guiraudjb/Arducible_Fanny_Petanque_World_Tour/videos/poster-chassis-as-du-tir.jpg

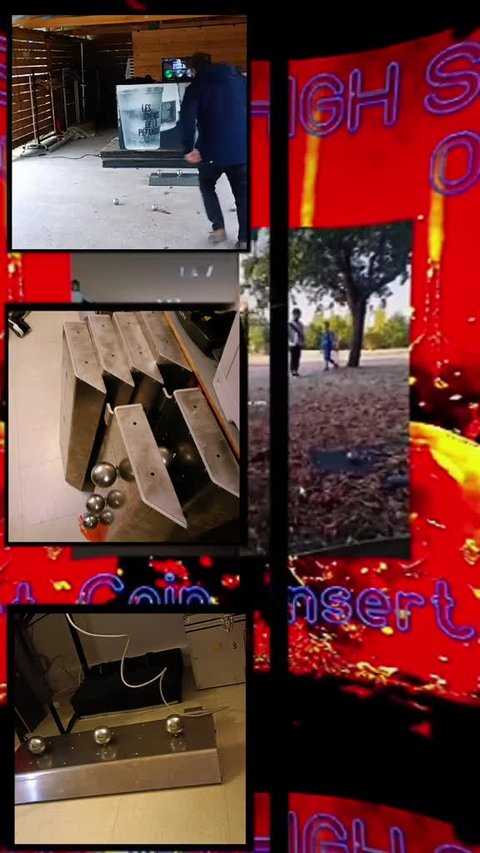
videos/poster-chassis-as-du-tir.jpg
