guiraudjb/Arducible_Fanny_Petanque_World_Tour/videos/poster-assemblage-articulation.jpg

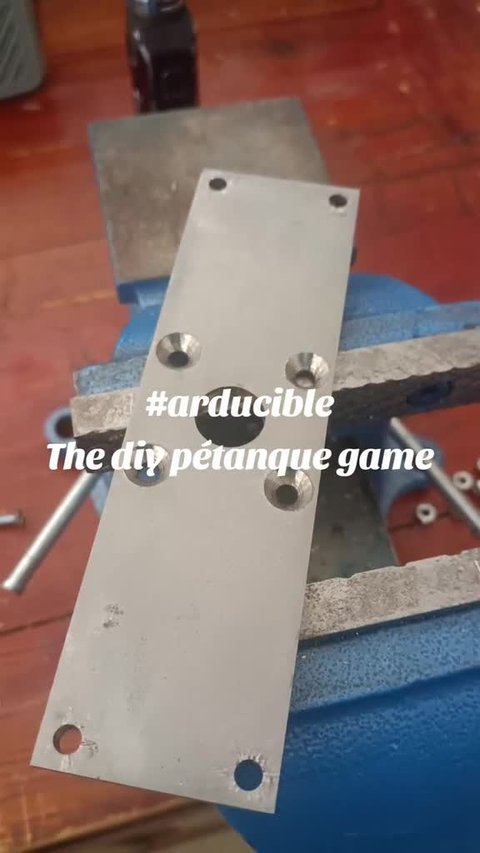
videos/poster-assemblage-articulation.jpg
