guiraudjb/Arducible_Fanny_Petanque_World_Tour/ressources/utils/RECHERCHE_ATHLETES_PETANQUE.md

# Recherche : athlètes, titres et classements de pétanque par pays

Registre des recherches web menées pour documenter, pour chacun des 112 pays du tour (`Scripts/dialogues.py`), les athlètes de pétanque notables, les titres nationaux/internationaux et le niveau compétitif du pays — en complément de `RECHERCHE_PETANQUE_PAYS.md` (dates de fondation des fédérations) et en vue d'enrichir les questions de `Scripts/quiz_questions.py`.

Principe : chaque fait doit être vérifiable et sourcé. Quand aucune information fiable n'a été trouvée après recherche web, c'est noté explicitement (`AUCUNE INFORMATION TROUVÉE`) plutôt que d'inventer un fait.

**112 pays traités par recherche web.**

## Europe

**Allemagne** (tier 0) — Pas de champion individuel historique majeur trouvé, mais nation en forte progression : a organisé le premier championnat d'Europe triplette féminin à Rastatt (2003) ; a décroché son tout premier titre de championne d'Europe triplette masculine en 2025 à Santa Susanna (Espagne), battant la France 13-7 en finale ; nombreuses médailles CEP (bronzes/argents EuroCup, ors en Espoirs triplette femmes 2009/2011/2017/2025) — sources : cep-petanque.com/medals.html ; sportmag.fr/petanque-enorme-desillusion-la-france-privee-de-la-couronne-par-lallemagne

**Andorre** (tier 1) — Federació Andorrana de Petanca (présidée par Patrick Senzier), organise championnats nationaux et ateliers jeunesse. Aucun athlète ni résultat international trouvé — sources : andorrapetanca.com ; coa.ad/federacio/federacio-andorrana-petanca

**Angleterre** (tier 2) — Petanque England ; fédération forte reconnue par la CEP ; bronze en FedCup 2023, argent Doubles Femmes 2022, bronze Doubles Hommes 2022, argent Junior Triples Filles 2022, or Précision Espoirs Femmes 2017 ; a longtemps dominé le "Home Nations Championship" jusqu'à une série de 24 ans rompue par Jersey en 2025 — sources : cep-petanque.com/medals.html ; channeleye.media/team-jersey-triumphs-in-historic-victory-at-petanque-home-nations-championships

**Autriche** (tier 4) — Fédération autrichienne (boule.at) ; bronze en triplette femmes au championnat d'Europe 2016 et bronze en tir de précision femmes 2024 ; jeune joueur Maris Newerkla (PSV Freistadt) noté 5e aux championnats d'Europe juniors — sources : cep-petanque.com/medals.html ; boule.at/ranglisten

**Belgique** (tier 5) — Claudy Weibel : 2 titres de champion du monde (triplette 2000, tête-à-tête 2015 à Nice), champion d'Europe de tir de précision 2009, 19 médailles mondiales seniors ; William Van der Biest, 2 fois champion du monde junior ; la Belgique a aussi remporté l'or en EuroCup en 2016 et 2018 — sources : fr.wikipedia.org/wiki/Charles_Weibel ; sportmag.fr/petanque-la-legende-claudy-weibel-dit-stop-avec-la-belgique ; cep-petanque.com/medals.html

**Bulgarie** (tier 6) — Fédération bulgare de pétanque (petanque-bulgaria.com) ; a organisé le championnat d'Europe hommes 2015 et 2019 à Albena. Aucun athlète bulgare médaillé trouvé — sources : petanque-bulgaria.com ; cep-petanque.com/medals.html

**Danemark** (tier 7) — Fédération existant depuis plus de 50 ans ; Lasse Dithmar a réalisé le meilleur score de tir de précision jamais atteint par un Danois (36) en grand championnat ; médailles CEP officielles : Or en FedCup 2024 ET 2025, argent EuroCup 1998, plusieurs bronzes (triplette femmes 2012/2014, junior mixte 2000/2004, tir 2006/2013) — sources : sportmag.fr/petanque-le-danemark-grandit-a-linternational ; cep-petanque.com/medals.html

**Écosse** (tier 8) — Scottish Pétanque Association fondée en 1985 ; dispute le "Celtic Challenge" contre le Pays de Galles et l'Irlande (13 victoires en 2026, derrière le Pays de Galles à 14). Aucune médaille CEP/FIPJP trouvée à ce jour — sources : scottishpetanque.org ; welshpetanque.org.uk/?page_id=77

**Espagne** (tier 9) — Sara Díaz Reyes, championne d'Europe espagnole citée comme référence ; l'Espagne a battu la Suisse 13-7 en finale de doublette et l'Italie 13-9 en doublette messieurs lors de récents championnats d'Europe ; médailles CEP très nombreuses (or triplette féminine 1971, multiples ors en tir de précision) — sources : boule-petanque.fr/vibrer-petanque/direct-live-des-championnats-deurope-de-petanque-en-espagne-cette-semaine ; cep-petanque.com/medals.html

**Estonie** (tier 10) — En demi-finale du championnat d'Europe vétérans 2023, l'Estonie s'est inclinée 33-23 face à l'Italie ; médailles CEP officielles en FedCup : argent 2023, bronze 2022 ; bronzes en tir de précision 2011 et 2013 — sources : blogpetanque.com/guerchois/RESULTATS-CHAMPIONNAT-D-EUROPE_a987 ; cep-petanque.com/medals.html

**Finlande** (tier 11) — Suomen Pétanque-Liitto ; meilleurs résultats historiques : plusieurs 5e places en Euro, ~9e en Mondial ; argent FedCup 2024, bronzes FedCup 2018/2019/2021, or en Espoirs triplette hommes 2019 ; joueurs représentant la Finlande au Mondial de Dijon (déc. 2024) : Mikko Soikkeli, Petri Seppä, Antti Lehtonen, Mikael Daniloff-Bredenholm — sources : petanquefinland.com ; cep-petanque.com/medals.html

**France** (tier 12) — Philippe Quintais, "le Roi Quintais"/"Zidane de la pétanque", 14 fois champion du monde (8x triplette, 4x tir de précision, 2x en tant que coach), 2 titres de champion d'Europe ; Dylan Rocher, actuel meilleur joueur mondial (9 fois champion du monde, 7 fois champion d'Europe) ; la France domine tous les tableaux avec 27+ titres mondiaux et plus de 80 podiums — sources : en.wikipedia.org/wiki/Philippe_Quintais ; famille-rocher.com/qui-sommesnous-dylan-rocher ; fr.wikipedia.org/wiki/Championnats_du_monde_de_pétanque

**Guernesey** (tier 13) — Guernsey Club de Pétanque ; au tournoi international "Guernsey Open" 2025, Andrew Bellamy-Burt vainqueur en simple, victoires en doublette et triplette avec des joueurs jersiais/guernesiais mêlés (tournoi ouvert, pas de médaille FIPJP/CEP) — source : guernseypetanque.co.uk/guernsey-open

**Hongrie** (tier 14) — Ágnes Kocsis-Simon, présidente de la Fédération hongroise de pétanque, joueuse et entraîneuse : 11 titres nationaux, 11e place par équipe au championnat du monde en ayant battu la future championne (Tunisie), a mené l'équipe féminine jeunes de Hongrie au bronze au championnat d'Europe U- 2019 ; argent en tir de précision juniors filles au championnat d'Europe 2022 — sources : petanque.hu/kocsissimonagnes-interju2020 ; sportmag.fr/petanque-la-hongrie-se-fait-sa-place-dans-le-gratin-europeen ; cep-petanque.com/medals.html

**Irlande** (tier 15) — Irish Pétanque Association fondée en 1990 ; a remporté le "Celtic Challenge" quatre années consécutives, bronze en Coupe Fédération Europe ; équipe Ireland A1 (Colin Delaney, Sariff Antooaroo, Stephane Voinot, Kevin Meniel) invaincue en 2023 — sources : irishpetanque.org ; educnaute-infos.com/article-la-petanque-en-irlande-119320671

**Italie** (tier 16) — Diego Rizzi, surnommé "l'Alieno" (l'extraterrestre) : 46 fois champion d'Italie, 6 fois champion d'Europe, 5 fois champion du monde, 2 fois champion de France ; l'Italie championne du monde triplette 2024 (Rizzi/Cocciolo) battant Madagascar 13-11, premier titre italien en 45 ans dans cette épreuve ; or mondial en doublette 2022, argent en tête-à-tête 2022 — sources : fr.wikipedia.org/wiki/Diego_Rizzi ; sportmag.fr/petanque-litalie-sur-le-toit-du-monde

**Jersey** (tier 17) — L'équipe de Jersey a mis fin en 2025 à une série de 24 années de victoires consécutives de l'Angleterre au "Petanque Home Nations Championship" ; 4 joueurs de Jersey ont participé au championnat d'Europe 2026 à Lorca (Espagne) ; Cassie Stewart-Le Gallais a remporté les Island Singles Championships 2025 (catégorie femmes) — sources : channeleye.media/team-jersey-triumphs-in-historic-victory-at-petanque-home-nations-championships ; jerseysportscouncil.com/jersey-petanque-players-in-confederation-of-european-petanque-championships

**Lettonie** (tier 18) — Latvijas petanka sporta federācija (fédération active, championnats nationaux doublette hommes/femmes). Aucun résultat international individuel ou d'équipe médaillé trouvé — source : petanque.lv

**Lituanie** (tier 19) — Lietuvos petankės asociacija ; champions nationaux : Irma Bagdanavičienė (simple femmes), Nerijus Kukcinavičius (simple hommes), Doringa Burneikienė & Almantas Burneika (mixte) ; a participé au championnat d'Europe 2024 à 's-Hertogenbosch (Pays-Bas) où la Lituanie a décroché le bronze en doublette femmes — sources : lietuvospetanke.lt/petankes-rezultatai ; cep-petanque.com/medals.html

**Luxembourg** (tier 20) — Fédération Luxembourgeoise de Boules et de Pétanque (65 ans d'existence) ; joueurs notables : Luc Cattazzo, Claudio Contardi, Sven Thill, Adrien Daunois ; plusieurs médailles CEP (bronzes EuroCup 2015/2019/2024, bronze doublette femmes 2024, argent junior mixte 2014) — sources : flbp.lu ; boulistenaute.com/les-actualites-de-la-petanque-et-du-monde-bouliste ; cep-petanque.com/medals.html

**Monaco** (tier 21) — Myriam Chambeiron et Laura Vierjon, championnes d'Europe de doublette féminine 2022 (à 's-Hertogenbosch, Pays-Bas), battant en finale la France, l'Allemagne, le Danemark, la Lituanie et l'Angleterre ; puissance récurrente du tir de précision avec de très nombreuses médailles CEP (or EuroCup 2011, ors en Espoirs, Vétérans, junior mixte 2018) — sources : monaco-tribune.com/2022/07/petanque-monaco-decroche-le-titre-de-champion-deurope-chez-les-feminines ; cep-petanque.com/medals.html

**Norvège** (tier 22) — Qualifiée pour la première fois au championnat du monde en 2013 ; meilleur résultat mondial junior : 9e place en 1995 ; or en FedCup 2022, bronzes FedCup 2023/2018 ; bronze en tir de précision femmes 2014 — sources : cd29petanque.fr/europe/petanque-en-norvege ; cep-petanque.com/medals.html

**Pays-Bas** (tier 23) — Kees Koogje et Edward Vinke, champions nationaux néerlandais, Vinke ayant représenté les Pays-Bas à plusieurs championnats d'Europe ; l'équipe néerlandaise a battu en poule les champions du monde en titre Dylan Rocher/Christophe Sarrio lors d'un tournoi à Rome ; nombreuses médailles CEP (or en tir de précision femmes 2007, ors en Vétérans 2016/2017, bronze en simple femmes 2022/2024) — sources : pen.nl/artikel/speler-petanque-vereniging-nieuwegein-nederland-kampioen-doubletten ; cep-petanque.com/medals.html

**Pays de Galles** (tier 24) — Welsh Pétanque Association fondée en 2004 ; pays le plus titré du "Celtic Challenge" avec 14 victoires (devant l'Écosse à 13 et l'Irlande à 8) ; champions nationaux récents : J-Y Robic, L Field, I Bailey — sources : welshpetanque.org.uk ; en.wikipedia.org/wiki/Welsh_Pétanque_Association

**Pologne** (tier 25) — Fédération polonaise de pétanque créée en 2002 ; Jędrzej Śliż, bronze en tir de précision au championnat d'Europe juniors 2003 (Brno) ; Paweł Pieprzyk, or en tir de précision juniors 2012 (Gand, Belgique) ; Katarzyna Błasiak, plusieurs médailles internationales ; or en FedCup 2021 — sources : lepetitjournal.com/varsovie/karolina-fabis-petanque-polonaise-passion-gagne-terrain-364712 ; cep-petanque.com/medals.html

**Portugal** (tier 26) — Federação Portuguesa de Petanca créée en 1992, membre FIPJP ; bronze en tir de précision hommes au championnat d'Europe 2019, argent 2011 ; bronze en Espoirs triplette hommes 2024. Aucun athlète nommé individuellement trouvé — sources : fppetanca.pt/fpp ; fipjp.org/images/pdf/nations/portugal.pdf ; cep-petanque.com/medals.html

**Roumanie** (tier 27) — Fédération roumaine de pétanque fondée en 2006 par Titus Marin ; Association Petanque Romania (APR) créée à Bucarest avec le soutien de la diaspora ; sport encore en développement, sans résultat international médaillé trouvé — sources : adevarul.ro/stil-de-viata/petanque-jocul-cu-bila-pe-gustul-lui-victor-1299315 ; romanialibera.ro/special/un-sport-nou-a-patruns-in-romania-petanque-66045

**Russie** (tier 28) — Fédération russe de pétanque (organise un championnat ouvert à Moscou) ; bronze en Vétérans au championnat d'Europe 2016 à Monaco — source : cep-petanque.com/medals.html

**Saint-Marin** (tier 29) — La Fédération sammarinaise de boules organise un tournoi international annuel de pétanque (24e édition mentionnée), avec inauguration de terrains couverts. AUCUNE INFORMATION TROUVÉE sur un athlète sammarinais médaillé au niveau international — sources : sanmarinortv.sm/sport/sport-sammarinese-c16/bocce-marro-e-musso-vincono-il-240-trofeo-internazionale-di-petanque-di-san-marino ; libertas.sm

**Serbie** (tier 30) — AUCUNE INFORMATION TROUVÉE de source fiable sur une fédération, un athlète ou un résultat international serbe en pétanque

**Slovaquie** (tier 31) — Slovak Petanque Federation ; participe au circuit "Petanque Tour Central Europe" (Trophée L. Sedivy) ; bronze en tir de précision hommes au championnat d'Europe 2015 à Albena. Aucun athlète nommé trouvé — source : cep-petanque.com/medals.html

**Slovénie** (tier 32) — La Slovénie a perdu 48-35 face à l'Italie en phase de championnat d'Europe, et 5-13 face à la France en 8e de finale du championnat du monde ; médailles CEP officielles : bronze FedCup 2025, argent FedCup 2022, bronze triplette hommes 2019, bronzes en tir de précision 2018/2023. Aucun athlète nommé trouvé — sources : blogpetanque.com/guerchois/RESULTATS-CHAMPIONNAT-D-EUROPE_a987 ; cep-petanque.com/medals.html

**Suède** (tier 33) — Ivar Liljegren, vice-champion d'Europe de tête-à-tête 2024 (à Martigny, Suisse), ayant battu Henri Lacroix en poule puis en demi-finale ; une joueuse suédoise a été sacrée championne d'Europe de tête-à-tête féminin 2026 à Lorca, battant Aurélie Bories 13-9 en finale (nom non confirmé) ; or à l'EuroCup 1998, or en triplette femmes 2007 — sources : sportmag.fr/petanque-un-redoutable-tireur-suedois-debarque-en-france ; sportmag.fr/petanque-bonetto-champion-deurope-desillusion-pour-bories-et-le-mixte ; cep-petanque.com/medals.html

**Suisse** (tier 34) — Maïky Molinas (Genève), champion du monde de tête-à-tête 2019, battant Henri Lacroix 13-12 ; Sylviane Métairon, championne du monde féminine l'année suivante ; la Suisse a remporté le championnat d'Europe junior triplette en 2022 ; considérée comme une grande nation de pétanque malgré seulement ~2 500 licenciés (contre 300 000 en France) ; or en EuroCup 1999, or en Vétérans 2025 — sources : letemps.ch/sport/petanque-maiki-molinas-las-carreau ; rts.ch/sport/autres-sports/14181090-loin-des-cliches-la-suisse-fait-partie-des-meilleures-nations-au-monde-en-petanque ; cep-petanque.com/medals.html

**Tchéquie** (tier 35) — Česká asociace pétanque klubů (~52 clubs, ~1000 licenciés en 2010) ; plus grand succès tchèque : médaille d'argent de l'équipe féminine au championnat d'Europe 2007 (Ankara/Turquie) ; argent en FedCup 2021 ; bronze en tir de précision juniors filles 2022 — source : cep-petanque.com/medals.html

**Ukraine** (tier 37) — Fédération ukrainienne de pétanque, enregistrée en 2007 puis reconfirmée en 2015 ; champions nationaux récents : Andriy Kameniev (Kharkiv) et Hanna Bezrodna (Kharkiv) ; a participé au tournoi préliminaire du championnat du monde 2024 à Dijon. Aucun résultat médaillé au niveau international (CEP/FIPJP) trouvé — sources : petanque.org.ua ; fr.wikipedia.org/wiki/Championnats_du_monde_de_pétanque_2024

Note méthodologique : les données les plus fiables proviennent de la page officielle des médailles de la Confédération Européenne de Pétanque (cep-petanque.com/medals.html), consultée directement, ce qui a permis de confirmer précisément année/catégorie/rang pour de nombreux petits pays (Danemark, Norvège, Pologne, Estonie, Lituanie, Tchéquie, Slovénie, Slovaquie, Hongrie, Autriche, Portugal, Russie, etc.). Pour Serbie, Roumanie, Andorre, Saint-Marin et Bulgarie, aucune médaille officielle ni athlète notable n'a pu être confirmé malgré plusieurs recherches ciblées.

## Asie

**Arménie** (tier 3) — AUCUNE INFORMATION TROUVÉE sur un athlète notable ou un résultat international. Un club de pétanque existe à Erevan (présenté comme "le premier club de pétanque en Arménie"), mais aucune fédération, aucun palmarès ni aucun résultat de compétition n'a pu être trouvé — source : https://www.instagram.com/petanqueclub_armenia/?hl=fr ; https://www.facebook.com/PetanqueArmenia/

**Turquie** (tier 36) — Aucun athlète notable identifié, mais le pays a un rôle d'hôte international réel : la fédération turque (Turkish Federation of Bocce, Bowling and Dart, affiliée FIPJP) a organisé les Championnats du Monde féminins en 2008, puis le 45ème Championnat du Monde de pétanque en triplette masculine à Izmir en 2015 (limité à 48 équipes qualifiées par continents), avec en parallèle le Championnat du Monde de tir de précision — source : https://petanque-en-comminges.over-blog.com/pages/45eme_Championnat_du_Monde_Triplettes_a_Izmir_Turquie-3811890.html

**Afghanistan** (tier 65) — AUCUNE INFORMATION TROUVÉE. Aucune fédération, aucun club, aucun athlète de pétanque afghan n'a pu être trouvé malgré plusieurs recherches.

**Bangladesh** (tier 66) — AUCUNE INFORMATION TROUVÉE. Aucune fédération ni club de pétanque n'a pu être identifié au Bangladesh.

**Brunei** (tier 67) — A participé au 6ème Championnat d'Asie de pétanque 2025 (Kuala Lumpur) en triplette homme/femme et tir, sans obtenir de médaille. Aucune médaille de pétanque relevée aux SEA Games 2025 (le premier "gold" historique de Brunei à ces Jeux était en wushu, pas en pétanque) — source : http://www.asianboulessport.org/News/FullOfficialResult_ASC2025.pdf ; https://www.seagames2025.org/news/details/Brunei-Secures-First-Gold-Med:-736

**Cambodge** (tier 68) — Sok Chanmean, champion du monde de tir de précision en 2016 (Madagascar), 2e place aux Championnats du Monde 2004 (France), 39 médailles cumulées sur 29 compétitions internationales depuis 2001 (12 titres). Au Championnat d'Asie 2025 (Kuala Lumpur) : OR en triplette féminine (Un Sreya, Ouk Sreymom, Heang Vichny, Pov Thyda), ARGENT en triplette masculine (Thong Chhoeun, Sychan Dara, Heng Than, Puth Yon Chandra), OR en tir juniors (Nun Ravin). Puissance montante confirmée de la pétanque en Asie du Sud-Est — source : https://www.cambodgemag.com/post/le-cambodgien-aux-39-m%C3%A9dailles-sok-chanmean-a-de-grandes-ambitions-pour-les-championnats-du-monde ; PDF résultats officiels ASC2025 (asianboulessport.org)

**Chine** (tier 69) — Au Championnat d'Asie 2025, la Chine (équipe Zhou Bao, Chuan Huai, Dao Shan, Cheng Ze) a remporté le BRONZE en triplette masculine (Nation Cup). Par ailleurs Wang Chenyi (Chine) a atteint la demi-finale de la discipline "Lyonnaise féminine" (boules lyonnaises, discipline distincte de la pétanque) aux World Games 2025 à Chengdu — à noter que ce dernier résultat concerne une discipline sœur et non la pétanque elle-même — source : PDF résultats officiels ASC2025 ; https://cnosf.franceolympique.com/jeux-mondiaux-2025-j11-du-bronze-pour-finir

**Corée du Sud** (tier 70) — Présence confirmée mais modeste (club "Hongchungang", moins de 25 joueurs). A participé au Championnat d'Asie 2025 sans obtenir de médaille (classée en fin de tableau en triplette hommes/femmes et junior) — source : PDF résultats officiels ASC2025 (asianboulessport.org)

**Inde** (tier 71) — La Petanque India Association (PIA) est l'organe national reconnu ; la pétanque serait arrivée en Inde en 2005. L'Inde a participé au Championnat d'Asie 2025 à Kuala Lumpur mais classée dernière (16e) en triplette masculine, sans médaille — source : https://www.instagram.com/indiapetanque/ ; PDF résultats officiels ASC2025

**Indonésie** (tier 72) — Anni Saputri, championne d'Asie 2025 en tir de précision féminin (Kuala Lumpur). Andri Irawan, médaille d'or en simple messieurs aux SEA Games 2025 (Thaïlande), battant le Laotien Southammavong Bountamy 13-7 en finale. Bronze en triplette masculine à l'Asian Cup 2025 (M Muhlis Harliza, Bagas Syarief Hidayat, Dhoni Wahyu Krisbiantoro, Topan Satria) — source : PDF résultats officiels ASC2025 ; https://en.wikipedia.org/wiki/P%C3%A9tanque_at_the_2025_SEA_Games

**Iran** (tier 73) — La Boules and Petanque Association of Iran (BPAI) est reconnue depuis 2009 comme organe national unique pour la pétanque, organisant des championnats nationaux (ex. 13e édition en février 2023 à Sari) pour sélectionner les équipes envoyées aux championnats d'Asie et du monde. Aucun résultat de médaille ni athlète notable identifié précisément — source : https://fipjp.org/index.php/en/?view=article&id=526:iranian-national-petanque-championships-2023&catid=45

**Japon** (tier 74) — Ayumi Goma, joueuse japonaise classée 1ère de la sélection nationale trois fois consécutives, ayant représenté le Japon au Championnat d'Asie 2023 à Kuala Lumpur (5e ex æquo en triplette femmes) et aux Asian Beach Games 2016 (simple femmes). Au Championnat d'Asie 2025 : BRONZE en tir juniors (Koiwa Toshihiro), BRONZE en triplette féminine et junior (Nation Cup), avec les joueuses Goma Ayumi, Sakakibara Chikage, Ishikawa Norie, Katata Keiko — source : PDF résultats officiels ASC2025 ; recherche web sur Ayumi Goma

**Kazakhstan** (tier 75) — AUCUNE INFORMATION TROUVÉE. Aucune fédération ni club de pétanque identifiable.

**Kirghizistan** (tier 76) — Une "Kyrgyz Petanque Federation" est référencée sur la base de données petanque-world.com, mais celle-ci indique explicitement l'absence de clubs, de joueurs et de compétitions actifs dans le pays. AUCUNE INFORMATION TROUVÉE sur un athlète ou un résultat — source : https://www.petanque-world.com/country/federation/kyrgyzstan-kg/

**Laos** (tier 77) — Thepphakan Bovilak (Bovilak Thepphakan), première médaille d'or de l'histoire du Laos aux SEA Games, remportée en simple femmes le 10 décembre 2025 à Bangkok (33e SEA Games). Southammavong Bountamy (Bountamy Southamavong), médaille d'argent en simple hommes aux mêmes Jeux, battu 13-7 en finale par l'Indonésien Andri Irawan. Confirme le Laos comme puissance montante de la pétanque en Asie du Sud-Est — source : https://kpl.gov.la/EN/detail.aspx?id=96008 ; https://en.wikipedia.org/wiki/P%C3%A9tanque_at_the_2025_SEA_Games

**Malaisie** (tier 78) — Pays hôte du 6e Championnat d'Asie 2025 (Kuala Lumpur), très performant : BRONZE tir hommes (Muhamad Nuzul Azwan Ahmad Temizi), ARGENT tir femmes (Nur Iman Aina binti Ahmad Sabti), ARGENT tir juniors (Muhammad Harith Muhaimin bin Hafaizul), BRONZE triplette masculine (Asian Cup), BRONZE triplette féminine (Asian Cup, équipe A), ARGENT triplette junior (Asian Cup) et OR triplette junior (Nation Cup, équipe B) — source : PDF résultats officiels ASC2025 (asianboulessport.org)

**Mongolie** (tier 79) — AUCUNE INFORMATION TROUVÉE. Aucune fédération, club ou athlète de pétanque mongol identifié.

**Myanmar** (tier 80) — Médaille d'argent en tir de précision féminin aux SEA Games 2025 (derrière la Thaïlande), dans le cadre d'un total de 11 médailles remportées par le Myanmar à ces Jeux (toutes disciplines confondues). Nom de l'athlète non trouvé précisément — source : recherche web SEA Games 2025 Myanmar petanque (gnlm.com.mm, moi.gov.mm)

**Népal** (tier 81) — AUCUNE INFORMATION TROUVÉE. Aucune fédération ni club de pétanque népalais identifié.

**Pakistan** (tier 82) — AUCUNE INFORMATION TROUVÉE. Aucune fédération ni club de pétanque pakistanais identifié.

**Philippines** (tier 83) — Aux SEA Games 2025 (Thaïlande) : double BRONZE — Cesiel Domenios & Ma. Corazon Soberre (double dames) et Jhasfer Camingal & Harry Micutuan (double hommes). Aux SEA Games 2023 (Cambodge) : BRONZE en double dames (April Alarcon & Maria Corazon Soberre), seule médaille philippine cette année-là — source : https://www.facebook.com/gmasportsph/posts/2025-sea-games-double-bronze-in-petanque-doubles-jhasfer-camingal-and-harry-micu/1474175984716670/ ; https://www.malaymail.com/news/sports/2023/05/11/sea-games-national-petanque-squad-adds-a-silver-and-bronze-to-medal-tally/68775

**Singapour** (tier 84) — BRONZE Nation Cup en triplette féminine au Championnat d'Asie 2025 (Tan Lay Tin, Tay Gek Heok, Leong Seng Lee). Programme national modeste mais structuré (Sports Boules Singapore), participation historique dès les SEA Games 2005 aux Philippines — source : PDF résultats officiels ASC2025 ; https://www.sportsboules.org.sg/team-sports

**Taïwan** (tier 85) — Wu, Kun-Yu, médaille d'ARGENT en tir de précision hommes au Championnat d'Asie 2025. ARGENT en triplette féminine (Nation Cup, équipe Chen Ping-Ru, Wang Yi-Hsuan, Zheng Yong-Xin, Yang Yen-Lin). BRONZE en triplette junior (Asian Cup, équipe Tsai Chih-Hsuan, Li Yi-Huei, Chen Min-Che, Chen Rou-Xuan) — source : PDF résultats officiels ASC2025 (asianboulessport.org)

**Thaïlande** (tier 86) — Nation dominante mondiale : Championne du Monde 2023 (Bénin) avec 3 titres — triplette masculine (1ère fois de son histoire : Ratchata Khamdee, Sarawut Sriboonpeng, Supan Thongphoo, Thanawan Toosewha), simple messieurs (Ratchata Khamdee), double dames (Sunitra Phuangyoo & Nantawan Fuangsanit) ; la Thaïlande a fini 1ère nation devant la France en 2023. Au Championnat d'Asie 2025 (Kuala Lumpur) : OR tir hommes (Khamdee Ratchata), OR triplette masculine Asian Cup, OR triplette junior, OR triplette féminine (Nation Cup). Aux SEA Games 2025 : nation la plus titrée en pétanque avec 5 médailles d'or — source : https://www.france24.com/fr/info-en-continu/20231121-princesse-arm%C3%A9e-comment-la-tha%C3%AFlande-est-devenue-championne-du-monde-de-p%C3%A9tanque ; https://ma-thailande.fr/la-thailande-championne-du-monde-de-petanque ; PDF résultats officiels ASC2025

**Turkménistan** (tier 87) — AUCUNE INFORMATION TROUVÉE. Aucune fédération, club ou athlète de pétanque turkmène identifié.

**Vietnam** (tier 88) — Premier titre mondial de l'histoire de la pétanque vietnamienne : championne du monde de triplette féminine 2023 à Bangkok (13-12 face à la Thaïlande), équipe composée de Trinh Thi Kim Thanh, Tran Thi Diem Trang, Thach Thi Anh Lan et Kim Thi Thu Thao. Titre défendu en 2025 à Sin-le-Noble (France), victoire 13-1 en finale face à la Thaïlande. Aux SEA Games 2025 : 3 médailles d'or — double hommes (Ngô Ron & Lý Ngọc Tài), double dames (Nguyễn Thị Thùy Kiều & Nguyễn Thị Thi), tir hommes (Nguyễn Văn Dũng). Au Championnat d'Asie 2025 : ARGENT triplette masculine Nation Cup, ARGENT triplette féminine Asian Cup — source : https://en.sggp.org.vn/vietnamese-petanque-team-secures-first-world-championship-title-post106604.html ; https://en.vietnamplus.vn/vietnamese-petanque-team-successfully-defends-world-championship-post330330.vnp ; https://en.wikipedia.org/wiki/P%C3%A9tanque_at_the_2025_SEA_Games ; PDF résultats officiels ASC2025

Note méthodologique : les résultats du Championnat d'Asie 2025 (Kuala Lumpur, 5-10 novembre 2025) proviennent du document officiel téléchargé depuis asianboulessport.org (FullOfficialResult_ASC2025.pdf), qui donne le détail nominatif des médaillés par pays et catégorie (tir de précision, triplette hommes/femmes/juniors, Asian Cup et Nation Cup). Pour 9 pays (Arménie, Afghanistan, Bangladesh, Kazakhstan, Kirghizistan, Mongolie, Népal, Pakistan, Turkménistan), aucune source fiable n'a pu établir d'athlète ou de résultat international précis malgré plusieurs recherches ciblées — ces cas sont marqués AUCUNE INFORMATION TROUVÉE conformément à la consigne de ne jamais inventer de contenu factuel.

## Afrique

**Algérie** (tier 38) — Seul titre mondial de son histoire : championne du monde de pétanque en triplette en 1964 à Genève (Suisse), première nation non-française à remporter ce titre après trois éditions de domination française. Plus récemment : Farid Hamoudi, bronze au tir de précision aux championnats d'Afrique 2009 et 2013 ; Hmida Zerrouk, argent au tir de précision 2019 ; bronze en triplette hommes aux championnats d'Afrique 2021. Équipe 2024 (Dijon) : Hammoudi Farid, Zebaier Boualem, Bachene Rabah, Boutarfa Samir (coach Kerdjou Abdelmalek) — sources : sportmag.fr, fr.wikipedia.org/wiki/Championnats_d'Afrique_de_pétanque, petanque-dijon2024.fr

**Bénin** (tier 39) — Championne du monde en doublette mixte en 2023 (50e Mondial, Cotonou), première médaille d'or mondiale du pays. Marcel (Terrazini) Bio, considéré comme l'un des meilleurs tireurs au monde et capitaine de l'équipe nationale : champion d'Afrique de tir de précision en 2019 et 3e en triplette au championnat d'Afrique 2019. Médailles en triplette hommes aux championnats d'Afrique : argent 2007, bronze 2013, bronze 2015, bronze 2019 — sources : france24.com, fr.wikipedia.org/wiki/Championnats_d'Afrique_de_pétanque, benin-sports.com

**Burkina Faso** (tier 40) — Premier vainqueur historique du championnat d'Afrique de pétanque en triplette hommes (2007, à Cotonou), équipe : Raphaël Kiéma, Marius Ouoba, Salif Ouédraogo, Touré Mamadou Ouédraogo. Bronze au tir de précision au Mondial 2008 (Dakar). Argent en triplette hommes au championnat d'Afrique 2021. Bronze par équipe (« Étalons Boulistes ») au Mondial 2023 (Bénin), Coupe CEDEAO en or 2023. Équipe féminine : or à la Coupe des nations femmes 2024, Florence Kanzié bronze au tir de précision femmes 2024 — sources : fr.wikipedia.org/wiki/Championnats_d'Afrique_de_pétanque, burkina-faso.news-pravda.com, infosculturedufaso.net

**Cameroun** (tier 41) — Médailles aux championnats d'Afrique de pétanque : bronze en triplette hommes 2011, argent en triplette hommes 2015, argent au tir de précision 2024 (Charles Mbenoun) — source : fr.wikipedia.org/wiki/Championnats_d'Afrique_de_pétanque

**Comores** (tier 42) — Résultat historique : première finale de l'histoire du pays au championnat d'Afrique (tête-à-tête 2025, Nouakchott), argent pour Zaidou Maoulida Mhamadi (les Comores avaient éliminé Madagascar 13-11). 5e place mondiale en triplette au Mondial de Cotonou 2023 (Bénin), 2e nation africaine derrière le Burkina Faso — sources : fr.wikipedia.org/wiki/Championnats_d'Afrique_de_pétanque, alwatwan.net, comoresinfos.net

**Congo** (tier 43) — Or au tir de précision au championnat d'Afrique 2015 (Galy Chabrol Binguila). Or à la Coupe des nations hommes au championnat d'Afrique 2024 (Marrakech). Argent en triplette hommes au championnat d'Afrique 2025 (Nouakchott), équipe : Binguila Charbrol, Batambika Verdorold, Babassana Christ, Ndembi Bertrand, battue en finale par la Tunisie 13-8 — sources : fr.wikipedia.org/wiki/Championnats_d'Afrique_de_pétanque, adiac-congo.com

**Côte d'Ivoire** (tier 44) — Championne du monde de la Coupe des Nations au Mondial 2023 (Cotonou, Bénin), en battant le Bénin 13-3 en finale, avec la triplette Saman, Maiga, Gnahoré. Or en tête-à-tête au championnat d'Afrique 2025 (Salif Kourouma). Trois médailles au championnat d'Afrique 2026 (Abidjan) : or en individuel, argent en doublette et argent en triplette — sources : news.abidjan.net, linfodrome.com, fr.wikipedia.org/wiki/Championnats_d'Afrique_de_pétanque, ami-sportif.com

**Djibouti** (tier 45) — Said Kadir, médaille d'argent au tir de précision au championnat d'Afrique de pétanque 2009 — source : fr.wikipedia.org/wiki/Championnats_d'Afrique_de_pétanque

**Égypte** (tier 46) — AUCUNE INFORMATION TROUVÉE (l'Égypte n'apparaît pas sur la liste des fédérations africaines affiliées à la FIPJP, et aucun résultat sportif fiable n'a été trouvé) — source vérifiée : fipjp.org/index.php/fr/federations/confederation-afrique

**Gabon** (tier 47) — Fédération affiliée à la FIPJP/CASB, mais AUCUNE INFORMATION TROUVÉE sur un athlète notable ou un résultat international précis malgré recherche — source : fipjp.org/index.php/fr/federations/confederation-afrique

**Guinée** (tier 48) — Aucun résultat international trouvé. Au niveau national : la triplette Baba Conté, Djiba Camara et Alseny Sylla Bongo a remporté l'or au championnat national de boules et pétanque 2024 (Conakry, stade Russal, Tombo) — source : guineenews.org / mjs.gov.gn

**Libye** (tier 49) — Fédération libyenne de pétanque existante (élections de comité en 2017), membre fondateur de la Confédération Africaine de Sport Pétanque en 2019. AUCUNE INFORMATION TROUVÉE sur un athlète notable ou un résultat international précis — sources : fiboules.org, fipjp.org/index.php/fr/federations/confederation-afrique

**Madagascar** (tier 50) — L'une des plus grandes puissances mondiales de la pétanque hors France. Titres mondiaux en triplette hommes : 1999 (Christian Andriantseheno, Kalias Oukabay, Jean-Jacky Randrianandrasana) et 2016 (2e titre triplette). Championnats d'Afrique triplette hommes : or 2009, 2011, 2017. Doublette mixte : championne du monde 2025 à Rome (Lova et Fana, 13-10 face à la France). Tir de précision : Jean-François « Zigle » Rakotondrainibe champion du monde de tir de précision (2024) ; Sylvain Rakotoarivelo également champion du monde du tir ; or au tir de précision au championnat d'Afrique 2017 (Zoël Tony Elhenj). Faneva Ramanandraitsiory, champion du monde junior de tir de précision. Championnat du monde jeunes 2025 : or en doublette mixte (Tafitasoa Mitia et Andriatsivolo Jean Nathanaël) et titre déjà remporté en 2017 à Kaihua (Chine) — sources : la1ere.franceinfo.fr, moov.mg, lexpress.mg, depeche-taratra.mg, linfo.re, fr.wikipedia.org/wiki/Christian_Andriantseheno, madagascar-tourisme.com, fr.wikipedia.org/wiki/Championnats_d'Afrique_de_pétanque

**Mali** (tier 51) — Sangaré Nouhoum, bronze au tir de précision au championnat d'Afrique 2009. Le Mali a participé au Mondial (élimination 13-3 face à l'Italie en 16e de finale) — sources : fr.wikipedia.org/wiki/Championnats_d'Afrique_de_pétanque, sportmag.fr

**Maurice** (tier 52) — Parvez Khodabaccus, tireur mauricien, demi-finaliste au tir de précision au Championnat du monde 2024 à Dijon, après avoir éliminé l'Italien Diego Rizzi (favori du titre) et terminé 2e des qualifications avec 49 points. L'Île Maurice a également remporté le bronze au tir de précision au championnat d'Afrique 2019 — sources : sportmag.fr, fr.wikipedia.org/wiki/Championnats_d'Afrique_de_pétanque

**Mauritanie** (tier 53) — Pays hôte du 10e championnat d'Afrique de pétanque (novembre 2025, Nouakchott). L'équipe nationale a obtenu la 5e place mondiale par équipe de trois (triplette) lors du Mondial 2023 (Bénin), qualification directe pour le Mondial suivant. Sélection 2025 (coach Tarek Akili) : Mohamed Lemine Bakha, Bah Def, Mohamed Barikalla, Amadou Traoré, Valy Abdallahi, Yaya Ndiaye, Aliou Guisset, Mohamed Ould Taher — sources : cridem.org, fjbrim.com, fipjp.org, wiwsport.com

**Maroc** (tier 54) — Trois titres de champion du monde en triplette hommes : 1984 (Rotterdam, Pays-Bas), 1987 (Boumerdès, Algérie) et 1990 (Monaco). Vice-champion du monde en triplette hommes en 2018 à Desbiens (Québec), battu 13-7 par la France en finale, avec Mohamed Ajouad, Abdessamad El Mankari et Hodayfa Bouchgour. Abdessamad El Mankari, champion du monde de tir de précision individuel en 2008 à Dakar, et quadruple champion d'Afrique de tir de précision (2009, 2011, 2013). Or en triplette hommes aux championnats d'Afrique 2013 et 2021. Argent en triplette femmes 2019 et 2024, argent au tir de précision femmes 2024 (Soukaina Gourar) — sources : hespress.com, sport.le360.ma, bladi.net, aujourdhui.ma, fr.wikipedia.org/wiki/Championnats_d'Afrique_de_pétanque

**Niger** (tier 55) — Mohamed Harouna, champion d'Afrique de tir de précision en 2021. Argent à la Coupe des nations hommes au championnat d'Afrique 2024. Le Niger s'est retiré du Mondial 2023 (Cotonou) — sources : fr.wikipedia.org/wiki/Championnats_d'Afrique_de_pétanque, levenementniger.com

**Ouganda** (tier 56) — Fédération affiliée à la FIPJP/CASB, mais AUCUNE INFORMATION TROUVÉE sur un athlète notable ou un résultat international précis malgré recherche — source : fipjp.org/index.php/fr/federations/confederation-afrique

**République Centrafricaine** (tier 57) — AUCUNE INFORMATION TROUVÉE (n'apparaît pas sur la liste des fédérations africaines affiliées à la FIPJP, aucun résultat sportif fiable trouvé) — source vérifiée : fipjp.org/index.php/fr/federations/confederation-afrique

**République Démocratique du Congo** (tier 58) — AUCUNE INFORMATION TROUVÉE (n'apparaît pas sur la liste des fédérations africaines affiliées à la FIPJP, à ne pas confondre avec la République du Congo/Congo-Brazzaville, active en pétanque) — source vérifiée : fipjp.org/index.php/fr/federations/confederation-afrique

**Sénégal** (tier 59) — Or en triplette hommes au championnat d'Afrique 2024 (Marrakech). François Fara Ndiaye, vice-champion du monde de tir de précision individuel en 2008 à Dakar (finale perdue face au Marocain Abdessamad El Mankari), argent au tir de précision au championnat d'Afrique 2011. Bronze en triplette hommes au championnat d'Afrique 2009 — sources : aujourdhui.ma, fr.wikipedia.org/wiki/Championnats_d'Afrique_de_pétanque

**Seychelles** (tier 60) — AUCUNE INFORMATION TROUVÉE malgré recherche sérieuse

**Tchad** (tier 61) — Hounaye Raymon, argent au tir de précision au championnat d'Afrique 2013. Le Tchad avait signé des accords pour organiser le championnat d'Afrique 2015 et avait candidaté pour l'organisation du Mondial 2016, finalement attribué à Madagascar — sources : fr.wikipedia.org/wiki/Championnats_d'Afrique_de_pétanque, tchadinfos.com

**Togo** (tier 62) — Bronze au tir de précision par équipe au Mondial 2023 (Cotonou, Bénin). Argent en triplette hommes au championnat d'Afrique 2019. Argent à la Coupe des nations femmes au championnat d'Afrique 2024 — sources : lenouveaureporter.com, fr.wikipedia.org/wiki/Championnats_d'Afrique_de_pétanque

**Tunisie** (tier 63) — Trois titres de champion du monde en triplette hommes : 1983 (Mohamed Ferjani, Hédi Jabeur, Matallah Ben Hamida), 1986 (Jendoubi Allala, Raouf Lakili, Tarik Lakili, 15-9 contre le Maroc en finale) et 1997 (Montpellier ; Abderraouf Lakili, Tarak Lakili, Khaled Lakhal). Mouna Béji : championne du monde en triplette femmes 2011, championne du monde en individuel femmes 2023, championne du monde en doublette femmes 2025 (à Fréjus, avec Asma Belli, contre la France). Or en triplette hommes aux championnats d'Afrique 2015 et 2019 ; or en triplette femmes 2019 et 2024 ; or au tir de précision hommes 2024 (Khaled Boughriba) — sources : mosaiquefm.net, leconomistemaghrebin.com, fr.wikipedia.org/wiki/Fédération_tunisienne_de_boules_et_pétanque, fr.wikipedia.org/wiki/Championnats_d'Afrique_de_pétanque

**Zambie** (tier 64) — Fédération affiliée à la FIPJP/CASB, mais AUCUNE INFORMATION TROUVÉE sur un athlète notable ou un résultat international précis malgré recherche — source : fipjp.org/index.php/fr/federations/confederation-afrique

Note : la page Wikipédia « Championnats d'Afrique de pétanque » (fr.wikipedia.org/wiki/Championnats_d'Afrique_de_pétanque) est la source la plus riche et fiable trouvée, avec un tableau complet des médailles par édition (2007-2025).

## Amérique

**Argentine** (tier 89) — Médaille de bronze de l'équipe nationale au Championnat Panaméricain à Iquique (Chili), qualification pour le Championnat du Monde de Khon Kaen (Thaïlande, novembre 2026, triplette masculine). Entraîneur José Giménez ; joueurs cités : Mario Sejas, Adrián Castillo, Juan Esponda — source : lagaceta.com.ar/nota/1135392/deportes/petanca-argentina-crece-apunta-al-mundial-como-se-prepara-seleccion.html

**Bolivie** (tier 90) — Fédération affiliée à la Confédération Panaméricaine de Pétanque (président cité : Yerko Castro) ; équipe présente au Championnat Panaméricain qualificatif d'Iquique (Chili) 2025. Aucun nom de joueur individuel ni médaille trouvé de façon fiable — sources : panampetanque.org/about-us

**Canada** (tier 91) — Selon le tableau des médailles de la FIPJP (bilan après Montauban 2013) : 3 médailles d'argent et 4 de bronze au Championnat du Monde, aucune médaille d'or — classé parmi les nations de "second rang" derrière les 10 grandes puissances mondiales. Pétanque organisée au Québec depuis 1956, qui a accueilli 4 fois le Championnat du Monde — sources : fipjp.org/index.php/fr/?view=article&id=70:tableau-des-medailles&catid=8 ; ici.radio-canada.ca/sports/2009947/petanque-championnats-monde-benin-canada

**Chili** (tier 92) — Aux Jeux Bolivariens d'Ayacucho 2024 (Pérou) : argent de l'équipe mixte de pétanque (battue en finale par le Venezuela) et argent en paire mixte pour Melisa Polito et Renato Donoso — sources : leanotas.com/chile-campeon-de-las-bochas-de-los-juegos-bolivarianos-del-bicentenario-ayacucho-2024/ ; eldeportero.cl/sabrina-y-melisa-polito-ganaron-medallas-de-bronce-en-el-mundial-de-bochas/

**Colombie** (tier 93) — Fédération colombienne affiliée à la Confédération Panaméricaine de Pétanque (président cité : Gustavo Henao). AUCUNE INFORMATION TROUVÉE sur un athlète ou un résultat international précis.

**Costa Rica** (tier 94) — Mentionné seulement dans une liste de pays membres de la Confédération Panaméricaine de Pétanque, sans aucune autre trace vérifiable. AUCUNE INFORMATION TROUVÉE fiable au-delà de cette mention.

**Cuba** (tier 95) — AUCUNE INFORMATION TROUVÉE. Aucune fédération, aucun joueur, aucun résultat de pétanque identifiable.

**Équateur** (tier 96) — AUCUNE INFORMATION TROUVÉE. Aucune fédération ni résultat de pétanque identifiable ; l'Équateur ne figure pas parmi les médaillés de pétanque aux Jeux Bolivariens d'Ayacucho 2024.

**États-Unis** (tier 97) — Rebekah "Bekah" Howe (Crow Creek Sioux) : argent en tir de précision individuel dames aux World Games de Birmingham, 12 juillet 2022 (première médaille internationale de l'histoire de la pétanque US), battue en finale par la Cambodgienne Ouk Sreymom. Stefan Nicolas : or (première médaille d'or internationale de l'histoire de la pétanque US) en 2022 ; lui et son père Jerome Nicolas (représentant des USA aux Mondiaux de France 2013) ont représenté ensemble les USA au Championnat du Monde au Bénin en septembre 2023. Équipe masculine triplette USA championne du Championnat Panaméricain qualificatif à Iquique (Chili), décembre 2024, qualifiée pour la Coupe du Monde de Kuala Lumpur (septembre 2025) — sources : ictnews.org/news/indigenous-woman-wins-silver-medal-at-world-games/ ; usapetanque.org/in-the-spotlight/usa-takes-silver-in-petanque-at-the-world-games ; gotowncrier.com/2023/07/father-son-duo-to-play-for-u-s-at-world-petanque-championships/

**Guatemala** (tier 98) — Mentionné seulement dans une liste de pays membres de la Confédération Panaméricaine de Pétanque. AUCUNE INFORMATION TROUVÉE fiable sur un athlète ou un résultat.

**Haïti** (tier 99) — Fédération Haïtienne de Pétanque/du Sport de Boules (FHSB) créée à Port-au-Prince, rejoint la FIPJP en mars 2009 sous l'impulsion de Jean-Édouard Nelson ; affiliée à la Confédération Panaméricaine (représentante citée : Nancy Aly, président Dieufils Pierre). AUCUN résultat ni athlète individuel de compétition trouvé — sources : petanqueamericaopen.blogspot.com/2009/03/haiti-joins-fipjp.html ; panampetanque.org/about-us

**Mexique** (tier 100) — Federación Mexicana de Petanca fondée en 2011 ; première participation au Championnat du Monde triplette masculine à Marseille en 2012, puis Canada 2018, Espagne 2021, Bénin 2023, Dijon 2024, Rome/France 2025 ; équipe féminine triplette au Championnat du Monde féminin ; première participation d'une équipe jeunes en 2025 ; présente au Championnat Panaméricain qualificatif pour le Mondial triplette 2026. Aucun nom de joueur individuel ni médaille trouvé — sources : fedmexpetanca.org/home/historia ; panampetanque.org/mexico.html

**Paraguay** (tier 101) — Fédération affiliée à la Confédération Panaméricaine (président cité : Alcides Acosta) ; équipe présente au Championnat Panaméricain de Limache (Chili) 2023 (8 pays) et au Championnat Panaméricain qualificatif d'Iquique 2025 (triplette masculine). Aucun nom de joueur ni médaille trouvé.

**Pérou** (tier 102) — Aux Jeux Bolivariens d'Ayacucho 2024 : Rosalba Rojas, or en pétanque individuelle dames ; Erik Bardelli, finaliste (battu par le Vénézuélien José Manuel Marcano 13-2) en pétanque individuelle messieurs ; Bardelli/Rojas, bronze en paire mixte ; équipe péruvienne, bronze par équipe mixte — sources : rpp.pe/multideportes/mas-deportes/peru-en-juegos-bolivarianos-del-bicentenario-que-deportistas-ganaron-medallas-en-ayacucho-2024-noticia-1603310

**République Dominicaine** (tier 103) — Coordinateur cité au sein de la Confédération Panaméricaine de Pétanque : Juan Moreno. Équipe présente au Championnat Panaméricain de Limache (Chili) 2023 (8 pays participants). Aucun nom de joueur ni médaille trouvé.

**Uruguay** (tier 104) — Fédération affiliée à la Confédération Panaméricaine (président cité : Fredy Isaias). Participation évoquée mais non confirmée au Championnat Panaméricain d'Iquique 2025. Aucun nom de joueur ni médaille trouvé.

**Venezuela** (tier 105) — Aux Jeux Bolivariens d'Ayacucho 2024 : or de l'équipe mixte de pétanque (victoires 13-6 et 12-4 contre le Chili, 13-2 contre le Pérou) ; José Manuel Marcano, or en pétanque individuelle messieurs (victoires contre Erik Bardelli et Renato Donoso) ; María de Jesús Pérez, argent en pétanque individuelle dames — sources : mindeporte.gob.ve/venezuela-se-bano-de-oro-en-la-modalidad-petanca-de-la-bochas/

Note méthodologique : pour la Colombie, le Costa Rica, Cuba, l'Équateur et le Guatemala, aucune recherche web (français/anglais/espagnol) n'a permis de trouver un athlète nommé ou un résultat international vérifiable — marqué AUCUNE INFORMATION TROUVÉE. Pour la Bolivie, le Paraguay, la République Dominicaine et l'Uruguay, seule l'existence de la fédération et la participation aux championnats panaméricains ont pu être confirmées, sans athlète ni médaille nommément identifiés.

## Océanie

**Australie** (tier 106) — Pas de champion du monde ni de champion d'Océanie individuel identifié avec certitude. Résultats internationaux documentés : à l'Oceania Championship 2022 (Tahiti) l'Australie n'a remporté aucune médaille ; à l'Oceania Championship 2023 (Nouvelle-Calédonie, Boulari) elle a remporté 4 médailles ; à l'Oceania Championship 2025 (Wallis-et-Futuna) elle a obtenu 2 médailles de bronze et s'est qualifiée pour le Championnat du monde de pétanque triplette hommes 2026 (Malaisie). Joueuse notable : Delys Brady, médaille de bronze en pointage femmes à l'Oceania Championship 2025 — sources : petanqueaustralia.org.au/the-pfa/championships ; la1ere.franceinfo.fr/wallisfutuna/resultats-des-oceania-2025-la-petanque-a-brille-pendant-quatre-jours-a-wallis-1634945.html

**Nouvelle-Calédonie** (tier 107) — Toma Wai, joueur des « Cagous », sacré champion aux Océanias 2023 en triplette (avec Florian Mahossem et Aloi Pauvale) ; il a disputé trois éditions des Océanias et en est reparti à chaque fois avec l'or en triplette (en 2025 il jouait toutefois sous les couleurs de l'équipe polynésienne « Tuhaa Pae »). Sophie Takosi (club Boules du Mont-Dore) a remporté l'or en triplette (avec Adèle Ngadae et Sicera Owane) en battant de fortes équipes tahitiennes, et l'argent en pointage lors de sa première participation aux Océanias. À l'Oceania Championship 2025 (Wallis), les hommes calédoniens ont remporté l'or au tir de précision — sources : la1ere.franceinfo.fr/nouvellecaledonie/province-sud/mont-dore/petanque-les-oceanias-dans-le-viseur-des-boulistes-caledoniens-1608414.html ; la1ere.franceinfo.fr/nouvellecaledonie/province-sud/mont-dore/oceania-de-petanque-2023-23-cagous-reunis-pour-cette-edition-1434668.html

**Nouvelle-Zélande** (tier 108) — Pas de titre mondial identifié pour un joueur néo-zélandais. Participe au Championnat du monde Open depuis 1995 et au Championnat du monde féminin depuis 2006, avec des joueurs récurrents comme Christian Fouquet (7 sélections mondiales, 1995-2012) et Georgio Vakauta (sélections 2001-2003, 2012). Meilleur résultat continental : Oceania Championship 2005 (Rotorua) remporté avec six médailles d'or. Plus récemment : Claire Wilson, or en pointage femmes à l'Oceania Championship 2017 ; Naomi Paulo, or en pointage femmes à l'Oceania Championship 2023 ; Tom Paulo, argent en pointage hommes à l'Oceania Championship 2023 — sources : petanque.org.nz/archive/results/world-championship.htm ; petanque.nz/representation/oceania.html

**Tahiti** (tier 109) — Jean Manéa, finaliste (médaille d'argent) du Championnat du monde de tir de précision 2010 à Izmir (Turquie), battu en finale 34-12 par le Français Bruno Le Boursicaud — seule performance individuelle mondiale clairement documentée pour un joueur polynésien. Au tableau des médailles FIPJP (état 2013), la Polynésie française totalise 1 argent et 2 bronzes aux championnats du monde. Au niveau continental, nation dominante : à l'Oceania Championship 2025 (Wallis-et-Futuna), la délégation polynésienne a réalisé tous les podiums et terminé 1ère du classement général. Tahiti a accueilli les Océanias en 2000, 2008 et 2022 (Papara) — sources : Wikipédia « Championnats du monde de pétanque » / FIPJP palmarès tir de précision ; la1ere.franceinfo.fr/wallisfutuna/resultats-des-oceania-2025-la-petanque-a-brille-pendant-quatre-jours-a-wallis-1634945.html ; fipjp.org/index.php/fr/?view=article&id=70:tableau-des-medailles&catid=8

**Vanuatu** (tier 110) — AUCUNE INFORMATION TROUVÉE concernant un(e) athlète nommé(e) ou un titre précis. Faits vérifiés sans nom de joueur : le Vanuatu dispose d'une Fédération de Pétanque (présidée par Jerry Moli, Port-Vila), membre de la confédération océanienne de pétanque ; il a accueilli l'Oceania Championship 2016 à Port-Vila ; des sources non confirmées indiquent une participation au Championnat du monde en 2014 autour de la 18e place mondiale (source primaire inaccessible) — sources : fipjp.org/images/pdf/nations/vanuatu.pdf ; dailypost.vu (accès bloqué, non confirmé)

**Wallis-et-Futuna** (tier 111) — Tofata Tautapu, joueuse wallisienne réputée invaincue aux championnats d'Océanie de pétanque pendant huit ans. Elle a remporté 3 médailles d'or à l'Oceania Championship 2017 (Nouvelle-Zélande) : tir de précision, tête-à-tête femmes, et doublette femmes (avec Atonia Lutovika) ; la délégation de Wallis-et-Futuna est repartie de cette édition avec 3 ors et 1 bronze au total. À l'Oceania Championship 2025 (organisé à Wallis même), les femmes de Futuna ont remporté l'or en triplette, et le territoire a terminé 2e du classement général derrière la Polynésie française — sources : la1ere.franceinfo.fr/wallisfutuna/trois-medailles-bronze-boulistes-wallis-futuna-reviendront-heureux-oceania-petanque-nouvelle-zelande-527039.html ; la1ere.franceinfo.fr/wallisfutuna/resultats-des-oceania-2025-la-petanque-a-brille-pendant-quatre-jours-a-wallis-1634945.html
