guiraudjb/Arducible_Fanny_Petanque_World_Tour/ressources/utils/RECHERCHE_PETANQUE_PAYS.md

# Recherche pétanque par pays — sources

Registre des recherches web menées pour documenter un fait réel et sourcé
sur la pétanque dans chacun des 112 pays du tour (`Scripts/dialogues.py`),
utilisées pour générer les questions de `Scripts/quiz_questions.py` (voir
`ressources/utils/build_quiz_questions.py` et
`ressources/utils/quiz_petanque_researched_facts.py`).

Principe : chaque fait doit être vérifiable et sourcé. Quand aucune
information fiable n'a été trouvée après recherche, c'est noté
explicitement (`AUCUNE INFORMATION TROUVÉE`) plutôt que d'inventer un
fait — ces pays gardent le système de repli "reconnaître la réplique de
Fanny" (`Scripts/dialogues.py`) dans le quizz.

**100 pays documentés / 12 sans information fiable trouvée.**

Sources principales : fiches officielles "nations" de la FIPJP
(fipjp.org/images/pdf/nations/&lt;pays&gt;.pdf), sites de fédérations
nationales, Wikipédia (FR/EN), articles de presse spécialisée
(boulistenaute.com, lepetitjournal.com, etc.).

## Europe

**Allemagne** — La fédération allemande de pétanque (Deutscher
Pétanque-Verband, DPV) a été fondée le 1er décembre 1984 à Groß-Gerau ;
~26 876 licenciés actifs (2025), plus grande association du DBBPV.
Sources : https://de.wikipedia.org/wiki/Deutscher_Boccia-,_Boule-_und_P%C3%A9tanque-Verband ; https://deutscher-petanque-verband.de/

**Andorre** — Fédération Andorrane de Pétanque membre de la FIPJP depuis
1987. Source : https://fipjp.org/images/pdf/nations/andorra.pdf

**Angleterre** — Premier club britannique apparu en Essex au milieu des
années 1960 ; British Pétanque Association fondée en 1974, scindée en
2004 en fédérations nationales ; Pétanque England membre FIPJP depuis
2008. Sources : https://southerncountiespetanque.org/about/ ; https://fipjp.org/images/pdf/nations/england.pdf

**Arménie** — Fédération créée en 2004, membre FIPJP depuis 2005.
Source : https://fipjp.org/images/pdf/nations/armenia.pdf

**Autriche** — Fédération autrichienne (ÖPV) membre FIPJP depuis 1995.
Sources : https://fipjp.org/images/pdf/nations/austria.pdf ; https://www.boule.at/

**Belgique** — En 1957 à Spa, six pays (Belgique, France, Maroc, Monaco,
Suisse, Tunisie) posent les bases de la FIPJP, officiellement fondée le
8 mars 1958 à Marseille (rejointe par l'Espagne). Source :
https://www.fipjp.org/index.php/fr/fipjp/historique

**Bulgarie** — Fédération (présidée par Ludmil Smukov, Sofia) membre
FIPJP seulement depuis 2021 — l'une des affiliations les plus récentes
d'Europe. Source : https://fipjp.org/images/pdf/nations/bulgaria.pdf

**Danemark** — Dansk Petanque Forbund créée et affiliée FIPJP en 1986.
Sources : https://fipjp.org/images/pdf/nations/denmark.pdf ; https://petanque.dk/

**Écosse** — Scottish Pétanque Association fondée en 1985, affiliée CEP
et FIPJP. Source : https://www.scottishpetanque.org/

**Espagne** — Federación Española de Petanca créée en 1954 ; pays
fondateur de la FIPJP en 1958 ; pétanque arrivée dans les années 1950 via
des touristes français. Source : https://fipjp.org/images/pdf/nations/spain.pdf

**Estonie** — Fédération (EPKL) créée le 31 janvier 1993, membre FIPJP la
même année. Sources : https://fipjp.org/images/pdf/nations/estonia.pdf ; https://www.spordiregister.ee/en/organisatsioon/3255/eesti_petanquei_klubide_liit

**Finlande** — Suomen Pétanque-Liitto créée en 1982, membre FIPJP en 1983.
Source : https://fipjp.org/images/pdf/nations/finland.pdf

**France** — FFPJP fondée le 31 juillet 1945 à Marseille avec 10 000
membres fondateurs ; FIPJP fondée le 8 mars 1958. Sources :
https://www.home.ffpjp.org/pratiquer/la-pratique/l-histoire-de-la-petanque ; https://fipjp.org/images/pdf/nations/france.pdf

**Guernesey** — Membre FIPJP depuis 2018 ; premier club de l'île fondé en
1984. Sources : https://fipjp.org/images/pdf/nations/guernsey.pdf ; https://guernseypetanque.co.uk/about-us-2/

**Hongrie** — Magyar Pétanque Szövetség créée en 1989, membre FIPJP en
1991. Source : https://fipjp.org/images/pdf/nations/hongrie.pdf

**Irlande** — Irish Pétanque Association fondée en 1990, membre FIPJP en
1994. Sources : https://www.irishpetanque.org/about ; https://fipjp.org/images/pdf/nations/ireland.pdf

**Italie** — Premier titre mondial (triplette messieurs) en 1975 à
Québec ; 2e titre le 8 décembre 2024 au Zénith de Dijon face à Madagascar,
45 ans après son précédent sacre (1979, Southampton). Sources :
https://www.federbocce.it/la-federazione/storia.html ; https://www.boulistenaute.com/les-actualites-de-la-petanque-et-du-monde-bouliste/i/84827726/petanque-l-italie-sacree-45-ans-apres-un-titre-mondial-arrache-face-madag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

**Jersey** — Jersey Petanque Club fondé en 1986 (Gerald Durrell 1er
président d'honneur) ; fédération membre FIPJP depuis 2017. Sources :
https://jerseypetanque.org/about/ ; https://fipjp.org/images/pdf/nations/jersey.pdf

**Lettonie** — Fédération créée en 2009, admise la même année à la FIPJP
(après admission CEP en novembre 2008). Sources :
https://fipjp.org/images/pdf/nations/latvia.pdf ; https://petanque.lv/par-petanku/vesture/

**Lituanie** — Première fédération (LPF) créée en 2006, dissoute en 2010,
remplacée la même année par une nouvelle organisation. Source :
https://www.lse.lt/petanke/

**Luxembourg** — FLBP fondée en 1959 (Gérard Schneider), qui a ensuite
œuvré à l'installation du siège de la CEP à Belvaux-Metzerlach. Sources :
https://www.facebook.com/sportpetanque/posts/... ; https://sports.public.lu/fr/actualites/articles/2017/04/confederation-europeenne-petanque.html

**Monaco** — Membre fondateur de la FIPJP, créée le 8 mars 1958 à
Marseille. Source : https://www.boulistenaute.com/les-actualites-de-la-petanque-et-du-monde-bouliste/i/82704687/monaco-face-au-monde

**Norvège** — Fédération fondée en 1984 par trois clubs (Oslo Petanque
Club, Christiania Boule Club, Follo Petanca Club) ; fusionnée en 2007 dans
la fédération multisports norvégienne. Sources :
https://cd29petanque.fr/europe/petanque-en-norvege/ ; http://www.fipjp.org/images/pdf/nations/norvege.pdf

**Pays-Bas** — NJBB fondée le 1er septembre 1972, membre FIPJP en 1978 ;
~16 000-19 000 licenciés, ~200 clubs (50 ans en 2022). Sources :
https://njbb.nl/op-1-september-bestaat-de-njbb-50-jaar/ ; https://fipjp.org/images/pdf/nations/pays-bas.pdf

**Pays de Galles** — Welsh Pétanque Association fondée en 2004
(Pontyclun), affiliée CEP/FIPJP, organise la Welsh Cup for Clubs. Source :
https://en.wikipedia.org/wiki/Welsh_P%C3%A9tanque_Association

**Pologne** — Fédération créée le 10 novembre 2002 par six clubs
(Wrocław, Jedlina-Zdrój, Wałbrzych, Żywiec), FIPJP en 2003. Source :
https://pl.wikipedia.org/wiki/Polska_Federacja_P%C3%A9tanque

**Portugal** — FPP fondée le 26 mars 1992, FIPJP la même année. Sources :
https://www.fipjp.org/images/pdf/nations/portugal.pdf ; https://fppetanca.pt/fpp/

**Roumanie** — Pétanque introduite en 2006 par Titus Marin, fondateur de
la fédération roumaine ; invitée observatrice à la Coupe du Monde de
Grenoble 2006, championnat du monde en Thaïlande 2007. Source :
https://romanialibera.ro/special/un-sport-nou-a-patruns-in-romania-petanque-66045/ (source de presse, à recouper)

**Russie** — Fédération actuelle créée le 26 mars 2018 ; suspendue de la
FIPJP/CMSB en 2022 (guerre en Ukraine). Sources : https://boulsport.ru/vfb/1.htm ; http://www.fiboules.org/news/ukraine-:-les-federations-russe-et-du-belarus-suspendues/402/

**Saint-Marin** — Trofeo Internazionale di Petanque annuel (24e édition
en 2026 — année de création du tournoi non confirmée explicitement).
Source : https://www.sanmarinortv.sm/sport/... (incertain, non retenu
dans le quizz)

**Serbie** — Boćarski savez Srbije (Nebojša Čolić) ; premier championnat
national serbe en 2025. Sources : https://www.pink.rs/sport/679622/... ; https://bocarski-savez-srbije.rs/petank/

**Slovaquie** — SFP fondée en 1994, 19 clubs actifs aujourd'hui. Source :
https://sk.wikipedia.org/wiki/Slovensk%C3%A1_feder%C3%A1cia_p%C3%A9tanque

**Slovénie** — ZDPS fondée en 1999, FIPJP en 2000 (première année du
championnat national) ; licenciés passés de 25 à 320 en six ans. Sources :
https://fipjp.org/images/pdf/nations/slovenie.pdf ; https://zdps.si/kaj-je-petanka/

**Suède** — Svenska Bouleförbundet créée en 1977, FIPJP en 1980,
championnat national depuis 1978. Sources :
https://www.fipjp.org/images/pdf/nations/suede.pdf ; https://en.wikipedia.org/wiki/Swedish_p%C3%A9tanque_championships

**Suisse** — Fédération créée en 1953 (une des plus anciennes hors
France), FIPJP dès 1958 ; renommée "Swiss Pétanque" en 2019. Sources :
https://www.fipjp.org/images/pdf/nations/suisse.pdf ; https://swiss-petanque.ch/fr/federation/a-propos-de-swiss-petanque

**Tchéquie** — ČAPEK fondée en 1994 à Třebíč (statuts 1995, Pavel Lukeš
1er président), FIPJP en 1995, CEP en 1999. Source :
https://cs.wikipedia.org/wiki/%C4%8Cesk%C3%A1_asociace_p%C3%A9tanque_klub%C5%AF

**Turquie** — Pétanque intégrée à la fédération turque de Bocce, Bowling
et Fléchettes le 27 mai 2006 (proposition de Mutlu Türkmen). Source :
https://tr.wikipedia.org/wiki/T%C3%BCrkiye_Bocce_Bowling_Dart_Federasyonu

**Ukraine** — Fédération (UFP) cofondée en 2004 par Dmytro Bugaï ;
certificat officiel 2011 ; pétanque reconnue discipline sportive par
arrêté du 5 août 2013. Source : http://ufp.com.ua/novyny/66-... (accès
direct impossible, certificat SSL expiré)

## Afrique

**Algérie** — FASB créée en 1962, affiliée FIPJP la même année (une des
toutes premières fédérations africaines). Sources :
https://www.fipjp.org/images/pdf/nations/algerie.pdf ; https://www.fasb.dz/

**Bénin** — Fédération créée en 2004 ; a accueilli les 50e championnats du
monde à Cotonou (septembre 2023), Bénin champion du monde en doublette
mixte. Sources : https://www.fipjp.org/images/pdf/nations/benin.pdf ; https://mondial-petanque-benin.fipjp.com/

**Burkina Faso** — Fédération (Nazindintalba Jean A. Isidore Kientega)
créée et affiliée FIPJP en 1998. Source :
https://www.fipjp.org/images/pdf/nations/burkina.pdf

**Cameroun** — FECAPEDA (Yaoundé) membre FIPJP depuis 2002. Source :
https://www.fipjp.org/images/pdf/nations/cameroun.pdf

**Comores** — Fédération (Moroni) membre FIPJP depuis 1998. Source :
https://www.fipjp.org/images/pdf/nations/comores.pdf

**Congo (Brazzaville)** — FECOBoules membre FIPJP depuis 1999. Source :
https://www.fipjp.org/images/pdf/nations/congo.pdf

**Côte d'Ivoire** — FISP (Kone Adama, Abidjan) affiliée FIPJP seulement en
juin 2020 — l'une des adhésions les plus récentes d'Afrique. Source :
https://www.fipjp.org/images/pdf/nations/ivorycoast.pdf

**Djibouti** — Fédération (Stade Gouled) membre FIPJP depuis 1983, six
ans après l'indépendance. Source :
https://www.fipjp.org/images/pdf/nations/djibouti.pdf

**Égypte** — Fédération créée et affiliée FIPJP en 2010 (président Patrice
Everaert). Source : https://www.fipjp.org/images/pdf/nations/egypte.pdf

**Gabon** — FEGAP (Guillaume Mbadinga, Libreville) créée et affiliée
FIPJP en 2006. Source : https://www.fipjp.org/images/pdf/nations/gabon.pdf

**Guinée** — Fédération Guinéenne de Boules et Pétanque (Moussa Kaba,
Conakry) — année de création/adhésion non précisée. Source :
https://www.fipjp.org/images/pdf/nations/guinee.pdf (non retenu dans le
quizz, fait trop mince)

**Libye** — Libyan Bowls Federation (Mahmud Atwil, Tripoli) créée en 2009.
Source : https://www.fipjp.org/images/pdf/nations/libye.pdf

**Madagascar** — Champion du monde triplette masculine en décembre 2016 à
Antananarivo, battant le Bénin 13-5 en finale (2e titre après 1999 à La
Réunion). Sources : https://www.lexpressmada.com/05/12/2016/... ; https://www.fipjp.org/index.php/fr/championnats-du-monde/mondial-triplette-masculin/58-47e-championnats-du-monde-2016-a-madagascar

**Mali** — Fédération affiliée FIPJP en 1994 (Abibou Alabou Coulibaly,
Bamako). Source : https://www.fipjp.org/images/pdf/nations/mali.pdf

**Maurice** — Mauritius Boules Federation (Stade George V, Forest Side)
membre FIPJP depuis 1989. Source :
https://www.fipjp.org/images/pdf/nations/maurice.pdf

**Mauritanie** — FJBRIM membre FIPJP depuis 1989 ; bronze au championnat
du monde 2010 à Izmir (éliminée en demi-finale par Madagascar) ; accueille
le 10e Championnat d'Afrique à Nouakchott (nov. 2025). Sources :
https://www.fipjp.org/images/pdf/nations/mauritanie.pdf ; https://ami.mr/fr/archives/260532

**Maroc** — Champion du monde triplette messieurs en 1987 à Boumerdès
(Algérie) ; vice-champion du monde 2018 (Desbiens, Québec, finale perdue
13-7 face à la France). Sources :
https://fr.wikipedia.org/wiki/Championnats_du_monde_de_p%C3%A9tanque ; https://fr.hespress.com/15339-le-maroc-vice-champion-du-monde-de-petanque.html

**Niger** — FENIBOULES (Ly Amadou Tabsirou) membre FIPJP depuis 2011 ; 58
clubs dans 8 régions (19 à Niamey). Sources :
https://www.fipjp.org/images/pdf/nations/niger.pdf ; https://www.lesahel.org/sport-petanque-sadass-petanque-club-symbole-de-la-popularite-de-la-petanque-au-niger/

**Ouganda** — Fédération ("Sporting is the Answer Federation Uganda",
John Ssentamu) créée et affiliée FIPJP en 2013. Source :
https://www.fipjp.org/images/pdf/nations/ouganda.pdf

**République Centrafricaine** — AUCUNE INFORMATION TROUVÉE (n'apparaît
dans aucune liste de fédérations affiliées).

**République Démocratique du Congo** — AUCUNE INFORMATION TROUVÉE (à ne
pas confondre avec le Congo-Brazzaville, qui a sa propre fédération ;
seules mentions anecdotiques non vérifiables de terrains privés à
Kinshasa/Lubumbashi).

**Sénégal** — Fédération créée et affiliée FIPJP en 1982 ; bronze au
championnat du monde 2018 (équipe N'Diaye/Seck/Samoua/Dakhla Ilah).
Sources : https://www.fipjp.org/images/pdf/nations/senegal.pdf ; https://www.senenews.com/actualites/championnat-du-monde-de-petanque-2018-le-senegal-perd-contre-la-france_247618.html

**Seychelles** — Seychelles Pétanque Association (Danny Bonte, Victoria)
fondée et affiliée FIPJP en 1996. Source :
https://www.fipjp.org/images/pdf/nations/seychelles.pdf

**Tchad** — Fédération (Bachar Ibrahim, N'Djaména) créée en 2011, FIPJP
en 2012. Source : https://www.fipjp.org/images/pdf/nations/tchad.pdf

**Togo** — FTSB (Edem Bonou) créée et affiliée FIPJP en 2019 ; bronze en
tir de précision au championnat du monde 2023 à Cotonou. Sources :
https://www.fipjp.org/images/pdf/nations/togo.pdf ; https://www.republicoftogo.com/toutes-les-rubriques/sport/le-togo-decroche-le-bronze

**Tunisie** — Fédération créée et affiliée FIPJP en 1958 ; championne du
monde triplette à 3 reprises (1983, 1986, 1997 à Montpellier — Lakili,
Lakili, Lakhal). Sources : https://www.fipjp.org/images/pdf/nations/tunisie.pdf ; http://ftbp.org.tn/ftbp/palmares-de-la-federation/

**Zambie** — AUCUNE INFORMATION TROUVÉE (pas de fiche FIPJP ni fédération
identifiable malgré plusieurs recherches).

## Asie

**Afghanistan** — Fédération affiliée à la Confédération Asiatique de
Boules (ABSC/CASB, 26 membres) mais aucune date/détail trouvé. Source :
https://fipjp.org/index.php/fr/federations/confederation-asie (non
retenu dans le quizz, fait trop mince)

**Bangladesh** — Fédération créée en 2017 (Habiba Rahman Khan MP, Dacca).
Source : https://www.petanque-world.com/country/federation/bangladesh-bd/
(source communautaire, non officielle)

**Brunei** — Fédération créée en 2007 (Haji Mohammad bin Panglima, Bandar
Seri Begawan). Source : https://www.petanque-world.com/country/federation/brunei-bn/
(source communautaire)

**Cambodge** — Fédération fondée en 1992 ; 5e titre mondial consécutif par
équipe au Championnat du monde 2021 (Espagne) ; Ouk Sreymom championne du
monde de tir de précision 2021 (37-29 vs Thaïlande). Sources :
https://www.information.gov.kh/articles/60003 ; https://lepetitjournal.com/cambodge/petanque-cambodgienne-or-324906

**Chine** — Introduite à partir de 1985 par le promoteur français Bernard
Champey (universités de Pékin et Xi'an) ; pratiquée dans ~20 provinces en
2013. Source : https://www.educnaute-infos.com/article-la-petanque-en-chine-115299515.html
(source unique blog associatif)

**Corée du Sud** — Korean Petanque Federation créée en 2013 (Chai
Young-mi, Séoul). Source : https://www.petanque-world.com/country/federation/south-korea-kr/
(source communautaire)

**Inde** — Pétanque implantée depuis +100 ans à Pondichéry (comptoir
français) ; Petanque India Association incorporée le 27 août 2019,
affiliée ABSC/FIPJP. Sources :
https://www.petanque-world.com/country/federation/india-in/ ; https://www.thecompanycheck.com/company/petanque-india-association/U85300DL2019NPL354293
(date recoupée par un registre officiel indien)

**Indonésie** — FOPI créée le 11 mars 2011 (Caca Isa Saleh) ; a organisé
le championnat d'Asie juniors 2013 à Bali (22 nations). Source :
https://www.petanque.or.id/web/site/sejarah

**Iran** — Boules & Petanque Association of I.R. of Iran fondée en 2009
(Jasem Manouchehri, Hamedan) ; 13e championnat national en février 2023 à
Sari. Sources : https://www.petanque-world.com/country/federation/iran-ir/ ; https://o-sport.ir/Page121/Jasem-Manouchehri.html

**Japon** — Japan Petanque Boules Federation créée le 15 mars 2014,
association d'intérêt public. Source :
https://www.wikidata.org/wiki/Q11506905

**Kazakhstan** — Fédération affiliée ABSC/CASB/FIPJP mais aucun détail
trouvé. Source : https://fipjp.org/index.php/fr/federations/confederation-asie
(non retenu, trop mince)

**Kirghizistan** — Fédération fondée en 2022 (Medet Mukanov, Bichkek).
Source : https://www.petanque-world.com/country/federation/kyrgyzstan-kg/
(source communautaire)

**Laos** — Fédération créée en 1997, FIPJP en 1998. Source :
https://fipjp.org/images/pdf/nations/laos.pdf

**Malaisie** — Malaysia Boule Sports Federation créée en 1996, FIPJP en
2001. Source : https://fipjp.org/images/pdf/nations/malaisie.pdf

**Mongolie** — Fédération créée en 2012, FIPJP la même année. Source :
https://fipjp.org/images/pdf/nations/mongolie.pdf

**Myanmar** — Fédération créée et affiliée FIPJP en 2013 (Wunna Theikdi
Football Stadium, Nay Pyi Taw). Source :
https://fipjp.org/images/pdf/nations/myanmar.pdf

**Népal** — Petanque Federation Nepal (Dr Devkant Joshi, Katmandou) créée
et affiliée FIPJP en 2012. Source :
https://fipjp.org/images/pdf/nations/nepal.pdf

**Pakistan** — Fédération (Karachi) créée en 2002, FIPJP en 2006. Source :
https://fipjp.org/images/pdf/nations/pakistan.pdf

**Philippines** — "Pétanque de Las Islas Filipinas Inc." créée et
affiliée FIPJP en 2005. Source :
https://fipjp.org/images/pdf/nations/philippines.pdf

**Singapour** — Fédération créée en 1989, FIPJP en 1990 — une des plus
anciennes affiliations d'Asie. Source :
https://fipjp.org/images/pdf/nations/singapore.pdf

**Taïwan** — Fédération de Chinese Taipei créée en 2005, FIPJP en 2006
(T.Y. Miao). Source : https://fipjp.org/images/pdf/nations/chinese-taipei.pdf

**Thaïlande** — Introduite en 1975 par un Thaïlandais formé en France,
popularisée par la princesse mère Srinagarindra ; 2023 : 1er titre mondial
en triplette messieurs (Ratchata Khamdee), battant la France. Sources :
https://www.taipeitimes.com/News/sport/archives/2023/11/22/2003809533 ; https://en.wikipedia.org/wiki/P%C3%A9tanque_World_Championships

**Turkménistan** — Fédération (Arshavskiy Zinoviy, Achgabat) créée en
2019. Source : https://fipjp.org/images/pdf/nations/turkmenistan.pdf

**Vietnam** — Fédération (Tran Van Mui, Hanoï) créée en 2003, FIPJP en
2004. Source : https://fipjp.org/images/pdf/nations/vietnam.pdf

## Amérique

**Argentine** — Fédération créée et affiliée FIPJP en 2002 (Raúl Enrique
Quirós, Tucumán). Source : https://www.fipjp.org/images/pdf/nations/argentina.pdf

**Bolivie** — Fédération (Yerko Castro Fernandez, La Paz) affiliée FIPJP
seulement en 2025. Source : https://www.fipjp.org/images/pdf/nations/bolivia.pdf

**Canada** — Fédération créée en 1955 (Fédération Canadienne Bouliste),
FIPJP en 1959 ; Québec a accueilli en 1975 le 1er championnat du monde
FIPJP hors de France. Sources : https://www.fipjp.org/images/pdf/nations/canada.pdf ; https://petanquecentral.com/petanque-canada/

**Chili** — Federación Chilena de Bochas créée et affiliée FIPJP en 2013.
Source : https://www.fipjp.org/images/pdf/nations/chili.pdf

**Colombie** — Fédération (Gustavo Alonso Henao Chica, Cali) affiliée
FIPJP seulement en 2025. Source :
https://www.fipjp.org/images/pdf/nations/columbia.pdf

**Costa Rica** — AUCUNE INFORMATION TROUVÉE.

**Cuba** — Cuba Pétanque créée et affiliée FIPJP en 2013 (rattachée à
l'INDER, La Havane). Source : https://www.fipjp.org/images/pdf/nations/cuba.pdf

**Équateur** — AUCUNE INFORMATION TROUVÉE.

**États-Unis** — Mistral Club (plus ancien club US) fondé en 1958 à
Worcester (Massachusetts) par des immigrants français d'origine
arménienne de Marseille ; FPUSA fondée en 1973 (Alfred Levitt). Sources :
https://petanque.wordpress.com/le-mistral-club-de-petanque/ ; https://petanque.wordpress.com/2014/08/21/the-birth-of-the-fpusa/

**Guatemala** — AUCUNE INFORMATION TROUVÉE.

**Haïti** — Fédération Haïtienne de Sport Boules (Pierre Dieufils,
Port-au-Prince) créée en 2010, FIPJP en 2012. Source :
https://www.fipjp.org/images/pdf/nations/haiti.pdf

**Mexique** — Federación Mexicana de Petanca créée en 2011 pour
participer au championnat du monde 2012 (Marseille) ; 24 clubs, 4 régions.
Sources : https://www.fedmexpetanca.org/home/historia ; https://www.fipjp.org/images/pdf/nations/mexique.pdf

**Paraguay** — Federación Paraguaya de Bochas dispose du Centro Nacional
de Bochas, seul stade du continent réunissant raffa volo, petanca et
zerbín. Source : https://rcc.com.py/deporte/paraguay-es-el-primer-pais-en-contar-un-estadio-de-bochas-con-tres-modalidades/
(non retenu dans le quizz — fait de type "nom", pas de pool de
distracteurs sûr)

**Pérou** — Federación Peruana de Pétanque (Pedro Carreño Mendiola, Stade
National de Lima) affiliée FIPJP en 2021. Source :
https://www.fipjp.org/images/pdf/nations/perou.pdf

**République Dominicaine** — FEDOBOCHAS (Santiago) affiliée FIPJP depuis
2003. Source : https://www.fipjp.org/images/pdf/nations/dominicana.pdf

**Uruguay** — Federación Uruguaya de Bochas (bochas/boccia/petanca/zerbín)
fondée le 28 mai 1930. Sources :
https://www.mapeosociedadcivil.uy/organizaciones/federacion-uruguaya-de-bochas/ ; http://www.cou.org.uy/cou/es/articulos/692-federacion-uruguaya-de-bochas.html

**Venezuela** — Federación Venezolana de Bolas Criollas y Bochas (Lesbia
Marcano) créée en 2022, agréée FIPJP en 2023. Source :
https://www.fipjp.org/images/flags-nations/venezuela.pdf

## Océanie

**Australie** — Petanque Australia membre FIPJP depuis 1990. Sources :
https://www.fipjp.org/images/pdf/nations/australia.pdf ; https://www.petanqueaustralia.org.au/about/organisation-of-the-sport

**Nouvelle-Calédonie** — Fédération créée et affiliée FIPJP en 2013 (une
ligue territoriale existait depuis 1988 à Bourail) ; a accueilli la Coupe
du Monde des Confédérations à Païta en octobre 2015. Sources :
https://www.fipjp.org/images/pdf/nations/new-caledonia.pdf ; https://la1ere.franceinfo.fr/nouvellecaledonie/2014/01/14/petanque-la-caledonie-dans-la-cour-des-grands-100151.html

**Nouvelle-Zélande** — Petanque New Zealand fondée en 1993 lors d'une
réunion à l'Atomic Café d'Auckland (Chris Priestley, 1er président).
Source : https://www.petanquenz.com/petanquenz/about-us/index.html

**Tahiti (Polynésie française)** — Fédération Polynésienne de Pétanque
membre FIPJP depuis 2004 ; +2000 licenciés (13 clubs à Tahiti, 38 dans
les autres îles). Source : https://www.fipjp.org/images/pdf/nations/tahiti.pdf

**Vanuatu** — Fédération (Port-Vila, Jerry Moli) membre de la
Confédération Océanienne ; année d'affiliation FIPJP non précisée. Source :
https://fipjp.org/images/pdf/nations/vanuatu.pdf (non retenu, fait trop
mince)

**Wallis-et-Futuna** — Océania 2025 de pétanque à Wallis (16-19 octobre
2025) : Futuna, représentée seule pour la première fois, championne en
triplette dames (3 médailles au total) ; Wallis 2e au général derrière la
Polynésie française. Source :
https://la1ere.franceinfo.fr/wallisfutuna/resultats-des-oceania-2025-la-petanque-a-brille-pendant-quatre-jours-a-wallis-1634945.html

## Pays sans information fiable trouvée (12)

Saint-Marin (année du tournoi incertaine), Guinée (fait trop mince),
République Centrafricaine, République Démocratique du Congo, Zambie,
Afghanistan, Kazakhstan, Costa Rica, Équateur, Guatemala, Paraguay (fait
retenu ici en documentation mais pas dans le quizz), Vanuatu (année
manquante). Ces pays gardent le système de repli "reconnaître la réplique
de Fanny" dans `Scripts/quiz_questions.py`.
