guiraudjb/Arducible_Fanny_Petanque_World_Tour/ressources/Corrosion Et Compatibilité Des Métaux.pdf

# Traité d'Ingénierie sur la Dégradation des Matériaux Métalliques : Mécanismes Thermodynamiques, Compatibilité Galvanique et Cadre Normatif

## 1. Instabilité Thermodynamique et Enjeux Économiques de la Corrosion

La quasi-totalité des métaux employés dans l'ingénierie contemporaine, à l'exception notable des métaux nobles tels que l'or ou le platine, n'existe pas à l'état pur dans la nature. Ils se présentent sous la forme de minerais, c'est-à-dire d'oxydes, de sulfures ou de carbonates

1
L'élaboration métallurgique requiert un apport énergétique massif pour extraire le métal pur de sa gangue minérale, plaçant ainsi les métaux industriels dans un état thermodynamiquement métastable. Soumis aux agressions de leur environnement (oxygène, humidité, polluants), ces matériaux tendent inéluctablement à retourner vers leur état d'équilibre originel, beaucoup plus stable sur le plan énergétique, en formant de nouveaux composés chimiques

1
. Ce processus
de retour à l'état naturel définit le phénomène de corrosion.
L'impact économique de cette dégradation structurelle est d'une ampleur considérable. Les coûts directs globaux inhérents à la corrosion, incluant l'application de systèmes de protection, les opérations de maintenance préventive et le remplacement prématuré des infrastructures, sont évalués à environ 3,5 % du produit intérieur brut (PIB) des nations industrialisées

1
. Au-delà
de ces considérations financières, la corrosion soulève des enjeux critiques en matière de sécurité publique et industrielle. La défaillance inopinée d'éléments porteurs dans le génie civil, la rupture de canalisations sous pression dans l'industrie pétrochimique ou la perte d'intégrité de composants aéronautiques démontrent la nécessité d'une maîtrise absolue de ces phénomènes dès la genèse d'un projet

2
L'étude de la corrosion s'articule autour de mécanismes complexes et multifactoriels. Parmi ces processus, la corrosion galvanique, également qualifiée de corrosion bimétallique ou d'électro-corrosion, occupe une position singulière

1
. Elle résulte d'une erreur d'ingénierie évitable : l'association inappropriée de matériaux dissemblables au sein d'un même électrolyte. La compréhension fine de la thermodynamique électrochimique, de la conductivité des milieux et des rapports de surfaces est impérative pour prévenir ces dégradations et concevoir des assemblages pérennes.

## 2. Fondements Thermodynamiques et Électrochimiques

La corrosion en milieu aqueux ou atmosphérique humide obéit rigoureusement aux lois de l'électrochimie. Pour qu'une pile de corrosion s'établisse et s'auto-entretienne, le système doit impérativement réunir trois éléments constitutifs : une région anodique, une région cathodique et un milieu conducteur ionique, appelé électrolyte, reliant ces deux pôles tout en assurant un contact électrique direct au sein du substrat métallique

8

### 2.1. Cinétique des Réactions aux Électrodes

Le processus de détérioration matérielle s'opère exclusivement à l'anode. C'est en ce point que

se produit l'oxydation : les atomes du réseau cristallin métallique ( | ) se dissocient en ions
positifs ( | ) qui passent en solution dans l'électrolyte, abandonnant leurs électrons de
valence ( | ) dans la matrice métallique

8
. L'exemple paradigmatique est celui de l'acier ou de la fonte, où le fer subit la réaction d'oxydation suivante

10
:

Les électrons ainsi libérés transitent par conduction électronique à travers le métal jusqu'à la cathode. La cathode ne subit aucune dégradation géométrique ; elle constitue le siège de réactions de réduction permettant de consommer les électrons excédentaires. Dans la majorité des environnements naturels (eau douce, eau de mer, atmosphère), c'est l'oxygène dissous qui joue le rôle d'accepteur primaire d'électrons, conduisant à la génération d'ions hydroxyde selon la demi-équation

10
:

L'équilibre dynamique du système de corrosion est atteint lorsque la vitesse de dissolution anodique générant les électrons équivaut exactement à la vitesse de consommation de ces

mêmes électrons par la réaction cathodique

11
. Ultérieurement, les ions ferreux ( | ) et les
ions hydroxyde ( | ) réagissent au sein de l'électrolyte pour précipiter sous forme
d'hydroxydes de fer insolubles, communément appelés rouille

11
Afin de visualiser ces flux ioniques en laboratoire, il est courant d'immerger un échantillon d'acier (par exemple un clou) dans un gel d'agar-agar additionné d'une solution de chlorure de sodium (NaCl à 3 %) et d'indicateurs colorés

11
. L'ajout de ferricyanure de potassium révèle la

formation des ions aux zones anodiques par l'apparition d'une intense coloration bleue. Conjointement, la présence de phénolphtaléine met en évidence la production d'ions

hydroxyde | aux zones cathodiques par une coloration rose franche. Cette séparation
spatiale des couleurs démontre que la consommation d'oxygène et la dissolution du métal se produisent en des sites distincts

11

### 2.2. L'Équation de Nernst et les Potentiels Standards

La propension intrinsèque d'un métal à s'oxyder est quantifiée par son potentiel d'électrode

standard ( ), défini par rapport à l'électrode standard à hydrogène (ESH)

10
. La
thermodynamique permet de lier la faisabilité d'une réaction de corrosion à la variation de
l'enthalpie libre de Gibbs ( | ). Une réaction est jugée spontanée et inéluctable si | est
négatif, conformément à la relation
| 10 :
Où | désigne le nombre d'électrons transférés, | la constante de Faraday, et | la force
électromotrice de la cellule
| 10 .
Le potentiel réel d'une électrode plongée dans un environnement spécifique ne correspond pas exactement à son potentiel standard. Il est régi par l'équation de Nernst, qui intègre les paramètres de température et les concentrations des espèces en solution
| | 10 :

L'analyse des potentiels standards permet d'établir une hiérarchie absolue de la réactivité des éléments purs. Plus un potentiel est négatif, plus le métal est actif et prompt à se corroder. À l'inverse, un potentiel positif caractérise un métal noble et résistant

10
Électrode | Réaction de réduction associée | Potentiel Standard E∘ (V)
Lithium | | - 3,045 10
Calcium | | - 2,840 10
Sodium | | - 2,714 10
Magnésium | | - 2,340 1
Aluminium | | - 1,670 1

Zinc | - 0,760 1
Fer | - 0,440 1
Plomb | - 0,125 1
Hydrogène (ESH) | 0,000 (Référence) 1
Cuivre | + 0,340 1
Argent | + 0,800 1
Platine | + 1,200 1
Or | + 1,420 1

## 3. Taxonomie des Morphologies de Dégradation

Bien que les principes électrochimiques soient universels, l'expression physique de la corrosion dépend étroitement de la métallurgie locale et de l'architecture de la pièce

1
La corrosion généralisée, ou uniforme, se caractérise par une perte de masse homogène sur l'ensemble de la surface exposée. Elle est prédictible et gérable par l'ingénierie, qui peut intégrer des surépaisseurs sacrificielles lors du dimensionnement

12
. À l'opposé, la corrosion par piqûres (pitting) constitue un mode de défaillance extrêmement pernicieux. Elle se concentre sur des surfaces microscopiques, perçant le métal en profondeur tout en laissant les zones adjacentes intactes

12
. Ce phénomène frappe particulièrement les matériaux passivables, tels que les aciers inoxydables et l'aluminium, lorsque le film d'oxyde protecteur est localement détruit par des ions agressifs, en premier lieu les chlorures présents dans l'eau de mer

12
. La
capacité d'un acier inoxydable à résister à la piqûration est évaluée par l'indice PREN (Pitting Resistance Equivalent Number), dont la valeur s'accroît significativement par l'alliage avec le chrome, le molybdène et l'azote

15
La corrosion caverneuse dérive d'un mécanisme d'aération différentielle. Elle s'amorce dans les interstices, sous les joints, les têtes de vis ou les dépôts de salissures, où le renouvellement de l'électrolyte est fortement entravé

1
. Le confinement provoque un appauvrissement rapide en oxygène dissous dans la caverne. La zone confinée, désoxygénée, devient alors anodique par rapport à la vaste surface extérieure fortement aérée, enclenchant un processus de dissolution autocatalytique

1
L'intégrité microstructurale est également un facteur déterminant, comme l'illustre la corrosion intergranulaire. Cette pathologie se propage insidieusement le long des joints de grains cristallins, souvent consécutivement à une précipitation de carbures lors d'un cycle thermique inadéquat (tel que le soudage des aciers inoxydables non stabilisés). Le métal perd sa cohésion mécanique et devient hautement fragile sans manifester de perte de masse globale décelable à l'œil nu

1
. Ce phénomène peut être aggravé par des contraintes mécaniques résiduelles ou appliquées, menant à la corrosion sous contrainte, caractérisée par une fissuration brutale et catastrophique

14
Enfin, la dégradation peut être d'origine biologique, désignée sous le terme de corrosion bactérienne ou biochimique. Les bactéries sulfato-réductrices, proliférant dans des environnements anaérobies ou sous des dépôts stagnants, métabolisent les sulfates et génèrent du sulfure d'hydrogène hautement corrosif, accélérant la destruction des aciers

12

## 4. Dynamique de la Corrosion Galvanique (Bimétallique)

La corrosion galvanique se distingue des autres morphologies par sa genèse : elle est intégralement induite par l'assemblage de matériaux distincts au sein d'un système. Dès lors que deux métaux dotés de potentiels électrochimiques différents entrent en contact physique direct et baignent dans un électrolyte commun, une macro-pile court-circuitée se forme

5
Le métal caractérisé par le potentiel le plus bas, qualifié de moins noble ou de plus actif, est forcé d'assumer le rôle d'anode. Il cède ses électrons et subit une dissolution accélérée

5
Corollairement, le métal affichant le potentiel le plus élevé se polarise en cathode. Ayant un excès d'électrons fournis par l'anode, ses propres réactions de dissolution sont stoppées. Le métal noble se trouve ainsi immunisé contre la corrosion tant que le métal sacrificiel se consume

1

### 4.1. Série Galvanique et Seuils de Tolérance (Différence de Potentiel)

Si les potentiels standards théoriques offrent une base de compréhension, l'ingénierie appliquée s'appuie sur la "série galvanique". Il s'agit d'un classement des métaux et alliages réels, mesuré expérimentalement dans des environnements spécifiques, le plus souvent dans l'eau de mer ou une solution de chlorure de sodium à 2 % ou 3 %

9
La force motrice de l'attaque bimétallique est proportionnelle à l'écart de potentiel, ou

différence de potentiel ( ou ddp), mesuré en millivolts (mV), entre les deux éléments couplés

6
. Plus la ddp est vaste, plus le courant de corrosion est intense, et plus l'anode se détériore promptement

18
Les pratiques industrielles et normatives, notamment basées sur la norme française NF E 25-032 relative aux fixations, établissent des seuils de tolérance critiques
| 21 . Un couplage est
considéré comme sûr si la différence de potentiel n'excède pas 200 à 250 mV
| 21 . Entre 200 et
300 mV, le risque devient modéré et nécessite une analyse contextuelle
| 8 . Cependant, le
franchissement du cap des 300 mV (et particulièrement au-delà de 500 mV) signale un danger imminent : le métal anodique subira une attaque corrosive inacceptable, imposant la modification des matériaux ou la conception d'isolations strictes
| 8 .

### 4.2. Le Rapport des Surfaces : Règle d'Or de la Conception Architecturale

Bien que la ddp définisse la probabilité thermodynamique de la corrosion, la cinétique de destruction — c'est-à-dire la vitesse à laquelle l'épaisseur du matériau disparaît — est presque exclusivement gouvernée par le rapport des surfaces exposées entre l'anode et la cathode

18
Les lois de l'électrocinétique imposent que le courant global d'oxydation produit à l'anode soit strictement égal au courant global de réduction consommé par la cathode. Cependant, la

criticité de l'attaque dépend de la densité de courant ( ), définie comme l'intensité totale divisée par la surface active de l'électrode

10
Si la surface de la cathode est immense et que la surface de l'anode est infime, l'anode microscopique doit générer un volume colossal d'électrons pour satisfaire l'appétit de la vaste cathode. La densité de courant anodique devient faramineuse, conduisant à une perforation fulgurante de la petite pièce. Ce scénario du couplage "grande cathode / petite anode" est l'erreur de conception la plus catastrophique en ingénierie

21
. Un exemple classique est l'utilisation de rivets en aluminium (anode) pour assembler de vastes tôles en acier ou en cuivre (cathode).
À l'inverse, une configuration "grande anode / petite cathode" dilue la faible demande en électrons de la minuscule cathode sur une gigantesque surface anodique. La perte de masse de l'anode est alors si infime qu'elle demeure imperceptible et sans conséquence sur la durée de vie de l'infrastructure

21
. C'est ce principe qui justifie l'utilisation ubiquitaire de vis en acier inoxydable (petite cathode) pour fixer d'immenses structures en aluminium (grande anode)

15

### 4.3. Polarité Environnementale et Conductivité de l'Électrolyte

La propagation du courant galvanique est intimement liée à la nature de l'électrolyte. Un environnement intérieur sec, occasionnellement soumis à une condensation d'eau pure, présente une très faible conductivité électrique. La corrosion se limitera alors au joint immédiat entre les deux métaux

8
. À l'inverse, en milieu marin, l'eau chargée en ions chlorures agit comme un électrolyte hautement performant. Le courant galvanique peut alors circuler sur de vastes distances, propageant l'attaque anodique bien au-delà de la zone de contact physique

1
. De
plus, les sels chlorurés ont la capacité de briser les films de passivation, exacerbant drastiquement les cinétiques de réaction

1

## 5. Cartographie des Compatibilités Métalliques

La réussite d'un assemblage repose sur l'étude rigoureuse des couples galvaniques. Le tableau suivant synthétise les écarts de potentiel mesurés en millivolts (mV) entre différents métaux de construction usuels plongés dans une solution saline, permettant d'identifier immédiatement les risques d'association

8
Métal | Inox | Cuivr | Laiton | Aciers | Étain | Alumi | Acier | Zinc

/ Alliag e (Anod e poten tielle en colon ne, Catho de en ligne) | 304L/ 316L (mV) | e (mV) | / Bronz e (mV) | / Fonte (mV) | (mV) | nium (mV) | Galva nisé (mV) | (mV)
Acier Inoxy dable 304L | 0 | - | - | - | - | - | - | -
Cuivr e | 320 9 | 0 | - | - | - | - | - | -
Laiton / Bronz e | ~70-1 00 9 | 40-70 9 | 0 | - | - | - | - | -
Aciers (au carbo ne) | 750 / 9 390 | 9 530 | ~460-9 490 | 0 | - | - | - | -
Étain | 550 / 9 140 | 9 280 | ~210-9 240 | 9 250 | 0 | - | - | -
Alumi nium | 840 / 9 440 | 9 580 | ~510-9 540 | 9 50 | 300 9 | 0 | - | -
Acier Galva | 9 ~760 | 900 9 | ~830-9 860 | 9 370 | 620 9 | 320 9 | 0 | -

nisé

Zinc | 1150 / 9 780 | 9 920 | ~850-9 880 | 9 390 | 640 9 | 340 9 | 20 9 | 0

### 5.1. Associations Formellement Interdites et Mises en Garde

Certains couplages génèrent des processus de destruction si véloces et systémiques qu'ils sont formellement proscrits par les standards d'ingénierie.
L'Incompatibilité Critique : Cuivre et Zinc (ou Acier Galvanisé)
Le couplage entre le cuivre (ou ses alliages comme le laiton ou le bronze) et l'acier galvanisé ou le zinc pur est l'un des plus redoutés

12
. La noblesse du cuivre impose une différence de potentiel dépassant 900 mV face au zinc

9
. En contact direct, la dissolution du zinc est spectaculaire, transformant l'acier galvanisé en rouille rouge dès que la couche protectrice est annihilée

7
Cependant, le danger ne réside pas uniquement dans le contact physique. Le phénomène de corrosion par lessivage et cémentation est tout aussi destructeur. Si le cuivre est placé en amont du zinc (par exemple, des éléments de couverture en cuivre situés au-dessus de chéneaux en zinc, ou une tuyauterie en cuivre alimentant un ballon en acier galvanisé), l'eau ou
la condensation dissout des traces infimes d'ions cuivriques ( | )
| 12
. Entraînés par le flux,
ces ions atteignent la surface du zinc en aval. Une réaction d'oxydoréduction violente s'opère : les ions cuivre se réduisent et précipitent sous forme de dépôts de cuivre métallique sur la matrice zinguée, forçant la dissolution équivalente du zinc. Ces milliers de précipités cuivrés forment autant de micro-cathodes disséminées sur le zinc, générant de microscopiques piles galvaniques locales qui perforent le matériau de façon anarchique et inexorable

7
Le Couplage Aluminium et Cuivre
L'association directe entre le cuivre et l'aluminium engendre une force électromotrice approchant les 600 mV, propulsant l'aluminium vers une oxydation désastreuse

9
. Même lorsque
l'aluminium bénéficie d'une protection par anodisation épaisse ou par un revêtement thermolaqué, la moindre rayure ou discontinuité du film expose une minuscule surface d'aluminium nu à l'agression d'une vaste surface de cuivre cathodique. La densité de courant y devient colossale, perforant l'enveloppe à vitesse grand V

28
. De manière analogue au couple Cuivre/Zinc, tout ruissellement d'eau issue du cuivre vers des menuiseries en aluminium est à proscrire

33
La Problématique du Titane
Le titane est plébiscité pour sa résistance hors norme en environnement agressif. Toutefois, son extraordinaire noblesse le hisse à un potentiel voisin de celui de l'or ou du platine

21
. Le
coupler directement avec des aciers au carbone, de l'aluminium ou du zinc sans dispositifs d'isolation sévères induit une corrosion rapide et inexorable du partenaire le moins noble, la ddp pouvant franchir la barre des 900 mV

21

### 5.2. Associations Tolérées et Recommandées (Ingénierie Optimisée)

La réalisation d'infrastructures hybrides est possible en maîtrisant finement les écarts de potentiels et les ratios géométriques

9
La Synergie Acier Inoxydable et Aluminium (Le Paradoxe de la Surface) L'écart de potentiel mesuré entre un acier inoxydable austénitique (304L/316L) et l'aluminium varie de 440 à 840 mV

9
. Sur le papier, ce couplage semble risqué pour l'aluminium. Pourtant, il s'agit de l'association la plus exploitée dans le bâtiment (fixations de bardage) et l'industrie aérospatiale

26
. Ce succès s'explique exclusivement par la règle des rapports de surface. En employant des éléments de fixation en acier inoxydable (vis, rivets, écrous sertis), on associe une cathode de surface négligeable à une anode (panneaux, profilés en aluminium) dont la surface est exponentiellement supérieure

15
. La corrosion de l'aluminium a bien lieu, mais elle est répartie sur une si vaste étendue que la perte d'épaisseur annuelle devient infinitésimale et n'affecte pas l'intégrité de l'ouvrage

26
. La prudence reste néanmoins de mise en milieu marin extrême (CX), où l'usage de mastics d'étanchéité ou de canons isolants demeure recommandé pour éviter les piqûres sous tête

26
La Compatibilité Zinc et Aluminium
Le zinc (ou l'acier galvanisé) et l'aluminium démontrent une remarquable affinité galvanique. Leurs potentiels de dissolution sont si voisins que la ddp n'excède généralement pas 50 à 100 mV

9
. Le contact direct entre des bardages en aluminium et des ossatures en acier galvanisé, ou l'utilisation de visserie zinguée sur des structures en alliages légers, est une pratique sûre et validée en atmosphère rurale ou industrielle

33
. En milieu très salin (immersion), une corrosion additionnelle modérée du zinc peut survenir, mais elle demeure technologiquement gérable

29
Acier Inoxydable et Alliages Cuivreux
La juxtaposition d'acier inoxydable (particulièrement les nuances au molybdène type 316) avec le cuivre, le laiton ou le bronze est excellente. Les écarts de potentiels relevés n'excèdent guère 70 à 150 mV

9
. Cette faible réactivité explique leur utilisation conjointe massive dans les réseaux de distribution d'eau potable, la robinetterie industrielle et l'accastillage naval, sans observer de dégradations mutuelles préjudiciables

7

## 6. Cadre Normatif et Prescriptions d'Ingénierie (Normes ISO et DTU)

La prévention de la corrosion bimétallique n'est pas qu'une recommandation technique ; elle est dictée par des cadres normatifs mondiaux et nationaux qui engagent la responsabilité des bureaux d'études et des maîtres d'ouvrage.

### 6.1. Classification de la Corrosivité et Protection des Structures (ISO 12944, ISO 1461, ISO 14713)

La norme NF EN ISO 12944 constitue la clé de voûte de la protection des structures en acier par systèmes de peinture, tandis que les normes ISO 1461 et ISO 14713 encadrent la galvanisation à

chaud

2
. L'approche initiale exige la définition stricte de l'environnement, catégorisé de C1 à CX selon la perte d'épaisseur annuelle attendue

2
Catégorie de Corrosivité | Type d'Environnement (Exemples) | Agressivité et Impacts sur le Design
C1 | Bureaux, espaces intérieurs 2 chauffés . | Très faible. Tolérance sur certains couples limites.
C2 | Atmosphères rurales, hangars non chauffés avec condensation 2 . | Faible. L'acier non protégé montre des signes d'oxydation de surface.
C3 | Milieux urbains, industriels modérés, zones côtières à salinité modérée 2 . | Moyenne. Les fixations nécessitent des revêtements adaptés (zingage lourd, flocage) 44 .
C4 | Zones industrielles agressives, chantiers navals, front de mer 2 . | Élevée. Isolation électrique des couples hétérogènes obligatoire. Rétentions d'eau proscrites 44 .
C5 / CX | Zones tropicales humides, offshore direct, ponts maritimes soumis aux 2 embruns . | Extrême. Matériaux nobles (Inox 316L, Titane) ou protection cathodique 39 requise .

Les milieux immergés sont classés de Im1 (eaux douces) à Im4 (eaux salines avec protection cathodique)

2
. Pour les structures galvanisées, la norme NF A 35-503 définit la qualité des aciers en trois catégories (A, B, C) selon leur teneur en silicium et en phosphore

37
. Le respect de ces
teneurs contrôle "l'effet Sandelin", qui dicte la réactivité entre l'acier et le zinc en fusion. Des aciers de catégorie C, surchargés en silicium/phosphore, provoquent une croissance incontrôlée des alliages Fer-Zinc, générant des revêtements de plus de 200 µm d'épaisseur, d'aspect mat et parfois fragiles, influençant la durée de vie du composant face aux agressions galvaniques

37
De plus, la norme NF EN 1090-2 (régissant l'exécution des charpentes métalliques) impose que les éléments de fixation (boulons, rondelles) partagent une durabilité au moins équivalente à celle de la structure qu'ils lient

46
. Un boulon de classe 8.8 ou 10.9 (selon EN 14399) galvanisé ne doit pas être substitué par une alternative de moindre noblesse sous peine de rupture catastrophique de l'assemblage

50

### 6.2. L'Enveloppe du Bâtiment : Les Règles strictes des DTU 40.x

La toiture et le bardage constituent le théâtre privilégié des corrosions par lessivage atmosphérique. Les Documents Techniques Unifiés (DTU) imposent une discipline draconienne.
- DTU 40.41 (Zinc) & DTU 40.45 (Cuivre) : Ces documents entérinent juridiquement l'interdiction de positionner des équipements en cuivre (chéneaux, ornements, collerettes) en surplomb d'installations en zinc ou en acier galvanisé

30
. Cette ségrégation
vise à annihiler la corrosion par cémentation des ions cuivriques. De surcroît, le zinc doit être rigoureusement isolé des mortiers ou plâtres frais, dont l'alcalinité extrême ronge le métal

53
- DTU 40.44 (Acier Inoxydable) : Bien que l'acier inoxydable soit prestigieux, sa spécification obéit à des règles strictes. En atmosphère marine ou industrielle agressive, la nuance austénitique de base 304L (1.4307) doit être impérativement supplantée par une nuance fortement alliée au molybdène, telle que le 316L (1.4404 ou 1.4571), sous peine de voir des coulures de rouille disgracieuses et des piqûres perforantes ruiner la couverture

56
- Aération et géométrie : Les DTU 40.41 et 40.45 exigent des toitures dites "froides", intégrant une lame d'air ventilée de 4 à 6 cm sous le voligeage, afin de dissiper la condensation nocturne. L'absence d'une telle ventilation engendre une corrosion fulgurante en sous-face des métaux (formation intempestive de rouille blanche sur le zinc)

31

### 6.3. Hydraulique et Distribution : Le Dogme du DTU 60.1

Les installations de plomberie et d'eau chaude sanitaire (ECS) concentrent une triple contrainte : températures élevées, oxygénation constante, et circulation de fluides conducteurs. Le NF DTU 60.1 (et DTU 60.5) codifie la hiérarchie des matériaux pour endiguer la destruction galvanique des réseaux

32
- La Règle de l'Amont et de l'Aval : Il est strictement prohibé d'installer la moindre portion de canalisation ou de raccord en cuivre en amont d'un réseau en acier galvanisé

12
. La
justification repose à nouveau sur le transport des ions | destructeurs pour le zinc.
- L'Impasse des Boucles Sanitaires : Dans le cadre des boucles d'eau chaude sanitaire (réseau de recirculation assurant l'eau chaude instantanée), l'association cuivre et acier galvanisé est totalement proscrite. Dans un tel circuit fermé, la notion de flux directionnel disparaît, et la contamination par les ions cuivriques affecte irréversiblement l'ensemble des organes galvanisés

7
- Température et Traitements : Le DTU alerte sur l'instabilité de l'acier galvanisé au-delà de 60 °C, température à laquelle le potentiel du zinc s'inverse par rapport à celui du fer dans les eaux riches en bicarbonates, détruisant son rôle sacrificiel et propulsant la perforation des tubes

12
. Pour contrer ces effets et atténuer la corrosion généralisée, des traitements d'eau sont autorisés, notamment l'injection de silicates et de polyphosphates alcalins

12
. Toutefois, les silicates, excellents inhibiteurs pour l'acier galvanisé, n'offrent aucune protection aux canalisations en cuivre

12
. Des adoucisseurs d'eau (résines échangeuses de cations) peuvent abaisser la conductivité et réduire la sévérité du courant galvanique, bien qu'ils ne suppriment pas la pile électrochimique initiale

7
. En
présence de métaux dissemblables (par exemple la connexion d'une pompe immergée en acier inoxydable avec des canalisations galvanisées), l'usage de raccords diélectriques isolants (ou l'intercalation de sections en PVC/PEHD) est une nécessité absolue

7

## 7. Arsenal Technologique et Stratégies d'Assemblage Préventives

La lutte contre la dégradation des matériaux hétérogènes réclame l'intégration de contre-mesures dès l'avant-projet, s'appuyant sur cinq leviers d'ingénierie fondamentaux

1

### 7.1. Compatibilité et Optimisation Géométrique

La première itération d'un design doit rechercher l'homogénéité matérielle, ou se restreindre à des métaux dont l'écart de potentiel n'excède pas 200 mV

20
. Si l'hétérogénéité est dictée par des contraintes mécaniques ou budgétaires (par exemple l'utilisation massive d'aluminium pour l'allègement des structures de transport couplé à des châssis en acier

59
), l'ingénieur doit
impérativement éviter de concevoir de petites pièces anodiques

24
. Les éléments cruciaux de fixation (boulonnerie, inserts) doivent toujours être prescrits dans le métal le plus cathodique du système (ex. A2, A4, ou 316L) pour sanctuariser leur résistance

22
. L'épaisseur des tôles
intervient également dans l'ancrage : l'utilisation d'inserts taraudés aveugles (type POP Nut™) nécessite l'emploi de métaux galvaniquement compatibles, et dont la géométrie (tête affleurante ou noyée) empêche la création de crevasses favorisant la rétention de saumure

5

### 7.2. Rupture de la Continuité Électrique (Isolation Diélectrique)

La pile galvanique s'effondre dès lors que la migration électronique est entravée. L'interposition physique de polymères techniques (Nylon, Téflon®, Élastomères, résines acétales) entre les deux métaux accomplit cet objectif

5
- Connectique et Visserie : L'usage de canons isolants, de manchons épaulés et de rondelles diélectriques permet d'isoler le fût de la vis ainsi que sa tête par rapport à la pièce traversée

5
- Barrettes Bimétalliques : Dans les environnements électriques et de mise à la terre, où la conductivité électrique doit paradoxalement être maintenue tout en liant du cuivre à de l'aluminium (ou à de l'acier zingué), on recourt à des raccords de transition bimétalliques. Ces cosses, plaques ou rondelles spécifiques intègrent une transition métallurgique stable, évitant le couplage électrochimique explosif de l'interface directe

9

### 7.3. Confinement et Protection par Revêtements (ISO 12944)

L'oblitération de l'électrolyte empêche la réaction cathodique. L'application de systèmes de peintures multicouches à haute teneur en solides ou riches en pigments anticorrosion (époxy durci au polyamide, laques polyuréthanes) permet d'isoler l'ensemble de l'architecture, certifiée

selon les durabilités de l'ISO 12944 (de Faible à Très Haute durabilité | ans)
| 2

Une erreur magistrale consiste à ne revêtir que l'anode : le moindre défaut du film protecteur (égratignure, porosité) concentrera un foudroyant courant de dissolution anodique sur la minuscule zone à nu, la cathode restante demeurant immense

5
. La règle de l'art stipule que si un seul élément doit être peint par économie, ce doit impérativement être la cathode

5
. L'usage
de revêtements avancés, comme le chromage fin et dense (Armoloy TDC), offre une barrière infranchissable aux électrolytes tout en apportant une tenue mécanique supérieure aux arbres de transmission ou composants aérospatiaux

21
. Dans la fixation, l'usage de couches d'alliages de zinc (Zinc-Nickel) ou de zinc lamellaire supplante le cadmiage (hautement toxique et banni par les normes RoHS) pour assurer une protection sacrificielle robuste aux aciers sans agresser l'aluminium²⁸

### 7.4. Assemblage Avancé et Traitement Thermique

Lorsque les pièces doivent être fusionnées, les techniques de jonction sophistiquées pallient les limites de la métallurgie classique. Le soudage par faisceau d'électrons (EBW), le soudage par diffusion (HIP) ou le brasage sous vide permettent d'unir des métaux fondamentalement dissemblables sans introduire de métaux d'apport intermédiaires créant de nouveaux gradients galvaniques

60
. Ces opérations sous atmosphère contrôlée (vide ou hydrogène) purgent les oxydes de surface et garantissent une intégrité moléculaire exempte d'interstices, réduisant les sites d'amorçage de la corrosion caverneuse et galvanique dans les turbines, les échangeurs de chaleur et l'aéronautique

60

### 7.5. Protection Cathodique Appliquée

Pour la sauvegarde d'infrastructures colossales impossibles à isoler (pipelines, plateformes pétrolières, ponts côtiers, navires), l'ingénierie orchestre volontairement la pile galvanique en faveur de l'ouvrage

3
- Anodes Sacrificielles : L'acier est connecté à des blocs de métaux hyper-actifs (alliages de zinc, de magnésium ou d'aluminium) disséminés sur la coque ou dans le sol. Ces blocs s'oxydent continuellement en saturant l'acier d'électrons, lui imposant le rôle de cathode immunisée

1
- Courant Imposé : Une source externe de courant continu, couplée à des anodes inertes (titane revêtu, graphite), injecte un flux électronique massif sur l'infrastructure, abaissant son potentiel bien en deçà du seuil d'oxydation

2

## 8. Conclusion

L'altération des composants métalliques par corrosion bimétallique ne relève d'aucune fatalité ; elle constitue l'aboutissement prévisible d'une incompatibilité électrochimique et d'erreurs d'intégration architecturale. La préservation de l'intégrité des structures exige une appropriation totale des règles thermodynamiques et cinétiques qui gouvernent ces transferts ioniques.
Les interdits formels dictés par l'expérience et codifiés par les normes — à l'image du contact destructeur entre le cuivre et l'acier galvanisé, ou de l'association de l'aluminium aux alliages cuivreux en milieu humide — constituent le socle de toute démarche de conception sécuritaire.

L'optimisation des configurations tolérées, comme le couplage de l'aluminium et de l'acier inoxydable, démontre avec acuité la supériorité de la règle des rapports de surface (grande anode face à une petite cathode) face à la seule lecture théorique des écarts de potentiel. Finalement, dans un paysage industriel régi par les directives ISO 12944, l'exécution EN 1090 et les DTU nationaux, l'anticipation de la corrosion doit se muer en un véritable exercice de simulation prédictive dès l'avant-projet. De l'évaluation de la corrosivité du milieu, au choix de revêtements barrières, jusqu'à la prescription de fixations diélectriques, l'ingénierie des matériaux s'affirme comme le seul rempart crédible pour garantir la longévité des infrastructures de demain et enrayer le coût dévastateur des avaries de corrosion.

Sources des citations

1. Lutte contre la corrosion - Maurin Fixation, https://fixation.emile-maurin.fr/custom/docs/modele/fix_chap7_fi/chapitre-7-lutte-contre-corrosion-pdf-673-ko-fix_chap-lmod7.pdf (https://fixation.emile-maurin.fr/custom/docs/modele/fix_chap7_fi/chapitre-7-lutte-contre-corrosion-pdf-673-ko-fix_chap-lmod7.pdf)
2. CORROSIVITÉ & DURABILITÉ - Filière Peinture Anticorrosion, https://www.filiere-peinture-anticorrosion.fr/wp-content/uploads/2023/07/FicheN03_2024_Corrosivite_et_durabilite.pdf.pdf (https://www.filiere-peinture-anticorrosion.fr/wp-content/uploads/2023/07/FicheN03_2024_Corrosivite_et_durabilite.pdf.pdf)
3. Expertise en corrosion et protection anticorrosion - Cetim, https://www.cetim.fr/content/view/flyer/90808/Expertise-in-corrosion-and-corrosi on-protection.pdf (https://www.cetim.fr/content/view/flyer/90808/Expertise-in-corrosion-and-corrosion-protection.pdf)
4. Expertise en corrosion et protection anticorrosion - Cetim, https://www.cetim.fr/prestations/conseil-et-expertises/expertise-en-corrosion-et-protection-anticorrosion/ (https://www.cetim.fr/prestations/conseil-et-expertises/expertise-en-corrosion-et-protection-anticorrosion/)
5. Corrosion électrolytique Compatibilité galvanique de métaux divers - Visselect, http://www.visselect.com/adncms/images/stories/notices_techniques/ecrous__sertir_notices_techniques.pdf (http://www.visselect.com/adncms/images/stories/notices_techniques/ecrous__sertir_notices_techniques.pdf)
6. Quelles sont les causes de la corrosion galvanique et comment puis-je l'éviter -Accu,
https://accu-components.com/fr/p/334-quelles-sont-les-causes-de-la-corrosion -galvanique-comment-puis-je-lempecher (https://accu-components.com/fr/p/334-quelles-sont-les-causes-de-la-corrosion-galvanique-comment-puis-je-lempecher)
7. Corrosion galvanique : causes, risques et solutions - La Bonne Pompe, https://www.labonnepompe.com/fr/blog/corrosion-galvanique-causes-risques-et -solutions-n70 (https://www.labonnepompe.com/fr/blog/corrosion-galvanique-causes-risques-et-solutions-n70)
8. NOTE TECHNIQUE - Couple galvanique - Maltep, https://www.maltep.com/img/cms/Corrosion%20galvanique/P04-NT-210119-02.p df (https://www.maltep.com/img/cms/Corrosion%20galvanique/P04-NT-210119-02.pdf)
9. Mise à la terre et protection : La corrosion galvanique - Maltep, https://www.maltep.com/fr/content/26-mise-a-la-terre-et-protection-la-corrosio n-galvanique (https://www.maltep.com/fr/content/26-mise-a-la-terre-et-protection-la-corrosion-galvanique)
10. COURS DE CORROSION,
https://www.univ-biskra.dz/enseignant/bensaada/corrosion.pdf
11. Comprendre la corrosion galvanique - à www.publications.gc.ca, https://publications.gc.ca/collections/collection_2020/pch/CH57-4-22-2019-fra.p df (https://publications.gc.ca/collections/collection_2020/pch/CH57-4-22-2019-fra.pdf)

12. Corrosion | ANTAGUA, https://www.antagua.fr/corrosion-paris.html
13. Corrosion des circuits d'eau sanitaire en acier - Agence Qualité Construction, https://qualiteconstruction.com/ressource/fiches-pathologie-batiment/corrosion-circuits-eau-sanitaire-acier/ (https://qualiteconstruction.com/ressource/fiches-pathologie-batiment/corrosion-circuits-eau-sanitaire-acier/)
14. Protéger les biens métalliques contre la corrosion - SelecDEPOL, https://selecdepol.fr/mesures-constructives/proteger-les-biens-metalliques-cont re-la-corrosion (https://selecdepol.fr/mesures-constructives/proteger-les-biens-metalliques-contre-la-corrosion)
15. Module 5 : Résistance à la corrosion des aciers inoxydables - Worldstainless, https://worldstainless.org/wp-content/uploads/2025/02/Module_05_Resistance_a_la_corrosion_des_aciers_inoxydables.pdf (https://worldstainless.org/wp-content/uploads/2025/02/Module_05_Resistance_a_la_corrosion_des_aciers_inoxydables.pdf)
16. Types de corrosion et catégories de corrosivité - Bernardo Ecenarro, https://www.bernardoecenarro.com/fr/besa-lab/types-de-corrosion-et-categories-de-corrosivite/ (https://www.bernardoecenarro.com/fr/besa-lab/types-de-corrosion-et-categories-de-corrosivite/)
17. Prévention de la corrosion des matériaux métalliques - Formations - Cetim, https://www.cetim.fr/formation/formation/materiaux-et-surfaces/Materiaux-metalliques/Corrosion/prevention-de-la-corrosion-des-materiaux-metalliques-m07 (https://www.cetim.fr/formation/formation/materiaux-et-surfaces/Materiaux-metalliques/Corrosion/prevention-de-la-corrosion-des-materiaux-metalliques-m07)
18. Lutte contre la corrosion - Maurin Fixation, https://fixation.emile-maurin.fr/custom/images/rtf/chapitre-7-lutte-contre-corrosion-fix_chap-lmod7.pdf (https://fixation.emile-maurin.fr/custom/images/rtf/chapitre-7-lutte-contre-corrosion-fix_chap-lmod7.pdf)
19. tableau corrosion électrochimique (galvanique) - Velo Vert - forum velotaf, https://forum.velotaf.com/topic/34928-tableau-corrosion-electrochimique-galvanique/ (https://forum.velotaf.com/topic/34928-tableau-corrosion-electrochimique-galvanique/)
20. Comprendre la corrosion galvanique - Galvatech 2000, https://galvatech2000.com/comprendre-la-corrosion-galvanique/
21. Comprendre la corrosion galvanique : concepts, causes et prévention, https://armoloy.com/fr/Comprendre-les-causes-de-la-corrosion-galvanique%C2%A0%3A-pr%C3%A9vention-et-solutions/ (https://armoloy.com/fr/Comprendre-les-causes-de-la-corrosion-galvanique%C2%A0%3A-pr%C3%A9vention-et-solutions/)
22. 7.1 Corrosion galvanique - Maurin Fixation, https://fixation.emile-maurin.fr/custom/images/rtf/corrosion-galvanique-infra-ldoc 12.pdf (https://fixation.emile-maurin.fr/custom/images/rtf/corrosion-galvanique-infra-ldoc12.pdf)
23. Couple galvanique - GTA-Visserie et Fixations spéciales, https://www.visserie-boulonnerie-speciale.com/accueil/documentation/couple-galvanique/ (https://www.visserie-boulonnerie-speciale.com/accueil/documentation/couple-galvanique/)
24. https://armoloy.com/fr/Comprendre-les-causes-de-la-corrosion-galvanique%C2%A0%3A-pr%C3%A9vention-et-solutions/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,anode%20sera%20beaucoup%20plus%20imp ortante. (https://armoloy.com/fr/Comprendre-les-causes-de-la-corrosion-galvanique%C2%A0%3A-pr%C3%A9vention-et-solutions/)
25. Comprendre la corrosion galvanique : concepts, causes et prévention, https://armoloy.com/fr/modes-de-d%C3%A9faillance-des-m%C3%A9taux/corrosion-galvanique/ (https://armoloy.com/fr/modes-de-d%C3%A9faillance-des-m%C3%A9taux/corrosion-galvanique/)
26. La corrosion galvanique – Partie 2 - Métalétech, https://metaletech.com/2026/05/18/la-corrosion-galvanique-partie-2/
27. L'acier inoxydable réagit-il avec l'aluminium ? - SinoExtrud, https://sinoextrud.com/fr/lacier-inoxydable-reagit-il-avec-laluminium/
28. La résistance à la corrosion de l'aluminium - JPC France, https://www.jpcfrance.fr/bases-pratiques/matieres-premieres/la-resistance-a-la-corrosion/ (https://www.jpcfrance.fr/bases-pratiques/matieres-premieres/la-resistance-a-la-corrosion/)
29. Le contact du zinc avec d'autre métaux - Galvazinc, https://www.galvazinc.com/contact-zinc-autre-metaux
30. Oxydation des accessoires de toiture - Energie Plus Le Site, https://energieplus-lesite.be/theories/enveloppe9/comportement-des-materiaux4/oxydation-des-accessoires-de-toiture/ (https://energieplus-lesite.be/theories/enveloppe9/comportement-des-materiaux4/oxydation-des-accessoires-de-toiture/)
31. DTU 40.45 – Couvertures par éléments métalliques en cuivre - Batirama.com, https://www.batirama.com/article/26619-dtu-40.45-couvertures-par-elements-m etalliques-en-cuivre.html (https://www.batirama.com/article/26619-dtu-40.45-couvertures-par-elements-metalliques-en-cuivre.html)
32. Plomberie - sanitaire, https://www.btp42.fr/upload/DocumentsTech/_29_09_2021_08_36_47_36-calepin -plomberiesanitaire---essentiel-nf-dtu-60.1.pdf (https://www.btp42.fr/upload/DocumentsTech/_29_09_2021_08_36_47_36-calepin-plomberiesanitaire---essentiel-nf-dtu-60.1.pdf)
33. fiche-technique-39-comportement-aluminium-contact-autres-metaux-dans-bat iment-74.pdf,
https://www.fenetrealu.com/uploads/documents/fiche-technique-39-comportem ent-aluminium-contact-autres-metaux-dans-batiment-74.pdf (https://www.fenetrealu.com/uploads/documents/fiche-technique-39-comportement-aluminium-contact-autres-metaux-dans-batiment-74.pdf)
34. Association cuivre et acier galvanisé - smabtp, https://www.smabtp.fr/sma/assurance/infos-assurance/pathologie-et-prevention-batiment-et-tp/association-cuivre-et-acier-galvanise (https://www.smabtp.fr/sma/assurance/infos-assurance/pathologie-et-prevention-batiment-et-tp/association-cuivre-et-acier-galvanise)
35. Compatibilité inox - alu - Usinages, https://www.usinages.com/threads/compatibilite-inox-alu.33089/
36. Manuel ABSOLUMENT ZINC - Galvazinc, https://www.galvazinc.com/images/articles/PDFs/Manuel-Absolument-Zinc-V1.pd f (https://www.galvazinc.com/images/articles/PDFs/Manuel-Absolument-Zinc-V1.pdf)
37. France-Galva-Memento.pdf, https://www.francegalva.fr/wp-content/uploads/2015/04/France-Galva-Memento. pdf (https://www.francegalva.fr/wp-content/uploads/2015/04/France-Galva-Memento.pdf)
38. NF EN ISO 12944-8 - Normes - Afnor EDITIONS, https://www.boutique.afnor.org/fr-fr/norme/nf-en-iso-129448/peintures-et-vernis-anticorrosion-des-structures-en-acier-par-systemes-de-p/fa043018/12710 (https://www.boutique.afnor.org/fr-fr/norme/nf-en-iso-129448/peintures-et-vernis-anticorrosion-des-structures-en-acier-par-systemes-de-p/fa043018/12710)
39. NORME INTERNATIONALE ISO 12944-1 - IMANOR, https://www.imanor.gov.ma/wp-content/uploads/2022/05/ISO-12944-1_2017-ed.2 -id.64833-Publication-PDF-fr-1.pdf (https://www.imanor.gov.ma/wp-content/uploads/2022/05/ISO-12944-1_2017-ed.2-id.64833-Publication-PDF-fr-1.pdf)
40. Norme NF EN ISO 14713-1 - Afnor EDITIONS, https://www.boutique.afnor.org/fr-fr/norme/nf-en-iso-147131/revetements-de-zinc-lignes-directrices-et-recommandations-pour-la-protectio/fa188817/59461 (https://www.boutique.afnor.org/fr-fr/norme/nf-en-iso-147131/revetements-de-zinc-lignes-directrices-et-recommandations-pour-la-protectio/fa188817/59461)
41. Normes de galvanisation à chaud - Galvaswiss AG, https://www.galvaswiss.ch/fr/construction/normes-de-galvanisation-a-chaud/
42. FICHE QUALITE GROUPE INFO R1 REVETEMENT DE ZINC – EPAISSEUR OBTENUE -France Galva,
https://www.francegalva.fr/wp-content/uploads/2018/03/epaisseur-de-zinc-sur-a cier.pdf (https://www.francegalva.fr/wp-content/uploads/2018/03/epaisseur-de-zinc-sur-acier.pdf)
43. tout sur la galvanisation à chaud | zinq,
https://www.zinq.fr/wp-content/uploads/pdf/tout-sur-la-galvanisation-a-chaud.p df (https://www.zinq.fr/wp-content/uploads/pdf/tout-sur-la-galvanisation-a-chaud.pdf)
44. Choisir une protection anticorrosion selon ISO 12944 - xtrem coatings, https://www.xtremcoatings.com/post/comment-choisir-une-protection-anticorro sion-selon-la-classe-iso-12944 (https://www.xtremcoatings.com/post/comment-choisir-une-protection-anticorrosion-selon-la-classe-iso-12944)
45. Corrosion des métaux – Catégories de corrosivité - Métalétech, https://metaletech.com/2022/08/22/corrosion-des-metaux-categories-de-corrosivite/ (https://metaletech.com/2022/08/22/corrosion-des-metaux-categories-de-corrosivite/)
46. NORME INTERNATIONALE ISO 12944-3 - iTeh Standards, https://cdn.standards.iteh.ai/samples/64835/66b08aa1327142c0a8df95421f4db430/ISO-12944-3-2017.pdf (https://cdn.standards.iteh.ai/samples/64835/66b08aa1327142c0a8df95421f4db430/ISO-12944-3-2017.pdf)
47. Norme EN 1090-1: assemblage de structures en acier et aluminium - TRA-C industrie,
https://www.tra-c.com/fr/norme-de-soudage/norme-en-1090-1-assemblage-structures-acier-aluminium/ (https://www.tra-c.com/fr/norme-de-soudage/norme-en-1090-1-assemblage-structures-acier-aluminium/)
48. Exécution des structures métalliques Selon la norme NF EN 10902 Véronique BICILLI - PILES,
https://piles.cerema.fr/IMG/pdf/EN_1090-2_01-07-2010_cle783afc.pdf
49. Exécution des structures métalliques La nouvelle norme européenne EN 1090, https://www.otua.org/files/v3/pont-ouvrage-art/pdf/execution-structures.pdf
50. NF DTU 32.1 - Charpentes et ossatures en acier - Progineer, https://progineer.fr/workspace/regulation/dtu-32-1/
51. Corrosion | Simpson Strong-Tie, https://www.simpson.fr/fr-FR/articles/corrosion
52. Normes et codes de pratique - Galvanisation à chaud - ZinkInfo Benelux, https://www.zinkinfobenelux.com/fr/normes-et-codes-de-pratique/
53. DTU 40.4 : Guide Essentiel pour la Pose des Couvertures Zinc - Mortier Matériaux, https://mortiermateriaux.fr/dtu-40-4-couvertures-zinc/
54. NF DTU 40.41 - Couvertures par éléments métalliques en feuilles - Progineer, https://progineer.fr/workspace/regulation/dtu-40-41/
55. DTU 40.41 – Couvertures en feuilles et longues feuilles en zinc - Batirama.com, https://www.batirama.com/article/26342-dtu-40.41-couvertures-en-feuilles-et-lo ngues-feuilles-en-zinc.html (https://www.batirama.com/article/26342-dtu-40.41-couvertures-en-feuilles-et-longues-feuilles-en-zinc.html)
56. NF DTU 40.44 - Couverture en acier inoxydable - Progineer, https://progineer.fr/workspace/regulation/dtu-40-44/
57. Corrosion de feuilles de zinc en couverture - smabtp, https://www.smabtp.fr/sma/assurance/infos-assurance/pathologie-et-prevention-batiment-et-tp/corrosion-de-feuilles-de-zinc-en-couverture (https://www.smabtp.fr/sma/assurance/infos-assurance/pathologie-et-prevention-batiment-et-tp/corrosion-de-feuilles-de-zinc-en-couverture)
58. NF DTU 60.1 - Plomberie sanitaire pour bâtiments, https://www.batirama.com/article/11570-nf-dtu-60.1-plomberie-sanitaire-pour-b atiments.html (https://www.batirama.com/article/11570-nf-dtu-60.1-plomberie-sanitaire-pour-batiments.html)
59. Guide de solutions pratiques permettant de contrer la corrosion galvanique entre l'aluminium et l'acier dans le domaine du, https://aluminium.ca/wp-content/uploads/2022/11/guide-des-solutions-pratiques-corrosion-galvanique.pdf (https://aluminium.ca/wp-content/uploads/2022/11/guide-des-solutions-pratiques-corrosion-galvanique.pdf)
60. Techniques d'assemblage des métaux - Services - Bodycote, https://www.bodycote.com/fr/ce-que-nous-faisons/assemblage-de-metaux/
