guiraudjb/Arducible_Fanny_Petanque_World_Tour/ressources/utils/amérique du sud/Bochas au Venezuela et Colombie.pdf

# Analyse Anthropologique, Technique et Sociologique des Pratiques des Boules Créoles (Bolas Criollas) et des Bochas au Venezuela et en Colombie

## Introduction à la Culture des Jeux de Sphères en Amérique du Sud

L'utilisation d'objets sphériques comme instruments de jeu, de compétition et de rituel social constitue une constante anthropologique dont les origines remontent à l'aube de la civilisation humaine. Des découvertes archéologiques suggèrent que des pratiques rudimentaires de lancer de pierres arrondies existaient dès 5200 avant notre ère en Égypte ancienne, avant de s'étendre à la Grèce antique, où la balistique ludique est devenue une véritable discipline, puis à l'Empire romain, qui a introduit le concept fondamental d'une cible vers laquelle les projectiles devaient converger

1
. Au fil des siècles, ces pratiques ont traversé l'Europe médiévale, suscitant des passions si intenses qu'elles furent parfois perçues comme une menace pour l'ordre militaire ; des monarques tels que le roi Henri III d'Angleterre ou les rois Charles IV et Charles V de France ont formellement interdit ces jeux, craignant qu'ils ne détournent leurs archers et soldats de l'entraînement martial

1
En Amérique du Sud, et plus spécifiquement dans le continuum géographique et culturel formé par le Venezuela et la Colombie, cet héritage eurasiatique s'est heurté aux réalités topographiques, matérielles et sociales du Nouveau Monde. Il en a résulté une hybridation fascinante. Les "bioulze créoles" (orthographe phonétique et francisée historique pour désigner les boules créoles, ou bolas criollas en espagnol) représentent aujourd'hui bien plus qu'un simple passe-temps dominical. Elles constituent le sport traditionnel par excellence du Venezuela, unifiant les vastes plaines des Llanos jusqu'aux côtes caraïbes

4
Parallèlement, la migration européenne et la codification sportive ont introduit et préservé les bochas d'origine italienne, une discipline d'une rigueur géométrique absolue

7
. La porosité de la
frontière colombo-vénézuélienne, particulièrement autour de la ville de Cúcuta dans le département de Norte de Santander, a favorisé l'assimilation des boules créoles en territoire colombien

11
. Cette assimilation s'accompagne de l'émergence de disciplines endémiques comme le bolo criollo dans la région de Santander

14
, et s'étend jusqu'à l'excellence paralympique avec la boccia, où la Colombie domine actuellement la scène internationale

3
Ce rapport propose une autopsie exhaustive de ces écosystèmes ludiques. En disséquant leur généalogie historique, la transition matérielle de leurs équipements, l'architecture de leurs terrains, la biomécanique de leurs lancers et leurs profondes implications sociologiques et économiques, il s'agit de démontrer comment un acte cinétique simple—lancer une sphère vers une cible—révèle l'histoire coloniale, l'adaptation technologique et l'identité intrinsèque des sociétés vénézuélienne et colombienne.

## Archéologie et Histoire Évolutive des Boules Créoles

### L'Importation Coloniale et le Syncrétisme Ludique

L'introduction des jeux de boules sur le continent sud-américain est un sous-produit direct de la conquête et de la colonisation espagnoles. Les archives historiques et les traditions orales convergent pour attribuer l'arrivée de ces pratiques à un moine espagnol, qui, entre les années 1498 et 1510, aurait importé ce passe-temps au Venezuela

6
. L'objectif initial était d'offrir aux esclaves, aux indigènes asservis et aux travailleurs des haciendas une forme de divertissement canalisé durant leurs rares périodes de repos, agissant ainsi comme une soupape de sécurité sociale au sein du système oppressif des plantations

9
Dans ces premiers temps, les matériaux européens faisaient défaut. Les populations locales ont donc fait preuve d'une adaptation technologique immédiate en taillant des sphères dans les bois endémiques les plus denses et les plus durs disponibles, tels que le vera et le guayacán (gaïac)

1
. Ces bois tropicaux, réputés pour leur gravité spécifique élevée et leur résistance à la friction, permettaient d'imiter la balistique des boules européennes cloutées. La nécessité de différencier les équipes lors des affrontements a conduit à une signalétique rudimentaire mais efficace : les joueurs sculptaient ou peignaient une croix sur les boules en bois d'une équipe, tandis que les sphères de l'équipe adverse demeuraient vierges

1
L'ancrage du jeu dans les élites créoles est souvent attribué à la figure historique de Pedro Palacios y Sojo, universellement connu sous le nom de Padre Sojo, qui n'était autre que le grand-oncle du Libertador Simón Bolívar. Au XVIIIe siècle, le Padre Sojo aurait formalisé et popularisé ce jeu de boules pour divertir ses invités, sa famille et la bourgeoisie aristocratique sur ses vastes haciendas situées dans les zones de Chacao et de La Floresta, aujourd'hui intégrées à la métropole de Caracas

1
. Cette double adoption—par le prolétariat agricole et par l'aristocratie terrienne—a forgé la nature profondément interclasse et rassembleuse des bolas criollas, un phénomène rare dans les sociétés coloniales hautement stratifiées.

### L'Institutionnalisation et la Structuration Fédérale

Si le jeu est resté une pratique informelle et rurale pendant des siècles, sa popularité a connu une croissance exponentielle dans les années 1930, au point de nécessiter une standardisation

6
. La transition d'un folklore récréatif à un sport moderne s'est cristallisée en 1946, lorsque les boules créoles ont été officiellement incluses dans les Premiers Jeux Sportifs Nationaux du Venezuela

4
Toutefois, la fondation de l'orthodoxie sportive date précisément de 1956. Sous l'impulsion de Lorenzo Rivas, un chirurgien-dentiste passionné, et de Carlos Pérez Castillo, un maître d'équipage, la Fédération Vénézuélienne de Bolas Criollas a vu le jour

1
. Cette même année, lors
d'un congrès technique historique dans l'État de Lara, les délégations de diverses régions (Miranda, Lara, Aragua, Portuguesa, Guárico, Carabobo, Yaracuy, et le District Fédéral) se sont réunies

9
. Ce conclave avait pour but d'analyser, de débattre et d'unifier les myriades de règles locales et coutumières afin de promulguer le tout premier Règlement Officiel des Bolas Criollas

9
Dès lors, le sport a acquis une infrastructure compétitive pérenne, avec des championnats nationaux organisés annuellement, généralement entre août et septembre

4
. Le développement
du sport a été tel qu'en décembre 1997, l'entité dirigeante a formellement modifié son nom pour devenir la "Fédération Vénézuélienne de Bolas Criollas et Bochas" (Federación Venezolana de Bolas Criollas y Bochas), intégrant ainsi la variante italienne pour permettre aux athlètes nationaux de concourir dans les compétitions panaméricaines et mondiales sous l'égide de la Confédération Panaméricaine de Bochas

9

## Évolution Matérielle : La Révolution des Résines Synthétiques

L'un des aspects les plus fascinants de l'histoire des bolas criollas et des bochas est l'évolution des matériaux constitutifs de l'équipement, qui reflète l'histoire industrielle mondiale. Pendant longtemps, l'ivoire (marfil) a été considéré comme le matériau suprême pour la fabrication de sphères de précision, notamment pour les boules de billard, en raison de sa densité et de son élasticité

9
. Cependant, l'ivoire présentait des défauts majeurs pour un sport pratiqué en extérieur sur de la terre battue : il absorbait l'humidité, se tachait irrémédiablement, son coût était prohibitif, et son utilisation soulevait des problèmes écologiques majeurs conduisant à des restrictions de trafic international

9
La solution technologique est venue de la chimie des polymères thermodurcissables. L'adoption des résines phénoliques (telles que la bakélite) a révolutionné la fabrication des boules créoles

9
. La résine phénolique offre des avantages structurels inégalés : une résistance extrême aux chocs violents et à la friction abrasive du sable, une imperméabilité totale, et surtout, un rapport poids-volume isotrope qui garantit un centre de gravité parfait pour chaque sphère

9
. Le processus de fabrication implique le préchauffage de la résine, suivi de son injection dans des moules calibrés pour obtenir un poids exact d'environ 1,2 kg pour un diamètre d'environ 15 centimètres

9
L'arsenal officiel d'une partie de bolas criollas se compose de neuf éléments cruciaux :
- Huit boules massives : Généralement réparties en quatre boules rouges et quatre boules vertes, permettant une distinction visuelle immédiate des deux équipes sur la poussière du terrain

11
. Ces boules doivent être maintenues rigoureusement sèches ; le règlement interdit formellement toute modification chimique ou physique (comme l'ajout de résines adhésives) visant à altérer la friction de la sphère

24
- Le Mingo : Contrairement au cochonnet en bois de la pétanque française, le mingo vénézuélien est une petite bille usinée en acier massif ou en fer, d'un diamètre strictement inférieur à 5 centimètres

13
. Sa composition métallique est vitale : elle lui confère une inertie suffisante pour ne pas être projeté hors des limites du terrain à la moindre collision avec une boule d'un kilogramme lancée à pleine vitesse. L'équipement est traditionnellement transporté dans des sacs en toile imperméable ou des cestas (paniers) spécifiques, qui protègent la résine des variations thermiques et facilitent le transport lors des tournois

11

## Anatomie et Mécanique des "Bolas Criollas" (Boules Créoles)

L'architecture du jeu de bolas criollas repose sur une combinaison de topographie rurale et de règles géométriques. Le sport se pratique sur un terrain appelé cancha, qui est le théâtre d'une bataille stratégique intense.

### Topographie et Limites de la Cancha

La cancha des boules créoles est un vaste rectangle plat, exigeant des joueurs une capacité à évaluer les distances sur de longues étendues.
- Proportions et Dimensions : La fédération recommande une proportion de 2:3. Les dimensions idéales et maximales sont fixées à 20 mètres de largeur sur 30 mètres de longueur, bien que des terrains de 15x25 mètres soient couramment acceptés pour les catégories inférieures ou les espaces restreints

5
. La taille impressionnante du terrain exige une force athlétique considérable, particulièrement lors des tirs de dégagement d'un bout à l'autre de la zone.
- La Surface : La surface de jeu est délibérément naturelle, composée de terre battue, d'argile rouge ou de sable

4
. Cette texture organique implique des micro-dénivelés, des variations d'humidité et des aspérités (cailloux, racines occasionnelles) que les joueurs doivent savoir "lire" pour anticiper les déviations de la boule

24
- Les Barrières et le Cordel : Le périmètre du terrain est protégé par une vaille (valla de protección) d'au moins 50 centimètres de haut, généralement construite à partir de troncs de bois rustiques ou de plaques de béton plaquées de bois

4
. L'élément
juridictionnel le plus critique est le cordel : un fil ou une cordelette tendue à une distance maximale de 20 centimètres à l'intérieur de la barrière physique. Ce cordel délimite la zone de jeu valide. Toute boule, ou le mingo, qui franchit ce fil est déclarée hors jeu ou nulle

4

### Cinématique et Taxonomie des Lancers

Lors des compétitions officielles, le lancer s'effectue souvent depuis un calzador (ou calce), un dispositif métallique en forme de "U" ancré dans le sol. Le joueur doit y insérer son pied pivot pour garantir qu'aucune distance illicite n'est gagnée lors de l'élan

5
. La biomécanique du lancer créole diffère de celle du bowling : la paume de la main est orientée vers le bas. Le joueur balance son bras dans un arc fluide, le corps s'abaissant sur une jambe fortement fléchie tandis que l'autre jambe s'étend en arrière pour maintenir l'équilibre

13
. Une course d'élan est autorisée à condition que la ligne de faute imaginaire du calzador ne soit pas transgressée au moment de la libération de la sphère

13
L'arsenal tactique d'un joueur se divise en deux doctrines principales :
1. L'Arrime (Le Pointage) : Le geste de précision par excellence. L'arrimador lance la boule pour qu'elle décrive une parabole douce, atterrisse et roule vers le mingo. L'objectif est de s'approcher au plus près de la cible, voire de s'y coller. Un bon arrime est l'épine dorsale de la stratégie, car il oblige l'équipe adverse à consommer ses tirs puissants pour nettoyer la zone

5
. Les joueurs experts savent utiliser les courbes naturelles du terrain (curved paths) pour contourner les blocs défensifs

25
2. Le Boche (Le Tir) : L'acte de destruction tactique. Il est exécuté par le bochador, un joueur doté d'une force et d'une précision exceptionnelles, visant à expulser la boule de l'adversaire ou à déplacer le mingo

5
- Boche de aire : La boule est projetée haut dans les airs pour s'abattre directement, tel un projectile balistique, sur la boule cible, évitant ainsi les aléas du sol

5
- Boche rastrero (ou de marrana) : La boule est lancée violemment à l'horizontale, rasant le sol. Elle accumule une vitesse fulgurante et détruit les formations adverses par transfert d'énergie cinétique

5
- Le Clavao : L'apogée de l'habileté technique. C'est un boche appliqué avec un puissant effet rétroactif (backspin). À l'impact, l'énergie est transférée à la boule adverse qui est éjectée, tandis que la boule du tireur reste immobilisée, comme "clouée" au sol à l'emplacement exact de sa cible

13

### Architecture Temporelle et Statistique d'une Partie

Une partie s'articule autour de manches successives appelées tiros ou sets. Le match débute par le lancer du mingo par l'équipe ayant remporté le tirage au sort. Pour que le tir soit valide, le mingo doit atterrir dans la moitié opposée du terrain

5
. Les équipes lancent ensuite à tour de rôle ; l'équipe dont la boule est la plus éloignée du mingo doit impérativement rejouer jusqu'à ce qu'elle reprenne l'avantage ou qu'elle épuise son quota de boules

4
L'un des moments les plus dramatiques d'une manche se produit lorsque le mingo est percuté avec force. Si le mingo est déplacé à l'intérieur du terrain, la géométrie du jeu est redéfinie, transformant instantanément des boules perdantes en boules gagnantes

4
. Cependant, si la
violence de l'impact expulse le mingo au-delà du cordel délimitant la zone valide, une règle implacable s'applique : la manche entière est déclarée nulle (juego nulo). Toutes les boules sont ramassées, aucun point n'est accordé, et la manche doit être rejouée depuis son point d'origine

4
. Cette règle engendre une stratégie de dernier recours ("sauver les meubles") où une équipe en difficulté tente délibérément de sortir le mingo pour annuler la manche.
À la fin d'une manche, le juge calcule les points. Un cercle imaginaire est tracé avec le mingo en son centre, le rayon étant déterminé par la distance de la boule adverse la plus proche. Toutes les boules de l'équipe gagnante situées dans ce cercle valent un point. Une équipe peut ainsi marquer de 0 à 8 points par manche

4
. Dans les parties informelles, les mesures se font de manière empirique à l'aide de brindilles, de pas bout à bout, ou de ficelles, générant des débats animés qui font partie intégrante du folklore

13
. Un match se termine généralement lorsqu'une équipe atteint un seuil de points (souvent 20 points) ou après une limite de temps stricte (par exemple, 3 heures pour les adultes, mi-temps incluse)

13
L'évaluation des compétences individuelles a atteint un niveau de sophistication mathématique dans les ligues organisées, utilisant une métrique d'average similaire au baseball. La formule est définie par :

Un score d'average dépassant 800 (soit 80% d'efficacité tactique) indique un niveau de maîtrise élite, témoignant d'une constance remarquable face aux variables environnementales

11

## L'Orthodoxie des "Bochas" : L'Héritage Italien Codifié

S'il est fréquent, dans le langage profane latino-américain, de confondre les boules créoles avec les bochas (le terme générique issu de la langue italienne pour "boules"), les instances sportives font une distinction catégorique. Les bochas constituent un sport international, rattaché à la Fédération Internationale de Boules et très populaire dans le cône Sud (Argentine, Chili, Uruguay), mais dont les règles s'appliquent également au Venezuela pour les compétitions panaméricaines

7

### L'Espace Géométrique et les Barrières Actives

Contrairement à la rusticité tolérée de la cancha créole, le terrain de bochas est un sanctuaire de géométrie stricte, construit sur une surface synthétique ou une terre battue lissée au millimètre près, interdisant la moindre déclivité

7
Les dimensions sont immuables : 24 mètres de long sur exactement 4 mètres de large

7
L'architecture tridimensionnelle du terrain est tout aussi réglementée :
- Les Bandes Latérales : Fabriquées en planches de bois d'une épaisseur de 5 cm, elles mesurent entre 25 et 30 cm de hauteur

10
. Contrairement aux bolas criollas où les bordures ne servent que de limites passives, les bandes des bochas sont des éléments actifs de la tactique. Les joueurs utilisent ces murs pour effectuer des rebonds savants (caramboles) afin de contourner les boules ennemies

7
- Les Cabeceras (Murs de fond) : Elles s'élèvent à 1,5 mètre pour contenir les puissants tirs en l'air

10
- Le Plafond : La réglementation exige une hauteur minimale de 5,50 mètres au centre de la piste

10
. Cette exigence s'explique par la nature des tirs (bochazos) qui requièrent des trajectoires paraboliques extrêmement hautes pour atterrir verticalement sur la cible sans rouler

7

### La Cartographie Linéaire et l'Équipement

Le sol du terrain de bochas est strié de lignes transversales (A, B, C, D, E, F) qui compartimentent l'espace et régissent les droits de mouvement

10
:
- La Ligne F coupe le terrain en son centre exact

10
- La Zone de jeu libre et la Zone de rata sont définies par la ligne B (à 2 mètres du fond pour les hommes) et la ligne C (à 4 mètres pour les femmes), témoignant d'une adaptation spatiale basée sur le genre, inexistante dans les boules créoles

10
- La Ligne D (à 6,50 mètres) marque l'ultime frontière au-delà de laquelle un joueur ne peut s'avancer lors d'un tir puissant (bochazo)

10
L'équipement diffère également. Les sphères de bochas sont plus petites mais extrêmement denses, fabriquées en matériau synthétique ou en métal. Les standards internationaux fixent leur diamètre à 107 millimètres pour un poids exact de 920 grammes

7
. La cible, appelée bochín (et non mingo), est une sphère synthétique d'environ 40 mm de diamètre pesant entre 90 et 115 grammes, beaucoup plus légère que son homologue vénézuélien, ce qui la rend extrêmement volatile aux impacts

7

### Tableau Comparatif Synoptique des Disciplines

Afin de clarifier les distinctions techniques souvent ignorées par le grand public, le tableau ci-dessous synthétise les paramètres fondamentaux des trois disciplines majeures de la famille des sphères :
Paramètre Technique | Bolas Criollas (Boules Créoles) | Bochas (Standard International) | Pétanque Française
Origine et Bastion | Venezuela, influencé par l'Espagne | Italie (Bocce), Cône Sud | France, Europe, Mondial
Dimensions du Terrain | ~ 20 x 30 m (Ratio 2:3) | Strictement 24 x 4 m | Dimensions variables (min 15 x 4 m)
Surface Requise | Terre, sable, argile (irrégulière) | Lisse, sans aucun dénivelé | Gravier, sable, terre (irrégulière)
Bordures | Fil de limite (cordel) passif | Planches en bois actives (rebonds) | Délimitation au sol
Diamètre des Boules | ~ 150 mm | 107 mm | 70 à 80 mm
Poids des Boules | ~ 1 200 g | 920 g | 650 à 800 g
Matière des Boules | Résine phénolique, bakélite | Synthétique ou Métal | Acier creux
Cible | Mingo (Acier/Fer, < 50 mm, lourd) | Bochín (Synthétique, 40 | Cochonnet (Bois, ~30 mm)

| | mm, ~100 g)
Cinématique de Lancer | Arc descendant, roulement rapide | Paraboles hautes, tirs directs | Paraboles moyennes à hautes, tirs au fer
Règle Spécifique | Manche annulée si le mingo sort | Utilisation des murs autorisée | Lancer pieds joints dans un cercle

[Analyse comparative basée sur les sources 5, 12, 25, 55, 101, 113, 116]

## Le Continuum Colombien : Syncrétisme, Endémisme et Inclusion

Si le Venezuela est la patrie indivisible des boules créoles, la Colombie présente un panorama anthropologique beaucoup plus complexe, où les influences frontalières se mêlent à des traditions régionales fortes et à un leadership avant-gardiste dans le sport adapté.

### L'Osmose Frontalière à Cúcuta

La topographie politique de l'Amérique du Sud a créé une zone de confluence culturelle unique à la frontière colombo-vénézuélienne. La ville colombienne de Cúcuta, chef-lieu du département de Norte de Santander, est physiquement et économiquement intriquée avec l'État vénézuélien de Táchira. Dans ce creuset, les frontières nationales s'effacent devant les coutumes. Les bolas criollas ont traversé le pont international Simón Bolívar pour s'enraciner profondément dans la société de Cúcuta

11
À Cúcuta, le sport n'est pas seulement toléré ; il est institutionnalisé. Des universités de premier plan, telles que l'Université Libre de Cúcuta, organisent des tournois officiels de boules créoles sur leurs campus

12
. Les politiques publiques municipales intègrent également cette pratique dans leurs programmes de gériatrie et de cohésion sociale : la mairie de Cúcuta finance l'équipement de parcs avec des terrains de boules créoles, utilisés comme thérapie ludo-motrice pour les personnes âgées, aux côtés du tejo et du parqués

32

### L'Endémisme du Bolo Criollo en Santander

Si l'on s'enfonce plus au sud dans la région andine de Santander (autour de Bucaramanga et Sabana de Torres), l'influence des bolas criollas disparaît au profit d'un sport endémique d'une tout autre nature : le Bolo Criollo

15
. Déclaré officiellement "expression culturelle et sportive" et patrimoine régional par l'ordonnance départementale de 2010

15
, le bolo criollo se situe à la croisée des chemins entre le bowling américain, la pétanque et le jeu de quilles traditionnel. La mécanique du jeu diffère radicalement des sports de précision vers cible mobile. Il se joue sur une piste allongée (environ 24 mètres) à l'extrémité de laquelle se dressent trois quilles en bois massif (palos ou pines), mesurant chacune 60 centimètres de haut pour 8 centimètres de

diamètre

14
. Le joueur lance une lourde sphère en aluminium, en fer ou en bois (selon la force et l'âge du participant) dans le but d'abattre un maximum de quilles

33
Le lexique utilisé par les pratiquants du bolo criollo est le reflet de sa tradition rurale :
- Le Postor : Le joueur qui ouvre la manche, chargé d'établir un score de référence

14
- Le Matador : Le joueur de clôture (le "tueur"), qui possède la pression de réaliser le lancer décisif pour remporter la manche

14
- Le Garitero : L'arbitre et assistant positionné au fond de la piste, chargé de ramasser les boules lourdes, de redresser les quilles et de valider l'impact

14
. La règle d'impact est
stricte : si la boule frappe le mur du garitero et revient par ricochet abattre une quille de l'arrière vers l'avant, le point est invalidé

14
- La Cabra : Terme vernaculaire désignant le trophée, la mise financière ou la récompense remportée par les vainqueurs

14

### L'Élite Paralympique : L'Hégémonie Colombienne en Boccia

Le troisième volet de la culture des sphères en Colombie s'inscrit dans la modernité absolue du sport paralympique de haut niveau : la Boccia. Dérivée étymologiquement des bochas italiennes, la boccia a été développée dans les années 1970 en Scandinavie spécifiquement pour les personnes atteintes de paralysie cérébrale, avant de faire son entrée aux Jeux Paralympiques de 1984

2
Aujourd'hui, la Colombie, par l'intermédiaire de la Federación Colombiana de Boccia (Fecolboccia), est devenue une puissance mondiale dans cette discipline de précision absolue

17
. Se pratiquant en salle sur une surface synthétique de 12,5 x 6 mètres, le sport utilise des balles en cuir souple qui ne rebondissent pas, exigeant des calculs d'inertie complexes

3
L'aspect le plus fascinant de la boccia réside dans son système de classification médicale, qui garantit que l'issue du match repose exclusivement sur la brillance tactique et mentale plutôt que sur la capacité physique brute :
Classification | Profil Pathologique et Capacités Motrices | Assistance Autorisée | Mode de Lancer
BC1 | Paralysie cérébrale affectant sévèrement les membres. | Assistant autorisé hors zone. | Main ou Pied
BC2 | Paralysie cérébrale modérée, bonne dextérité manuelle. | Aucune assistance. | Main

BC3 | Dysfonction locomotrice extrême des quatre membres. Aucune capacité de préhension ou de relâchement soutenu. | Assistant obligatoire (doit tourner le dos au jeu) et rampe de lancement (canaleta). | Pointeur (tête/bouche)
BC4 | Handicaps physiques sévères non cérébraux (ex: dystrophie musculaire), faible contrôle du tronc. | Aucune assistance si lancé à la main. Assistant permis si lancé au pied. | Main ou Pied

[Classification paralympique basée sur les sources 28, 43, 54, 88, 114, 115]
La Colombie a cimenté son statut d'élite lors des Jeux Paralympiques de Paris 2024. Sous la tutelle de l'entraîneur national Camilo Ortega, la fratrie colombienne composée de Leidy Chica et Edilson Chica a marqué l'histoire du sport national en remportant la médaille d'or dans l'épreuve des paires mixtes BC4

18
. Ce triomphe souligne comment une nation, baignée dans la tradition des jeux de précision ruraux, a su transmuter cette affinité culturelle en excellence paralympique internationale.

## Implications Sociologiques, Économiques et Identitaires

### L'Ethos du Llanero et le Nivellement Social

Au Venezuela, les bolas criollas ne sont pas seulement un sport ; elles sont le reflet de l'âme des Llanos, ces immenses plaines inondables du bassin de l'Orénoque. Le jeu agit comme un puissant mécanisme de nivellement social. Sur la cancha couverte de poussière, les barrières de classe, de richesse ou de profession disparaissent face aux lois inaltérables de la gravité et de la cinétique

4
L'ethos du joueur de boules exige stoïcisme et concentration. Dans une société parfois marquée par la turbulence, le règlement de la fédération réprime sévèrement les tactiques dilatoires et l'intimidation verbale, forçant les participants à intérioriser la pression et à faire preuve de sang-froid dans les situations critiques

25
. Les parties, qui peuvent s'étirer sur plusieurs heures, sont le ciment des relations communautaires. Bien que le règlement officiel bannisse la consommation d'alcool pour préserver l'intégrité athlétique

25
, la pratique
vernaculaire lors des fêtes de village ou des dimanches après-midi est indissociable de la musique, des grillades et du partage de bières, transformant le sport en rituel festif

6

### Économie Touristique et Gentrification du Sport

D'un point de vue économique, la présence d'une cancha de boules créoles est devenue un marqueur d'hospitalité et de loisir dans le secteur immobilier et touristique. L'analyse des offres d'hébergement (comme Airbnb) révèle que les posadas et les maisons de vacances dans des zones côtières prisées comme Choroní et Chuao, ou dans l'État de Barinas, mettent explicitement en avant leurs terrains privés de bolas criollas comme un équipement de luxe, au même titre qu'une piscine ou qu'un accès Wi-Fi

39
. Cela indique une certaine "gentrification" du sport, qui, né dans la poussière des haciendas et des barrios, est aujourd'hui commercialisé comme une expérience culturelle authentique et un argument de vente pour le tourisme intérieur vénézuélien

39
De même, le commerce des équipements représente un marché de niche florissant. Sur les plateformes de commerce électronique latino-américaines comme MercadoLibre, un ensemble professionnel de boules créoles en résine bicolore se négocie entre 175 000 et près de 770 000 pesos colombiens (environ 40 à 180 USD) selon la qualité, témoignant de la demande continue de part et d'autre de la frontière

42

### Émancipation de Genre et Inclusion

L'évolution la plus remarquable de ces dernières décennies concerne la dynamique de genre. Historiquement perçus comme des bastions de la masculinité rurale, les bolas criollas, les bochas et le bolo criollo ont subi une mutation inclusive majeure

25
. Les fédérations nationales organisent aujourd'hui des championnats du monde et des ligues nationales exclusivement féminines avec un succès retentissant

17
Plus encore, l'introduction de tournois mixtes (parejas mixtas) modifie la sociologie du jeu. Cette intégration force à repenser les dynamiques d'équipe, où la force brute de certains tirs cède la place à la précision stratégique du pointage, valorisant ainsi une complémentarité athlétique qui reflète les avancées en matière d'équité de genre dans la société sud-américaine contemporaine

25

### Le Débat Identitaire : Parallèle avec l'Arepa

Enfin, l'étude des boules créoles offre un miroir aux tensions et aux affinités macro-culturelles entre le Venezuela et la Colombie. Les forums sociologiques et les discussions populaires soulignent souvent les différences fondamentales entre les deux nations : le Venezuela étant davantage tourné vers la culture caribéenne, tandis que la Colombie présente une mosaïque de cultures régionales andines, pacifiques et côtières extrêmement distinctes les unes des autres

50
Pourtant, tout comme la paternité de l'arepa (la galette de maïs) fait l'objet de débats passionnés et unit paradoxalement les deux peuples

51
, les bolas criollas servent de pont culturel incontestable. Que ce soit à travers l'osmose à Cúcuta, l'adoption des bochas dans les ligues sportives professionnelles, ou la réinvention du concept sphérique dans le bolo criollo et la boccia, ces sociétés démontrent que les pratiques ludiques transcendent les tracés diplomatiques.

## Conclusion

Le phénomène des jeux de boules au Venezuela et en Colombie constitue un objet d'étude anthropologique d'une densité insoupçonnée. Ce qui apparaît de prime abord comme un simple affrontement cinétique entre des sphères de résine ou de métal est en réalité l'aboutissement de siècles de métissages coloniaux, d'évolutions en science des matériaux et d'adaptations topographiques.
Le Venezuela a érigé les bolas criollas au rang de monument national, codifiant un folklore paysan en une discipline sportive rigoureuse où le calcul d'average se mêle à l'effervescence des Llanos

4
. La Colombie, fidèle à sa nature régionaliste et à son ambition sportive, a fragmenté cet héritage : elle a absorbé les boules créoles à sa frontière

12
, a sanctifié son bolo criollo dans les montagnes de Santander

15
, et a sublimé le concept originel pour se hisser sur la plus haute marche du podium paralympique mondial en boccia

17
À l'heure de la mondialisation et de l'hyper-digitalisation des loisirs, la persistance obstinée de ces disciplines démontre que le besoin de communion humaine, de maîtrise physique de l'environnement naturel et de tactique face à l'incertitude demeure une composante vitale des sociétés sud-américaines. Les sphères continueront de rouler, de se heurter et de déplacer le mingo, redessinant sans fin, à chaque lancer, la géométrie sociale d'une région unie par sa diversité.

Sources des citations

1. Juegos tradicionales de Venezuela: Las Bolas Criollas - Otilca Radio, https://radio.otilca.org/la-bolas-criollas-un-juego-milenario/
2. Boccia - Atletas Paralímpicos, Fotos & Eventos - Paralympic.org., https://www.paralympic.org/es/boccia
3. ¿Qué es el Boccia? - Señal Colombia, https://www.senalcolombia.tv/deportes/que-es-boccia
4. Bolas criollas - Wikipedia, la enciclopedia libre, https://es.wikipedia.org/wiki/Bolas_criollas
5. BOLAS CRIOLLAS - JUEGO VENEZOLANO - Hive.blog, https://hive.blog/hive-148441/@suralla/bolas-criollas-juego-venezolano
6. Más de 500 años de Bolas Criollas - Fama 98.1 FM, https://fama.fm/mas-de-500-anos-de-bolas-criollas/
7. Diferencias entre bochas, petanca y boccia: reglas, superficies y tipos de bola, https://petanca.cnsportstourism.com/bochas-vs-petanca-boccia/
8. Bochas: Juego, reglas, pista y deportes boccia, petanca - Competize, https://www.competize.com/blog/bochas-boccia-petanca-juego-deporte/
9. Historia de las Bolas Criollas en Venezuela | PDF - Scribd,
https://es.scribd.com/document/405026400/Historia-de-Las-Bolas-Criollas-en-V enezuela (https://es.scribd.com/document/405026400/Historia-de-Las-Bolas-Criollas-en-Venezuela)
10. Bochas - Wikipedia, la enciclopedia libre, https://es.wikipedia.org/wiki/Bochas
11. bolas criollas venezolanas | Guías, Proyectos, Investigaciones de Ciencias de la
Actividad Física y del Deporte | Docsity,

https://www.docsity.com/es/docs/bolas-criollas-venezolanas/7398849/
12. INICIÓ TORNEO DE BOLAS CRIOLLAS EN LA UNIVERSIDAD LIBRE CÚCUTA, http://unilibrecucuta.edu.co/portal/saladeprensa/1889-inici%C3%B3-torneo-de-b olas-criollas-en-la-universidad-libre-c%C3%BAcuta.html (http://unilibrecucuta.edu.co/portal/saladeprensa/1889-inici%C3%B3-torneo-de-bolas-criollas-en-la-universidad-libre-c%C3%BAcuta.html)
13. Bolas criollas - Wikipedia, https://en.wikipedia.org/wiki/Bolas_criollas
14. “Con el bolo criollo aprendí puntería”: Johan - Mi Señal, https://www.misenal.tv/noticias/para-chicos/en-sus-marcas/con-el-bolo-criollo-a prendi-punteria-johan (https://www.misenal.tv/noticias/para-chicos/en-sus-marcas/con-el-bolo-criollo-aprendi-punteria-johan)
15. Bolo criollo: el rescate de una expresión cultural y deportiva - Plataforma UPB, https://plataforma.bucaramanga.upb.edu.co/comunidad-viva/bolo-criollo-el-resc ate-de-una-expresion-cultural-y-deportiva (https://plataforma.bucaramanga.upb.edu.co/comunidad-viva/bolo-criollo-el-rescate-de-una-expresion-cultural-y-deportiva)
16. Así se juega el bolo criollo, patrimonio cultural de Santander - Radio Nacional de Colombia,
https://www.radionacional.co/cultura/asi-se-juega-el-bolo-criollo-patrimonio-cult ural-de-santander (https://www.radionacional.co/cultura/asi-se-juega-el-bolo-criollo-patrimonio-cultural-de-santander)
17. Categorias – Federación Colombiana de Boccia, https://fecolboccia.co/index.php/categorias/
18. Camilo Ortega, el entrenador que ha llevado al éxito el Boccia en Colombia, https://cpc.org.co/camilo-ortega-el-entrenador-que-ha-llevado-al-exito-el-boccia-en-colombia/ (https://cpc.org.co/camilo-ortega-el-entrenador-que-ha-llevado-al-exito-el-boccia-en-colombia/)
19. Triunfo dorado en Boccia: los hermanos Chica hacen historia en los Paralímpicos de París 2024 - Universidad del Valle / Cali, Colombia, https://www.univalle.edu.co/talento-vallecaucano/triunfo-dorado-boccia-herman os-chica-hacen-historia-paralimpicos-paris-2024 (https://www.univalle.edu.co/talento-vallecaucano/triunfo-dorado-boccia-hermanos-chica-hacen-historia-paralimpicos-paris-2024)
20. Historia y reglamento de bolas criollas | PDF | Juegos de habilidad física | Equipos
- Scribd, https://www.scribd.com/document/344187309/Bolas-Criollas
21. Hace más de 500 años se juega Bolas Criollas en Venezuela - El Ciudadano, https://www.elciudadano.com/latinoamerica/venezuela/hace-mas-de-500-anos-se-juega-bolas-criollas-en-venezuela/01/03/ (https://www.elciudadano.com/latinoamerica/venezuela/hace-mas-de-500-anos-se-juega-bolas-criollas-en-venezuela/01/03/)
22. America - CBI - Confederazione Boccistica Internazionale, https://cbi-prv.org/america
23. Nuevo directorio de la Federación Venezolana de Bolas Criollas y Bochas -Wix.com,
https://cpdebochas.wixsite.com/bochas/single-post/2017/08/22/nuevo-directorio-de-la-federaci%C3%B3n-venezolana-de-bolas-criollas-y-bochas (https://cpdebochas.wixsite.com/bochas/single-post/2017/08/22/nuevo-directorio-de-la-federaci%C3%B3n-venezolana-de-bolas-criollas-y-bochas)
24. Manual Didactico De Bolas Criollas - Calaméo, https://www.calameo.com/books/0024748445b182017b38a
25. Bolas criollas - Grokipedia, https://grokipedia.com/page/bolas_criollas
26. Bolas Criollas - EcuRed, https://www.ecured.cu/Bolas_Criollas
27. How to Play Bolas Criollas a Traditional Venezuelan Sport? - YouTube, https://www.youtube.com/watch?v=jA9jO3I2LsM
28. Bolas criollas: entérate en qué consiste este deporte - Venezolanos Ilustres, https://venezolanosilustres.com/secciones/salud-y-deportes/bolas-criollas-deporte-venezolano/ (https://venezolanosilustres.com/secciones/salud-y-deportes/bolas-criollas-deporte-venezolano/)
29. Bochas - WEBMASTER (CIO), https://primeradivision.com.ar/bochas/

30. ¿Cuál es la diferencia entre las bochas y la petanca? - Blog de Adrada, https://adrada.es/blog/cual-es-la-diferencia-entre-las-bochas-y-la-petanca/
31. Bocce: a sport that requires skill, precision and strategy - YouTube, https://www.youtube.com/watch?v=TQkjMo_o1G8
32. LA ALCALDÍA DE CÚCUTA REINICIA LAS ACTIVIDADES EN EL CLUB DEL ADULTO MAYOR,
https://cucuta.gov.co/la-alcaldia-de-cucuta-reinicia-las-actividades-en-el-sql/
33. Bolo criollo: el rescate de una expresión cultural y deportiva - YouTube, https://www.youtube.com/watch?v=OksMhO4dmmI
34. Bolo criollo: cuando el bolo americano se conoce con el tejo - Radionica, https://www.radionica.rocks/bolo-criollo-cuando-el-bolo-americano-se-conoce-con-el-tejo (https://www.radionica.rocks/bolo-criollo-cuando-el-bolo-americano-se-conoce-con-el-tejo)
35. From Santander to the world: Bolo Criollo - YouTube, https://www.youtube.com/watch?v=EFZYyS1FKnA
36. COMO JUGAR BOLO CRIOLLO - TEJO BOLIRANA EVENTOS EMPRESAS BOGOTA, https://www.mechaa.com/post/como-jugar-bolo-criollo
37. Clasificación - Federación Colombiana de Boccia, https://fecolboccia.co/index.php/clasificacion/
38. The Colombian Siblings Who Won Boccia Gold Together ❤️ - YouTube, https://www.youtube.com/shorts/qo8ob4cJZyc
39. Choroní, Venezuela : locations de vacances - Airbnb, https://www.airbnb.fr/choroni-venezuela/stays
40. Rancho de Chana avec piscine et boules créoles - Maisons à louer, https://www.airbnb.fr/rooms/1334160194353649533
41. État de Barinas : locations de vacances - Venezuela - Airbnb, https://www.airbnb.fr/barinas-venezuela/stays
42. Juego Bolas Criollas | MercadoLibre,
https://listado.mercadolibre.com.co/juego-bolas-criollas
43. Juego De Bolas Criollas Profesional De Resina 2 Colores - SOEMEX, https://www.soemex.com/juego-de-bolas-criollas-profesional-de-resina-2-color es (https://www.soemex.com/juego-de-bolas-criollas-profesional-de-resina-2-colores)
44. Juego De Bochas Para Deportes 8 Bolas Criollas 90mm - Mercado Libre, https://www.mercadolibre.com.co/juego-de-bochas-para-deportes-8-bolas-criollas-90mm/up/MCOU2428437064 (https://www.mercadolibre.com.co/juego-de-bochas-para-deportes-8-bolas-criollas-90mm/up/MCOU2428437064)
45. Juego De Bolas Criollas Nacional | MercadoLibre,
https://listado.mercadolibre.com.co/juego-de-bolas-criollas-nacional
46. Bolas Para Bolo Criollo | MercadoLibre,
https://listado.mercadolibre.com.co/bolas-para-bolo-criollo
47. Google Sports Data,
https://support.google.com/knowledgepanel/answer/9787176
48. Championnat du monde féminin & mixte 2025 en France, http://www.fiboules.org/news/championnat-du-monde-feminin-&-mixte-2025-en-france/524/ (http://www.fiboules.org/news/championnat-du-monde-feminin-&-mixte-2025-en-france/524/)
49. Federación Venezolana de Bolas Criollas y Bochas definió cronograma anual -Mindeporte, https://mindeporte.gob.ve/index.php/prensa/federacion-venezolana-de-bolas-cri ollas-y-bochas-definio-cronograma-anual (https://mindeporte.gob.ve/index.php/prensa/federacion-venezolana-de-bolas-criollas-y-bochas-definio-cronograma-anual)
50. ¿Cuáles son las diferencias culturales entre la gente de Colombia, Venezuela y Ecuador? : r/asklatinamerica - Reddit, https://www.reddit.com/r/asklatinamerica/comments/176iiic/whats_the_cultural_differences_between_the_people/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 (https://www.reddit.com/r/asklatinamerica/comments/176iiic/whats_the_cultural_differences_between_the_people/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)
51. ¿Cuáles son algunas de las diferencias culturales entre ecuatorianos,
colombianos y venezolanos? : r/asklatinamerica - Reddit, https://www.reddit.com/r/asklatinamerica/comments/1crgqi5/what_are_some_of_the_cultural_differences_between/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 (https://www.reddit.com/r/asklatinamerica/comments/1crgqi5/what_are_some_of_the_cultural_differences_between/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)
