guiraudjb/Arducible_Fanny_Petanque_World_Tour/ressources/utils/les jeux de boules/Jeux de boules internationaux.pdf

# Les Sports de Boules à Travers le Monde

: Une Analyse Anthropologique,

# Technique et Institutionnelle Exhaustive

L'acte de propulser un projectile sphérique ou discoïdal vers une cible, dans le but de s'en approcher ou d'en chasser un adversaire, constitue l'une des manifestations ludiques et sportives les plus anciennes et les plus universelles de l'humanité. De l'Égypte antique à l'Empire romain, où l'on jouait avec des pierres polies, jusqu'aux déclinaisons contemporaines ultra-codifiées, les jeux de boules ont traversé les siècles en s'adaptant continuellement aux géographies, aux climats et aux structures sociales des populations

1
. Sous l'apparence d'un
principe balistique fondamentalement simple, se déploie en réalité une mosaïque d'une complexité technique, sociologique et institutionnelle remarquable.
L'analyse globale de ces disciplines démontre que les sports de boules transcendent le simple divertissement. Ils incarnent un patrimoine culturel immatériel puissant, cristallisent des stratégies d'intégration sociale (notamment par le sport adapté), et génèrent une économie sportive allant du loisir précaire au professionnalisme télévisuel hautement lucratif. La présente recherche propose une exploration exhaustive de ces pratiques à l'échelle mondiale, de leurs fondements biomécaniques à leur gouvernance internationale, en passant par les particularismes régionaux qui en font la richesse.

## La Matrice Française : Démocratisation et Athlétisme

La France occupe une place centrale dans la genèse et la diffusion des sports de boules modernes, en grande partie grâce au rayonnement mondial de la pétanque. Toutefois, le paysage bouliste français est d'une grande diversité, structuré autour de scissions historiques entre des pratiques exigeant un athlétisme prononcé et des pratiques favorisant l'immobilité et l'inclusion.

### Le Jeu Provençal et la Révolution de la Pétanque

Historiquement, le sud de la France fut le berceau du « Jeu Provençal », également désigné sous l'appellation de « la longue » ou « les trois pas ». Cette discipline, d'une grande exigence physique, se pratique sur un terrain ouvert mesurant entre 24 mètres de longueur et 4 mètres de largeur

5
. Les règles biomécaniques y sont strictes : le joueur lance le but (le cochonnet) à une distance comprise entre 15 et 20 mètres pour les seniors (12 à 15 mètres pour les minimes)

5
. Pour le pointage, le joueur doit obligatoirement effectuer un pas en dehors du cercle de lancement (qui mesure entre 35 et 50 cm de diamètre) et rester en équilibre sur une jambe jusqu'à ce que la boule touche le sol

7
. Pour le tir, l'effort est encore plus intense : le joueur doit réaliser une course d'élan de trois pas (et lâcher sa boule avant le quatrième appui)

5
. Les boules
en métal (acier) utilisées doivent être creuses, sans aucun lest interne (sable, mercure ou plomb interdits), présenter un diamètre compris entre 70,5 et 80 mm et un poids oscillant entre

650 et 800 grammes

6
C'est précisément cette rigueur athlétique qui a provoqué une révolution paradigmatique au début du XXe siècle. En 1907, pour permettre aux anciens joueurs souffrant de rhumatismes de continuer à s'affronter sans la contrainte de la course d'élan, les règles furent
fondamentalement adaptées. La distance de lancer du but fut drastiquement réduite, fixée entre 6 et 10 mètres, et l'obligation de prendre de l'élan fut supprimée

1
. Les joueurs devaient
désormais lancer en gardant les deux pieds immobiles à l'intérieur du cercle, c'est-à-dire « pieds tanqués » en dialecte provençal, donnant ainsi naissance au mot « Pétanque »

1
La pétanque s'est alors imposée comme un phénomène planétaire (avec plus de 300 000 licenciés rien qu'en France), principalement grâce à cette accessibilité intergénérationnelle

9
. Elle
se joue sur des terrains plus restreints (officiellement 15 mètres sur 4 mètres, bien que des dimensions de 12 x 3 m soient tolérées), en un contre un (tête-à-tête avec 3 boules), en doublette (2 contre 2 avec 3 boules) ou en triplette, considérée comme la formation reine (3 contre 3 avec 2 boules par joueur)

9
. Les parties se disputent traditionnellement en 13 points, et infliger un score de 13 à 0 à l'adversaire perpétue la tradition humoristique d'« embrasser Fanny » (le perdant devant embrasser une représentation dénudée nommée Fanny)

6
. La précision
requise a même conduit à la création d'épreuves spécifiques de tir de précision, où les athlètes doivent frapper des boules cibles placées dans des cercles d'un mètre à des distances de 6, 7, 8 et 9 mètres, avec un barème complexe octroyant 1, 3 ou 5 points (pour un carreau parfait) pour un score maximum de 100 points

17

### La Boule Lyonnaise (Sport-Boules) : L'Athlétisme de Précision

À l'opposé de l'immobilisme de la pétanque, la Boule Lyonnaise, officiellement renommée Sport-Boules en 1981, cultive une approche éminemment athlétique et codifiée. Née à Lyon au XVIIIe siècle, cette discipline exige force, agilité et concentration sur un terrain délimité mesurant 27,50 mètres de long sur 2,5 à 4 mètres de large

12
L'ingénierie de l'équipement révèle des contraintes biomécaniques radicalement différentes : les boules lyonnaises sont nettement plus imposantes, avec un diamètre allant de 90 à 110 mm et un poids massif variant de 900 à 1 200 grammes

2
. Fabriquées à l'origine en pierre puis en bois, elles sont aujourd'hui fondues d'un seul bloc (souvent en cupro-aluminium chauffé à 1 100°C) et intègrent une masse interne mobile (ressorts ou éléments en caoutchouc) qui absorbe l'énergie cinétique pour limiter drastiquement le rebond lors des frappes

2
. Le but (le
bouchon ou « petit »), généralement en buis non ferré, mesure entre 35 et 37 mm²
Le terrain est divisé par un marquage complexe réalisé à l'aide d'une baguette appelée « cinquante ». On y trouve une aire centrale libre de 12,50 mètres et des zones d'extrémité de 7,50 mètres

2
. La particularité de la Boule Lyonnaise réside dans la validation du tir : le joueur doit annoncer sa cible, prendre une course d'élan jusqu'à une ligne spécifique (la « donnée »), et sa boule doit impérativement percuter le sol à moins de 50 centimètres de l'objet annoncé pour que la frappe soit réglementaire

15
. Cette discipline a poussé la logique physiologique à son paroxysme avec des épreuves comme le « tir progressif », un effort anaérobie extrême où le joueur effectue des courses ininterrompues d'un bout à l'autre du terrain pendant cinq minutes pour frapper un maximum de cibles disposées sur des tapis alvéolés

2
. Les parties traditionnelles se jouent souvent en 11 points (ou 13 points)

2

### Les Particularismes Régionaux : Architecture des Pistes et Asymétrie des Sphères

L'anthropologie du sport en France ne saurait être complète sans l'étude des variantes régionales endémiques. Celles-ci démontrent comment l'artisanat local, les conditions climatiques et la topographie ont modelé les règles balistiques. Nombre de ces disciplines sont aujourd'hui inscrites à l'Inventaire du Patrimoine Culturel Immatériel de la France

2
La Boule de Fort (Val de Loire et Anjou)
Pratiquée principalement dans le Maine-et-Loire (Anjou) au sein de clubs appelés « Sociétés », la Boule de Fort est une anomalie fascinante dans le monde de la physique des projectiles

1
Contrairement aux sphères parfaites de la pétanque, la boule de fort est asymétrique, ressemblant à une sphère écrasée (dite « méplate ») de 12,5 à 13 cm de diamètre et 10 cm d'épaisseur, pesant entre 1,2 et 1,5 kg

5
. Elle est cerclée de fer sur un tiers de sa largeur

11
. Cette
boule est volontairement déséquilibrée : un côté (le « fort ») est légèrement plus lourd ou plus bombé que l'autre (le « faible »)

11
. Autrefois tournées en bois de cormier ou de buis par des artisans, puis cloutées par des femmes appelées « ferreuses », ces boules sont aujourd'hui majoritairement en résine synthétique

11
L'asymétrie oblige la boule à rouler selon des trajectoires courbes. Pour exacerber ce mouvement sinusoïdal, l'architecture du terrain (le « jeu ») est unique au monde : il s'agit d'une piste incurvée en forme de gouttière, longue de 18 à 25 mètres (jusqu'à 30 mètres historiquement) et large de 5 à 8 mètres, dont les bords (les « pentes ») sont relevés de 30 à 40 centimètres

9
. Les joueurs, obligatoirement chaussés de pantoufles en feutre pour ne pas abîmer le revêtement en résine (qui a remplacé la terre battue mêlée à du sable), doivent maîtriser la gravité en faisant monter la boule sur les pentes avant qu'elle ne redescende lentement vers le maître (un cochonnet en plomb ou en bois pesant 300 grammes pour 80 à 90 mm de diamètre) en fin de course

5
Le temps de roulement d'une boule peut excéder une minute, conférant à ce sport une lenteur tactique proche du billard, où les parties (se jouant en 10 ou 12 points) peuvent durer jusqu'à trois heures

11
. Le vocabulaire y est extrêmement vernaculaire : un joueur « se campe » sur la pente, mesure avec une « bauge », et applaudit une boule qui « malonne » (titube) pour finir par faire « bibi gouline » (un biberon collé au maître)

11
. Gérée par la Fédération Française de Boule de Fort (qui compte des milliers d'adhérents), cette discipline est un pilier de la sociabilité angevine

12
La Bourle (Nord de la France et Flandres)
Le nord de la France et la Belgique voisine cultivent la pratique de la Bourle, une discipline qui pousse le concept d'asymétrie encore plus loin. La bourle n'est pas une boule, mais un imposant disque en bois dur (historiquement en gaïac, quebracho ou noyer, aujourd'hui parfois en résine canévasite)

9
. Son poids et ses dimensions varient drastiquement selon les villes : à Wattrelos, elle pèse entre 4 et 8 kg pour un diamètre de 30 à 40 cm, tandis qu'à Tourcoing, la bourle en noyer ne pèse que 2 kg pour 19,5 cm de diamètre, et descend même à 1,7 kg dans les

Flandres intérieures (Bailleul, Hazebrouck)

9
Tout comme la boule de fort, la bourle possède un côté « fort » et un côté « faible », nécessitant un lancer expert pour la faire serpenter sur une piste également cintrée (la « bourloire ») de 20 à 28 mètres de long sur environ 3 mètres de large

35
. Autrefois, la surface de ces pistes était un mélange complexe d'argile, de farine de seigle, de bouse et d'urine de vache ; elles sont aujourd'hui souvent synthétiques

36
. L'objectif n'est pas un cochonnet mobile, mais un disque de cuivre fixe de 3 cm de diamètre appelé « l'étaque », enchâssé à 50 cm des extrémités creusées (la « fosse » ou le « cul ») de la piste

35
. L'aspect tactique repose sur l'entrave : les premiers joueurs construisent des barrages défensifs, tandis que les « buqueurs » de l'équipe adverse tentent de frapper avec force pour libérer l'accès à l'étaque

37
. Le tissu
associatif est très dense, géré par des entités locales comme la Fédération des Sociétés de Bourles du Nord ou de Wattrelos, qui organisent d'innombrables tournois et championnats

40
Les Boules Bretonnes et Autres Curiosités
En Bretagne, la déclinaison des jeux illustre une hyper-fragmentation des règles locales. La Boule Bretonne se joue avec des sphères en résine synthétique (autrefois en bois tourné par les sabotiers) d'un diamètre de 92 à 110 mm et d'un poids de 600 g à 1 kg

9
. La taille du terrain en
terre battue ou sable varie de 15 à 18 mètres de long sur 3 à 4 mètres de large, strictement encadré par des bordures en bois (les planches)

9
Ce qui distingue cette discipline, outre la possibilité tactique d'utiliser les bandes latérales comme au billard pour faire ricocher la boule, c'est l'adaptation locale du centre de gravité

46
Dans le Finistère et le pays de Morlaix, la pratique exige des boules plombées (le centre de gravité est délibérément modifié par l'insertion d'un cylindre de plomb), permettant des trajectoires ultra-complexes pour contourner les obstacles

5
. À l'inverse, cette altération est rigoureusement interdite dans les Côtes d'Armor

12
. Le jeu se conclut généralement en 10 ou 12 points, le lancer aérien (sous main) y est souvent proscrit, obligeant la boule à rouler

24
D'autres curiosités complètent le panorama français, telles que la Boule de Sable (jouée dans les Mauges sur des fosses de sable de 13,5 x 2,5 m empêchant tout roulement), ou les humoristiques Boules Carrées de Cagnes-sur-Mer, qui s'appuient sur des cubes de bois aux trajectoires imprévisibles, disposant même d'un championnat du monde depuis les années 1980

1
. Récemment, des déclinaisons d'intérieur en plastique mou (pétanque indoor) ou des hybrides palet/pétanque comme le Gabaky ont vu le jour pour pallier les aléas météorologiques

5

## L'Hégémonie Anglo-Saxonne : Les Maîtres du « Bias » et du Gazon

Si les nations latines privilégient historiquement des terrains rugueux qui valorisent le lancer en cloche ou le tir de destruction en plein fer, la tradition anglo-saxonne a développé une relation quasi fusionnelle avec le gazon tondu ras. Le Lawn Bowls (ou Boulingrin) et ses sous-disciplines reposent sur une mécanique de précision roulante d'une élégance absolue.

### Lawn Bowls : La Science de la Courbe

Le Lawn Bowls, extrêmement populaire au Royaume-Uni, en Australie, au Canada, en Nouvelle-Zélande et dans l'ensemble des pays du Commonwealth, se joue avec des boules asymétriques pesant jusqu'à 1,59 kg

1
. Appelées « woods » en raison de leur fabrication historique en bois dur, elles sont aujourd'hui moulées en plastique dur ou résine époxy, mesurant environ 115 à 130 mm de diamètre

51
. L'innovation majeure de ces boules est qu'elles ne sont pas parfaitement sphériques : elles sont légèrement rabotées aux pôles et intègrent un biais (un côté est intentionnellement plus lourd que l'autre)

1
Ce biais force la boule à décrire une large courbe parabolique en perdant de la vitesse

1
. Le
joueur ne vise donc jamais la cible (appelée le « jack » ou « kitty ») en ligne droite, mais doit anticiper l'angle de courbure en fonction de la force de son lancer, du sens du biais, et de la rapidité du terrain

53
. Contrairement à la pétanque où la boule est projetée depuis le dos de la main, au Lawn Bowls, la boule est roulée avec un mouvement pendulaire fluide, la paume orientée vers le haut

51
. La technique est exclusivement axée sur le contrôle du roulement

16
. Les
parties se jouent souvent en simple (jusqu'à 21 points) ou en équipes (paires, triples, fours)

51

### Le Duel des Surfaces : Crown Green vs Flat Green

L'analyse de la pratique britannique révèle deux écoles fondamentalement distinctes, dictées par la topographie du terrain et le type de boule utilisé.
Le Flat Green Bowls est la version internationale standardisée, se jouant en plein air ou en intérieur (Indoor Bowls) sur des pistes (rinks) de gazon plat ou de moquette synthétique mesurant entre 36,6 et 40 mètres de long

52
. Les joueurs lancent depuis un tapis fixe et cherchent à approcher un jack blanc ou jaune, parfaitement rond et sans biais

52
. Les boules
utilisées ont un biais standardisé (souvent un biais numéro 3) conçu pour une trajectoire prévisible

58
. L'homogénéité du terrain fait de cette discipline un sport d'une précision chirurgicale, où une équipe utilise généralement quatre boules par joueur

54
À l'inverse, le Crown Green Bowls, majoritairement pratiqué dans le nord et les Midlands de l'Angleterre, introduit un chaos maîtrisé. Le terrain est un vaste carré de gazon irrégulier (souvent 40 à 45 yards carrés) qui présente une élévation au centre (la couronne ou « crown »), créant des pentes douces vers les bords avec de multiples ondulations

54
. Les implications
tactiques et matérielles sont profondes :
1. Le joueur qui remporte le point précédent place un petit tapis circulaire (le « footer ») n'importe où et peut envoyer le jack dans n'importe quelle direction sur la surface, à des distances variant de 19 à 75 yards

54
2. Le jack utilisé en Crown Green est asymétrique et possède lui aussi un biais (pesant environ 32 oz / 900 g) ; le joueur doit d'ailleurs montrer le côté biaisé du jack à son adversaire avant de le lancer pour révéler la trajectoire choisie

54
3. Les boules de Crown Green ont un biais beaucoup plus prononcé (biais numéro 2) pour pouvoir « grimper » la colline centrale et tenir la ligne dans les descentes

54
. Elles sont plus
légères (entre 2 lbs et 2 lbs 14 oz) et chaque joueur n'en possède que deux

54
. L'interaction
complexe entre le biais de la boule et l'inclinaison imprévisible du terrain oblige le joueur à lire le gazon comme un golfeur lirait un putting green

54

### Synthèse comparative des matériels et terrains

Pour illustrer ces variations d'ingénierie sportive, le tableau suivant synthétise les données techniques des disciplines phares :
Discipline | Dimension s moyennes du terrain | Poids de la boule | Diamètre | Asymétrie / Biais | Distance de cible
Pétanque | 15m x 4m (Plat, ouvert) | 650 - 800 g | 70,5 - 80 mm | Non (Sphère parfaite) | 6 - 10 m
Boule Lyonnaise | 27,5m x 4m (Plat, fermé) | 900 - 1200 g | 90 - 110 mm | Non (Remplissag e équilibré) | 12,5 - 20 m
Lawn Bowls (Flat) | ~36m -40m (Gazon plat) | Jusqu'à 1590 g | ~115 - 130 mm | Oui (Biais interne) | Variable, long
Boule de Fort | 18-25m x 6m (Incurvé) | 1200 - 1500 g | 125 - 130 mm | Oui (Le "Fort" et le "Faible") | Variable
Bourle (Wattrelos) | 20-28m x 3,5m (Incurvé) | 4000 -8000 g | 300 - 400 mm | Oui | Variable
Bochas (Sud-Am.) | 24m x 4m (Plat, fermé) | ~1150 g | ~115 mm | Non | Jusqu'à ~20 m

Sources croisées :

5

## L'Évolution Latine et Sud-Américaine : De la Bocce aux Bolas Criollas

Le troisième grand pôle culturel des sports de boules tire ses racines de l'Italie antique. L'Empire romain a largement contribué à la dissémination de jeux de lancer, d'abord avec des pierres, puis avec des objets sphériques en bois, qui ont évolué vers le « Bocce »

1

### Le Bocce et le Raffa en Italie

Le Bocce (pluriel de boccia) est souvent perçu comme le cousin italien de la pétanque, bien qu'il présente des divergences structurelles majeures

19
. Il se joue sur un terrain de 24 à 27,5 mètres de long pour environ 4 mètres de large, strictement délimité par des bordures en bois (les planches), souvent sur des surfaces d'argile, de gravier fin compacté ou de synthétique lisse

14
. Les boules utilisées sont massives : environ 107 à 115 mm de diamètre pour un poids d'environ 920 grammes, historiquement en bois dur, aujourd'hui en résine époxy colorée

14
La codification internationale, notamment le Raffa (géré par la Confédération Boccistica Internazionale), distingue trois types de lancers fondamentaux

5
:
- Le « Punto » : un lancer doux où le joueur fait rouler la boule pour approcher le but (le pallino de 40 à 60 mm).
- Le « Raffa » : un tir très technique nécessitant d'annoncer la pièce visée ; le joueur prend de l'élan et lance la boule avec force pour qu'elle roule sur le terrain et percute la cible.
- Le « Volo » : un tir de destruction aérien où la boule doit frapper directement la cible sans l'aide d'un long rebond au sol.
L'existence de bordures physiques permet d'utiliser les bandes pour des tirs par ricochet, ajoutant une dimension géométrique comparable au billard

14

### L'Exportation et l'Adaptation : Bochas et Bolas Criollas

L'émigration européenne massive (italienne et espagnole) vers l'Amérique du Sud au tournant des XIXe et XXe siècles a implanté ces pratiques sur le nouveau continent, où elles ont muté pour s'adapter aux réalités sociologiques et climatiques locales

63
En Argentine et en Uruguay, les « Bochas » reprennent de manière stricte l'héritage italien, devenant un pilier des clubs sociaux et des sociétés d'immigrants

63
. La discipline y est
fortement institutionnalisée : les fédérations sud-américaines imposent des terrains rigoureusement normés de 24 x 4 mètres (avec des bordures de 25 à 30 cm de haut et des plafonds d'au moins 5,50 mètres en intérieur)

61
. Les boules sud-américaines pèsent très exactement 1 150 grammes pour un diamètre de 115 mm⁶²
. La réglementation est d'une sévérité absolue, reflet d'une sportivisation très avancée : les tenues doivent être uniformes, les joueurs ont un maximum d'une minute pour jouer leur boule sous peine de sanction (anulation de boules), et les parties ont parfois des durées chronométrées (90 minutes en doublette, 120 minutes en triplette)

61
. Les annonces de tir (le « bochazo ») et les règles du « pique régulier » sur les planches ou de la « rata regular » illustrent un niveau de complexité tactique exceptionnel

62
. Le 12 octobre y est même célébré comme la Journée du Bochófilo

69
Plus au nord, au Venezuela, la pratique s'est hybridée pour devenir les Bolas Criollas, un sport d'une popularité immense, à mi-chemin entre sport de haute compétition et loisir festif

67
. Le
terrain est nettement plus large : de 22 x 11 mètres jusqu'à 25 x 15 mètres pour les catégories adultes (Libre et Master), souvent sur de la terre battue ou de l'argile rouge

67
. Le jeu oppose deux équipes, utilisant des boules en résine rouge et verte pesant environ 1,2 kg pour un diamètre de 9 à 11 cm⁷⁰
Contrairement au terrain fermé des Bochas, le jeu vénézuélien s'articule autour du « calce », une petite pièce métallique en forme de U ancrée dans le sol, d'où les joueurs doivent lancer tout en y maintenant un pied

72
. L'action balistique s'effectue avec la paume de la main orientée vers le bas. On y retrouve l'« arrime » (le pointage vers le « mingo », un cochonnet de 30 à 35 mm pesant 55 g), le « boche de aire » (tir direct en l'air) et le spectaculaire « boche rastrero » (un tir très puissant lancé à ras du sol pour détruire les barrages)

70
. Les parties se disputent jusqu'à 20 points, avec des limites de temps strictes (souvent 2h30) gérées par un chronomètre officiel, et des règles minutieuses concernant les remplacements et les temps morts supervisés par la Fédération Vénézuélienne de Bolas Criollas et Bochas

67

### Jogo da Malha : L'Alternative Portugaise

Bien que n'utilisant pas de boules sphériques, le Jogo da Malha (ou jeu du fito) au Portugal mérite d'être intégré à cette taxonomie balistique

81
. Remplaçant les boules par des disques en métal pesant environ 600 grammes (pour 10 cm de diamètre), les joueurs doivent abattre ou s'approcher au maximum d'un pilon cylindrique (le fito ou xito) placé à 15 ou 20 mètres de distance

81
. Un renversement direct du fito rapporte 4 ou 6 points, et la malha la plus proche ajoute des points jusqu'à ce qu'une équipe atteigne 30 points

82
. Ce sport partage l'ADN
biomécanique du lancer de précision tout en s'apparentant structurellement aux jeux de quilles.

## L'Hégémonie Asiatique et le Renouveau Indo-Océanique

Si les jeux de boules sont indissociables de l'Europe et de son ancienne sphère d'influence coloniale, l'Asie et l'Océan Indien représentent aujourd'hui un pôle de dynamisme incontournable, tant sur le plan de la création de nouvelles disciplines que de la suprématie acquise dans les compétitions mondiales historiques.

### Le Woodball : La Synthèse Asio-Pacifique

En 1990, Taïwan a vu naître le Woodball, un sport hybride innovant qui synthétise la mécanique des jeux de boules, du croquet et du golf

1
. Cette discipline se joue sur de vastes parcours de gazon ou de sable

85
. Un parcours complet de compétition internationale comprend 12 « fairways » (pistes) mesurant entre 3 et 10 mètres de large, pour une longueur totale devant excéder 700 mètres, intégrant des virages (doglegs) et des obstacles naturels

87
L'équipement est hautement spécifique : les joueurs frappent une boule en bois naturel parfaitement ronde (9,5 cm de diamètre, pesant entre 290 et 410 g) à l'aide d'un maillet (le mallet) en forme de T pesant 800 grammes et long d'environ 90 cm¹
. L'extrémité du maillet (la tête en forme de bouteille) est recouverte d'un capuchon en caoutchouc amortissant

84
. Le but
n'est pas d'approcher un cochonnet ni un trou, mais de faire franchir à la boule un portique fixe (le « gate ») de 15 cm de largeur

84
. Lors du passage de la sphère, une petite coupe en bois suspendue au centre du portique bascule de manière spectaculaire, validant le point

87

Géré par l'International Woodball Federation (IWbF), ce sport propose des compétitions basées soit sur le nombre total de coups (Stroke Competition), soit sur le nombre de fairways remportés (Fairway Competition)

85
. Le Woodball connaît une expansion fulgurante en Asie et s'exporte mondialement grâce à son caractère accessible, ses règles strictes encadrant les lancers (10 secondes maximum, interdiction de frapper en marchant ou avec le côté du maillet), et son exigence d'entretien foncier moindre comparée au golf

85

### Thaïlande et Madagascar : Les Nouvelles Superpuissances de la Pétanque

La véritable révolution géopolitique du monde bouliste réside cependant dans la suprématie écrasante acquise par la Thaïlande et Madagascar sur la pétanque, sport originellement et jalousement gardé par la France.
En Thaïlande, la pétanque a dépassé le stade du loisir pour devenir une véritable institution d'État. Ce développement exceptionnel trouve sa source dans les années 1950, suite au long séjour en France de la Reine Mère Srinagarindra, qui s'éprit de ce sport et décida de l'importer

90
. Fortement soutenue par la monarchie, la discipline a été intégrée de manière systématique dans les programmes de l'éducation nationale, ainsi que dans les formations de l'armée et de la police à partir des années 1960 et 1970

90
Pour soutenir cette expansion colossale de la demande publique et s'affranchir des coûteuses importations européennes, la famille thaïlandaise Chokephaibulkit (via l'entreprise FBT, déjà pionnière en Asie pour les équipements de football certifiés par la FIFA) a commencé à usiner localement des boules de pétanque de compétition dès la fin des années 1970

90
. C'est ainsi
qu'est née la marque La Franc, dont le nom vise à associer un gage de qualité balistique à l'authenticité de l'origine du jeu. Aujourd'hui homologuée par la FIPJP, La Franc équipe d'innombrables champions

90
. L'intégration institutionnelle, couplée à une rigueur d'entraînement quasi martiale, a propulsé la Thaïlande au sommet. Des joueurs thaïlandais comme Sarawut Sriboonpeng dominent régulièrement les championnats du monde (notamment en triplette et doublette mixte), venant défier et souvent vaincre les meilleures formations françaises lors de tournois internationaux majeurs

90
Un schéma de domination parallèle, bien que reposant sur une sociologie différente, s'observe à Madagascar. Ancien territoire sous influence française, la Grande Île a totalement assimilé la pétanque au point d'en faire son deuxième sport national, juste derrière le football

92
. Bien que
dépourvu de l'immense industrie manufacturière de la Thaïlande, Madagascar pallie ce manque par un vivier inépuisable de talents forgés dans les rues et sur des terrains très sélectifs, favorisant le développement d'un instinct du tir en cloche redoutable. Madagascar a remporté de multiples couronnes mondiales : sacrée championne du monde en 1999 à La Réunion, elle a réitéré l'exploit en 2016 à domicile en battant le Bénin

92
. La relève est également assurée, les juniors malgaches ayant brillamment remporté l'or en doublette mixte lors des mondiaux de 2025 en Espagne, s'imposant comme les rois incontestés de l'Océan Indien devant l'île Maurice ou Tahiti

94

## Le Sommet de l'Inclusivité : L'Hyper-Codification de la

## Boccia Paralympique

L'étude minutieuse des jeux de boules révèle que la quête de la précision géométrique est intrinsèquement liée à l'accessibilité physique. Si la création de la pétanque en 1907 fut la première étape historique vers l'inclusion des seniors, la Boccia en constitue aujourd'hui l'aboutissement technologique et sportif absolu

12
Inventée originellement pour les personnes atteintes de paralysie cérébrale (Infirmité Motrice Cérébrale), la Boccia a été intégrée comme sport officiel aux Jeux Paralympiques dès l'édition de New York en 1984, et s'adresse désormais aux athlètes souffrant de divers handicaps moteurs lourds

16
. Contrairement aux sports classiques qui misent sur la force d'impact de masses dures (acier, bronze, bois dur), la Boccia utilise des balles molles et malléables en cuir naturel ou synthétique

16
. Pour garantir l'équité mondiale, la Fédération Internationale de Boccia (BISFed / World Boccia) impose des normes d'une sévérité absolue : un jeu comprend 6 balles rouges, 6 bleues et un jack (le but) blanc, chacune pesant exactement 275 grammes (+/- 12 g) pour 270 mm de circonférence (+/- 8 mm)

16
L'ingénierie des tests d'homologation est fascinante : avant une compétition internationale, les arbitres font passer chaque balle dans un gabarit métallique rigide de 7 mm d'épaisseur (la balle doit traverser un trou de 278 mm mais ne pas passer dans un trou de 262 mm)

101
. Le
roulement est testé en laissant la balle glisser sous son propre poids sur une rampe en aluminium de 290 mm de long inclinée à 25 degrés ; à sa sortie, la balle doit impérativement parcourir au moins 175 mm en ligne droite parfaite sur une plaque de sortie pour prouver l'absence de biais interne

101
. Les matchs se disputent sur un terrain intérieur, plat et parfaitement lisse de 12,5 x 6 mètres, avec des zones de lancers délimitées par du ruban adhésif spécifique, en 4 manches (mènes) en individuel ou 6 manches en triplette

96
La grandeur de la Boccia réside dans son système de classification clinique et fonctionnelle, qui permet une compétition équitable

96
:
- BC1 : Athlètes atteints de paralysie cérébrale lançant à la main ou au pied. Ils sont autorisés à avoir un assistant sportif. Ce dernier est placé derrière le joueur, intervient uniquement sur demande pour stabiliser le fauteuil ou donner une balle, mais n'influence jamais le jeu

96
- BC2 : Athlètes disposant de capacités motrices légèrement supérieures aux BC1. Ils lancent seuls la balle, sans l'aide d'aucun assistant

96
- BC3 : La catégorie la plus emblématique de l'ingénierie du sport adapté. Ces athlètes présentent des handicaps sévères aux quatre membres et ne peuvent physiquement pas lancer la balle

96
. Ils utilisent donc une rampe (gouttière) réglable et souvent un pointeur fixé au casque ou manipulé par la bouche pour pousser la balle

96
. L'athlète est
accompagné d'un assistant sportif qui manipule la rampe selon les instructions mathématiques strictes du joueur. L'assistant doit obligatoirement rester dos au terrain tout au long du match et a l'interdiction absolue de regarder la cible, de parler ou de participer à la réflexion stratégique

96
. Cela garantit que la lecture géométrique et la victoire appartiennent à 100 % à l'intelligence de l'athlète

104

- BC4 : Athlètes atteints de déficiences graves d'origine non cérébrale (ex: myopathie, dystrophie, lésions de la moelle épinière). Ils possèdent une force résiduelle suffisante pour lancer seuls, sans assistance

96
Dans des pays comme la France, ce système paralympique est complété par des classes « National Éligible » (NE1 à NE4) qui permettent à toute personne présentant un handicap physique mineur ne rentrant pas dans les critères internationaux rigides de concourir dans des championnats officiels, faisant de la Boccia un modèle d'intégration par le sport

96

## Institutionnalisation, Économie et le Labyrinthe Olympique

La transition de ces pratiques, passant d'amusements folkloriques ou vernaculaires à de véritables disciplines sportives mondialisées, a engendré un écosystème institutionnel extrêmement dense. La gouvernance internationale est marquée par des enjeux de pouvoir, une disparité économique fulgurante entre les différentes variantes, et une obsession constante : l'intégration au programme des Jeux Olympiques.

### Le Dédale Fédéral et la Diplomatie de la Boule

Les sports de boules sont historiquement fragmentés, gérés par plusieurs fédérations internationales fondatrices jalouses de leurs prérogatives :
1. La FIPJP (Fédération Internationale de Pétanque et Jeu Provençal), fondée en 1958 à Marseille, régit les disciplines de lancer à pieds fixes ou faible élan

64
2. La FIB (Fédération Internationale de Boules), qui a autorité sur le Sport-Boules/Lyonnaise et ses épreuves athlétiques de tirs en course

15
3. La CBI (Confederazione Boccistica Internazionale), qui encadre le Punto-Raffa-Volo et les variations sud-américaines (Bochas)

64
Cependant, le Comité International Olympique (CIO) a rapidement imposé une règle : il refuse de négocier avec de multiples instances pour une famille de sports d'apparence similaire. C'est pourquoi, le 21 décembre 1985 à Monaco, ces entités se sont regroupées au sein de la CMSB (Confédération Mondiale des Sports de Boules), afin de présenter un front uni

15
. Cette stratégie
s'est avérée initialement payante, la CMSB obtenant la reconnaissance officielle du CIO en octobre 1986, et participant ainsi à divers Jeux Mondiaux (organisés par l'IWGA) et intégrant l'ARISF (Association of the IOC Recognized International Sports Federations)

89
Malgré la puissance du dossier commun « Boules Sport 2024 » visant à intégrer les Jeux de Paris avec une compétition fusionnée, l'objectif ultime de devenir un sport olympique titulaire n'a pas été atteint

109
. Face à ce revers et pour restructurer sa diplomatie, la CMSB a été dissoute en avril 2020. Elle a été immédiatement remplacée en mai 2021 par la FMBP (Fédération Mondiale de Boules et de Pétanque - ou World Pétanque Bowls Federation / WPBF), dont le siège a été établi à Prilly, en Suisse

64
. Sous la présidence de Claude Azéma, la FMBP est aujourd'hui l'unique organe formellement reconnu par le CIO pour représenter les 165 nations affiliées et leurs quelque 200 millions de pratiquants

64
Cette hyper-centralisation ne va pas sans frictions diplomatiques locales. À titre d'exemple, lorsque des fédérations nationales (comme la Fédération italienne de boules) ont tenté de promulguer des règles interdisant l'usage de certaines marques de boules de compétition sur leur territoire, la FMBP a dû intervenir par des lettres de réprimande officielles et des réunions d'urgence. Elle a fermement rappelé que seules les instances internationales détiennent le monopole de l'homologation balistique, soulignant la tension permanente entre la souveraineté nationale des fédérations et l'harmonisation mondiale exigée par le marché des équipementiers

111

### L'Économie du Sport : Les Asymétries de la Professionnalisation

Bien que le nombre d'amateurs à travers le monde soit colossal, l'économie du sport professionnel dans le monde des boules est marquée par une asymétrie géographique et structurelle frappante.
Dans la sphère francophone de la pétanque, l'économie des joueurs professionnels demeure précaire. Même sur des circuits télévisés d'élite comme les Masters de Pétanque (qui réunit en été les meilleures équipes mondiales sur 8 étapes dans des stades éphémères), les dotations financières ou prize money restent relativement modestes comparées à d'autres sports télévisés

117
. Seule une infime minorité de boulistes peut prétendre vivre exclusivement du jeu. Le « salaire » d'un joueur professionnel de pétanque n'est d'ailleurs pas un salaire fixe traditionnel, mais un assemblage financier complexe et volatile : il repose sur le partage des primes de victoires (les gains étant divisés entre les membres de la triplette ou doublette), les contrats d'équipementiers (marques de boules ou de vêtements qui versent des primes à la performance ou un fixe pour l'exposition du logo), et les défraiements divers offerts par les clubs d'élite

118
. Cette saisonnalité forte oblige nombre d'athlètes de haut niveau à conserver une activité salariée parallèle, à se reconvertir dans l'événementiel sportif, ou à exploiter des niches comme le coaching et le tourisme bouliste pour stabiliser leurs revenus, les frais incompressibles (licences, déplacements internationaux) venant fortement grever leurs budgets

91
Ce modèle d'économie de survie contraste radicalement avec le professionnalisme établi du circuit anglo-saxon du Lawn Bowls et de sa variante en salle, l'Indoor Bowls. La structuration y est beaucoup plus aboutie, calquée sur le modèle d'économie du spectacle sportif britannique (comme le snooker ou les fléchettes)

119
. Le World Bowls Tour (WBT), géré par la Professional Bowls Association depuis la fin des années 1990, organise des tournois majeurs télévisés en direct par les réseaux nationaux comme la BBC

119
. Le championnat du monde en salle (World Indoor Bowls Championships), qui se tient annuellement en janvier à Yarmouth au Potters Resorts, génère des audiences dépassant les 2,4 millions de téléspectateurs

119
. L'implication
massive de sponsors et d'opérateurs de tourisme permet d'offrir des bourses financières sans commune mesure avec la pétanque : le prize money total de l'événement frôle les 200 000 £ (Livres sterling), le vainqueur en simple (Open Singles) ou en simple féminin empochant directement un chèque de 50 000 £, tandis que les vainqueurs en paire se partagent 20 000 £

121
. Même les perdants des premiers tours (l'événement regroupant 32 joueurs, les 16 premiers du classement mondial entrant directement au second tour) touchent une compensation financière significative

121

Cette attractivité financière ne se limite pas à la Grande-Bretagne : les événements organisés sous l'égide de World Bowls et des fédérations nationales dans l'hémisphère sud déplacent des sommes colossales. Le championnat du monde sur herbe (World Bowls Championship), dont l'édition 2027 est programmée sur les prestigieux greens de Victoria Park à Leamington Spa en Angleterre, attend plus de 27 nations

119
. En Australie, la professionnalisation est totale : le tournoi annuel « Inland Petroleum City of Dubbo Fours » distribue 120 000 $ de prix pour un seul événement de quelques jours, tandis que le prestigieux « Australian Open » met en jeu un prize pool faramineux approchant les 350 000 $ australiens

125
. Ces chiffres illustrent la viabilité d'une industrie du sport de boules où les meilleurs joueurs du Commonwealth évoluent avec le statut de véritables professionnels du sport-spectacle.

## Conclusion

L'analyse de l'écosystème planétaire des sports de boules dévoile une dialectique fascinante entre l'attachement aux traditions vernaculaires et la rationalisation exigée par le sport moderne de haut niveau.
D'un côté, la conservation minutieuse des anomalies physiques des équipements – les asymétries et les pentes de la boule de fort en Anjou, le poids écrasant de la bourle nordique, ou l'ovale biaisé du lawn bowls britannique – garantit la sauvegarde des régionalismes et de l'identité de territoires spécifiques, offrant une alternative intellectuelle et lente à l'athlétisme moderne

28
De l'autre, l'expansion globale et standardisée de disciplines comme la pétanque, les bochas sud-américaines ou l'innovation du woodball asiatique, portées par l'émergence de nouvelles superpuissances (Thaïlande, Madagascar), témoigne d'un dynamisme géopolitique où l'hégémonie européenne n'est plus qu'un lointain souvenir

62
. Enfin, l'existence et
l'hyper-codification scientifique de la Boccia paralympique rappellent avec force que l'intelligence spatiale, géométrique et tactique demeure le dénominateur commun absolu de toutes ces disciplines

101
. Quelles que soient les tractations politiques de la FMBP auprès des instances olympiques, les jeux de boules s'affirment non pas comme de simples loisirs du passé, mais comme des sciences exactes de la précision, capables de transcender les frontières sociologiques, générationnelles, climatiques et physiques de l'humanité.

Sources des citations

1. TOP 15 des MEILLEURS JEUX de BOULES qui ont marqué L'HISTOIRE - la mariole, https://lamariole.com/blogs/petanque-du-21e-siecle/top-15-des-meilleurs-jeux-d e-boules-qui-ont-marque-lhistoire (https://lamariole.com/blogs/petanque-du-21e-siecle/top-15-des-meilleurs-jeux-de-boules-qui-ont-marque-lhistoire)
2. « LA BOULE LYONNAISE » - Ministère de la Culture, https://www.culture.gouv.fr/Media/Thematiques/Patrimoine-culturel-immateriel/Files/Fiches-inventaire-du-PCI/Le-jeu-de-la-boule-lyonnaise (https://www.culture.gouv.fr/Media/Thematiques/Patrimoine-culturel-immateriel/Files/Fiches-inventaire-du-PCI/Le-jeu-de-la-boule-lyonnaise)
3. Bochas y Bochazos - TestimoniosBA, https://www.testimoniosba.com/2022/01/28/bochas-y-bochazos/
4. Bochas, o el juego de la cautela - Pulpería Quilapán, https://pulperia.ar/bochas-o-el-juego-de-la-cautela/

5. Jeux de boules : le guide complet pour tout savoir sur le sujet - Lumios le jeu, https://www.lumios-le-jeu.fr/blogs/articles/jeux-de-boules
6. REGLEMENT OFFICIEL POUR LE SPORT DE JEU PROVENÇAL - Applicable sur l'ensemble des territoires des fédérations nationales, membres de la FIPJP, https://www.ffpjp.org/portail/images/2023/arbitrage/Reglement_Jeu_Proven%C3%A7al_2023.pdf (https://www.ffpjp.org/portail/images/2023/arbitrage/Reglement_Jeu_Proven%C3%A7al_2023.pdf)
7. Règlement du Jeu Provençal 2026 & Bases Point & Tir à la Longue - Pétanque, https://boule-petanque.fr/reglement-du-jeu-provencal
8. FÉDÉRATION FRANÇAISE DE PÉTANQUE ET JEU PROVENÇAL, https://www.ffpjp69.com/wp-content/uploads/2019/08/R%C3%A9glement-jeu-pr ovencal.pdf (https://www.ffpjp69.com/wp-content/uploads/2019/08/R%C3%A9glement-jeu-provencal.pdf)
9. Les différents jeux de boules à connaître - Blog Sport, Pétanque, Guides & Conseils, https://www.facileacomprendre.fr/divers-jeux-de-boules-a-connaitre/
10. https://www.boulipedia.com/jeu-provencal/regles#:~:text=Le%20cercle%20de%2 0lancement%20doit,un%20pas%20lors%20du%20lancer. (https://www.boulipedia.com/jeu-provencal/regles)
11. BDF49 La boule de fort - Wiki-Anjou, https://www.wiki-anjou.fr/index.php/BDF49_La_boule_de_fort
12. Les différents types de jeux de boules - La gazette de la pétanque, https://www.gazette-petanque.com/les-differents-types-jeux-de-boules/
13. Les règles de la pétanque avec Obut, https://www.obut.com/fr/content/92-les-regles-de-la-petanque
14. Jeu de Boules (Bocce) — Règles et Techniques - Bordeaux Games, https://bordeauxgames.com/regles/jeu-de-boules/
15. Règles du jeu – Pétanque, Boccia, Boule Lyonnaise & Jeu Provençal | pebou,
https://www.pebou.com/fr/rules/
16. Differences between bocce, pétanque and boccia: rules, surfaces and types of ball, https://petanca.cnsportstourism.com/en/boccia-vs-boccia-boccia/
17. reglement epreuve de tir de precision simplifie - Comité Départemental de Pétanque et Jeu Provençal, https://www.ffpjp-cd17.com/uploads/Educateurs/tirprecision.pdf
18. REGLEMENT EPREUVE DE TIR DE PRECISION SIMPLIFIE BENJAMINS - MINIMES -Pétanque et Jeu Provençal, https://www.petanque-regionsud-ffpjp.org/wp-content/uploads/2023/08/REGLEMENT-tir_simplifie_benjamins_minimes.pdf (https://www.petanque-regionsud-ffpjp.org/wp-content/uploads/2023/08/REGLEMENT-tir_simplifie_benjamins_minimes.pdf)
19. TOP 9 des différents Jeux de Boules (Bowling, Pétanque, Bocce, Boule L - la mariole,
https://lamariole.com/blogs/petanque-du-21e-siecle/top-des-differents-jeux-de-boules (https://lamariole.com/blogs/petanque-du-21e-siecle/top-des-differents-jeux-de-boules)
20. Boules Lyonnaises, https://bouleslyonnaises.lyonsportmetropole.org/
21. Sport-boules - Wikipédia, https://fr.wikipedia.org/wiki/Sport-boules
22. La Boule Lyonnaise : Le Jeu Traditionnel - la boule meaulnoise, https://la-boule-meaulnoise.blog4ever.com/la-boule-lyonnaise-le-jeu-traditionnel
23. Boule lyonnaise et pétanque, quelles différences ? - Petit Paumé, https://www.petitpaume.com/article/boule-lyonnaise-et-petanque-quelles-differ ences (https://www.petitpaume.com/article/boule-lyonnaise-et-petanque-quelles-differences)

24. Boules bretonnes – Silfiac, https://www.silfiac.fr/boules-bretonnes/
25. La boule de fort : une tradition ligérienne - destination-rivesduloirenanjou.fr, https://destination-rivesduloirenanjou.fr/destination-item/la-boule-de-fort-une-tradition-ligerienne/ (https://destination-rivesduloirenanjou.fr/destination-item/la-boule-de-fort-une-tradition-ligerienne/)
26. http://www.patrimoinevivantdelafrance.fr/index.php?mact=News,cntnt01,detail,0&cntnt01articleid=14&cntnt01returnid=24#:~:text=Elle%20mesure%20environ%2 012%2C5,la%20p%C3%A9tanque)%20p%C3%A8se%20300%20g. (http://www.patrimoinevivantdelafrance.fr/index.php?mact=News,cntnt01,detail,0&cntnt01articleid=14&cntnt01returnid=24)
27. d'où le nom du jeu - La Boule de fort en Anjou, http://bouledefort.free.fr/boule.htm
28. La boule de fort du Val de Loire - Fiche d'inventaire - Patrimoine Culturel Immatériel en France, https://www.pci-lab.fr/fiche-d-inventaire/fiche/120
29. Boule de fort - Wiki-Anjou, https://www.wiki-anjou.fr/index.php/Boule_de_fort
30. La boule de fort en Anjou - Patrimoine culturel immatériel, http://www.patrimoinevivantdelafrance.fr/index.php?mact=News,cntnt01,detail,0&cntnt01articleid=14&cntnt01returnid=24 (http://www.patrimoinevivantdelafrance.fr/index.php?mact=News,cntnt01,detail,0&cntnt01articleid=14&cntnt01returnid=24)
31. Boule de fort - Commune de Mazé-Milon, https://www.maze-milon.fr/boule-de-fort/
32. « BOULE DE FORT DE CHATEAUNEUF SUR SARTHE », https://www.culture.gouv.fr/Media/Thematiques/Patrimoine-culturel-immateriel/Files/Fiches-inventaire-du-PCI/La-boule-de-fort-de-Chateauneuf-sur-Sarthe (https://www.culture.gouv.fr/Media/Thematiques/Patrimoine-culturel-immateriel/Files/Fiches-inventaire-du-PCI/La-boule-de-fort-de-Chateauneuf-sur-Sarthe)
33. La boule de Fort - club Pétanque PETANQUE SAUJON VAUX - Clubeo, https://petanquesaujonvaux.clubeo.com/page/la-boule-de-fort.html
34. Jeu de boules de fort " La Bonne Tenue" - Savennières, https://www.savennieres.fr/associations/3270
35. Sports de boules - Bourle - sport.brussels, https://sport.brussels/disciplines/sports-de-boules/sports-de-boules-bourle/
36. Les estaminets et les jeux Les bourleux - Association HISTORIHEM, http://histori.hem.free.fr/estaminets_bourloire.html
37. la Bourle: jeu traditionnel - Les jeux picards, https://www.jeuxpicards.org/bourle.html
38. Bourle - Wikipédia, https://fr.wikipedia.org/wiki/Bourle
39. La bourle de Tourcoing - Fiche d'inventaire - Patrimoine Culturel Immatériel en France,
https://www.pci-lab.fr/en/fiche-d-inventaire/fiche/281-la-bourle-de-tourcoing
40. Association FEDERATION DES SOCIETES DE BOURLES DE TG à 59200
TOURCOING - SIREN 381 013 416 | L'Annuaire des Entreprises,
https://annuaire-entreprises.data.gouv.fr/entreprise/federation-des-societes-de-bourles-de-tg-381013416 (https://annuaire-entreprises.data.gouv.fr/entreprise/federation-des-societes-de-bourles-de-tg-381013416)
41. federation des societes de bourles du nord - L'Annuaire des Entreprises - Data gouv,
https://annuaire-entreprises.data.gouv.fr/entreprise/federation-des-societes-de-bourles-du-nord-832141832 (https://annuaire-entreprises.data.gouv.fr/entreprise/federation-des-societes-de-bourles-du-nord-832141832)
42. Fédération des Sociétés de Bourles du Nord, https://fedbourlenord.wordpress.com/
43. Federation Des Societes De Bourles De Wattrelos - CerfApp, https://www.cerfapp.fr/associations/hauts-de-france/nord/wattrelos/federation-d es-societes-de-bourles-de-wattrelos-w595029272 (https://www.cerfapp.fr/associations/hauts-de-france/nord/wattrelos/federation-des-societes-de-bourles-de-wattrelos-w595029272)
44. FEDERATION DES SOCIETES DE BOURLES DE WATTRELOS - Google Sites, https://sites.google.com/site/federationbourlewattrelos/
45. Boule bretonne du Morbihan - FALSAB, https://www.falsab.com/jeu/boule_bretonne_morbihan/
46. Principes et règles du jeu | boule-elvinoise,
https://www.boule-elvinoise.com/principes-et-regles-du-jeu
47. « Boule Bretonne des Côtes d'Armor », https://www.culture.gouv.fr/Media/Thematiques/Patrimoine-culturel-immateriel/Files/Fiches-inventaire-du-PCI/Boule-bretonne-des-Cotes-d-Armor (https://www.culture.gouv.fr/Media/Thematiques/Patrimoine-culturel-immateriel/Files/Fiches-inventaire-du-PCI/Boule-bretonne-des-Cotes-d-Armor)
48. Règlement FNSMR Boules Bretonnes, https://bretagne.sportrural.fr/wp-content/uploads/2023/03/Reglement-FNSMR-B oules-Bretonnes.pdf (https://bretagne.sportrural.fr/wp-content/uploads/2023/03/Reglement-FNSMR-Boules-Bretonnes.pdf)
49. « La Boule Bretonne à un plomb », https://www.culture.gouv.fr/Media/Thematiques/Patrimoine-culturel-immateriel/Files/Fiches-inventaire-du-PCI/Boule-bretonne-a-un-plomb (https://www.culture.gouv.fr/Media/Thematiques/Patrimoine-culturel-immateriel/Files/Fiches-inventaire-du-PCI/Boule-bretonne-a-un-plomb)
50. MAINE-ET-LOIRE — Boules (pétanque, boules) - Assoce, https://assoce.fr/departement/49/MAINE-ET-LOIRE/categorie/11035
51. Variations of Petanque - ActiveSG Circle, https://www.activesgcircle.gov.sg/learn/petanque/variations-of-petanque
52. What is lawn bowls, https://www.fflb.fr/en/what-is-lawn-bowls/
53. What's the difference between boules, pétanque, lawn bowls and bocce ball? -Packaworld,
https://www.packaworld.com/news-blog/whats-the-difference-between-boules-petanque-lawn-bowls-and-bocce-ball (https://www.packaworld.com/news-blog/whats-the-difference-between-boules-petanque-lawn-bowls-and-bocce-ball)
54. Crown Green Vs Flat Green - The Key Differences - Bowls.co.uk, https://www.bowls.co.uk/crown-green/crown-green-vs-flat-green
55. Bowls Selection | Crown Green Bowler,
https://www.crowngreenbowler.co.uk/bowls-selection
56. Discover Bowls - British Crown Green Bowling Association, https://www.bcgba.org.uk/bowler-information/discover-bowls/
57. The difference between Pétanque and Boules - Big Game Hunters, https://www.biggamehunters.co.uk/pages/petanque-vs-boules-what-is-the-diffe rence (https://www.biggamehunters.co.uk/pages/petanque-vs-boules-what-is-the-difference)
58. Flat Green vs Crown Green: The Key Differences - Bowls World, https://www.bowlsworld.co.uk/blogs/lawn-bowls/flat-green-vs-crown-green-the -key-differences (https://www.bowlsworld.co.uk/blogs/lawn-bowls/flat-green-vs-crown-green-the-key-differences)
59. Bowls | Lawn Bowling, Indoor Carpet Bowling & Outdoor Flat Green Bowling |
Britannica, https://www.britannica.com/sports/bowls
60. Frequently Asked Questions - Taylor Bowls, https://www.taylorbowls.com/faqs
61. reglamento de juego del deporte de bochas en canchas, estilo sudamericano, http://www.argentinabochas.com.ar/images/reglamentos/Reglamento%20Sudam ericano%20-%20Argentina.pdf (http://www.argentinabochas.com.ar/images/reglamentos/Reglamento%20Sudamericano%20-%20Argentina.pdf)
62. Reglamento Bochas Estilo Sudamericano, http://bochascba.com.ar/reglamento-estilo-sudamericano

63. Institucional - Federación Uruguaya de Bochas, https://bochasuruguay.com.uy/institucional/
64. Fédération mondiale de boules et de pétanque - Wikipédia, https://fr.wikipedia.org/wiki/F%C3%A9d%C3%A9ration_mondiale_de_boules_et_de_p%C3%A9tanque (https://fr.wikipedia.org/wiki/F%C3%A9d%C3%A9ration_mondiale_de_boules_et_de_p%C3%A9tanque)
65. Las Bochas en Uruguay: un deporte marcado por la tradición, identidad e inclusión social,
https://grupormultimedio.com/las-bochas-en-uruguay-un-deporte-marcado-por-la-tradicion-identidad-e-inclusion-social-id194026/ (https://grupormultimedio.com/las-bochas-en-uruguay-un-deporte-marcado-por-la-tradicion-identidad-e-inclusion-social-id194026/)
66. Reglamento del Juego de Bochas - Infosport Saladillo, https://www.infosportsaladillo.com.ar/deporte-nota/1008
67. Historia de las Bolas Criollas en Venezuela | PDF - Scribd,
https://es.scribd.com/document/405026400/Historia-de-Las-Bolas-Criollas-en-V enezuela (https://es.scribd.com/document/405026400/Historia-de-Las-Bolas-Criollas-en-Venezuela)
68. REGLAMENTO COMBINADO,
http://www.argentinabochas.com.ar/images/reglamentos/Reglamento%20combin ado.pdf (http://www.argentinabochas.com.ar/images/reglamentos/Reglamento%20combinado.pdf)
69. La historia de las bochas y el Día del Bochófilo - Puntal Villa María, https://www.puntalvillamaria.com.ar/domingo/la-historia-las-bochas-y-el-dia-del-bochofilo-n120363 (https://www.puntalvillamaria.com.ar/domingo/la-historia-las-bochas-y-el-dia-del-bochofilo-n120363)
70. BOLAS CRIOLLAS - JUEGO VENEZOLANO - Hive.blog, https://hive.blog/hive-148441/@suralla/bolas-criollas-juego-venezolano
71. Bolas criollas: entérate en qué consiste este deporte - Venezolanos Ilustres, https://venezolanosilustres.com/secciones/salud-y-deportes/bolas-criollas-deporte-venezolano/ (https://venezolanosilustres.com/secciones/salud-y-deportes/bolas-criollas-deporte-venezolano/)
72. Reglamento de Bolas Criollas 2025 | PDF | Deporte del atletismo - Scribd,
https://es.scribd.com/document/545168881/REGLAMENTO-OFICIAL-DE-JUEGO-DE-BOLAS-CRIOLLAS (https://es.scribd.com/document/545168881/REGLAMENTO-OFICIAL-DE-JUEGO-DE-BOLAS-CRIOLLAS)
73. Reglamento de Juego de Bolas Criollas | PDF | Árbitro | Deporte del atletismo -
Scribd,
https://es.scribd.com/document/405028449/Reglamento-de-Juego-de-Bolas-Cri ollas-2018-o-k (https://es.scribd.com/document/405028449/Reglamento-de-Juego-de-Bolas-Criollas-2018-o-k)
74. Reglamento de Bolas Criollas 2025 | PDF | Deporte del atletismo | Árbitro - Scribd,
https://es.scribd.com/document/625012092/REGLAMENTO-DE-JUEGO-BOLAS-C RIOLLAS (https://es.scribd.com/document/625012092/REGLAMENTO-DE-JUEGO-BOLAS-CRIOLLAS)
75. Bolas criollas - Wikipedia, https://en.wikipedia.org/wiki/Bolas_criollas
76. liga interclubes de bolas criollas - Libocrintc, https://www.libocrintc.com/libo.pdf
77. Set (8) Bolas Criollas. Bochas Petanca - Pesadas. Venezuela | MercadoLibre,
https://www.mercadolibre.cl/set-8-bolas-criollas-bochas-petanca--pesadas-venezuela/up/MLCU110118728 (https://www.mercadolibre.cl/set-8-bolas-criollas-bochas-petanca--pesadas-venezuela/up/MLCU110118728)
78. Bolas Criollas - EcuRed, https://www.ecured.cu/Bolas_Criollas
79. Propuesta metodológica para el dominio de la técnica en el lanzamiento de la Bola Criolla en el arrime del equipo municipal de Arroyo Naranjo - EFDeportes, https://www.efdeportes.com/efd177/la-tecnica-en-el-lanzamiento-de-la-bola-cri olla.htm (https://www.efdeportes.com/efd177/la-tecnica-en-el-lanzamiento-de-la-bola-criolla.htm)

80. Reglamento Oficial de Bolas Criollas 2023 | PDF | Documento de identidad |
Árbitro - Scribd,
https://es.scribd.com/document/729872943/REGLAMENTO-BOLAS-CRIOLLAS-A N-O-2017 (https://es.scribd.com/document/729872943/REGLAMENTO-BOLAS-CRIOLLAS-AN-O-2017)
81. Jogo da malha – Wikipédia, a enciclopédia livre, https://pt.wikipedia.org/wiki/Jogo_da_malha
82. Regras do Jogo da Malha - Freguesia de Degolados, https://www.degolados.pt/jregras-do-jogo-da-malha/
83. ENA - Jogo da Malha - CENA, https://gana.blogs.sapo.pt/40487.html
84. Woodball Rules / Equipment, http://uswoodball.com/rules-ch2.htm
85. About Woodball - Topend Sports, https://www.topendsports.com/sport/list/woodball.htm
86. Introduction to Woodball Sport | PDF | Golf Course | Entertainment - Scribd,
https://www.scribd.com/presentation/615090584/Woodball-Ppt-r-r
87. Chapter One: Beach Woodball Course, https://www.iwbf-woodball.org/imagess/1021051115_1331375C5p3.pdf
88. Rules of Woodball,
http://www.iwbf-woodball.org/imagess/1021050620_0828E8213p3.pdf
89. Confédération mondiale des sports de boules (CMSB) - Union of International Associations, https://uia.org/s/or/en/1100052062
90. LA FRANC Boules de Pétanque - légendaire histoire (1950) - petanque spot, https://petanque-spot.com/la-franc-boules-de-petanque-competition-histoire/
91. Pétanque : Madagascar et la Thaïlande défiés par les meilleures formations françaises à l'International Triplette d'Objat - Boulistenaute, https://www.boulistenaute.com/les-actualites-de-la-petanque-et-du-monde-bouliste/i/82029399/petanque-madagascar-et-la-thailande-defies-par-les-meilleur es-formations-francaises-a-l-international-triplette-d-objat (https://www.boulistenaute.com/les-actualites-de-la-petanque-et-du-monde-bouliste/i/82029399/petanque-madagascar-et-la-thailande-defies-par-les-meilleures-form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)
92. Pétanque: Madagascar remporte le championnat du monde, https://www.madamaxi.com/actualites-madagascar-petanque-madagascar-rem porte-le-championnat-du-monde-actualites-1436.html (https://www.madamaxi.com/actualites-madagascar-petanque-madagascar-remporte-le-championnat-du-monde-actualites-1436.html)
93. Pétanque : Madagascar créé la surprise en vue des Mondiaux ! - SPORTMAG, https://www.sportmag.fr/petanque-madagascar-cree-la-surprise-en-vue-des-mondiaux/ (https://www.sportmag.fr/petanque-madagascar-cree-la-surprise-en-vue-des-mondiaux/)
94. Championnats du Monde de pétanque I Madagascar champion 2024 de tir de précision -,
https://alwatwan.net/sports/championnats-du-monde-de-p%C3%A9tanque-i-ma dagascar-champion-2024-de-tir-de-pr%C3%A9cision.html (https://alwatwan.net/sports/championnats-du-monde-de-p%C3%A9tanque-i-madagascar-champion-2024-de-tir-de-pr%C3%A9cision.html)
95. Pétanque - Mondiaux Jeunes : Madagascar champion du monde en doublette mixte,
https://midi-madagasikara.mg/petanque-mondiaux-jeunes-madagascar-champion-du-monde-en-doublette-mixte/ (https://midi-madagasikara.mg/petanque-mondiaux-jeunes-madagascar-champion-du-monde-en-doublette-mixte/)
96. Boccia - Wikipédia, https://fr.wikipedia.org/wiki/Boccia
97. Boccia | Handisport.org, https://www.handisport.org/les-29-sports/boccia/
98. Boccia - Paralympics Australia, https://www.paralympic.org.au/sport/boccia/
99. Boccia New Standard - Handi Life Sport, https://handilifesport.com/product/boccia-new-standard/
100. Short boccia rules - Bashto Sports, https://www.bashtosports.com/index.php/en/about-boccia/short-boccia-rules
101. Sport Equipment - World Boccia, https://www.worldboccia.com/about-boccia/sport-equipment/
102. Competition Rules - Boccia News, https://boccianews.com/wp-content/uploads/2016/11/draft-working-copy_format ted.pdf (https://boccianews.com/wp-content/uploads/2016/11/draft-working-copy_formatted.pdf)
103. sports / boccia rules - ISF Inclusive Games 2019, https://isfinclusivegames2019.dge.mec.pt/boccia.htm
104. BOCCIA – CDH 80 - CD Handisport Somme, https://handisport-somme.org/sport/boccia/
105. https://generation2024.franceolympique.com/sites/default/files/2023-10/Paris2 024-Fiche%20Pedagogique%20Boccia.pdf (https://generation2024.franceolympique.com/sites/default/files/2023-10/Paris2024-Fiche%20Pedagogique%20Boccia.pdf)
106. CLASSIFICATION - Commission fédérale de la Boccia - Handisport.org, https://boccia.handisport.org/classification/
107. Boccia - Comité paralympique canadien, https://paralympique.ca/sport/boccia/
108. Boccia - Comité Départemental Handisport de Seine Saint-Denis, https://www.handisport93.fr/sport/boccia/
109. Historique - F.I.P.J.P, https://www.fipjp.org/index.php/fr/fipjp/historique
110. History - F.I.P.J.P, https://fipjp.org/index.php/en/f-i-p-j-p/history
111. Communiqué de la WPBF (FMBP), https://wpbf-fmbp.org/index.php/fr/?view=article&id=90:communique-de-la-wpbf-fmbp&catid=10 (https://wpbf-fmbp.org/index.php/fr/?view=article&id=90:communique-de-la-wpbf-fmbp&catid=10)
112. Confédération mondiale des sports de boules - Wikipédia, https://fr.wikipedia.org/wiki/Conf%C3%A9d%C3%A9ration_mondiale_des_sports_de_boules (https://fr.wikipedia.org/wiki/Conf%C3%A9d%C3%A9ration_mondiale_des_sports_de_boules)
113. Claude Azéma: “Pétanque is taken less seriously in France than abroad” -YouTube, https://www.youtube.com/watch?v=pdbfdRGoRP4
114. IWGA General Assembly in Madrid - WPBF, https://wpbf-fmbp.org/index.php/en/wpbf-en/about-the-wpbf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 (https://wpbf-fmbp.org/index.php/en/wpbf-en/about-the-wpbf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)
115. Qui sommes-nous ? - WPBF, https://wpbf-fmbp.org/index.php/fr/wpbf/a-propos-de-la-wpbf
116. WPBF - Federation Mondiale de Boules et de Petanque - Olympics.com, https://www.olympics.com/cio/federation-mondiale-de-boules-et-de-petanque
117. Présentation - Masters de Pétanque, https://www.mastersdepetanque.fr/presentation/
118. Ce que le salaire d'un bouliste professionnel ne dit pas : primes, contrats et revenus cachés - - Orientation Formation, https://www.orientation-formation.org/ce-que-le-salaire-dun-bouliste-professionnel-ne-dit-pas-primes-contrats-et-revenus-caches/ (https://www.orientation-formation.org/ce-que-le-salaire-dun-bouliste-professionnel-ne-dit-pas-primes-contrats-et-revenus-caches/)
119. World lawn and indoor bowls events - Wikipedia, https://en.wikipedia.org/wiki/World_lawn_and_indoor_bowls_events

120. World Bowls Tour | Supporting Professional Indoor Bowls,
https://theworldbowlstour.org/
121. World Indoor Bowls Championships - Grokipedia, https://grokipedia.com/page/World_Indoor_Bowls_Championships
122. World Indoor Bowls Championships prize money: How much does the winner get for BBC event? - The Mirror, https://www.mirror.co.uk/sport/other-sports/bowls-championship-bbc-prize-mo ney-36604303 (https://www.mirror.co.uk/sport/other-sports/bowls-championship-bbc-prize-money-36604303)
123. 2027 World Bowls Championship, https://www.bowlsengland.com/world-bowls-championships-2027/
124. 2027 World Bowls Championship, https://www.worldbowls.com/2027-world-bowls-championship/
125. Prize money - Australian Open - Bowls Australia, https://australianopen.bowls.com.au/prize-money/
126. Richest Fours event in the World - World Bowls Series, https://worldbowlsseries.com/richest-fours-event-in-the-world/
