guiraudjb/Arducible_Fanny_Petanque_World_Tour/assets/Images/BackgroundWorldTourHardcore/004_armenie.png

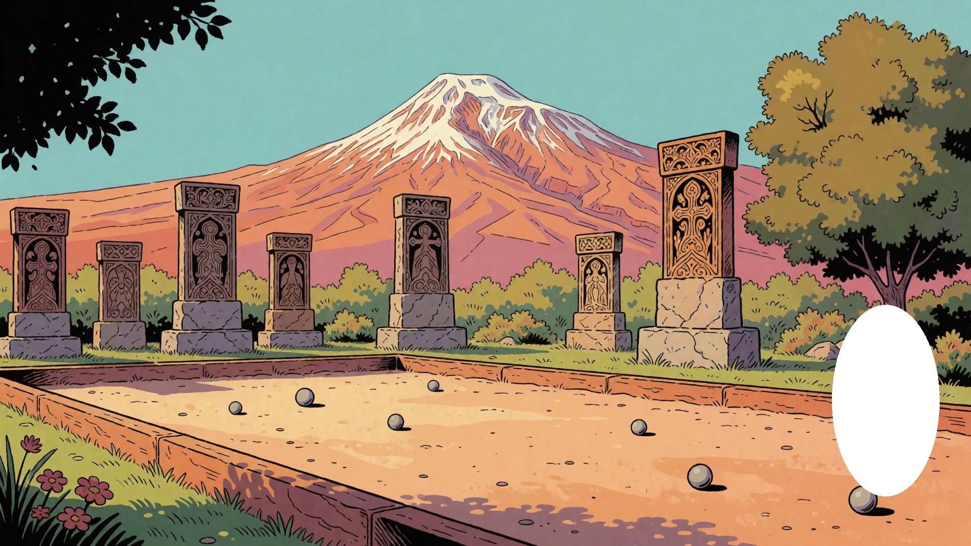
assets/Images/BackgroundWorldTourHardcore/004_armenie.png
