guiraudjb/Arducible_Fanny_Petanque_World_Tour/assets/Images/BackgroundWorldTourHardcore/008_danemark.png

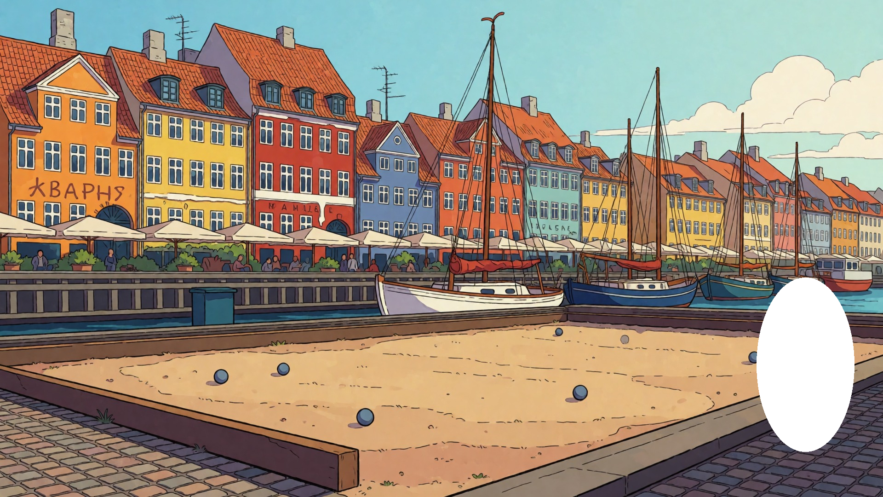
assets/Images/BackgroundWorldTourHardcore/008_danemark.png
