guiraudjb/Arducible_Fanny_Petanque_World_Tour/assets/Images/BackgroundWorldTourHardcore/013_france.png

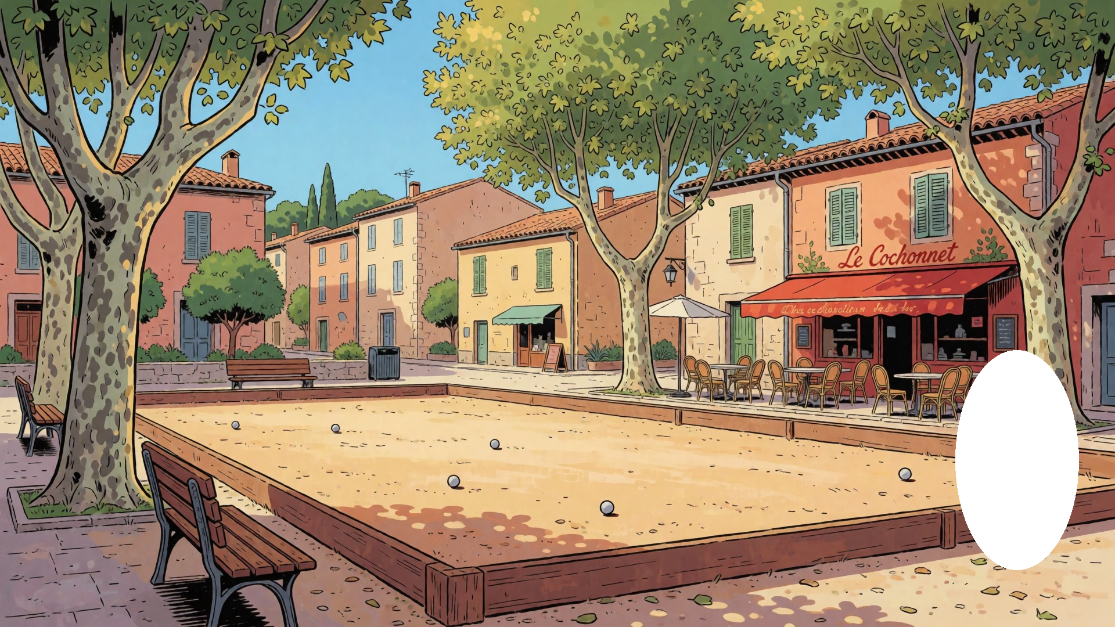
assets/Images/BackgroundWorldTourHardcore/013_france.png
