guiraudjb/Arducible_Fanny_Petanque_World_Tour/assets/Images/BackgroundWorldTourHardcore/015_hongrie.png

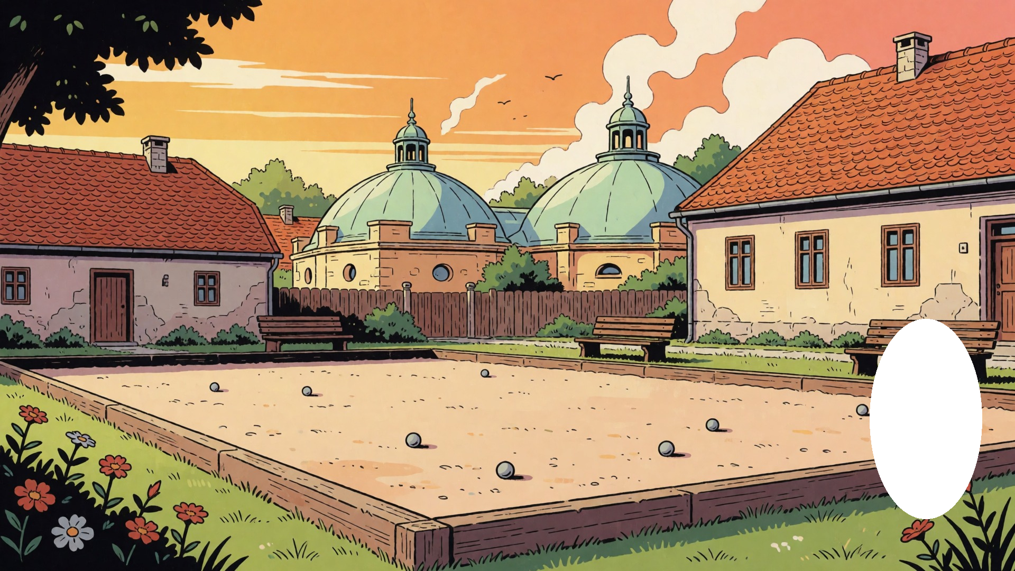
assets/Images/BackgroundWorldTourHardcore/015_hongrie.png
