guiraudjb/Arducible_Fanny_Petanque_World_Tour/assets/Images/BackgroundWorldTourHardcore/019_lettonie.png

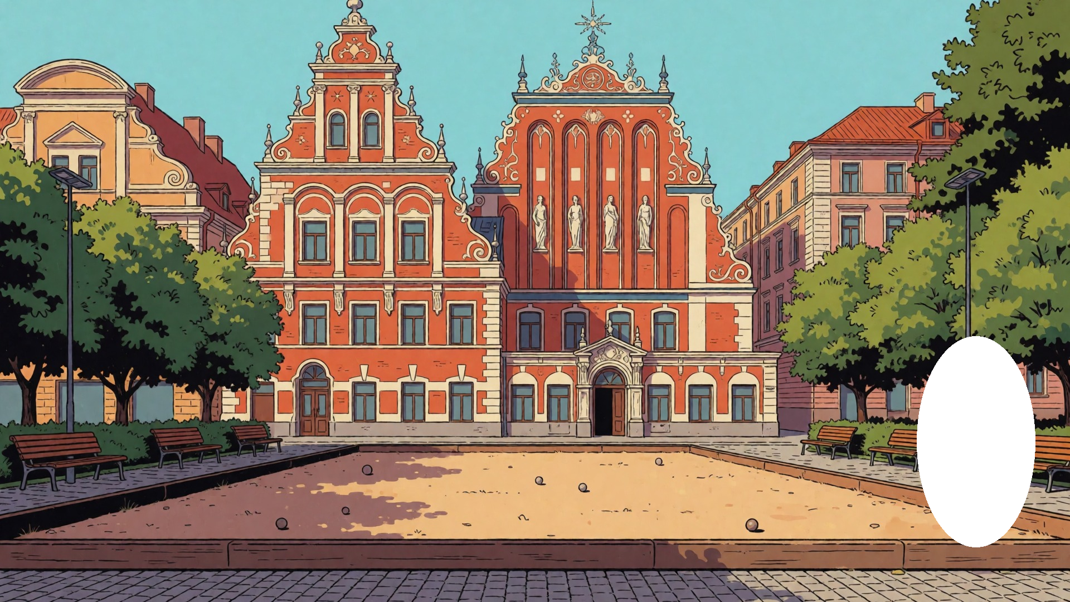
assets/Images/BackgroundWorldTourHardcore/019_lettonie.png
