guiraudjb/Arducible_Fanny_Petanque_World_Tour/assets/Images/BackgroundWorldTourHardcore/020_lituanie.png

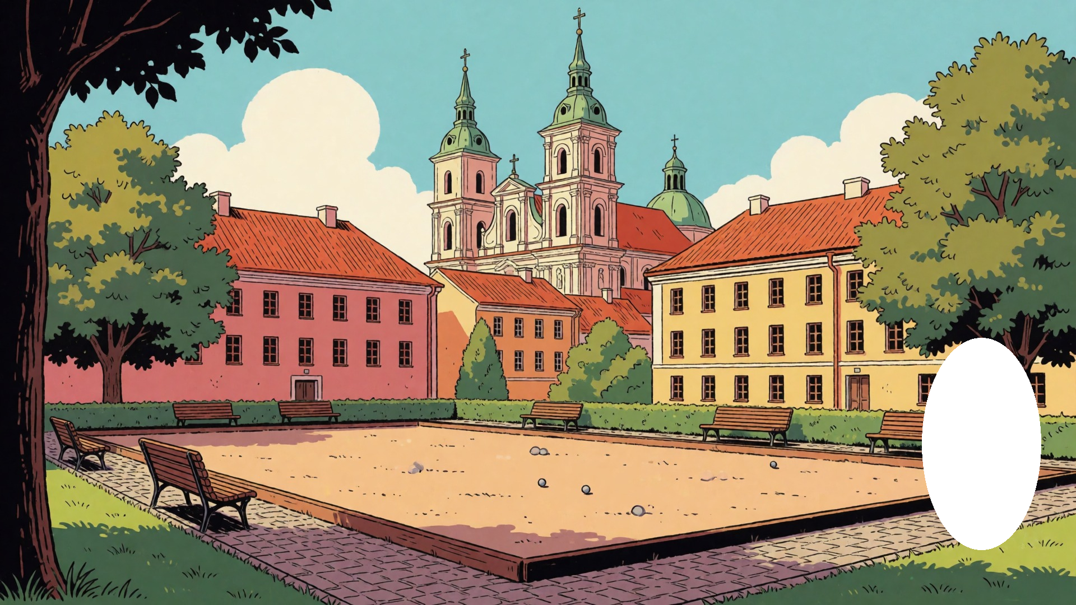
assets/Images/BackgroundWorldTourHardcore/020_lituanie.png
