guiraudjb/Arducible_Fanny_Petanque_World_Tour/assets/Images/BackgroundWorldTourHardcore/023_norvege.png

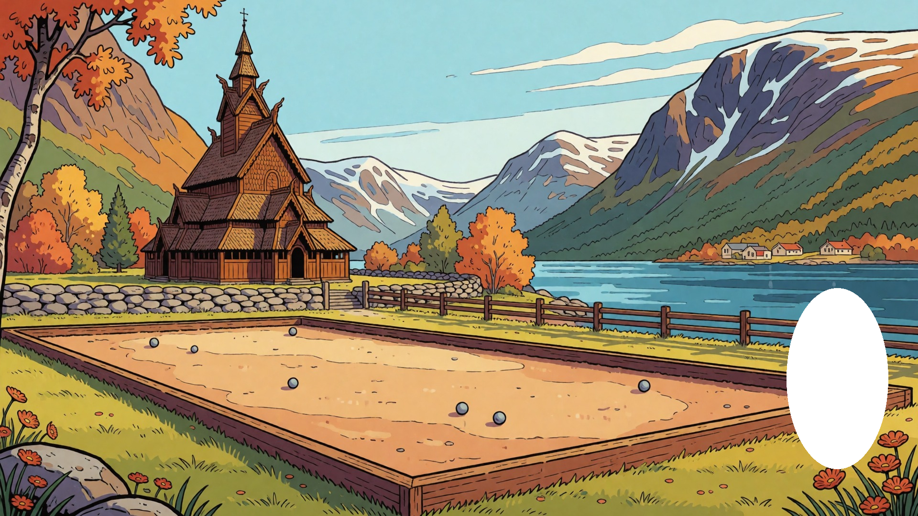
assets/Images/BackgroundWorldTourHardcore/023_norvege.png
