guiraudjb/Arducible_Fanny_Petanque_World_Tour/assets/Images/BackgroundWorldTourHardcore/024_pays_bas.png

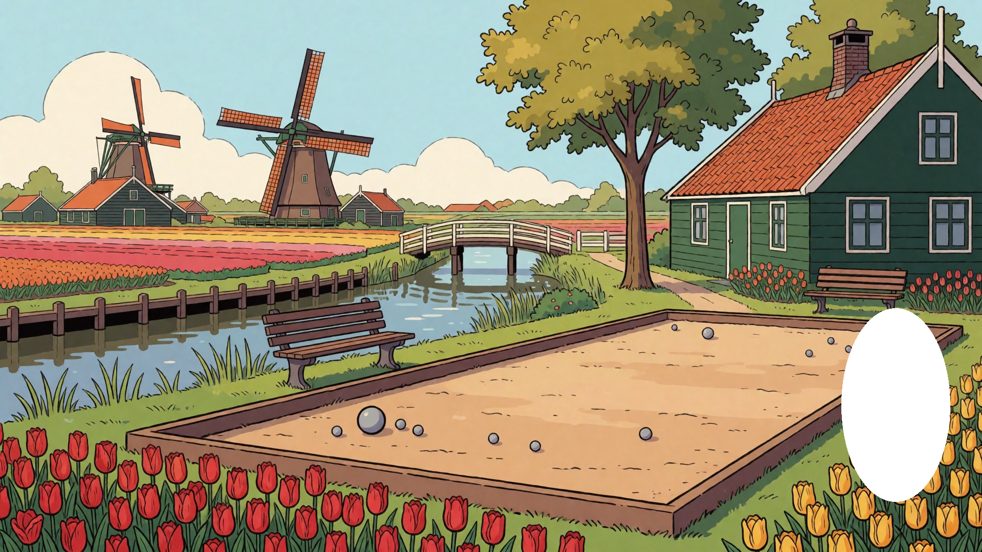
assets/Images/BackgroundWorldTourHardcore/024_pays_bas.png
