guiraudjb/Arducible_Fanny_Petanque_World_Tour/assets/Images/BackgroundWorldTourHardcore/026_pologne.png

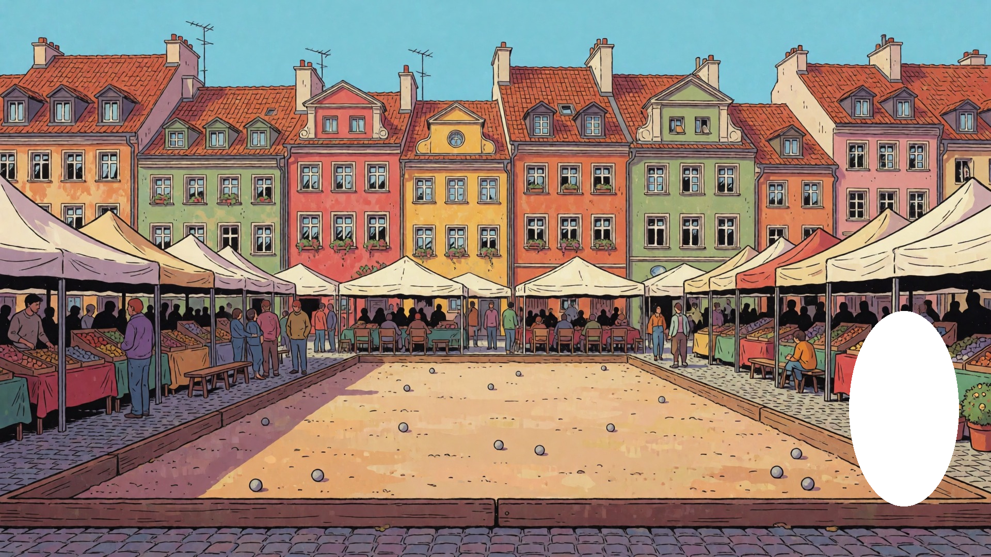
assets/Images/BackgroundWorldTourHardcore/026_pologne.png
