guiraudjb/Arducible_Fanny_Petanque_World_Tour/assets/Images/BackgroundWorldTourHardcore/031_serbie.png

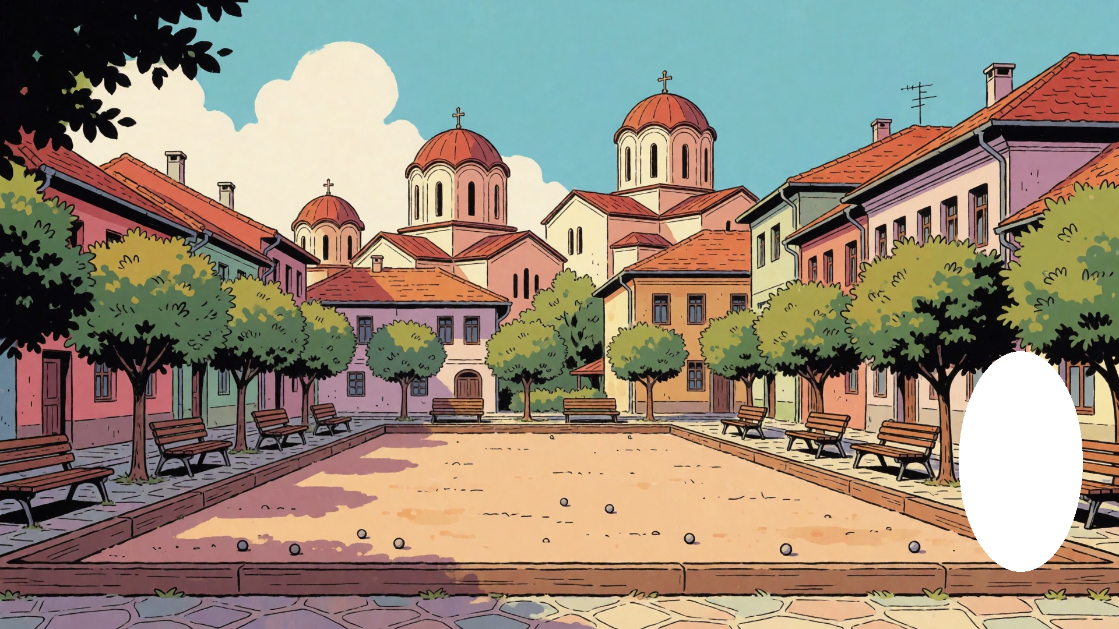
assets/Images/BackgroundWorldTourHardcore/031_serbie.png
