guiraudjb/Arducible_Fanny_Petanque_World_Tour/assets/Images/BackgroundWorldTourHardcore/047_egypte.png

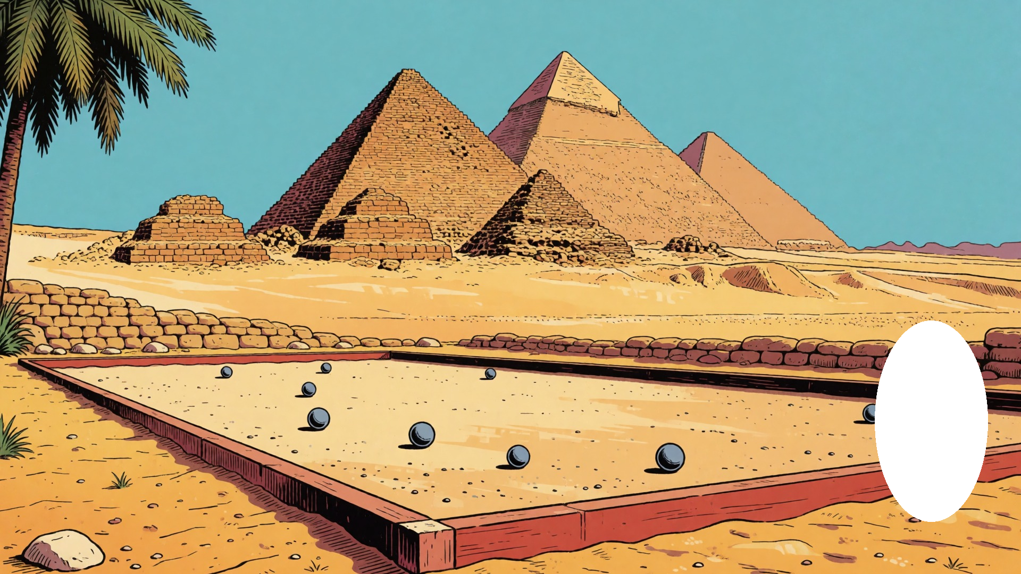
assets/Images/BackgroundWorldTourHardcore/047_egypte.png
