guiraudjb/Arducible_Fanny_Petanque_World_Tour/assets/Images/BackgroundWorldTourHardcore/058_republique_centrafricaine.png

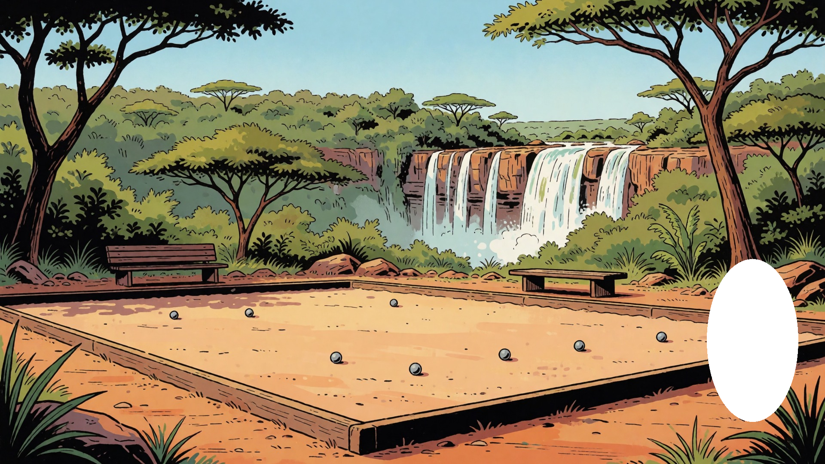
assets/Images/BackgroundWorldTourHardcore/058_republique_centrafricaine.png
