guiraudjb/Arducible_Fanny_Petanque_World_Tour/assets/Images/BackgroundWorldTourHardcore/059_republique_democratique_du_congo.png

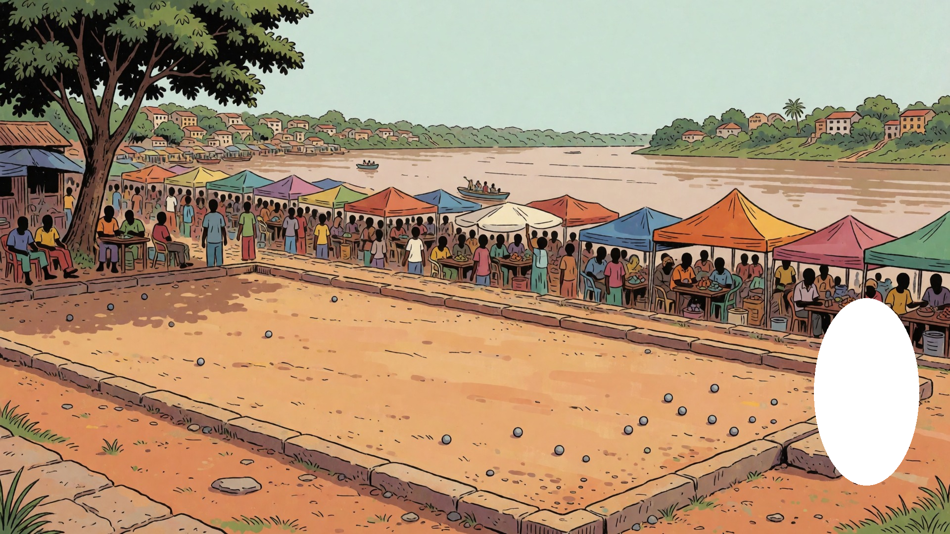
assets/Images/BackgroundWorldTourHardcore/059_republique_democratique_du_congo.png
