guiraudjb/Arducible_Fanny_Petanque_World_Tour/assets/Images/BackgroundWorldTourHardcore/066_afghanistan.png

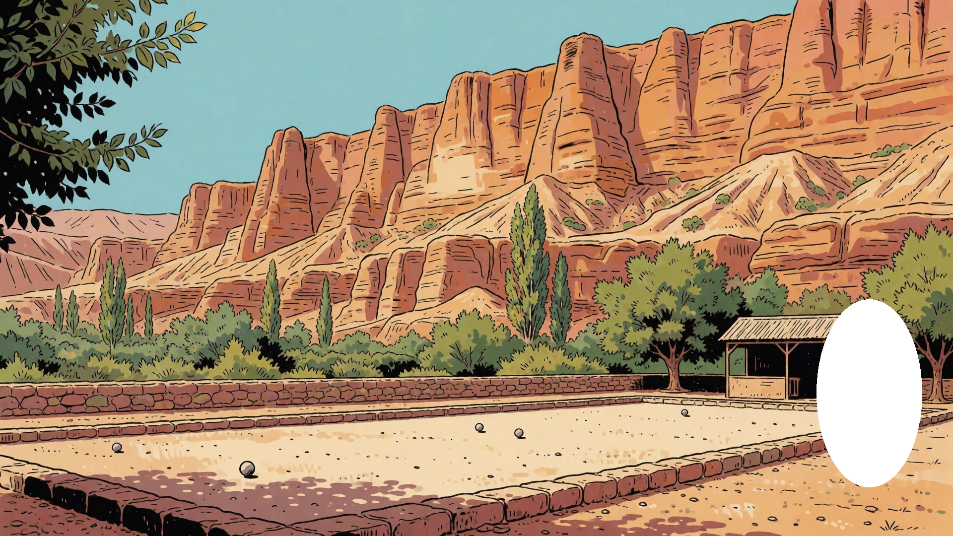
assets/Images/BackgroundWorldTourHardcore/066_afghanistan.png
