guiraudjb/Arducible_Fanny_Petanque_World_Tour/assets/Images/BackgroundWorldTourHardcore/077_kirghizistan.png

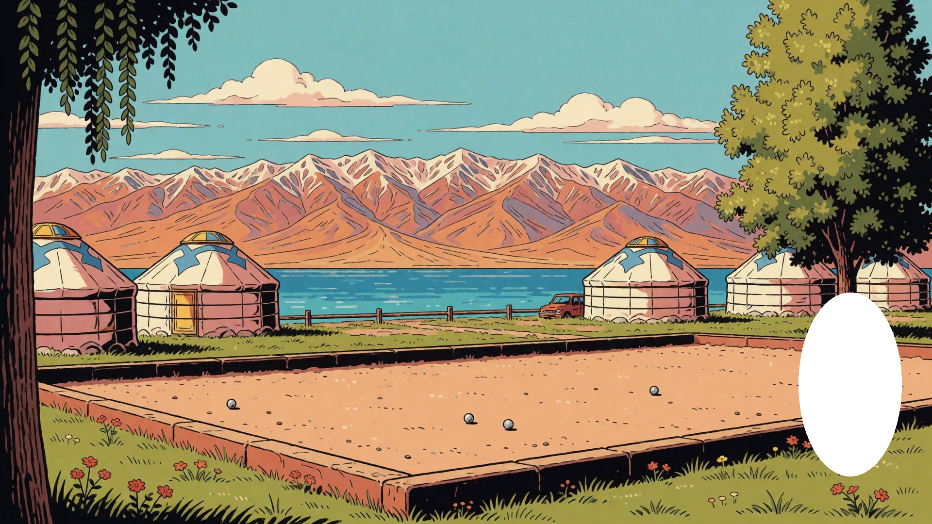
assets/Images/BackgroundWorldTourHardcore/077_kirghizistan.png
