guiraudjb/Arducible_Fanny_Petanque_World_Tour/assets/Images/BackgroundWorldTourHardcore/079_malaisie.png

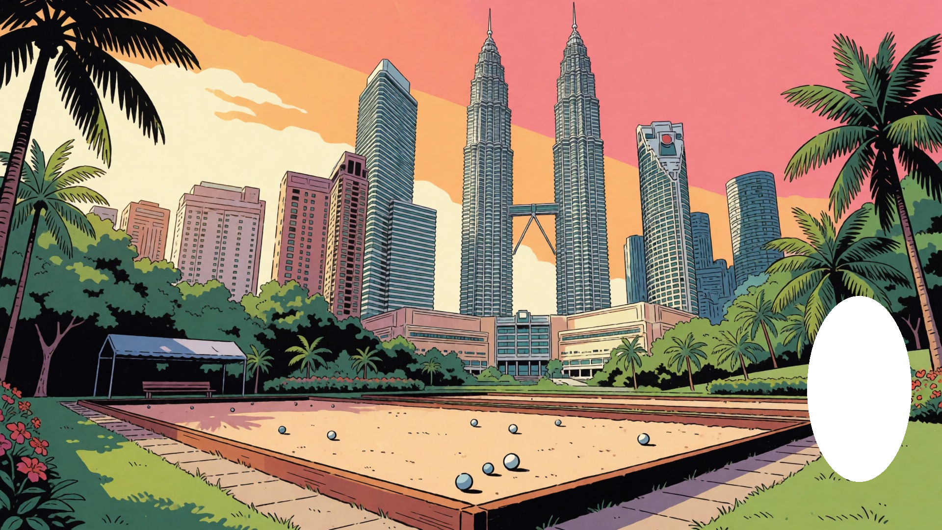
assets/Images/BackgroundWorldTourHardcore/079_malaisie.png
