guiraudjb/Arducible_Fanny_Petanque_World_Tour/assets/Images/BackgroundWorldTourHardcore/092_canada.png

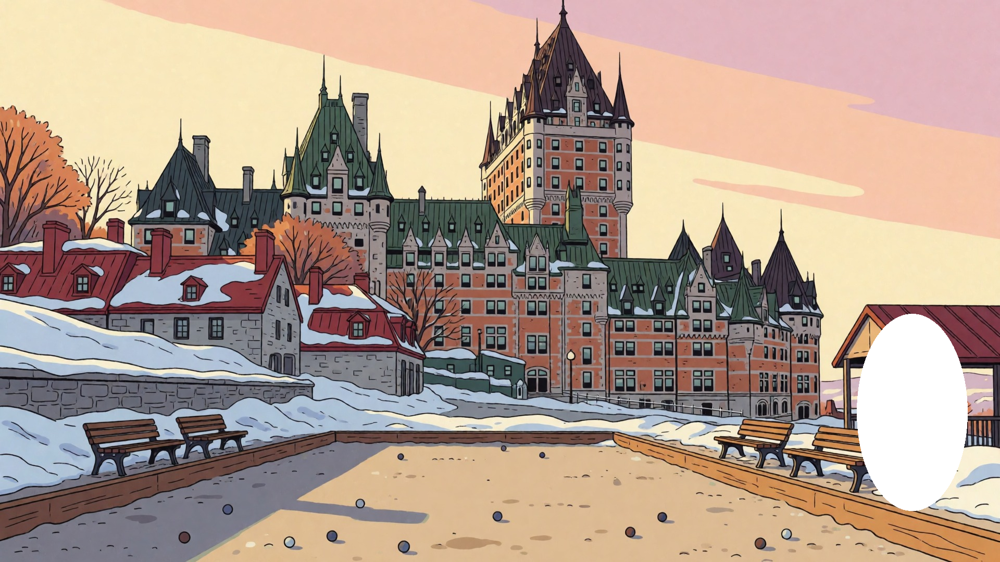
assets/Images/BackgroundWorldTourHardcore/092_canada.png
