guiraudjb/Arducible_Fanny_Petanque_World_Tour/assets/Images/BackgroundWorldTourHardcore/094_colombie.png

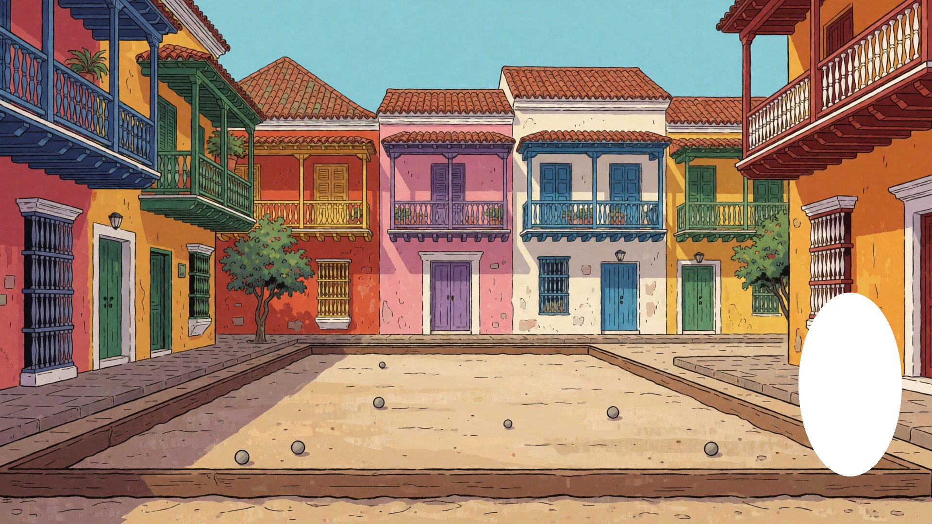
assets/Images/BackgroundWorldTourHardcore/094_colombie.png
