guiraudjb/Arducible_Fanny_Petanque_World_Tour/assets/Images/BackgroundWorldTourHardcore/097_equateur.png

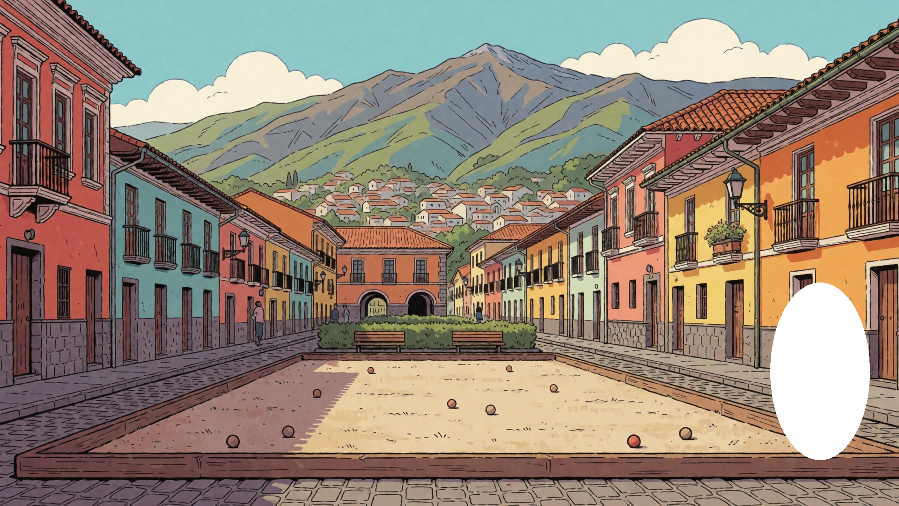
assets/Images/BackgroundWorldTourHardcore/097_equateur.png
