guiraudjb/Arducible_Fanny_Petanque_World_Tour/assets/Images/BackgroundWorldTourHardcore/100_haiti.png

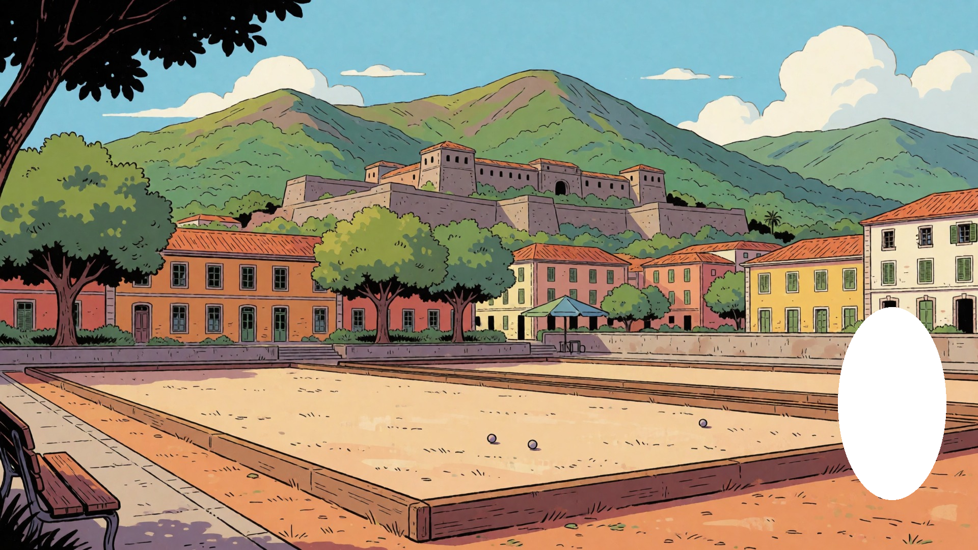
assets/Images/BackgroundWorldTourHardcore/100_haiti.png
