guiraudjb/Arducible_Fanny_Petanque_World_Tour/assets/Images/BackgroundWorldTourHardcore/101_mexique.png

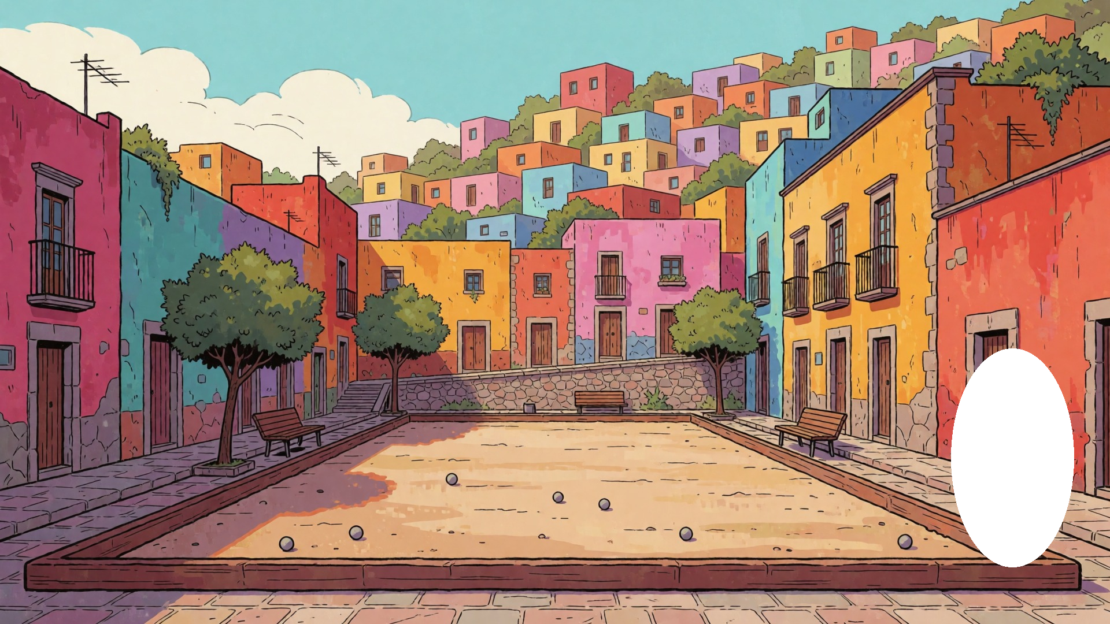
assets/Images/BackgroundWorldTourHardcore/101_mexique.png
