guiraudjb/Arducible_Fanny_Petanque_World_Tour/assets/Images/BackgroundWorldTourHardcore/104_republique_dominicaine.png

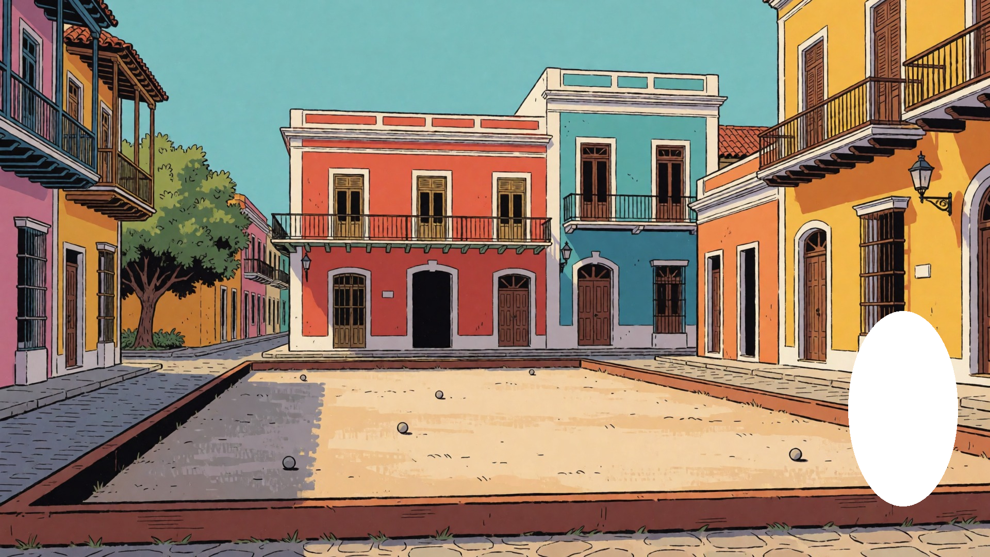
assets/Images/BackgroundWorldTourHardcore/104_republique_dominicaine.png
