guiraudjb/Arducible_Fanny_Petanque_World_Tour/assets/Images/CountryMapsWorldTour/004_armenie.png

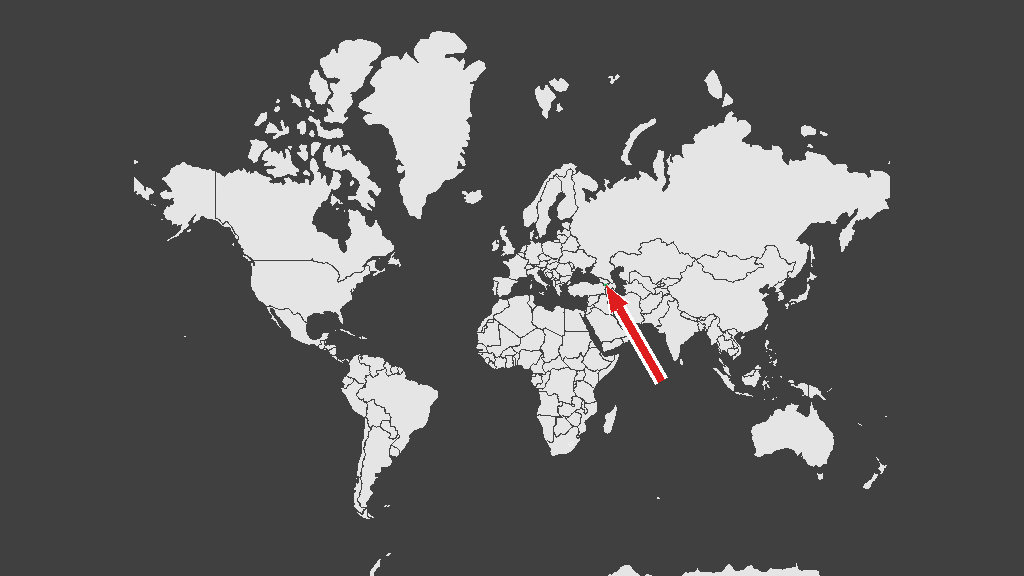
assets/Images/CountryMapsWorldTour/004_armenie.png
