guiraudjb/Arducible_Fanny_Petanque_World_Tour/assets/Images/FannyWorldTour/001_allemagne.png

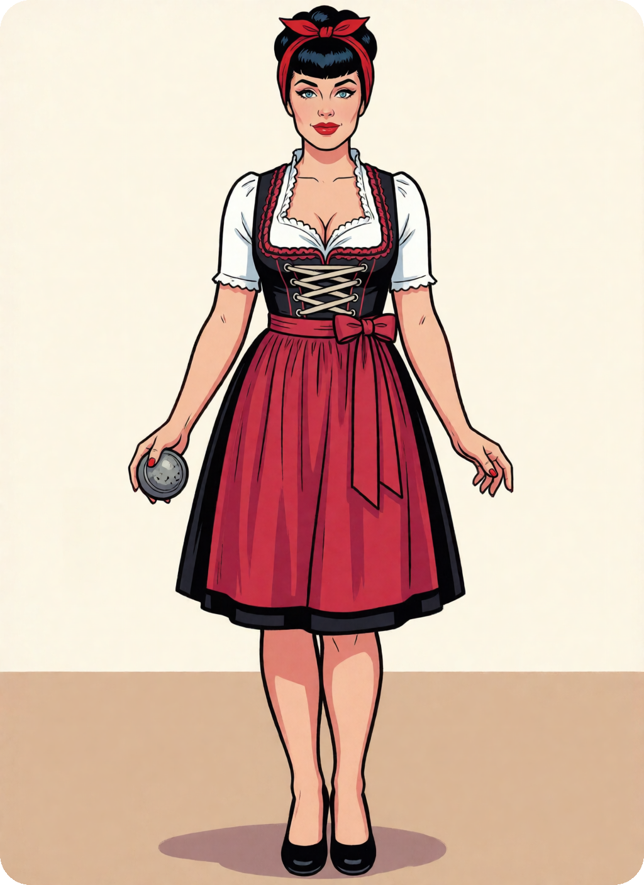
assets/Images/FannyWorldTour/001_allemagne.png
