guiraudjb/Arducible_Fanny_Petanque_World_Tour/assets/Images/FannyWorldTour/002_andorre.png

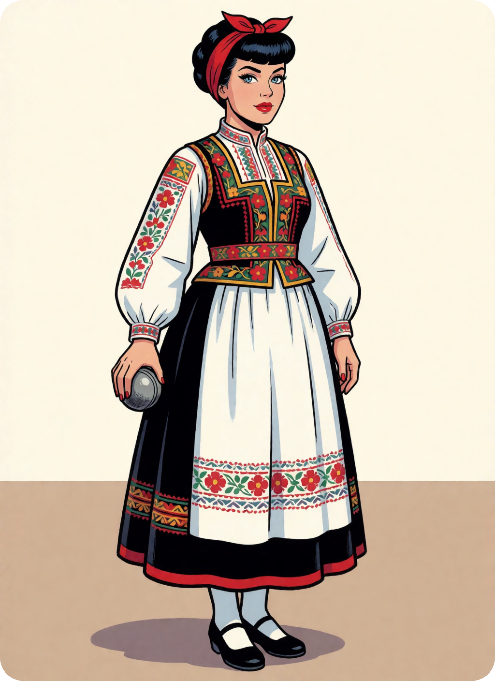
assets/Images/FannyWorldTour/002_andorre.png
