guiraudjb/Arducible_Fanny_Petanque_World_Tour/assets/Images/FannyWorldTour/003_angleterre.png

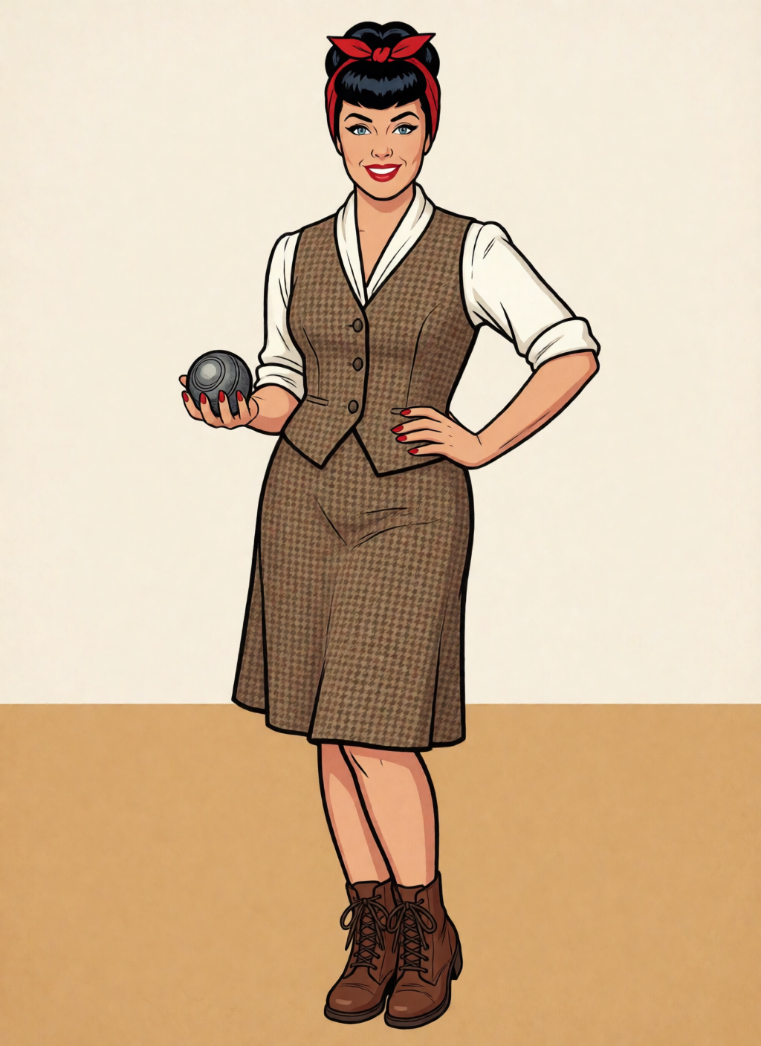
assets/Images/FannyWorldTour/003_angleterre.png
