guiraudjb/Arducible_Fanny_Petanque_World_Tour/assets/Images/FannyWorldTour/004_armenie.png

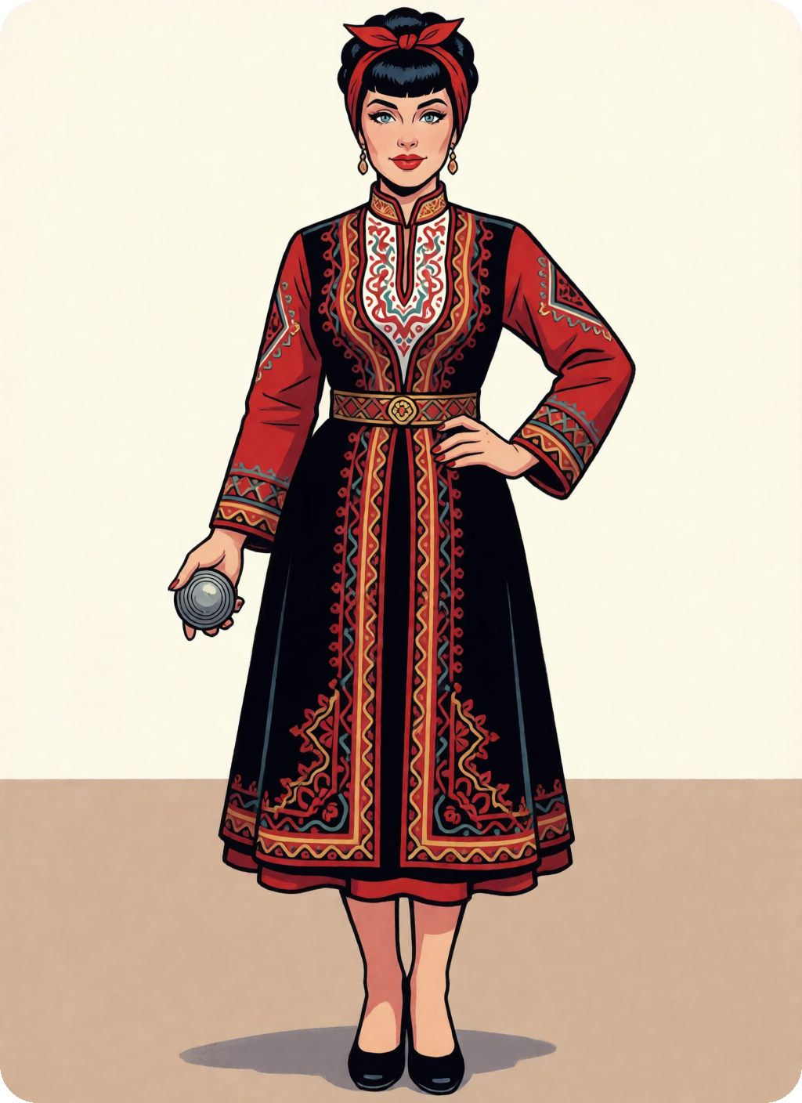
assets/Images/FannyWorldTour/004_armenie.png
