guiraudjb/Arducible_Fanny_Petanque_World_Tour/assets/Images/FannyWorldTour/008_danemark.png

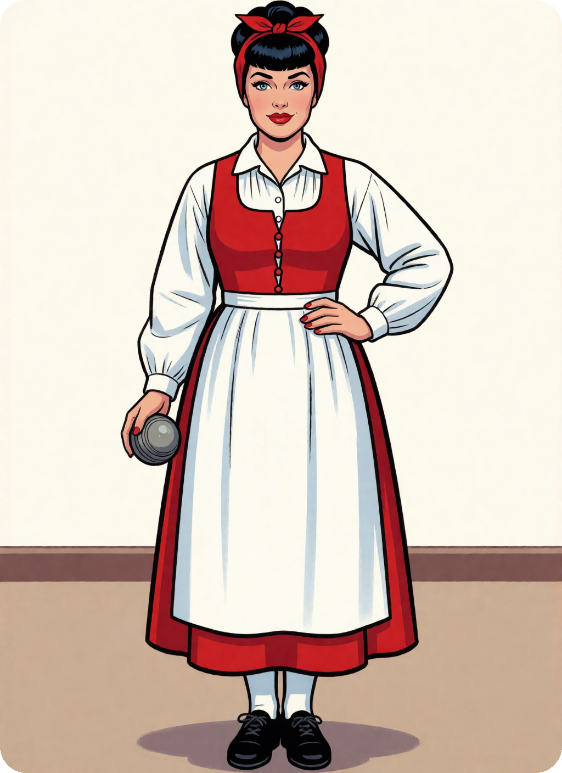
assets/Images/FannyWorldTour/008_danemark.png
