guiraudjb/Arducible_Fanny_Petanque_World_Tour/assets/Images/FannyWorldTour/018_jersey.png

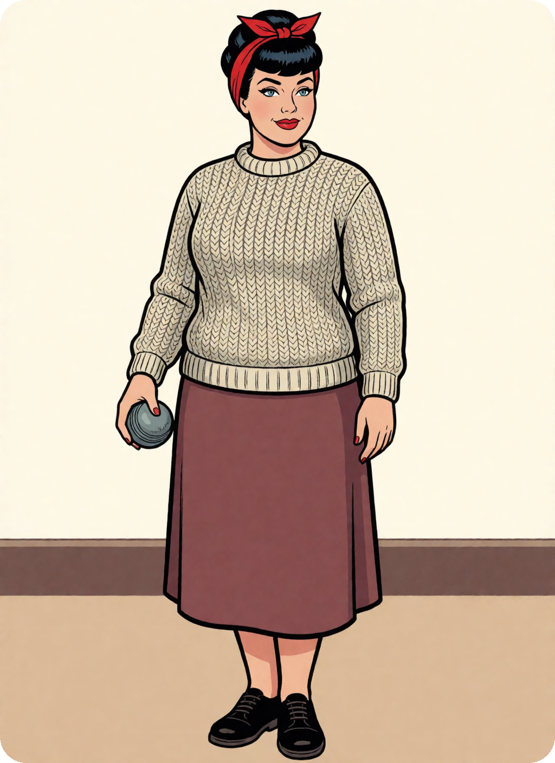
assets/Images/FannyWorldTour/018_jersey.png
