guiraudjb/Arducible_Fanny_Petanque_World_Tour/assets/Images/FannyWorldTour/020_lituanie.png

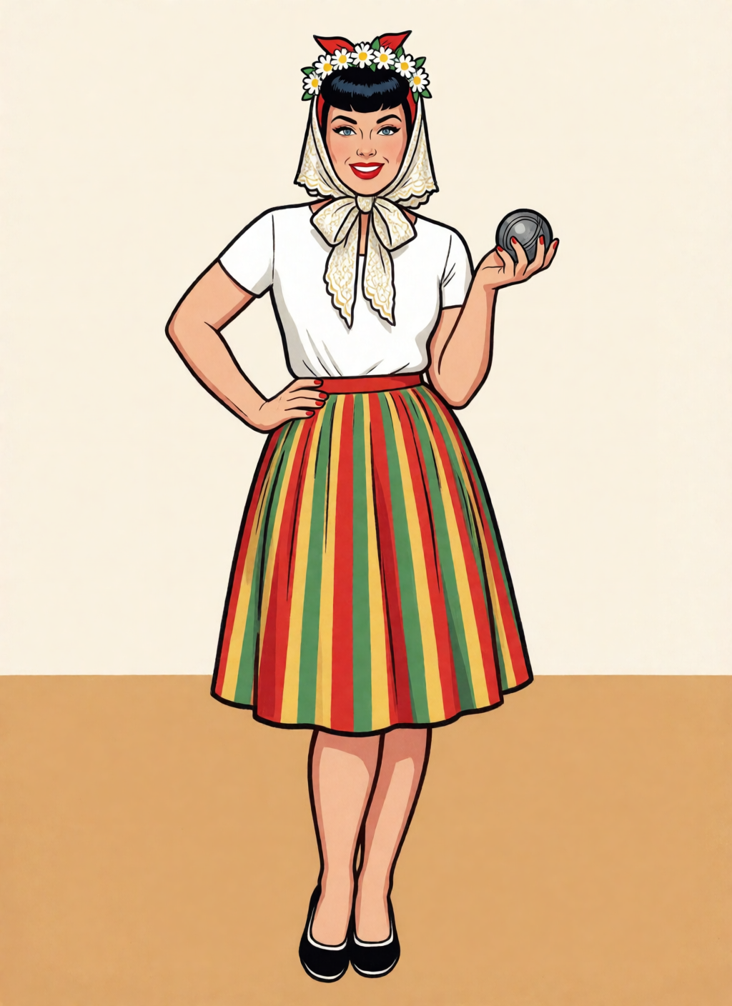
assets/Images/FannyWorldTour/020_lituanie.png
