guiraudjb/Arducible_Fanny_Petanque_World_Tour/assets/Images/FannyWorldTour/021_luxembourg.png

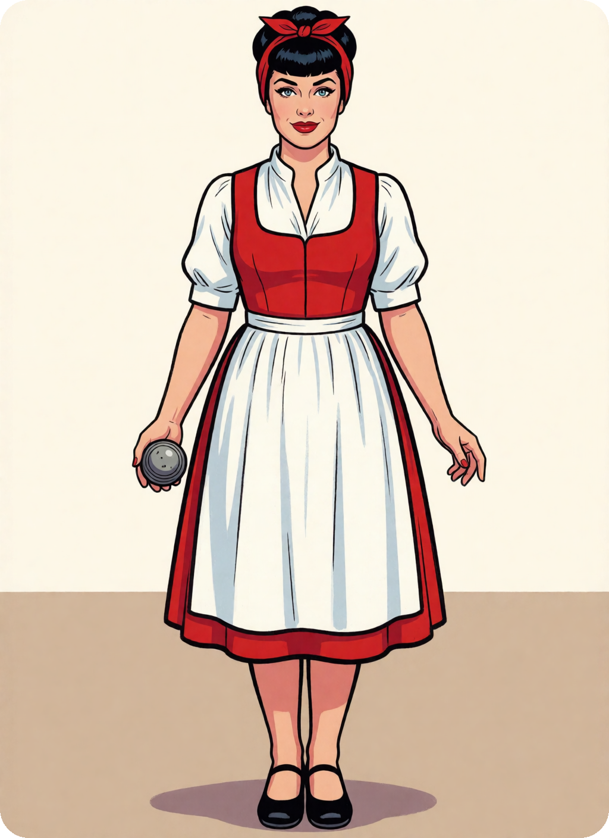
assets/Images/FannyWorldTour/021_luxembourg.png
