guiraudjb/Arducible_Fanny_Petanque_World_Tour/assets/Images/FannyWorldTour/028_roumanie.png

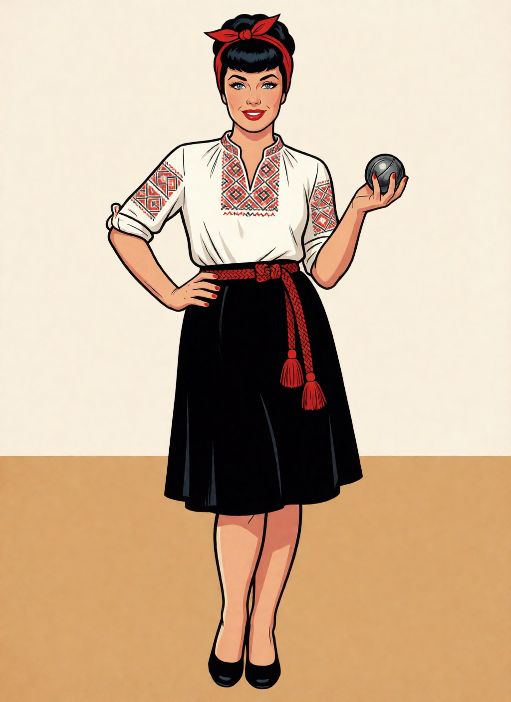
assets/Images/FannyWorldTour/028_roumanie.png
