guiraudjb/Arducible_Fanny_Petanque_World_Tour/assets/Images/FannyWorldTour/041_burkina_faso.png

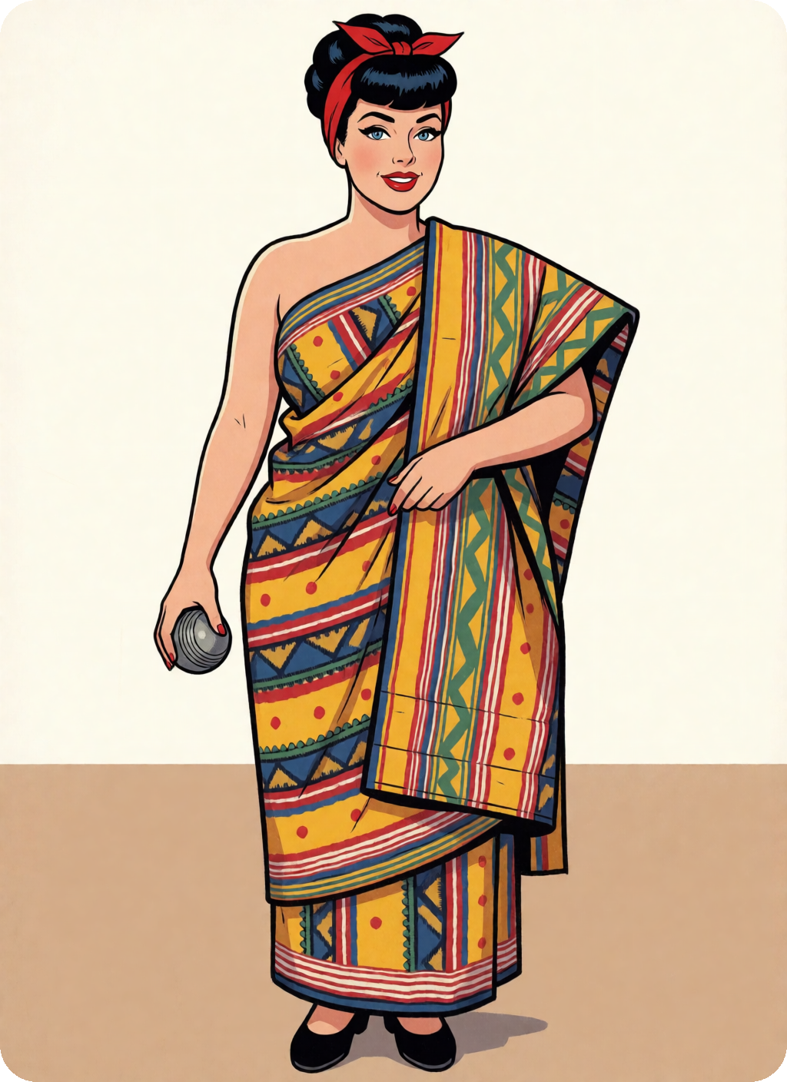
assets/Images/FannyWorldTour/041_burkina_faso.png
