guiraudjb/Arducible_Fanny_Petanque_World_Tour/assets/Images/FannyWorldTour/043_comores.png

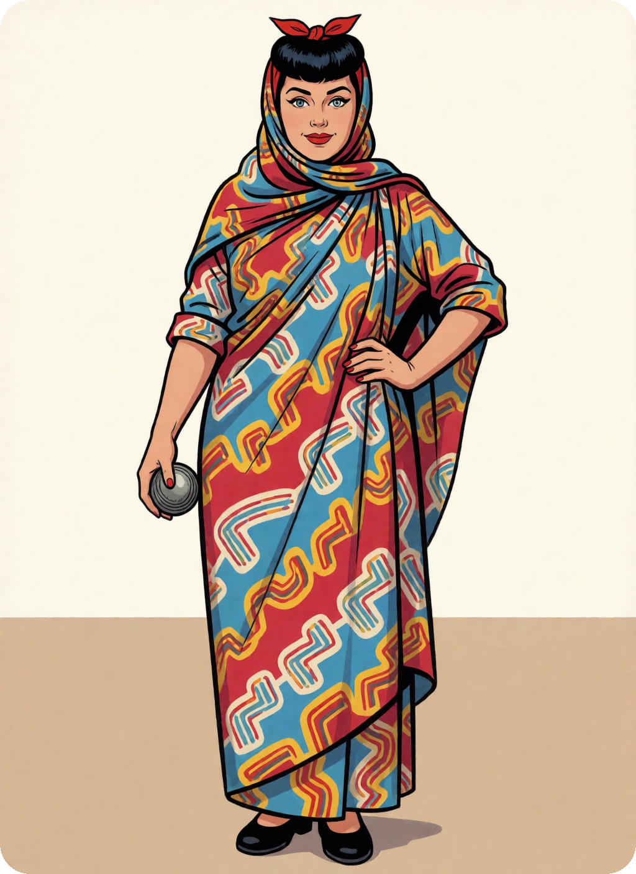
assets/Images/FannyWorldTour/043_comores.png
