guiraudjb/Arducible_Fanny_Petanque_World_Tour/assets/Images/FannyWorldTour/045_cote_d_ivoire.png

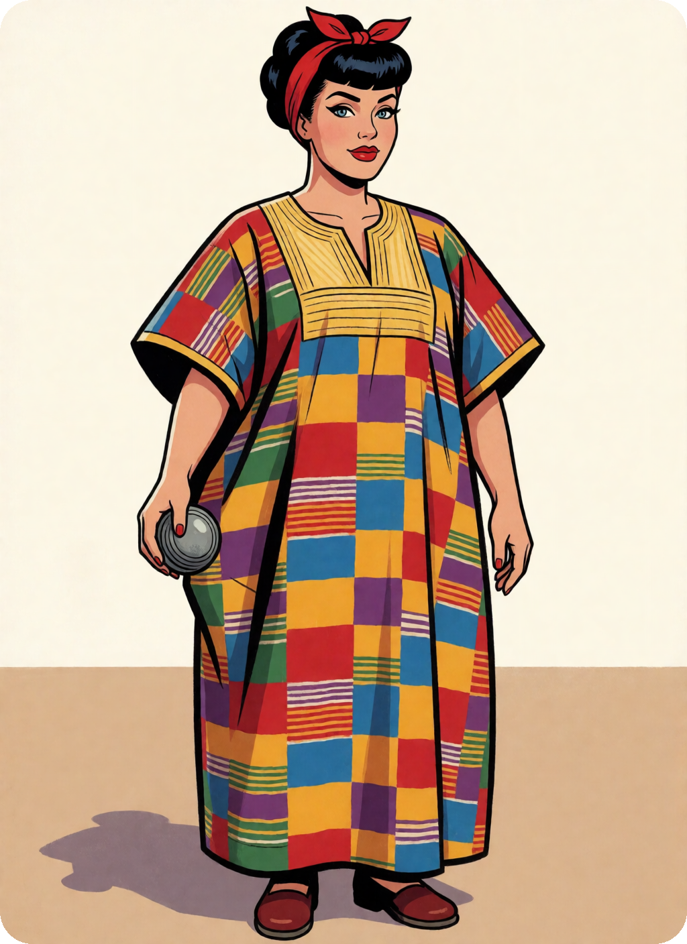
assets/Images/FannyWorldTour/045_cote_d_ivoire.png
