guiraudjb/Arducible_Fanny_Petanque_World_Tour/assets/Images/FannyWorldTour/046_djibouti.png

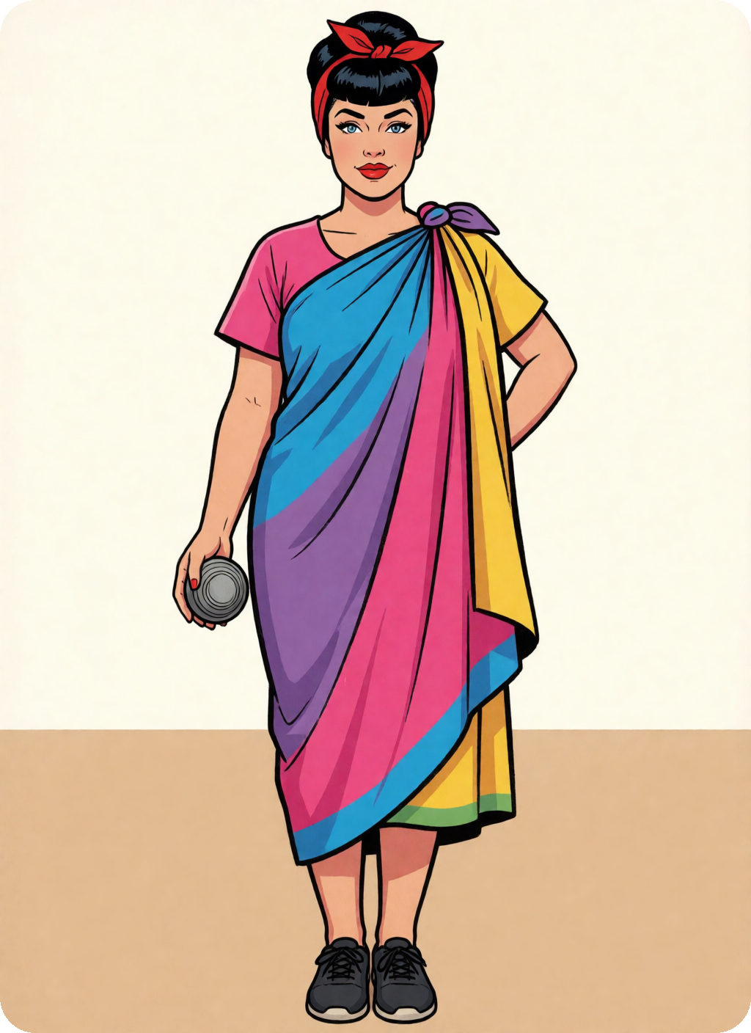
assets/Images/FannyWorldTour/046_djibouti.png
