guiraudjb/Arducible_Fanny_Petanque_World_Tour/assets/Images/FannyWorldTour/048_gabon.png

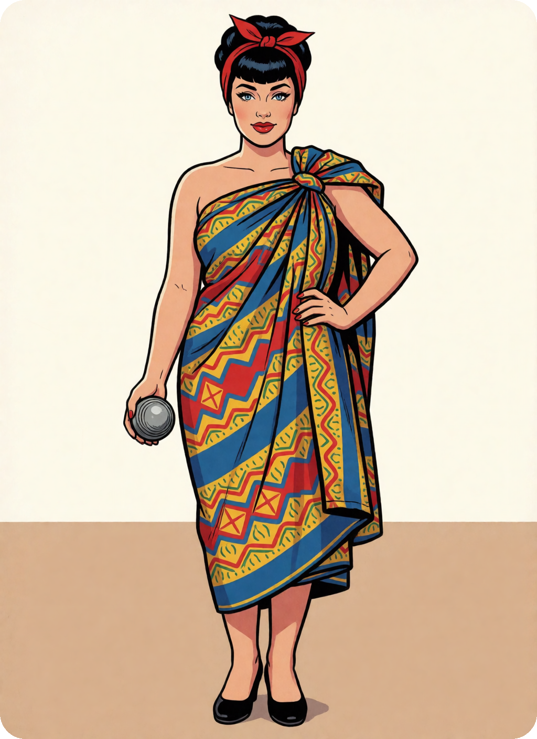
assets/Images/FannyWorldTour/048_gabon.png
