guiraudjb/Arducible_Fanny_Petanque_World_Tour/assets/Images/FannyWorldTour/055_maroc.png

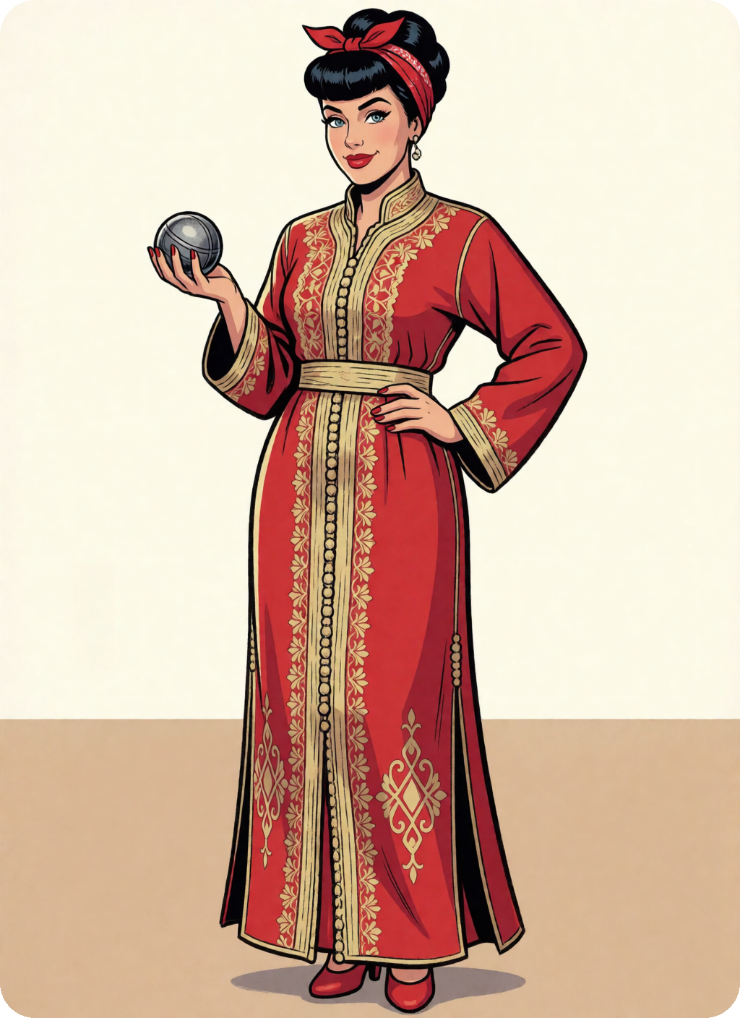
assets/Images/FannyWorldTour/055_maroc.png
