guiraudjb/Arducible_Fanny_Petanque_World_Tour/assets/Images/FannyWorldTour/056_niger.png

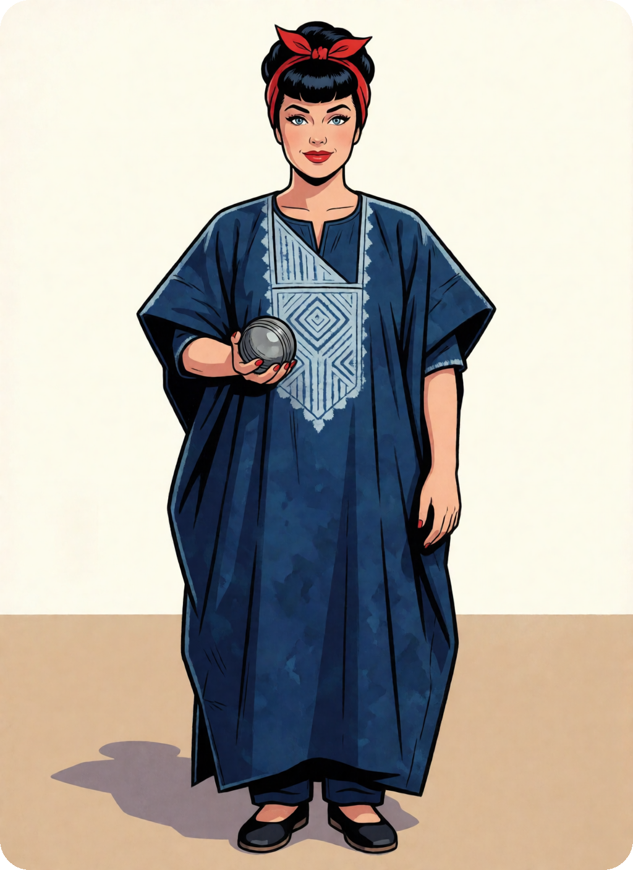
assets/Images/FannyWorldTour/056_niger.png
