guiraudjb/Arducible_Fanny_Petanque_World_Tour/assets/Images/FannyWorldTour/057_ouganda.png

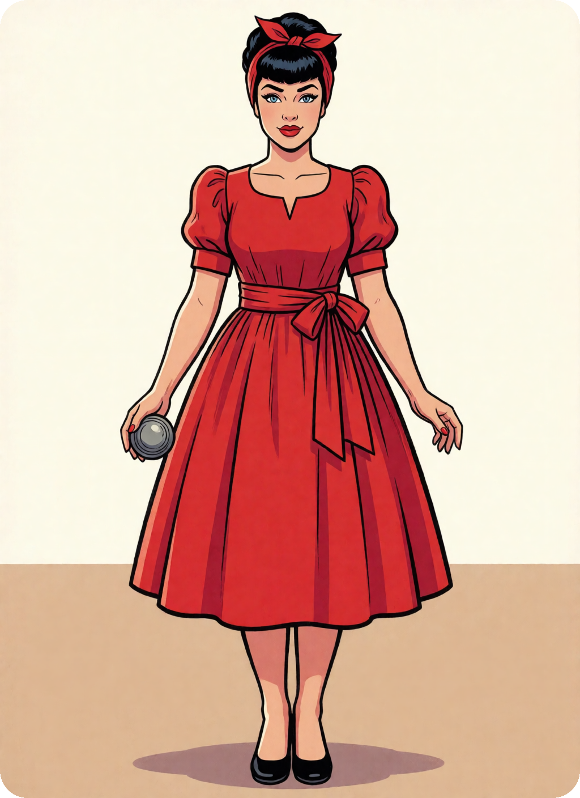
assets/Images/FannyWorldTour/057_ouganda.png
