guiraudjb/Arducible_Fanny_Petanque_World_Tour/assets/Images/FannyWorldTour/061_seychelles.png

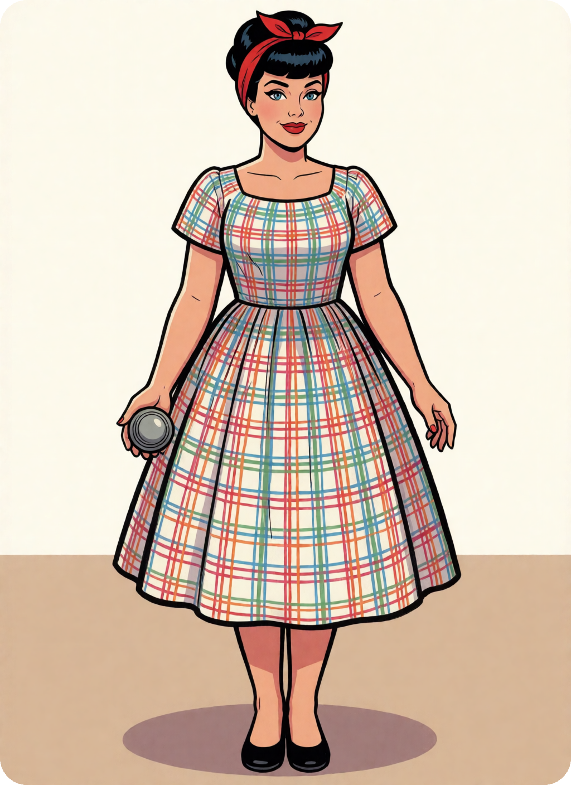
assets/Images/FannyWorldTour/061_seychelles.png
