guiraudjb/Arducible_Fanny_Petanque_World_Tour/assets/Images/FannyWorldTour/070_chine.png

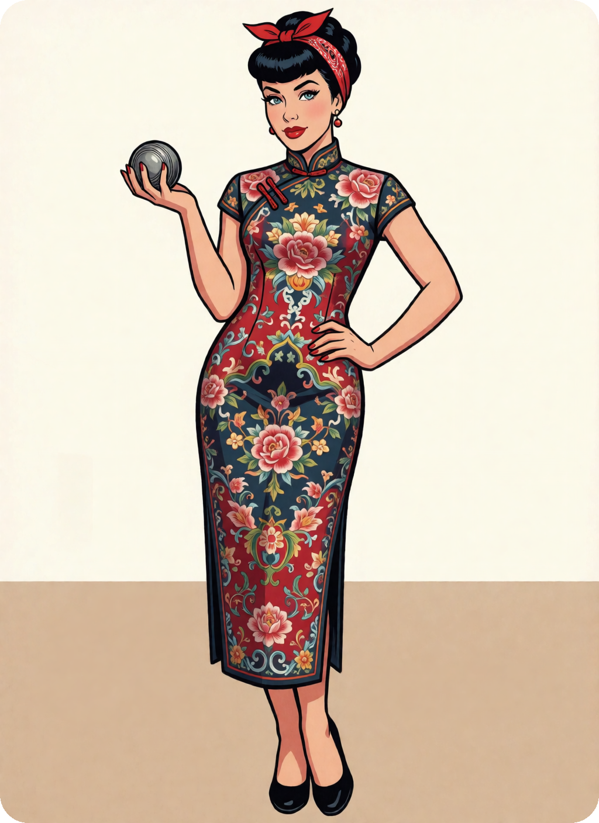
assets/Images/FannyWorldTour/070_chine.png
