guiraudjb/Arducible_Fanny_Petanque_World_Tour/assets/Images/FannyWorldTour/073_indonesie.png

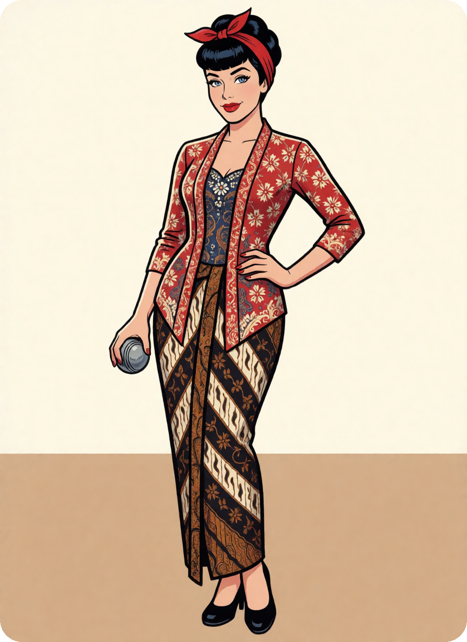
assets/Images/FannyWorldTour/073_indonesie.png
