guiraudjb/Arducible_Fanny_Petanque_World_Tour/assets/Images/FannyWorldTour/078_laos.png

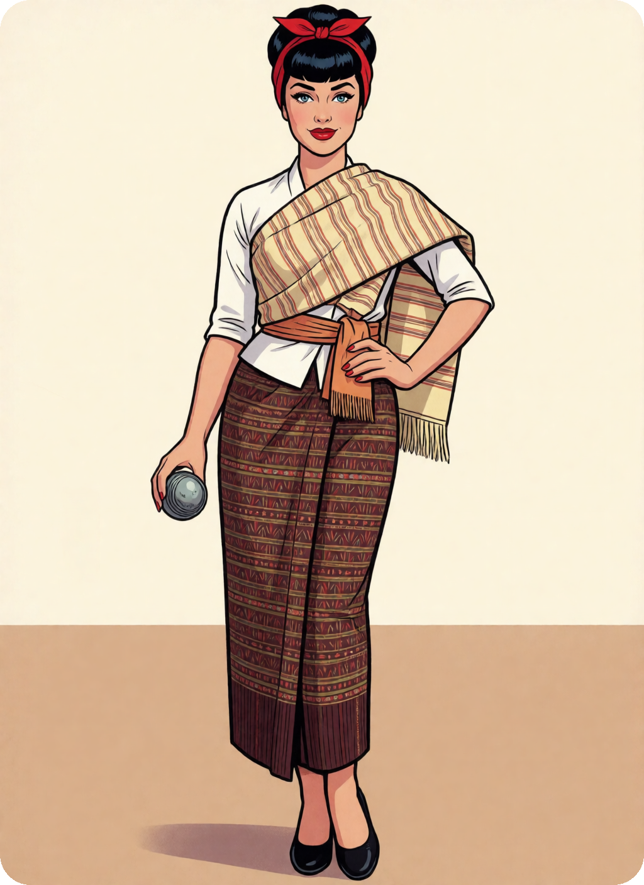
assets/Images/FannyWorldTour/078_laos.png
