guiraudjb/Arducible_Fanny_Petanque_World_Tour/assets/Images/FannyWorldTour/079_malaisie.png

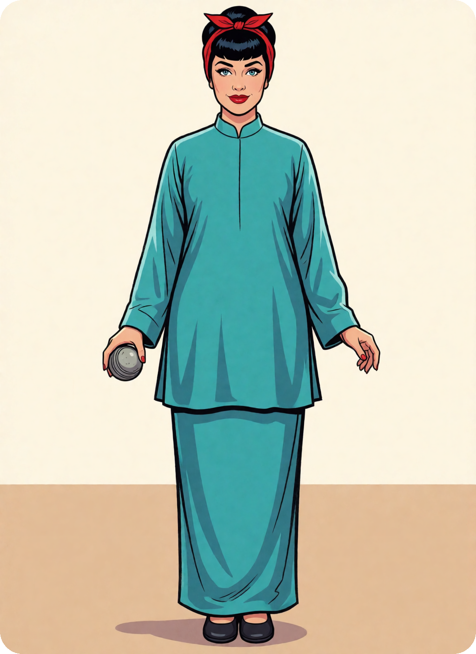
assets/Images/FannyWorldTour/079_malaisie.png
