guiraudjb/Arducible_Fanny_Petanque_World_Tour/assets/Images/FannyWorldTour/080_mongolie.png

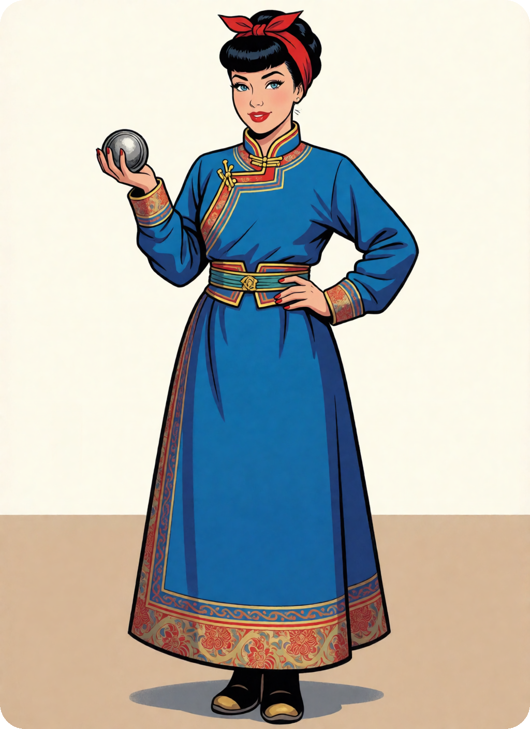
assets/Images/FannyWorldTour/080_mongolie.png
