guiraudjb/Arducible_Fanny_Petanque_World_Tour/assets/Images/FannyWorldTour/081_myanmar.png

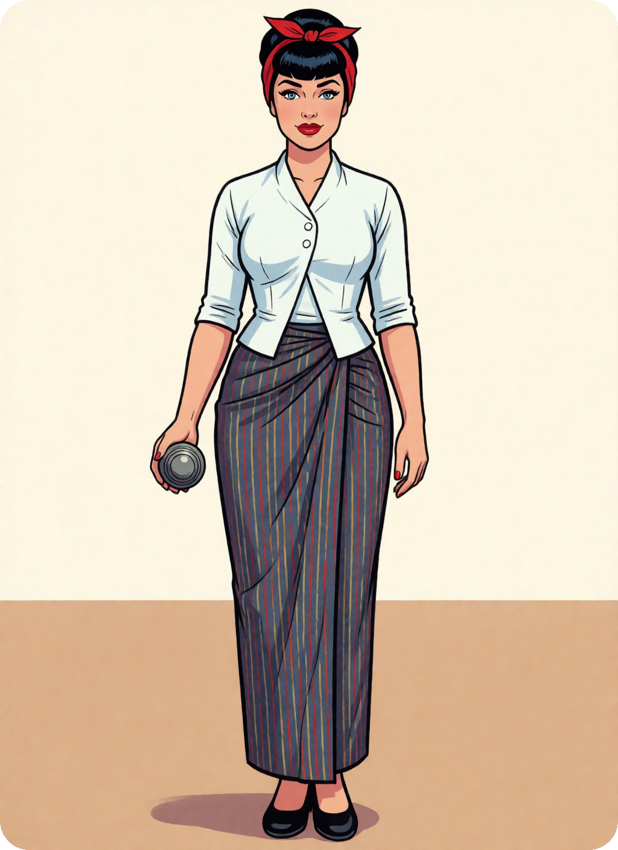
assets/Images/FannyWorldTour/081_myanmar.png
