guiraudjb/Arducible_Fanny_Petanque_World_Tour/assets/Images/FannyWorldTour/092_canada.png

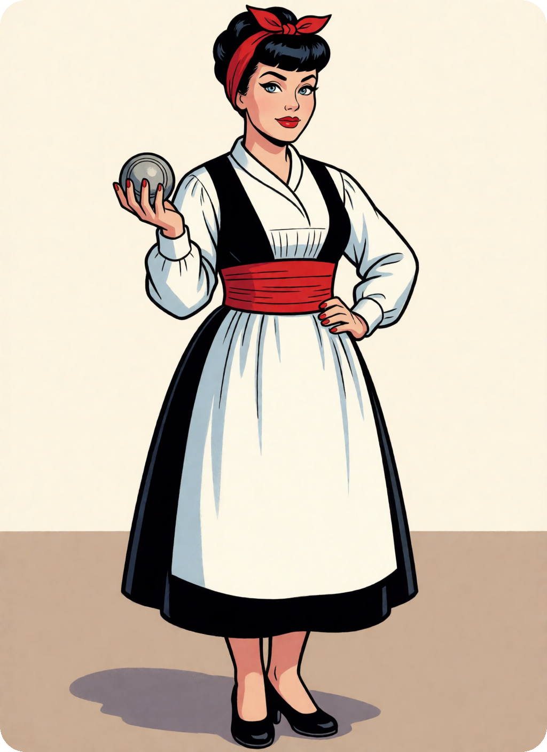
assets/Images/FannyWorldTour/092_canada.png
