guiraudjb/Arducible_Fanny_Petanque_World_Tour/assets/Images/FannyWorldTour/094_colombie.png

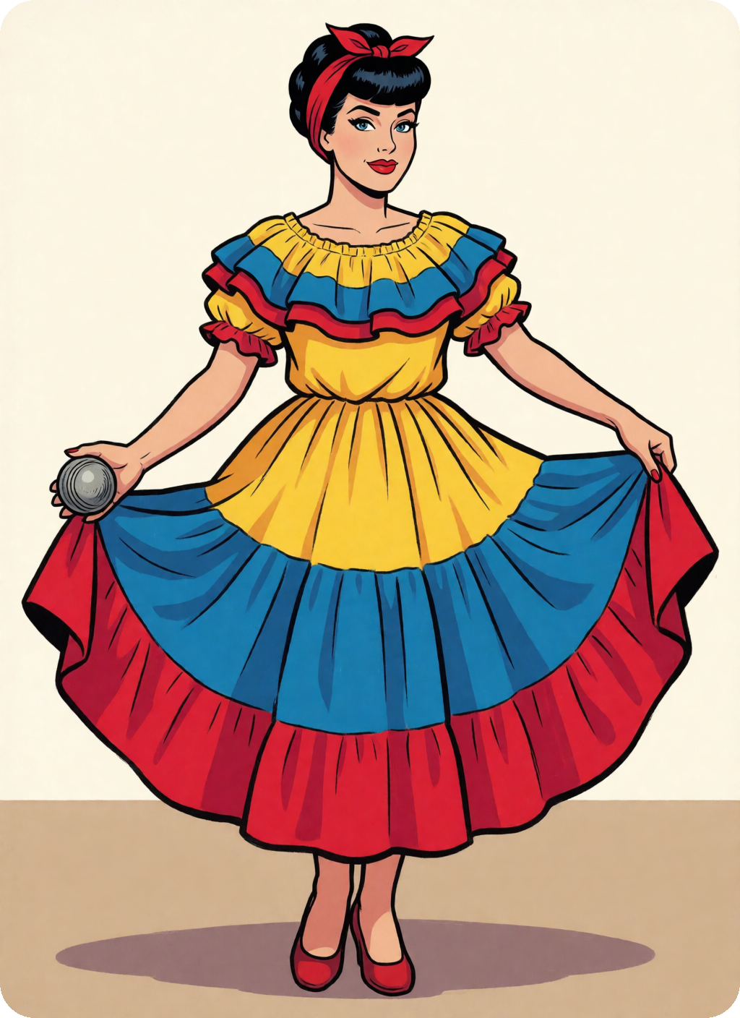
assets/Images/FannyWorldTour/094_colombie.png
