guiraudjb/Arducible_Fanny_Petanque_World_Tour/assets/Images/FannyWorldTour/100_haiti.png

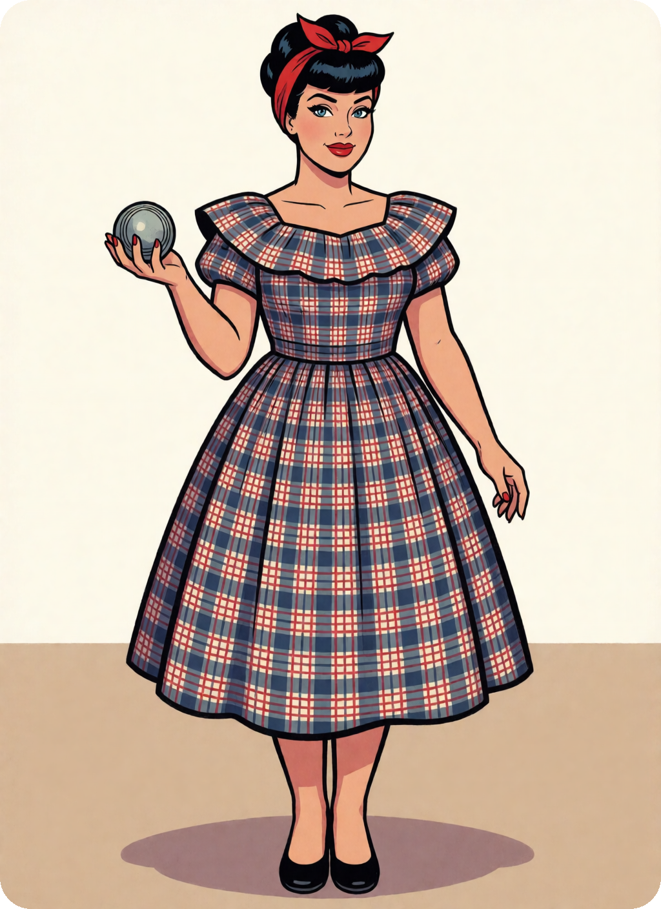
assets/Images/FannyWorldTour/100_haiti.png
