guiraudjb/Arducible_Fanny_Petanque_World_Tour/assets/Images/FannyWorldTour/115_liban.png

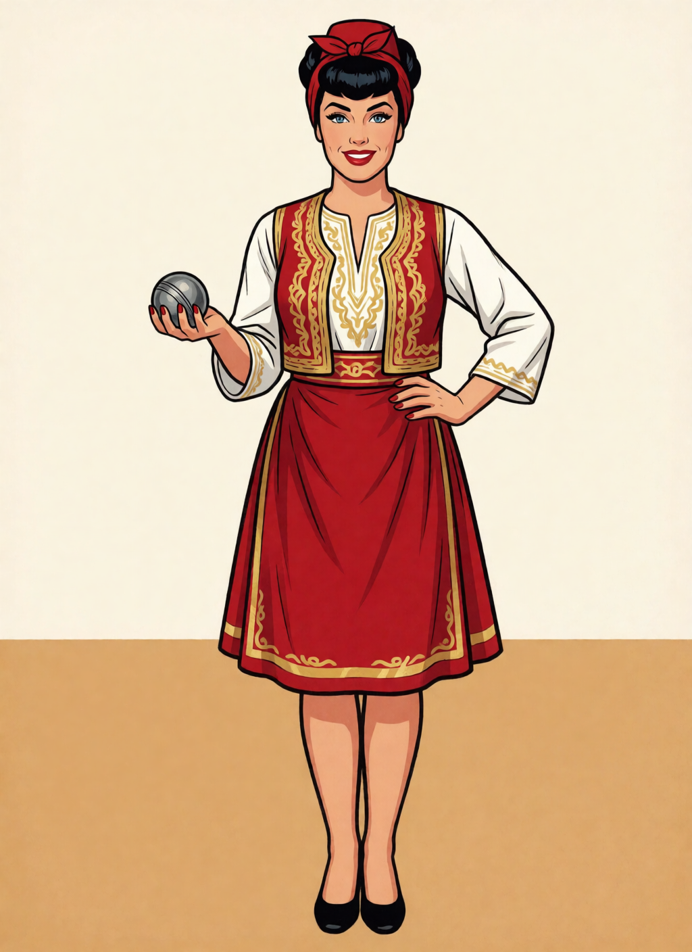
assets/Images/FannyWorldTour/115_liban.png
