guiraudjb/Arducible_Fanny_Petanque_World_Tour/hardware/pcb/pcb-detection-v3-breadboard-preview.png

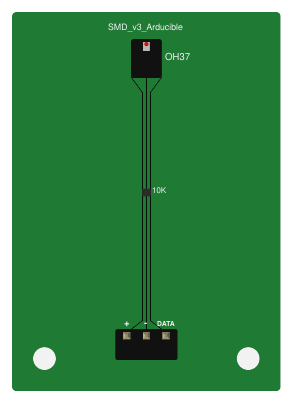
hardware/pcb/pcb-detection-v3-breadboard-preview.png
