guiraudjb/Arducible_Fanny_Petanque_World_Tour/hardware/pcb/pcb_easyeda2.png

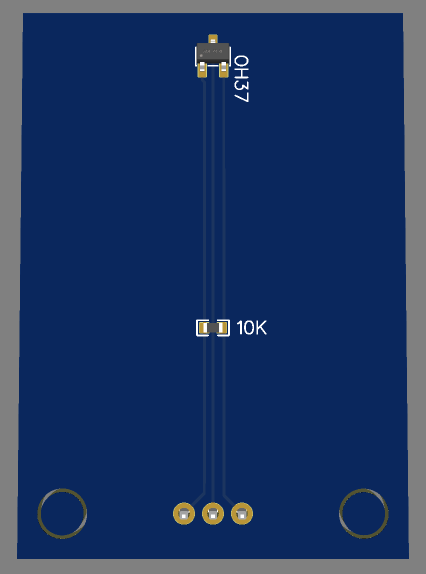
hardware/pcb/pcb_easyeda2.png
