guiraudjb/Arducible_Fanny_Petanque_World_Tour/hardware/pcb/pcb_easyeda3.png

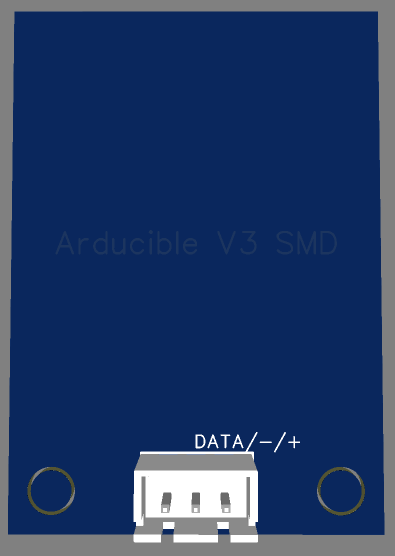
hardware/pcb/pcb_easyeda3.png
