guiraudjb/Arducible_Fanny_Petanque_World_Tour/hardware/renders/articulation/entretoise-h31.png

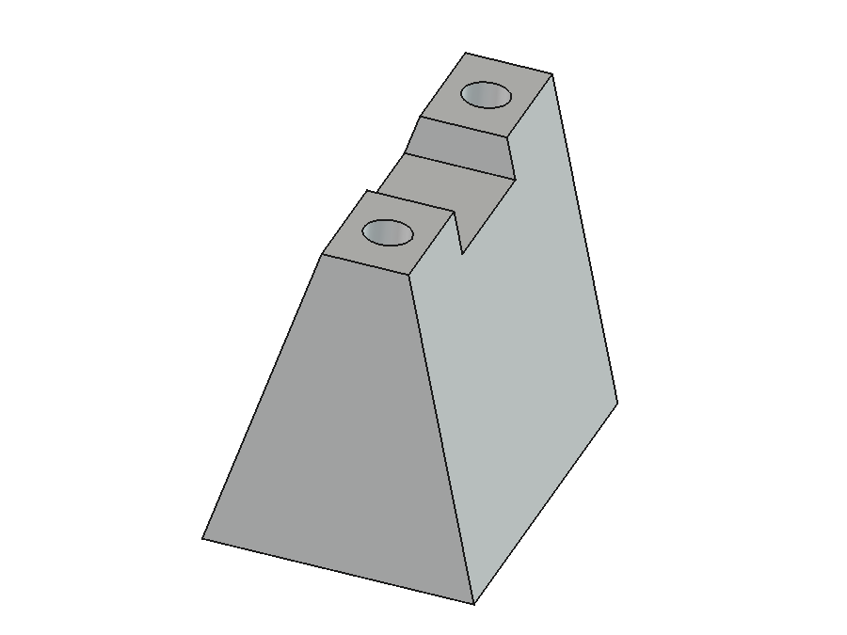
hardware/renders/articulation/entretoise-h31.png
