guiraudjb/Arducible_Fanny_Petanque_World_Tour/hardware/renders/articulation/interface-axe-aimant-4mm.png

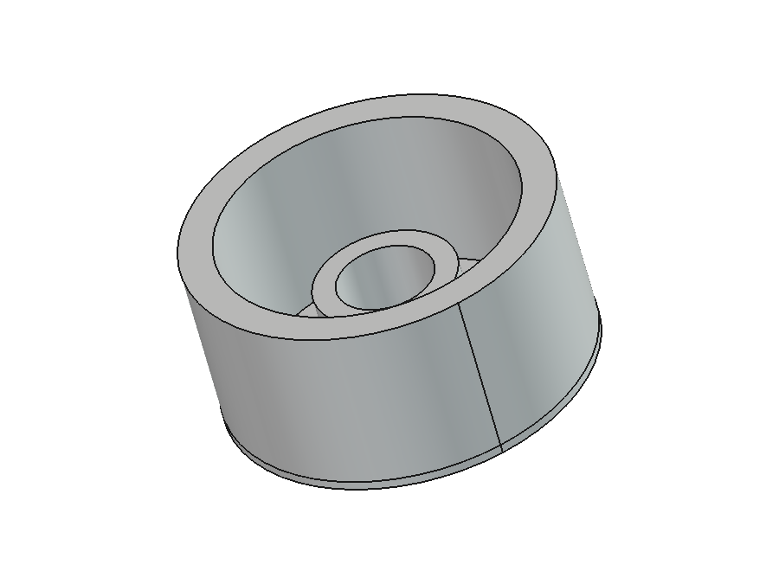
hardware/renders/articulation/interface-axe-aimant-4mm.png
