guiraudjb/Arducible_Fanny_Petanque_World_Tour/hardware/renders/articulation/plaque-inf.png

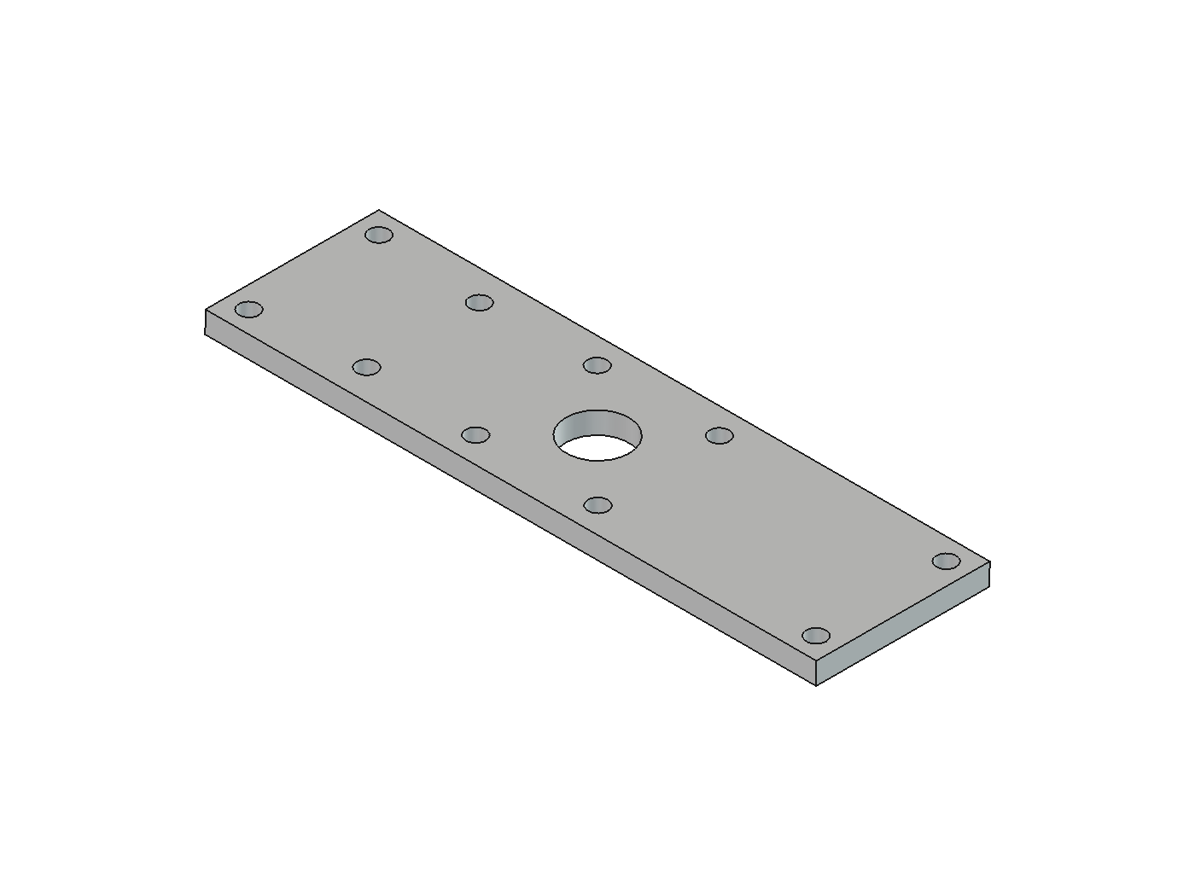
hardware/renders/articulation/plaque-inf.png
