guiraudjb/Arducible_Fanny_Petanque_World_Tour/hardware/renders/articulation/rondelle-8x22x1-5.png

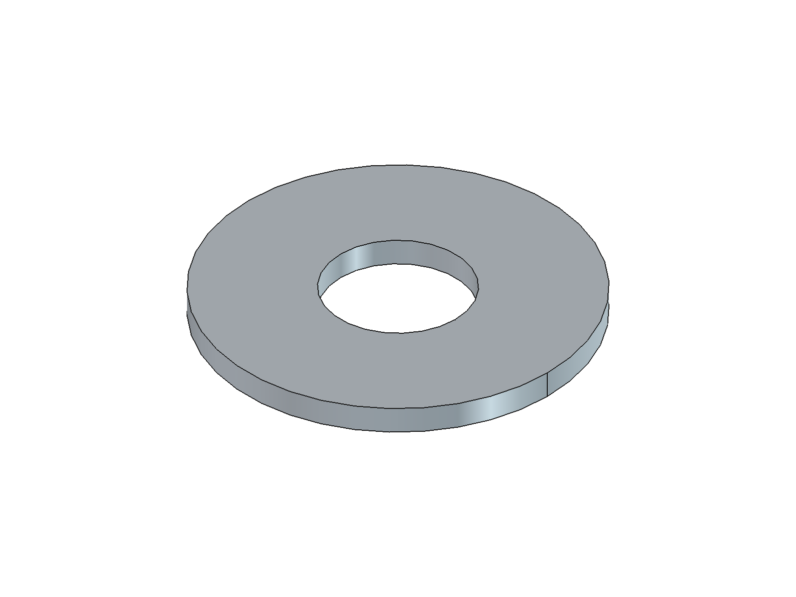
hardware/renders/articulation/rondelle-8x22x1-5.png
