guiraudjb/Arducible_Fanny_Petanque_World_Tour/hardware/renders/articulation/rotule-ge8-articulee-inclinee10deg.png

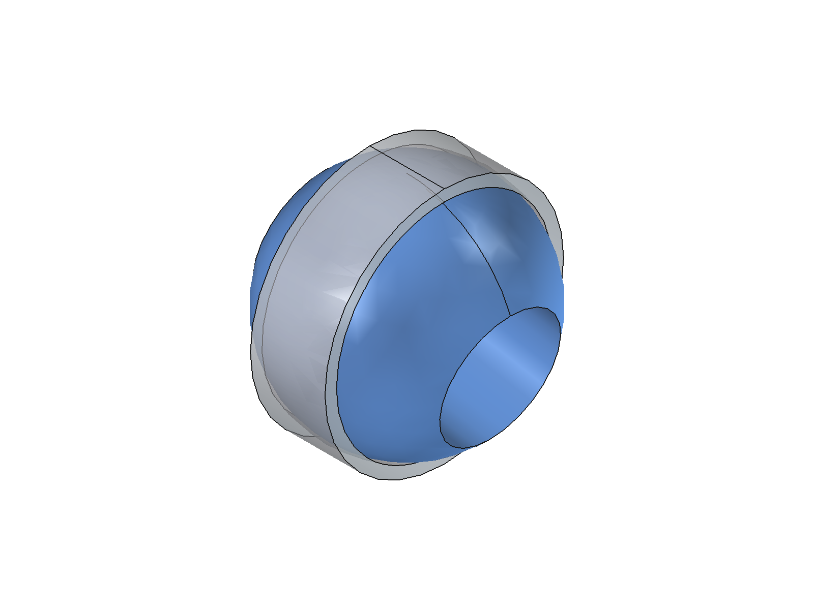
hardware/renders/articulation/rotule-ge8-articulee-inclinee10deg.png
