guiraudjb/Arducible_Fanny_Petanque_World_Tour/hardware/renders/articulation/tampon-deformable-compression30.png

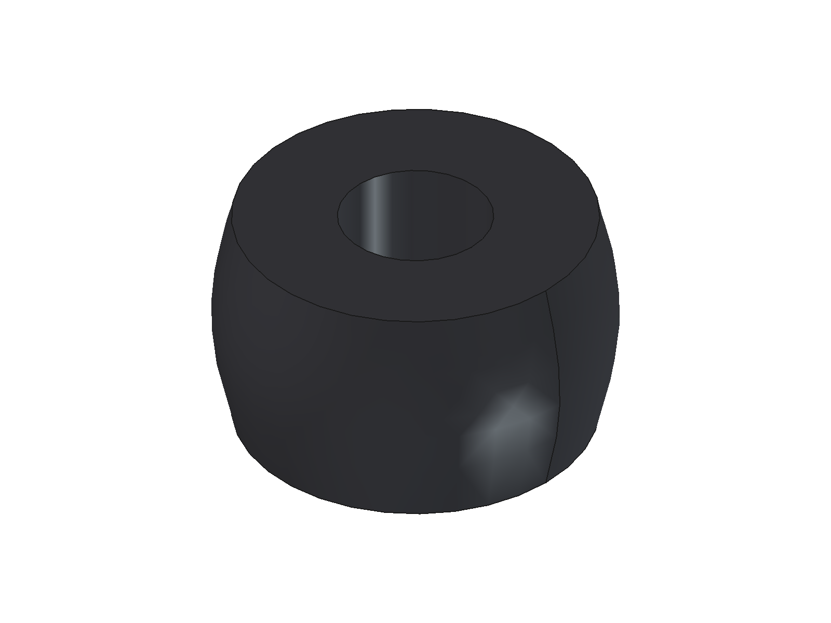
hardware/renders/articulation/tampon-deformable-compression30.png
