guiraudjb/Arducible_Fanny_Petanque_World_Tour/hardware/renders/articulation/tampon-ressort-cr60.png

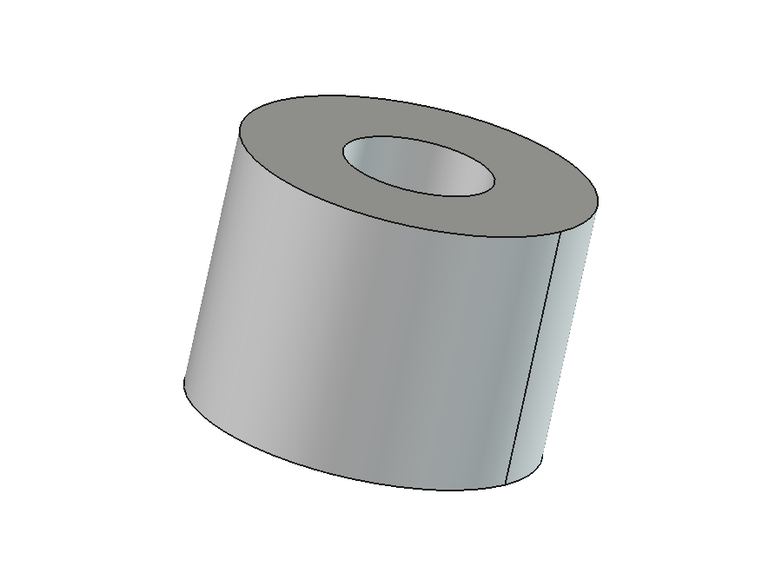
hardware/renders/articulation/tampon-ressort-cr60.png
