guiraudjb/Arducible_Fanny_Petanque_World_Tour/hardware/renders/articulation/vis-m4x30.png

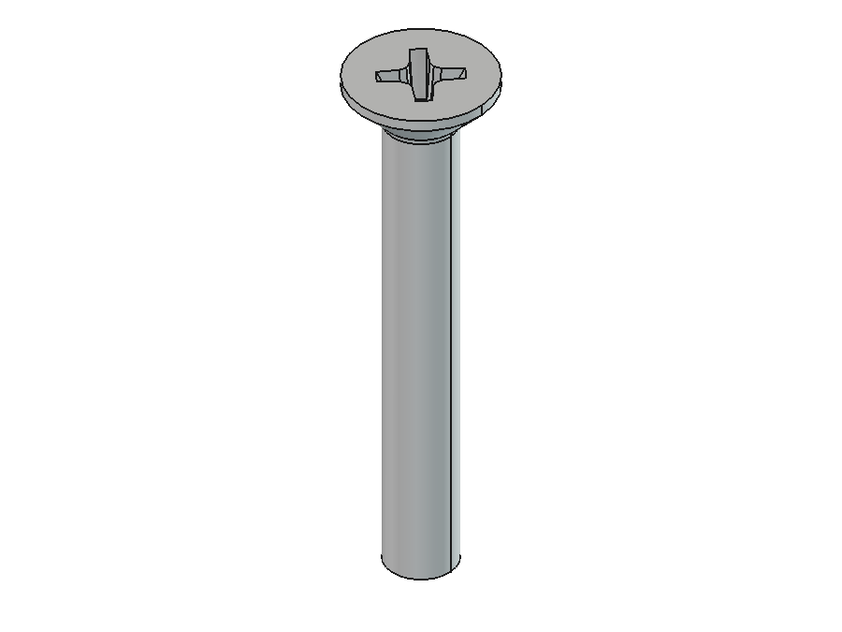
hardware/renders/articulation/vis-m4x30.png
