guiraudjb/Arducible_Fanny_Petanque_World_Tour/hardware/renders/articulation/vues-supplementaires/plaque-inf-front.png

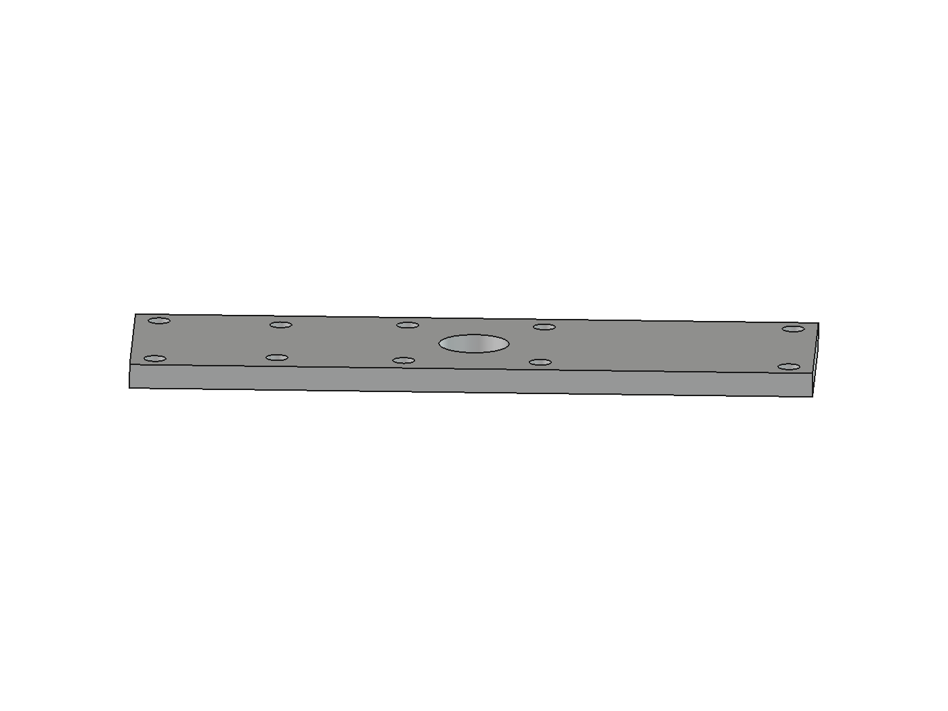
hardware/renders/articulation/vues-supplementaires/plaque-inf-front.png
