guiraudjb/Arducible_Fanny_Petanque_World_Tour/hardware/renders/articulation/vues-supplementaires/plaque-inf-top.png

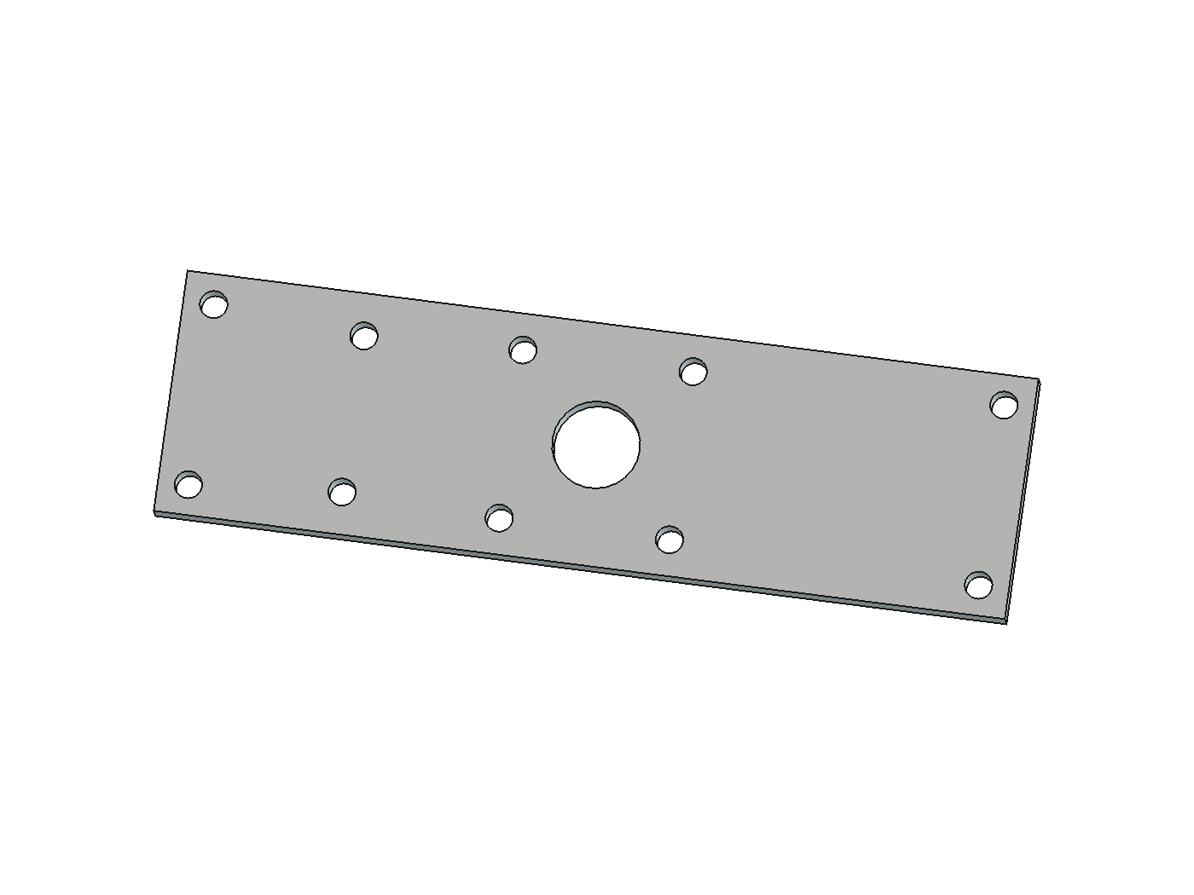
hardware/renders/articulation/vues-supplementaires/plaque-inf-top.png
