guiraudjb/Arducible_Fanny_Petanque_World_Tour/hardware/renders/articulation/vues-supplementaires/plaque-sup-bottom.png

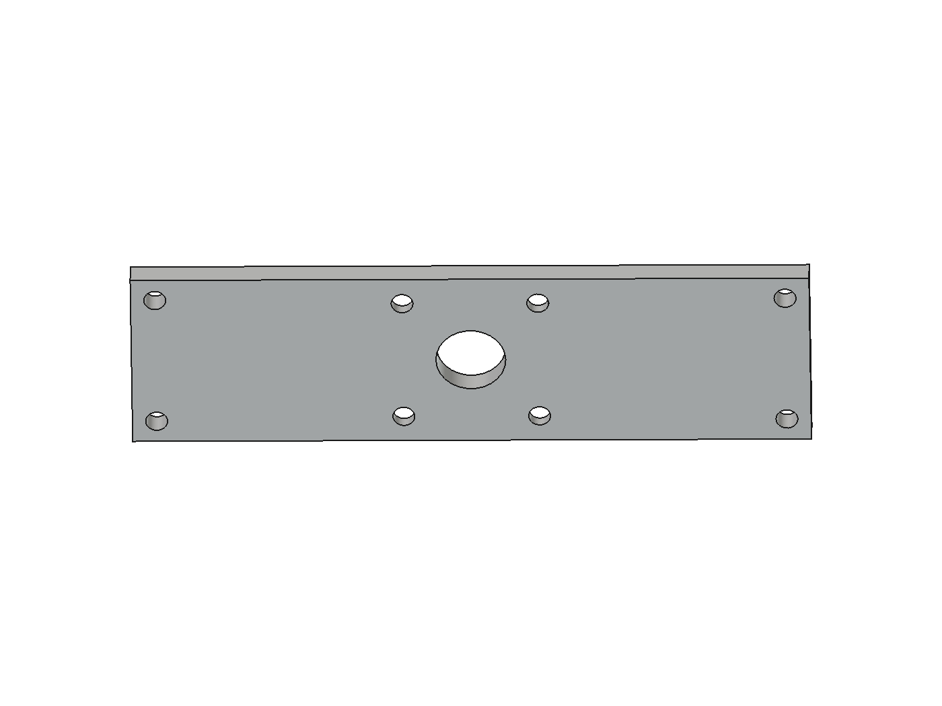
hardware/renders/articulation/vues-supplementaires/plaque-sup-bottom.png
