guiraudjb/Arducible_Fanny_Petanque_World_Tour/hardware/renders/chassis/interface-noyau-rj45.png

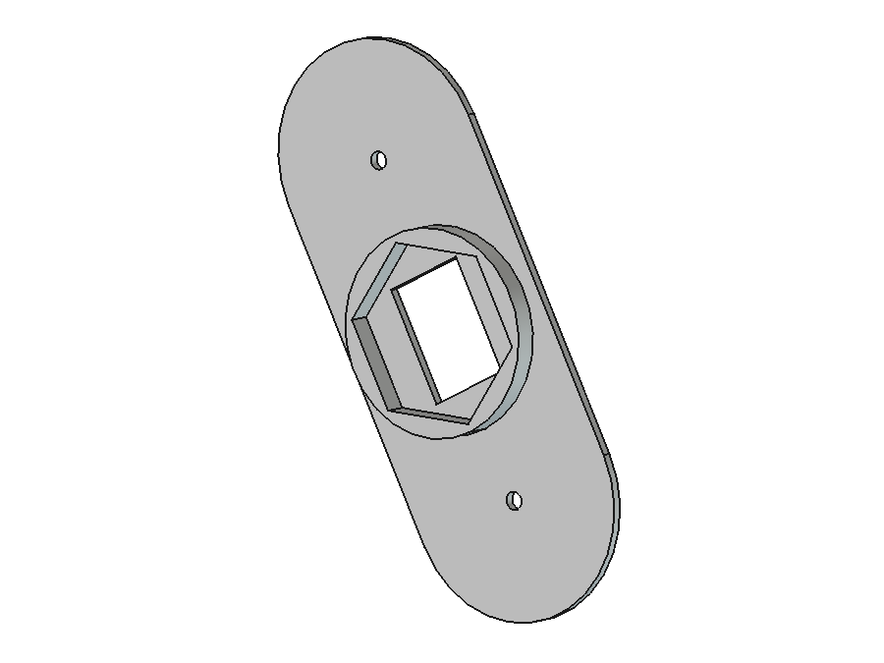
hardware/renders/chassis/interface-noyau-rj45.png
