guiraudjb/Arducible_Fanny_Petanque_World_Tour/hardware/renders/chassis/support-rj45.png

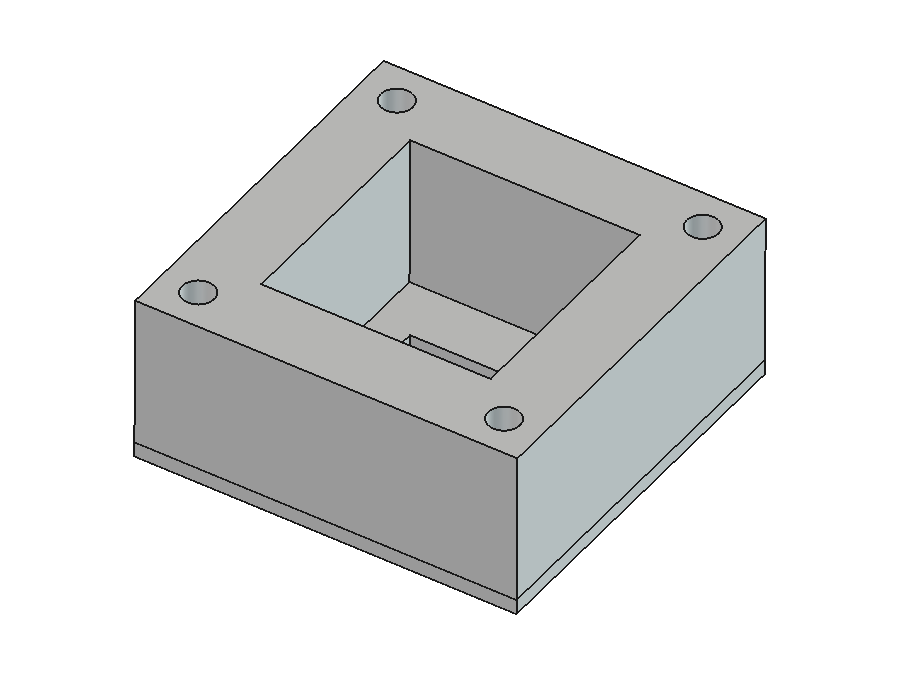
hardware/renders/chassis/support-rj45.png
