guiraudjb/Arducible_Fanny_Petanque_World_Tour/hardware/renders/chassis/support-v7.png

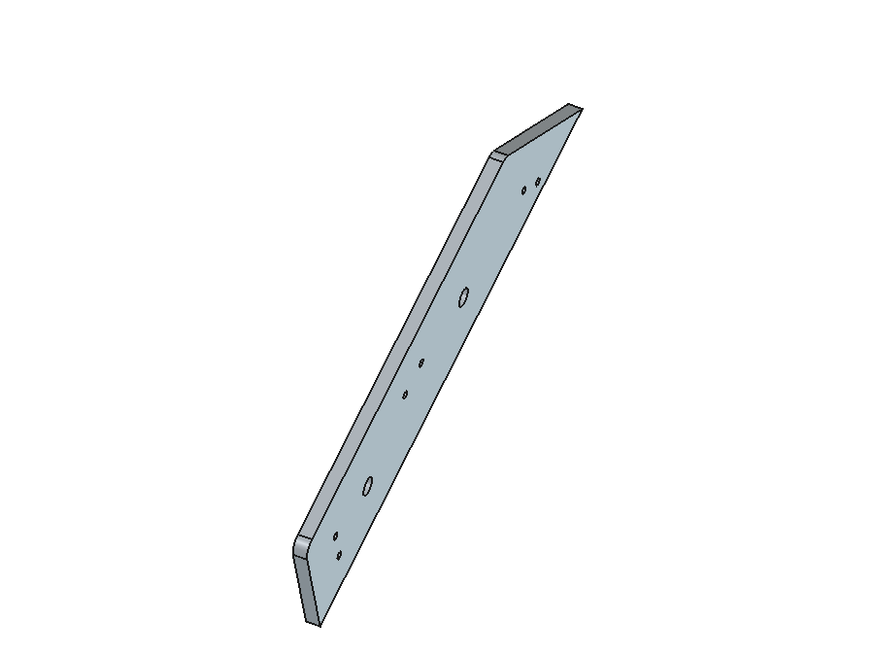
hardware/renders/chassis/support-v7.png
