guiraudjb/Arducible_Fanny_Petanque_World_Tour/hardware/renders/enclosure/boitier-facade.png

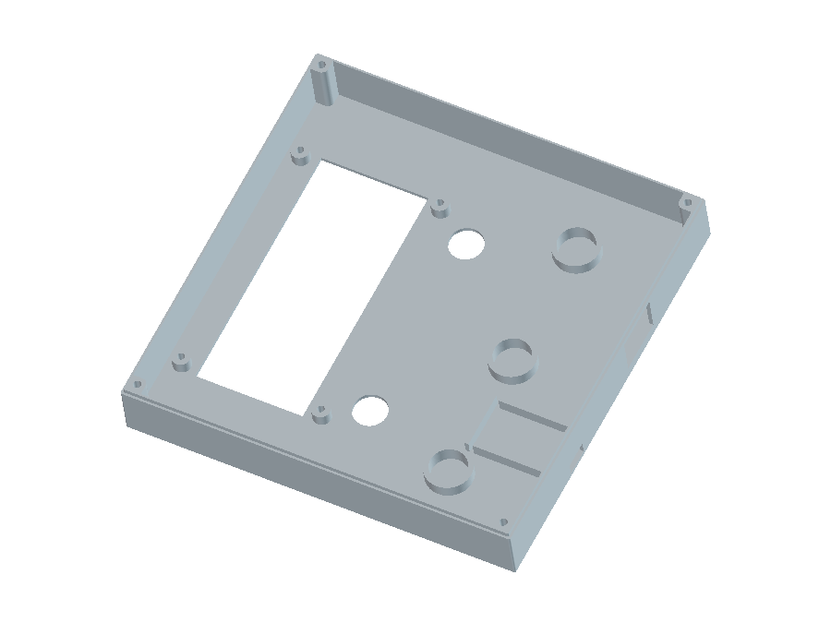
hardware/renders/enclosure/boitier-facade.png
