guiraudjb/Arducible_Fanny_Petanque_World_Tour/hardware/renders/enclosure/boitier-fermeture.png

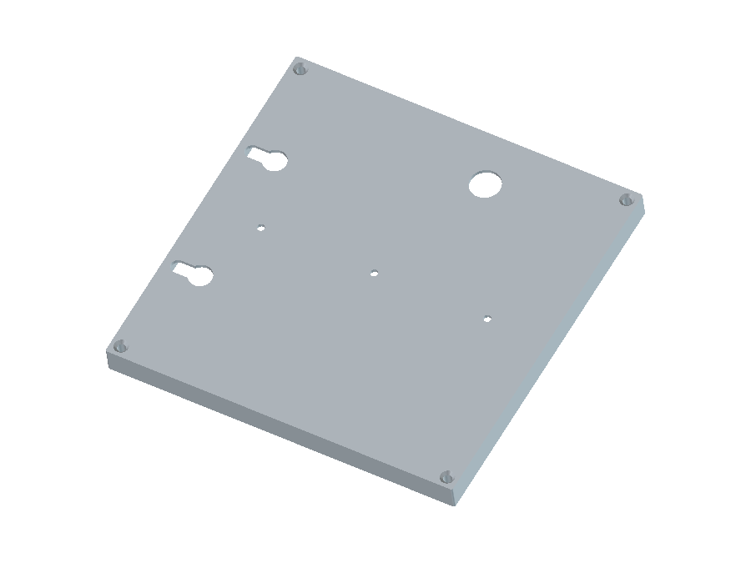
hardware/renders/enclosure/boitier-fermeture.png
