guiraudjb/Arducible_Fanny_Petanque_World_Tour/hardware/renders/enclosure/boitier-support-ws2812.png

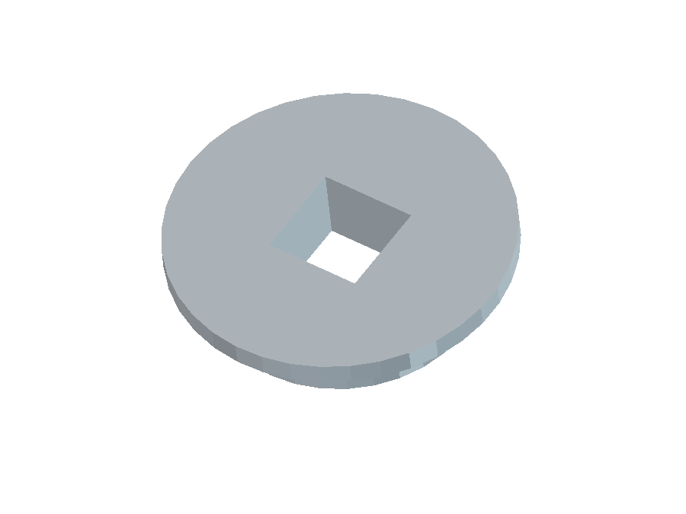
hardware/renders/enclosure/boitier-support-ws2812.png
