guiraudjb/Arducible_Fanny_Petanque_World_Tour/hardware/renders/enclosure/promicro-board.png

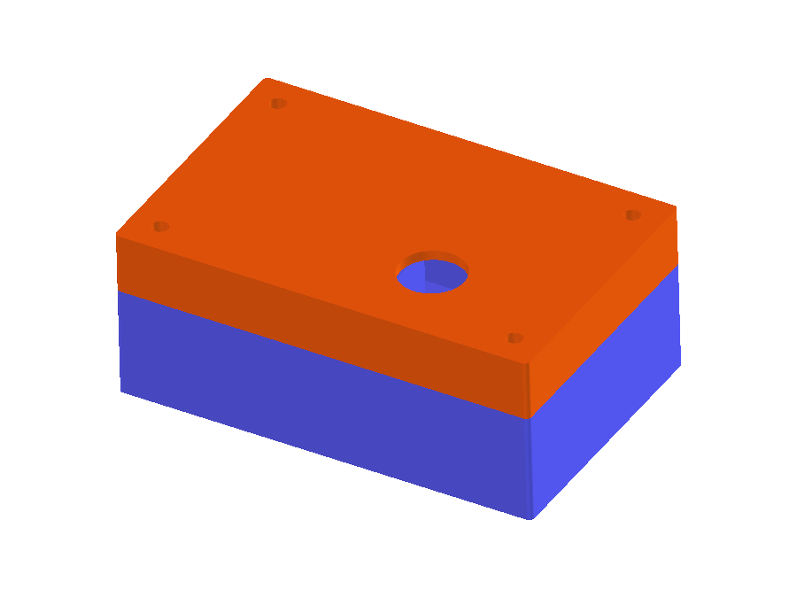
hardware/renders/enclosure/promicro-board.png
