guiraudjb/Arducible_Fanny_Petanque_World_Tour/hardware/renders/pcb/detection-pcb-v3-iso.png

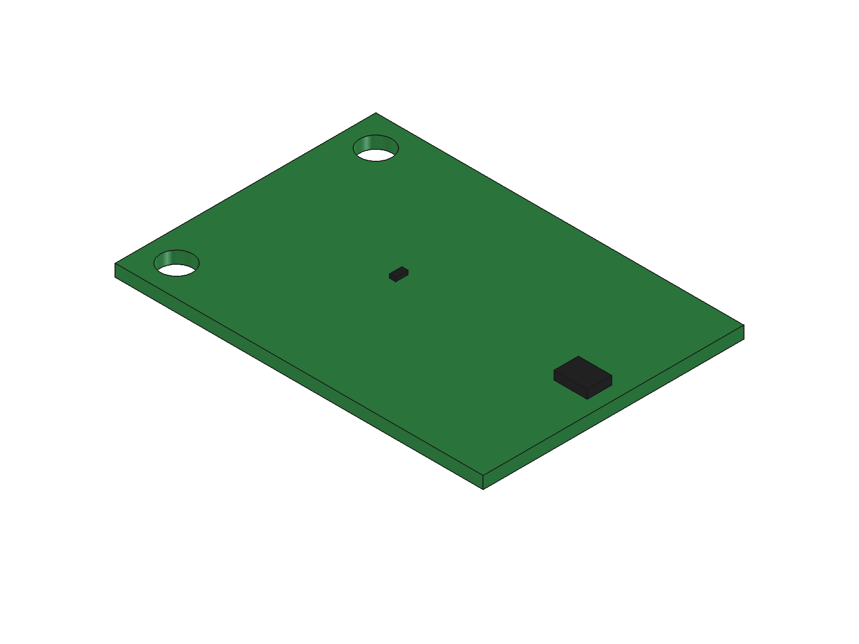
hardware/renders/pcb/detection-pcb-v3-iso.png
