guiraudjb/Arducible_Fanny_Petanque_World_Tour/ressources/card game/assets/cards/5-diamonds.png

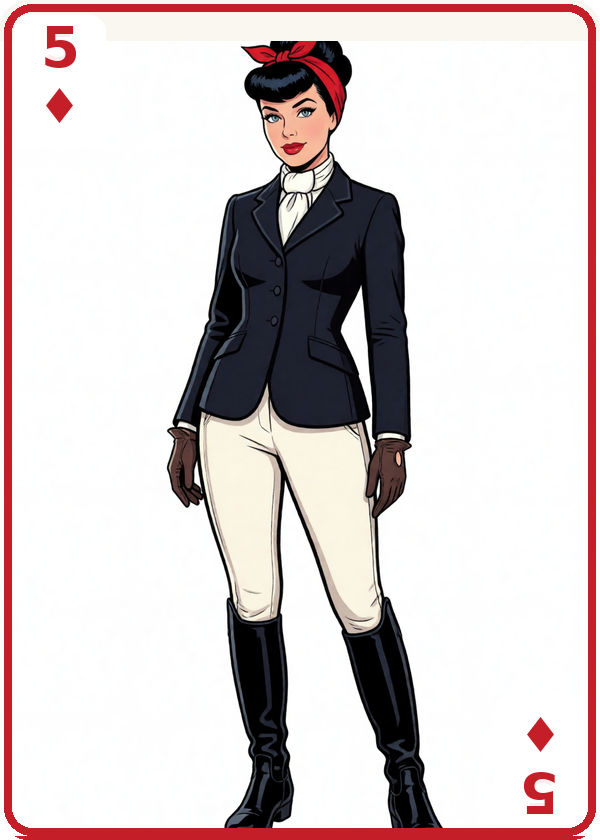
ressources/card game/assets/cards/5-diamonds.png
