guiraudjb/Arducible_Fanny_Petanque_World_Tour/ressources/card game/assets/cards/8-hearts.png

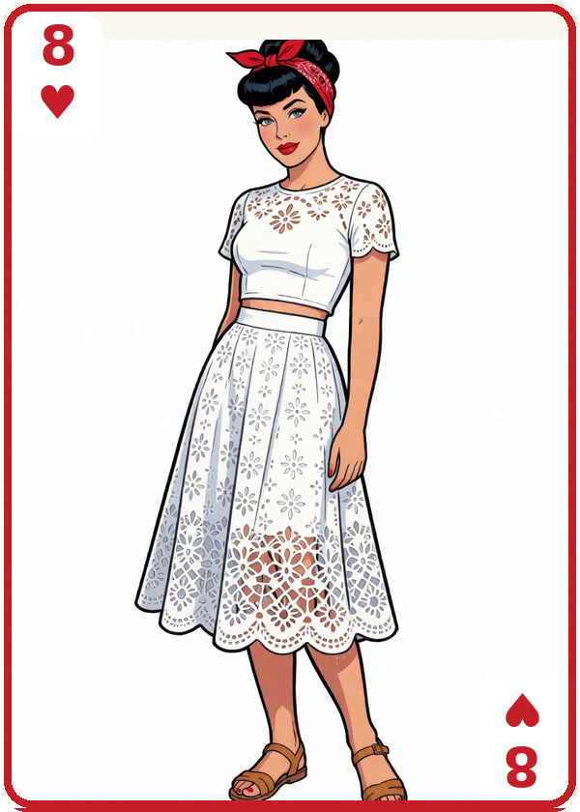
ressources/card game/assets/cards/8-hearts.png
