guiraudjb/Arducible_Fanny_Petanque_World_Tour/ressources/card game/assets/cards/back.png

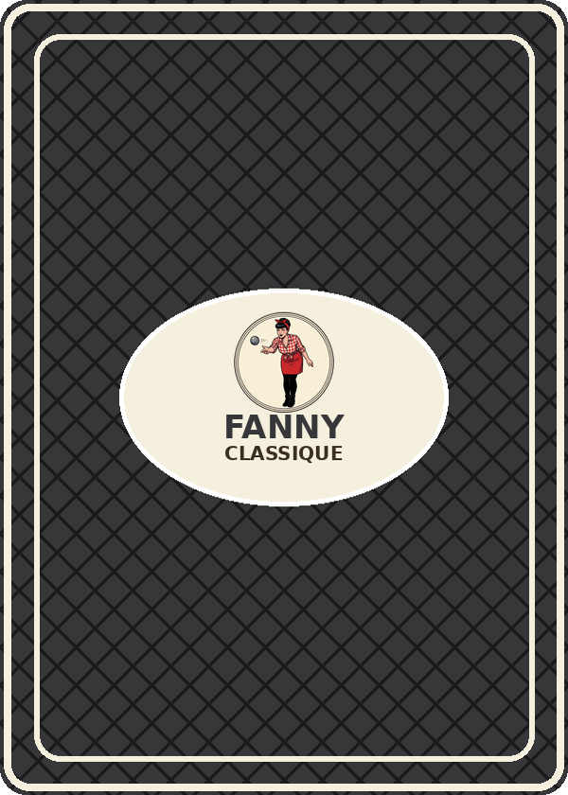
ressources/card game/assets/cards/back.png
