guiraudjb/Arducible_Fanny_Petanque_World_Tour/ressources/card game/assets/cards/theme-couture/4-spades.png

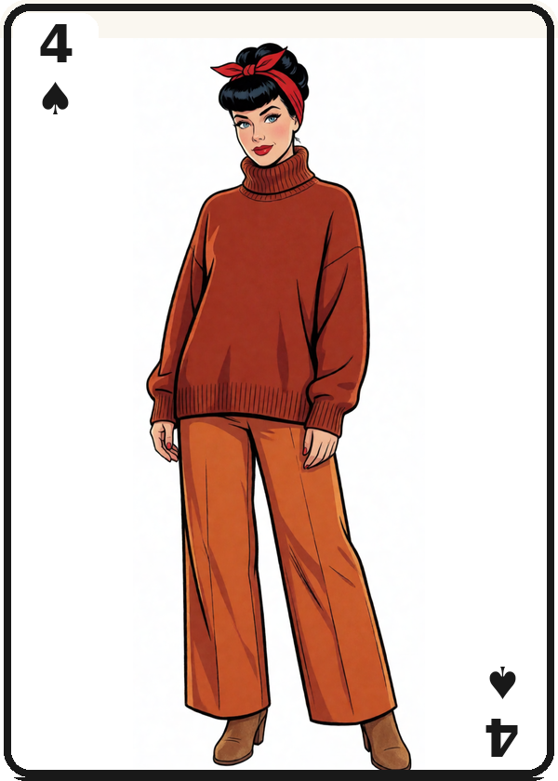
ressources/card game/assets/cards/theme-couture/4-spades.png
