guiraudjb/Arducible_Fanny_Petanque_World_Tour/ressources/card game/assets/cards/theme-fanny-vol1/3-diamonds.png

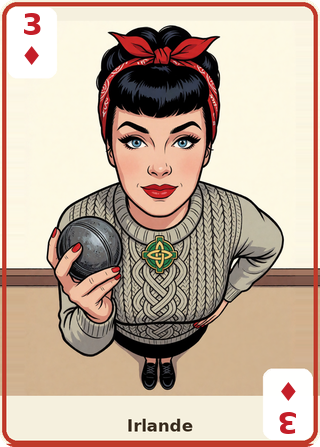
ressources/card game/assets/cards/theme-fanny-vol1/3-diamonds.png
