guiraudjb/Arducible_Fanny_Petanque_World_Tour/ressources/card game/assets/cards/theme-fanny-vol2/2-hearts.png

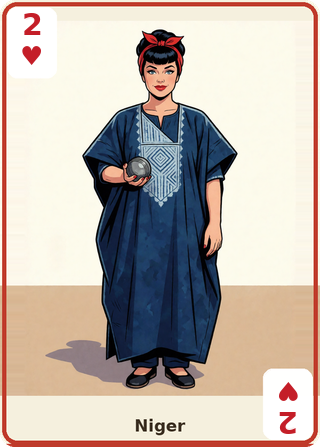
ressources/card game/assets/cards/theme-fanny-vol2/2-hearts.png
