guiraudjb/Arducible_Fanny_Petanque_World_Tour/ressources/card game/assets/cards/theme-fanny-vol2/4-clubs.png

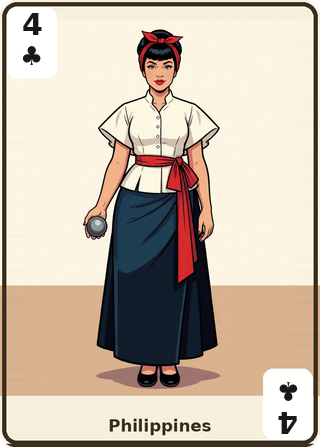
ressources/card game/assets/cards/theme-fanny-vol2/4-clubs.png
