guiraudjb/Arducible_Fanny_Petanque_World_Tour/ressources/card game/assets/cards/theme-fanny-vol2/9-spades.png

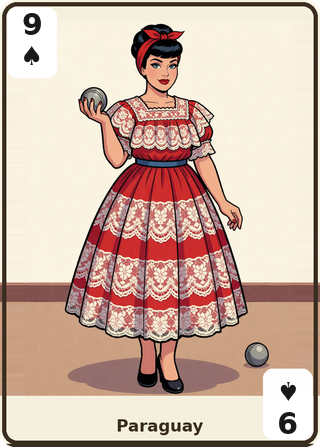
ressources/card game/assets/cards/theme-fanny-vol2/9-spades.png
