guiraudjb/Arducible_Fanny_Petanque_World_Tour/ressources/card game/assets/cards/theme-fanny-vol2/10-diamonds.png

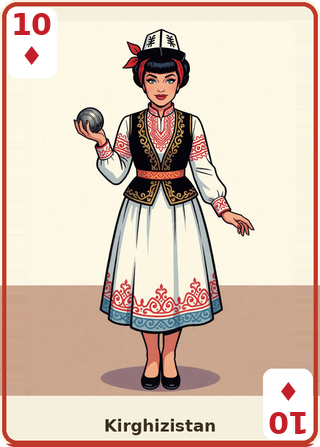
ressources/card game/assets/cards/theme-fanny-vol2/10-diamonds.png
