guiraudjb/Arducible_Fanny_Petanque_World_Tour/ressources/card game/assets/cards/theme-fanny-vol2/joker-black-2.png

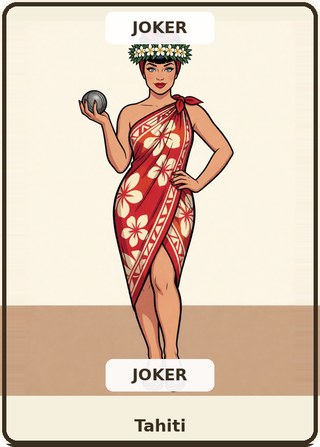
ressources/card game/assets/cards/theme-fanny-vol2/joker-black-2.png
