guiraudjb/Arducible_Fanny_Petanque_World_Tour/ressources/card game/assets/cards/theme-outfits/9-hearts.png

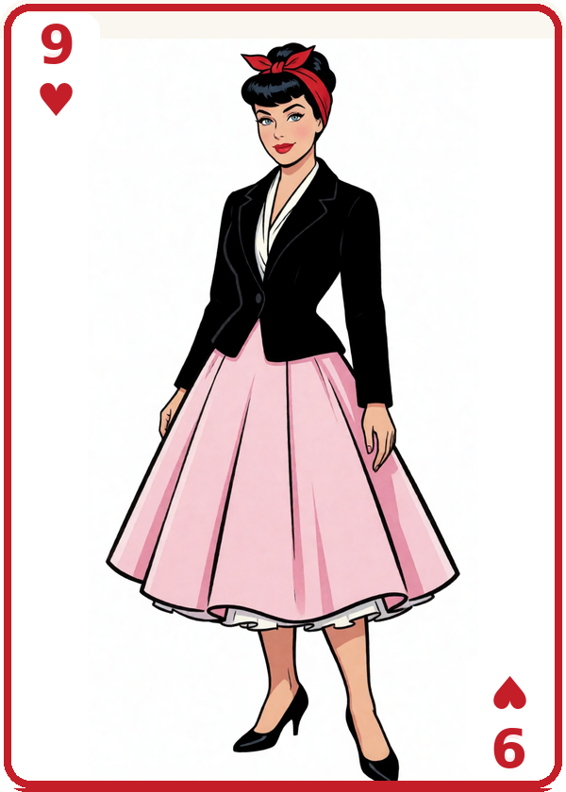
ressources/card game/assets/cards/theme-outfits/9-hearts.png
