guiraudjb/Arducible_Fanny_Petanque_World_Tour/ressources/card game/assets/cards/theme-outfits/J-diamonds.png

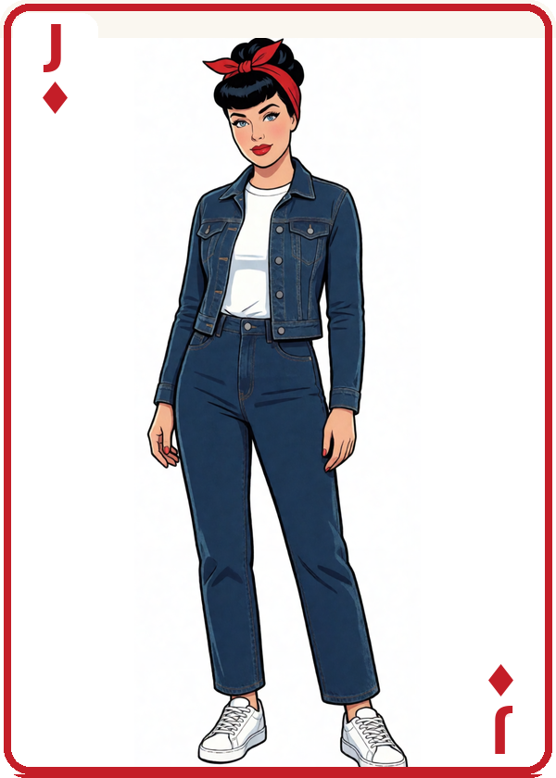
ressources/card game/assets/cards/theme-outfits/J-diamonds.png
