guiraudjb/Arducible_Fanny_Petanque_World_Tour/ressources/card game/assets/cards/theme-plage-ville/3-spades.png

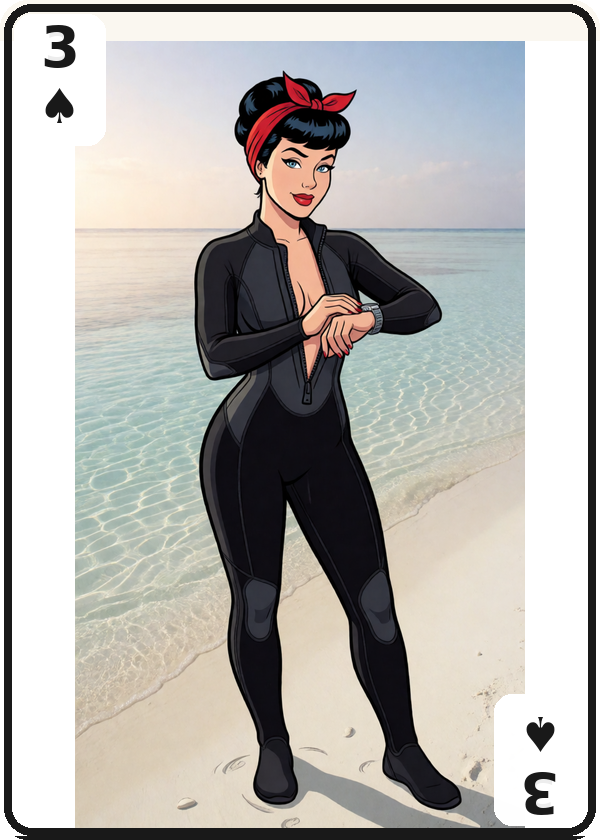
ressources/card game/assets/cards/theme-plage-ville/3-spades.png
