guiraudjb/Arducible_Fanny_Petanque_World_Tour/ressources/card game/assets/cards/theme-plage-ville/K-clubs.png

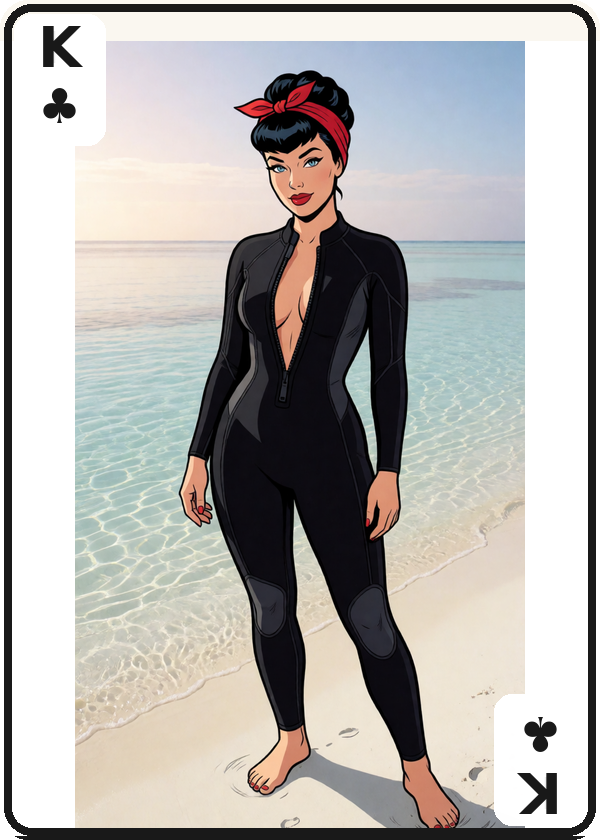
ressources/card game/assets/cards/theme-plage-ville/K-clubs.png
