guiraudjb/Arducible_Fanny_Petanque_World_Tour/ressources/card game/assets/cards/theme-sexy/4-hearts.png

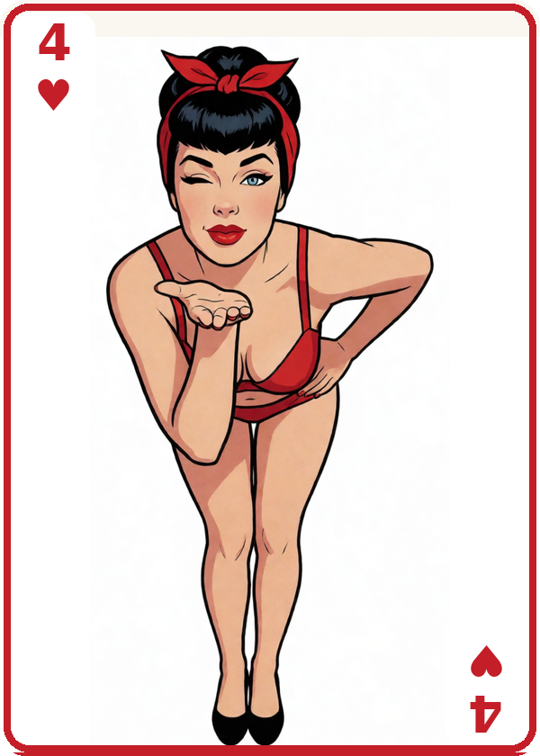
ressources/card game/assets/cards/theme-sexy/4-hearts.png
