guiraudjb/Arducible_Fanny_Petanque_World_Tour/ressources/card game/assets/cards/theme-sexy/J-clubs.png

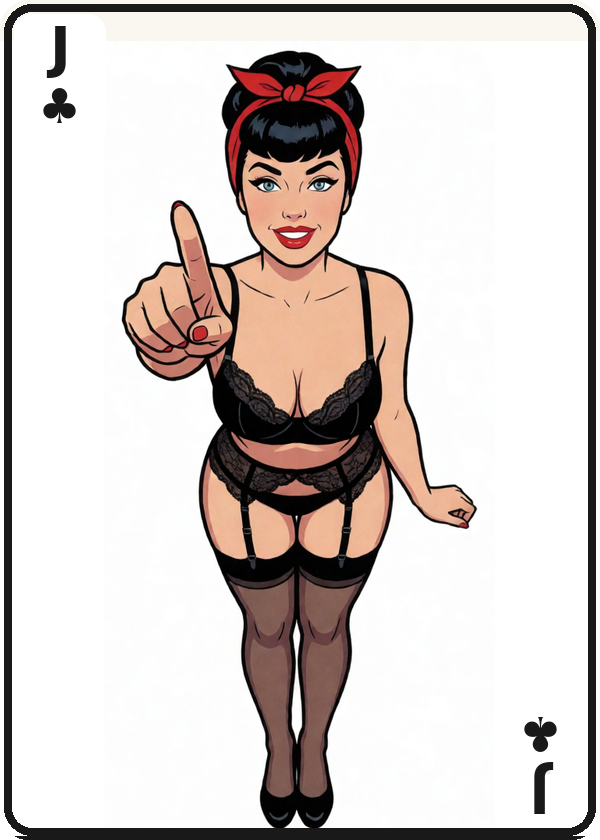
ressources/card game/assets/cards/theme-sexy/J-clubs.png
