guiraudjb/Arducible_Fanny_Petanque_World_Tour/ressources/card game/assets/cards/theme-sport/8-diamonds.png

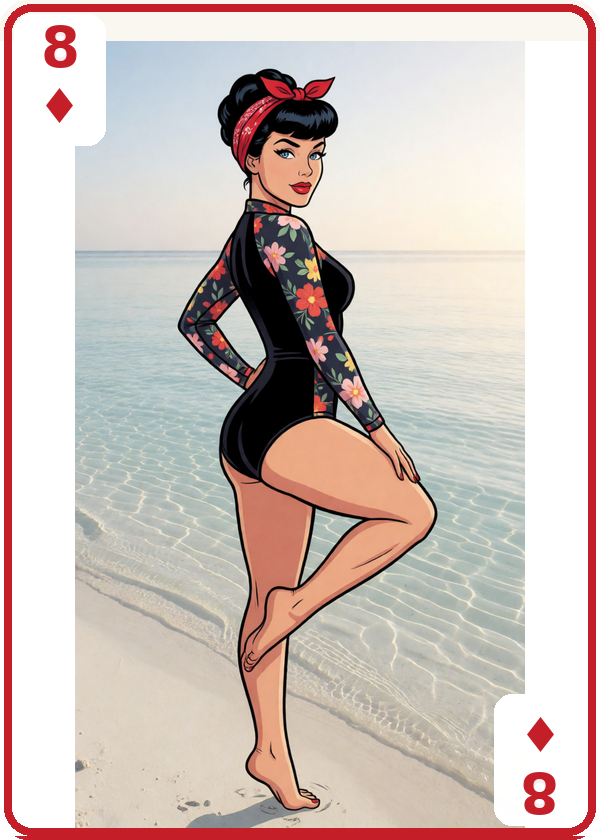
ressources/card game/assets/cards/theme-sport/8-diamonds.png
