guiraudjb/Arducible_Fanny_Petanque_World_Tour/ressources/card game/assets/cards/theme-voyage/10-spades.png

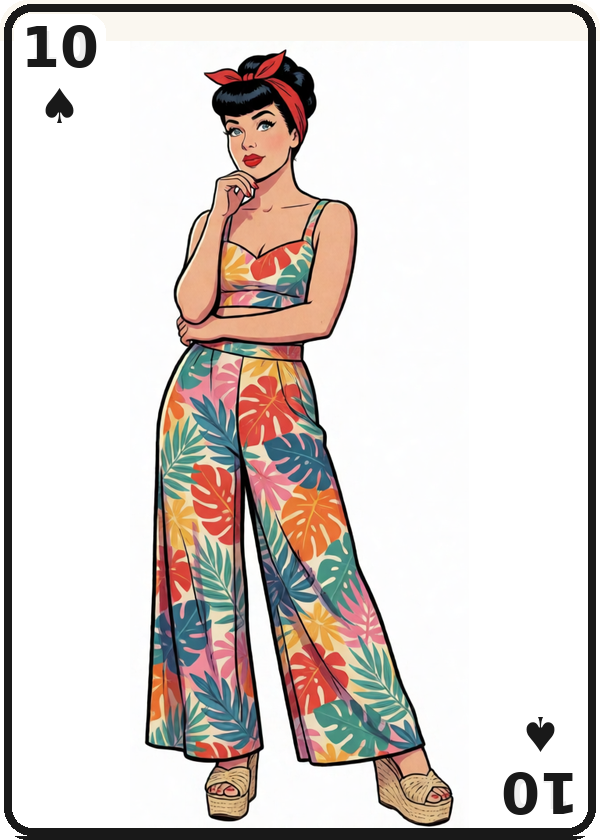
ressources/card game/assets/cards/theme-voyage/10-spades.png
