guiraudjb/Arducible_Fanny_Petanque_World_Tour/ressources/card game/assets/cards/theme-voyage/A-clubs.png

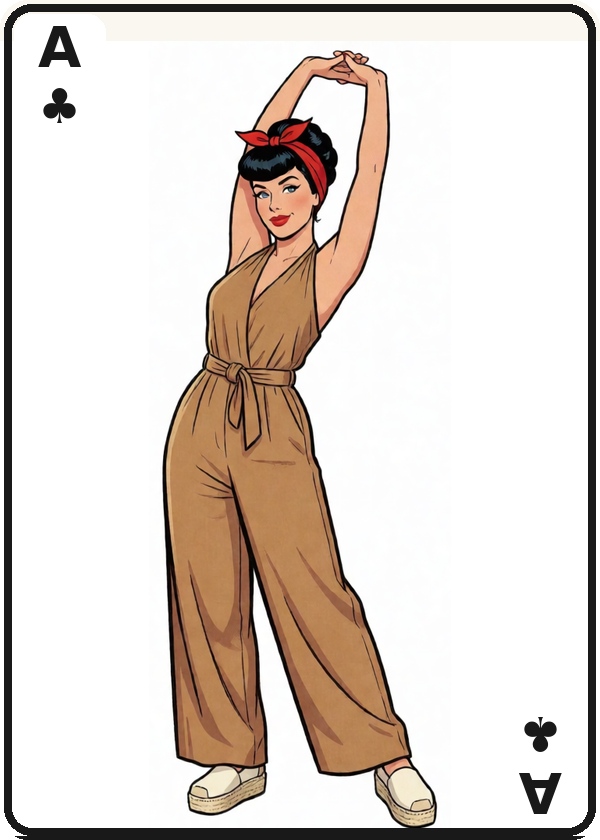
ressources/card game/assets/cards/theme-voyage/A-clubs.png
