guiraudjb/Arducible_Fanny_Petanque_World_Tour/ressources/card game/assets/cards/theme-voyage/K-clubs.png

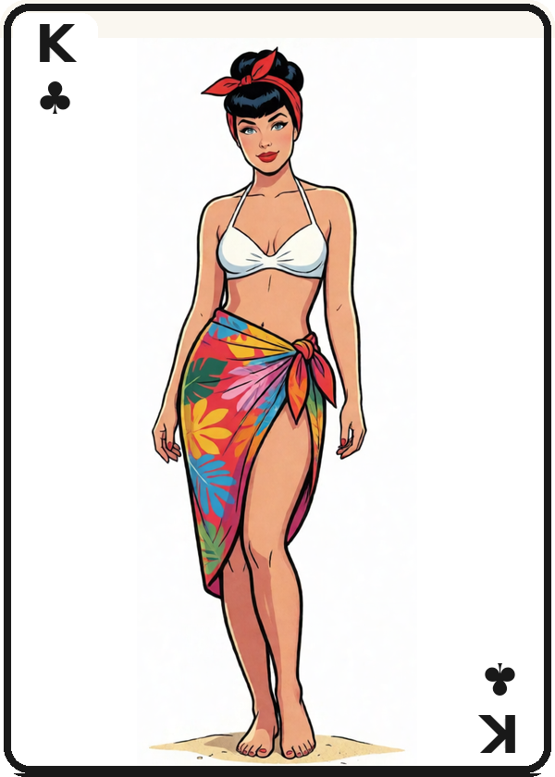
ressources/card game/assets/cards/theme-voyage/K-clubs.png
