guiraudjb/Arducible_Fanny_Petanque_World_Tour/ressources/card game/assets/opponent/stage-5.png

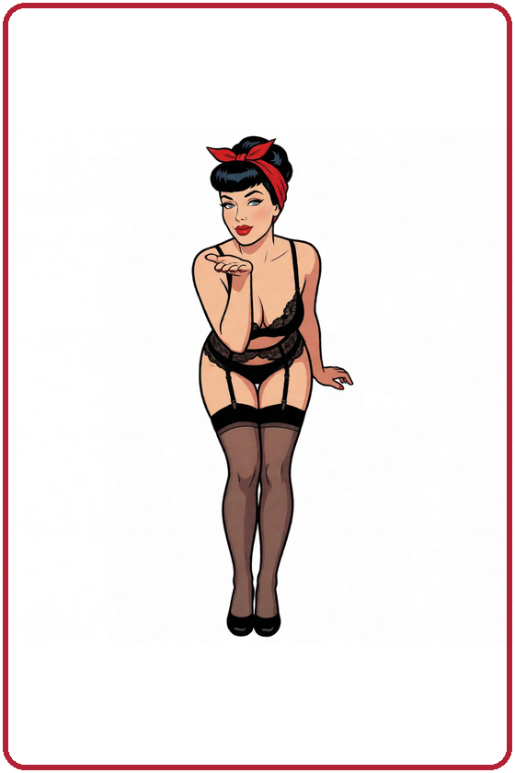
ressources/card game/assets/opponent/stage-5.png
