guiraudjb/Arducible_Fanny_Petanque_World_Tour/ressources/card game/assets/previews/baccara.jpg

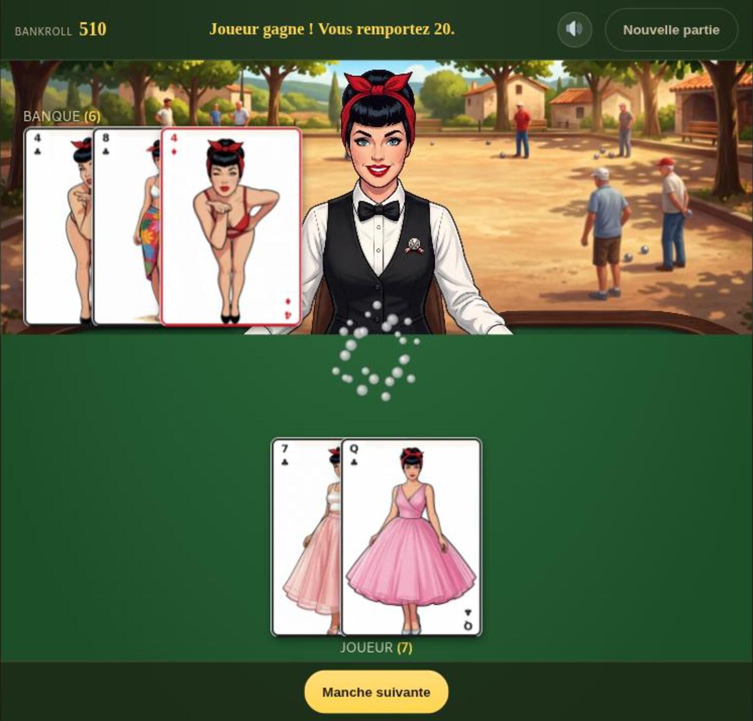
ressources/card game/assets/previews/baccara.jpg
