guiraudjb/Arducible_Fanny_Petanque_World_Tour/ressources/card game/assets/previews/blackjack.jpg

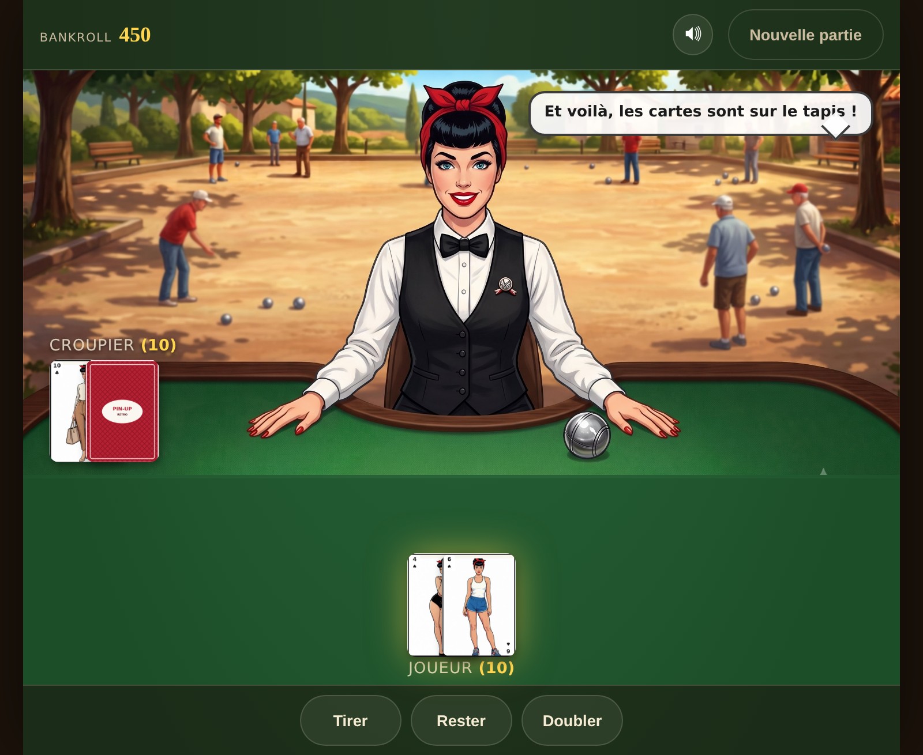
ressources/card game/assets/previews/blackjack.jpg
