guiraudjb/Arducible_Fanny_Petanque_World_Tour/ressources/card game/assets/previews/craps.jpg

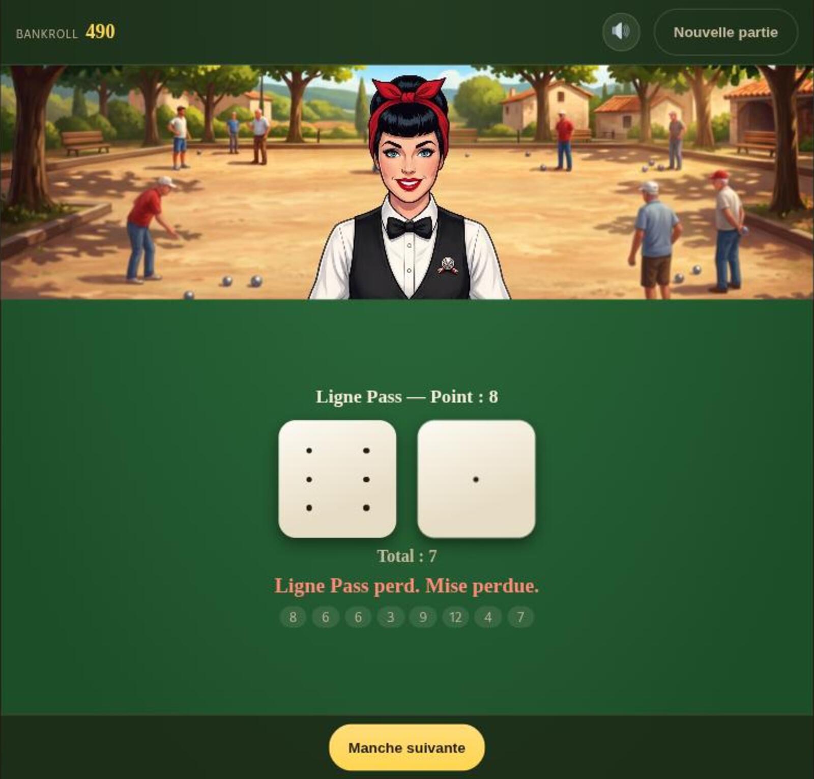
ressources/card game/assets/previews/craps.jpg
