guiraudjb/Arducible_Fanny_Petanque_World_Tour/ressources/card game/assets/previews/lettres.jpg

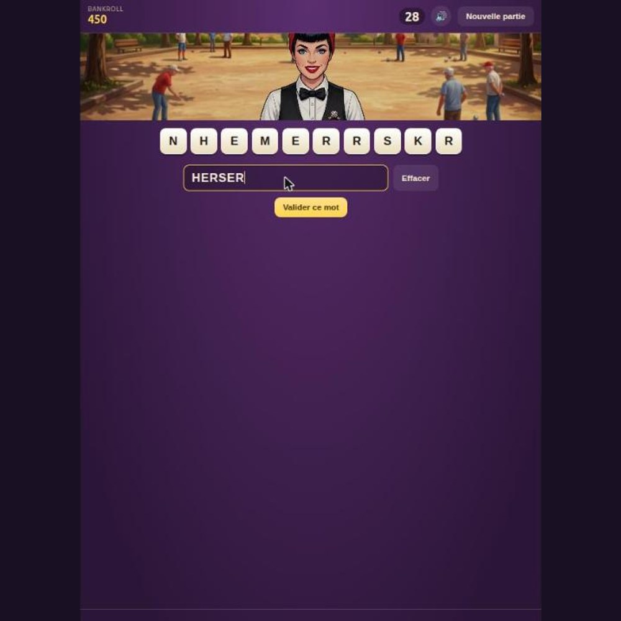
ressources/card game/assets/previews/lettres.jpg
