guiraudjb/Arducible_Fanny_Petanque_World_Tour/ressources/card game/assets/table/casino-cover.jpg

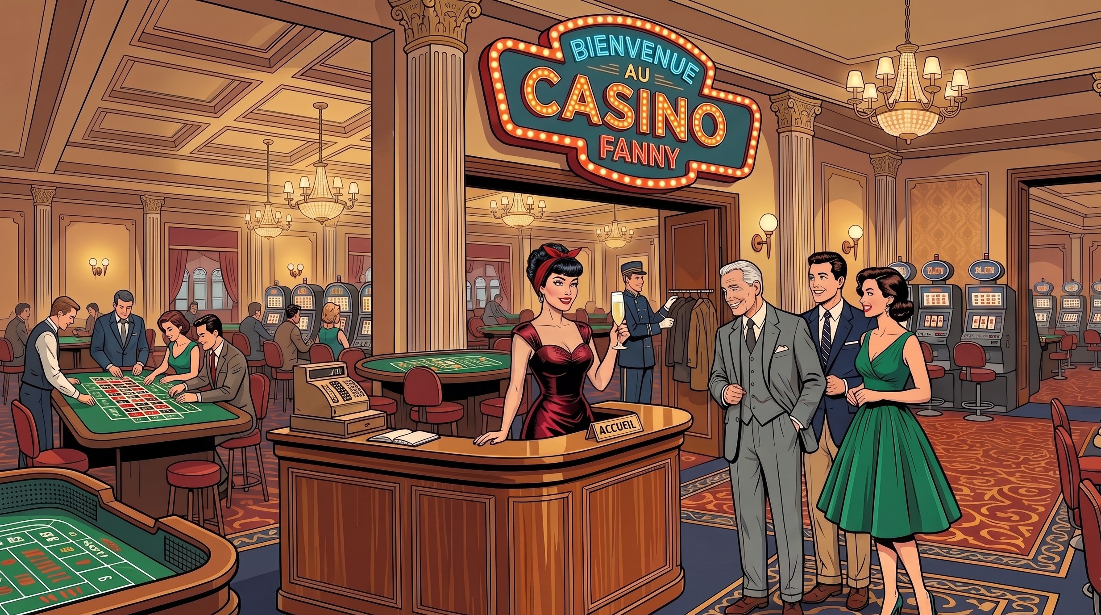
ressources/card game/assets/table/casino-cover.jpg
