guiraudjb/Arducible_Fanny_Petanque_World_Tour/ressources/card game/assets/table/fanny_intello_lunettes.png

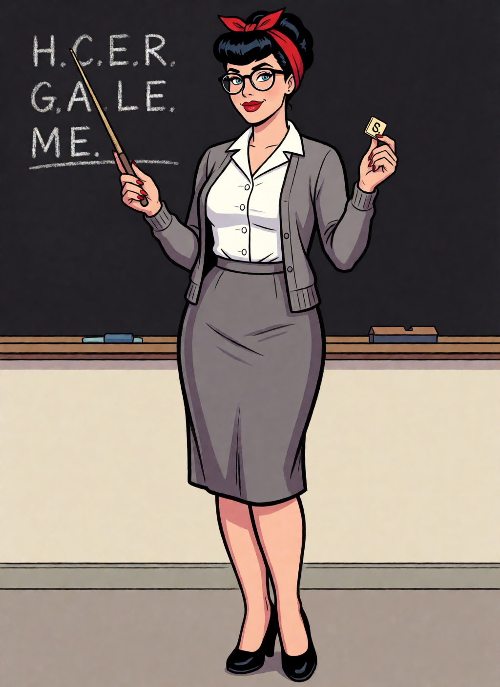
ressources/card game/assets/table/fanny_intello_lunettes.png
