guiraudjb/Arducible_Fanny_Petanque_World_Tour/videos/poster-demo-cible.jpg

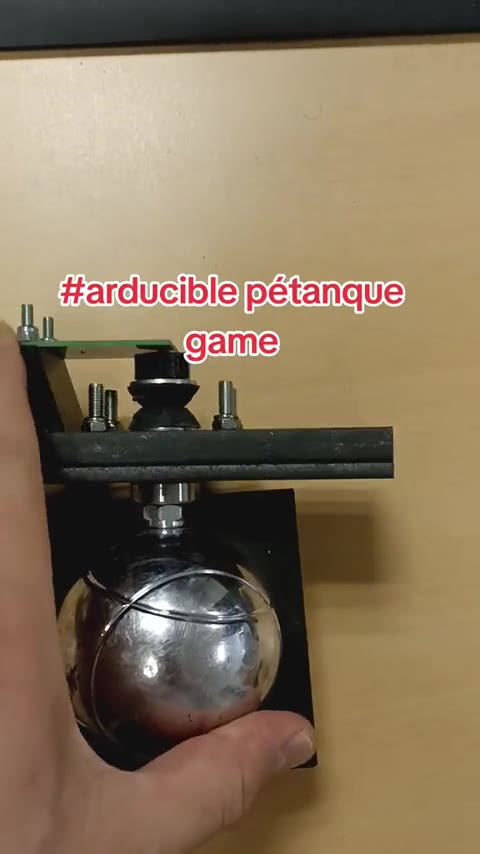
videos/poster-demo-cible.jpg
