guiraudjb/Arducible_Fanny_Petanque_World_Tour/videos/poster-demo-evenement.jpg

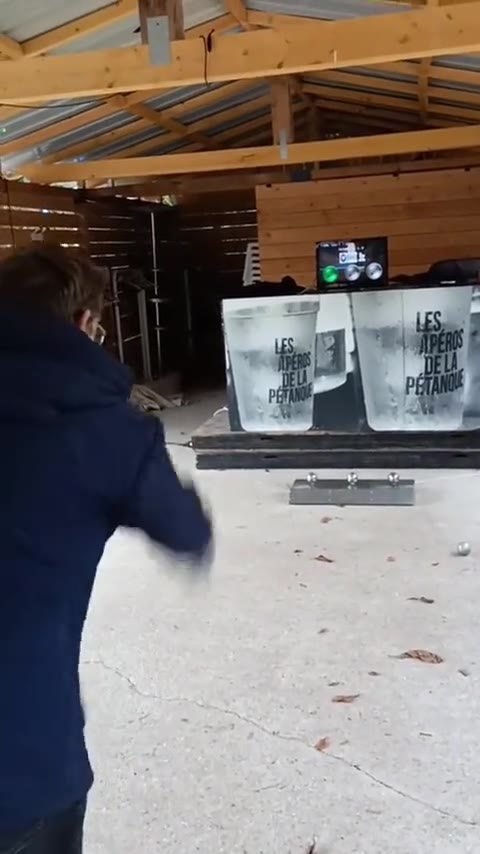
videos/poster-demo-evenement.jpg
