guiraudjb/Arducible_Fanny_Petanque_World_Tour/videos/poster-demo-reportage.jpg

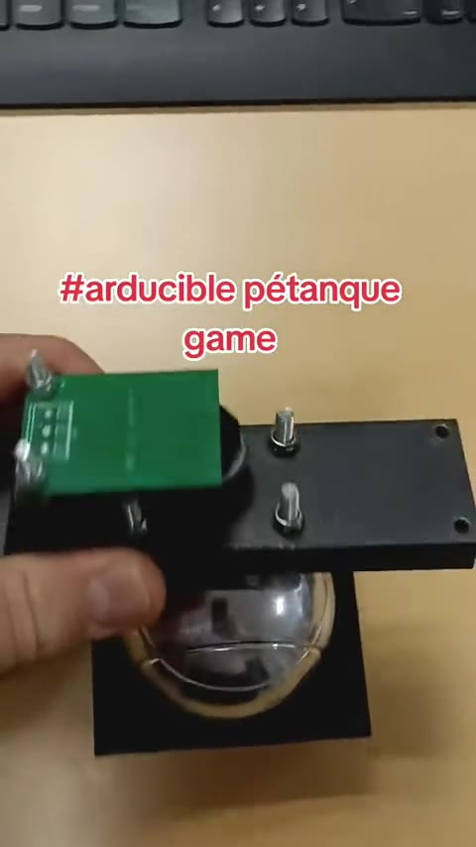
videos/poster-demo-reportage.jpg
