guiraudjb/Arducible_Fanny_Petanque_World_Tour/videos/poster-percage-boule.jpg

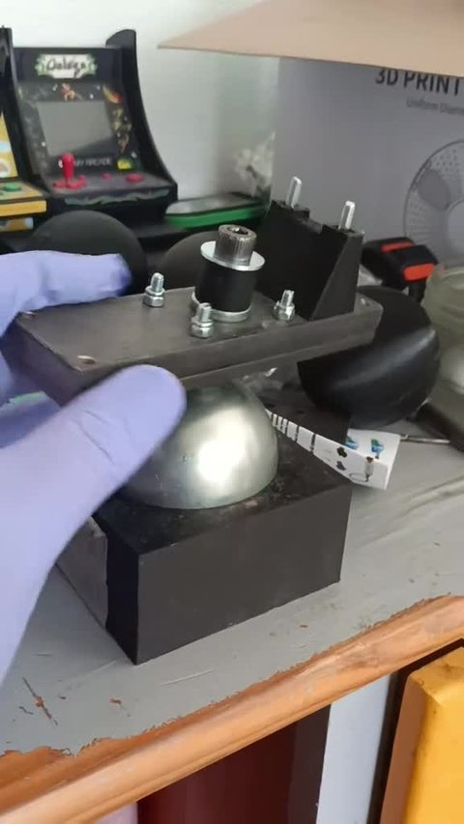
videos/poster-percage-boule.jpg
