guiraudjb/Arducible_Fanny_Petanque_World_Tour/videos/poster-teaser-arducible.jpg

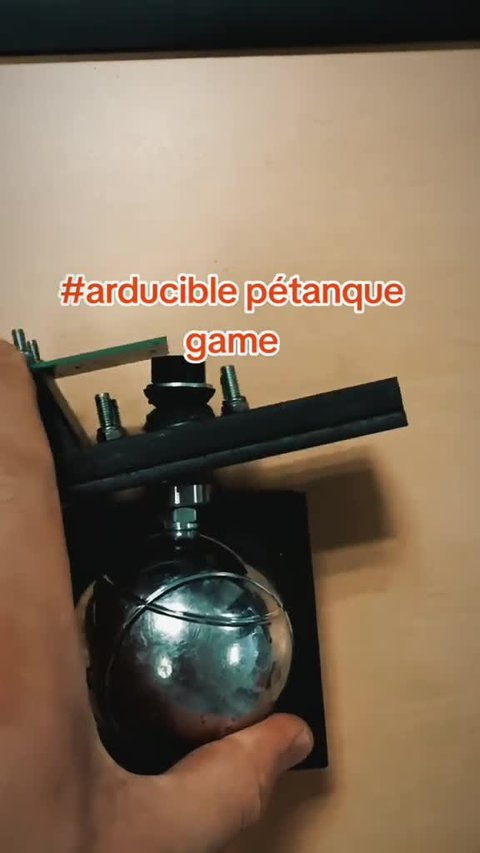
videos/poster-teaser-arducible.jpg
