guiraudjb/Arducible_Fanny_Petanque_World_Tour/videos/poster-teaser.jpg

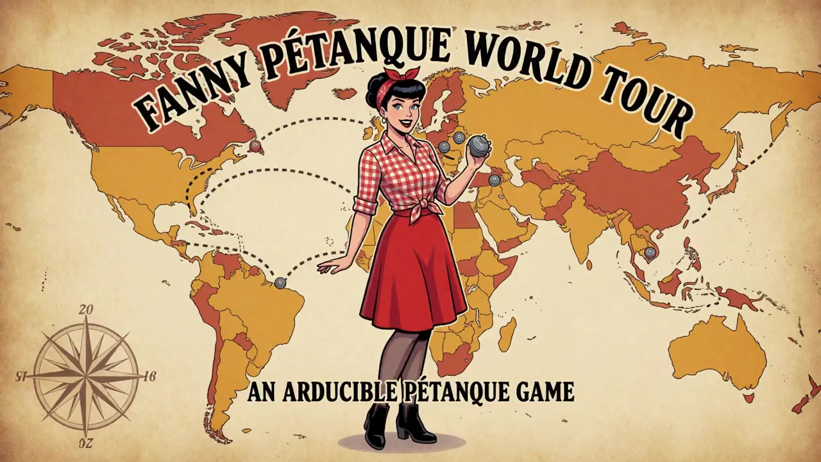
videos/poster-teaser.jpg
