guiraudjb/Arducible_Fanny_Petanque_World_Tour/hardware/pcb/bom-jlcpcb.png

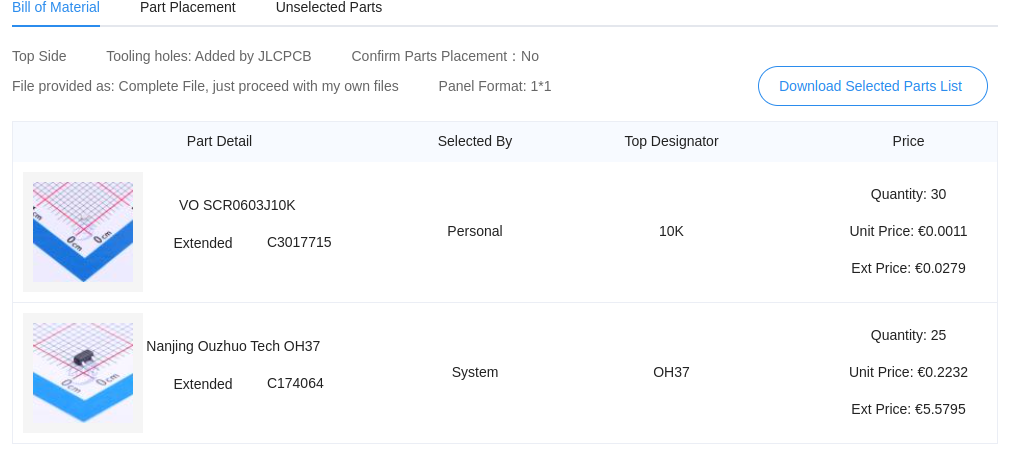
hardware/pcb/bom-jlcpcb.png
