guiraudjb/Arducible_Fanny_Petanque_World_Tour/ressources/modélisation/modelisation/parts/Controller/Capture du 2024-08-14 20-32-25.png

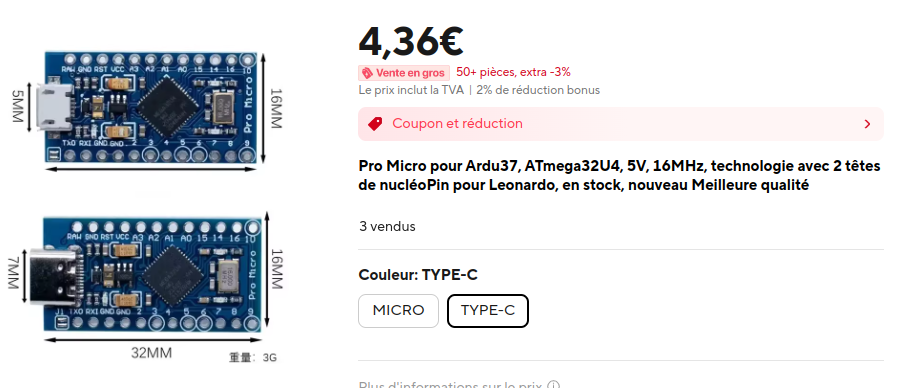
ressources/modélisation/modelisation/parts/Controller/Capture du 2024-08-14 20-32-25.png
