guiraudjb/Arducible_Fanny_Petanque_World_Tour/ressources/modélisation/modelisation/parts/Controller/schéma.png

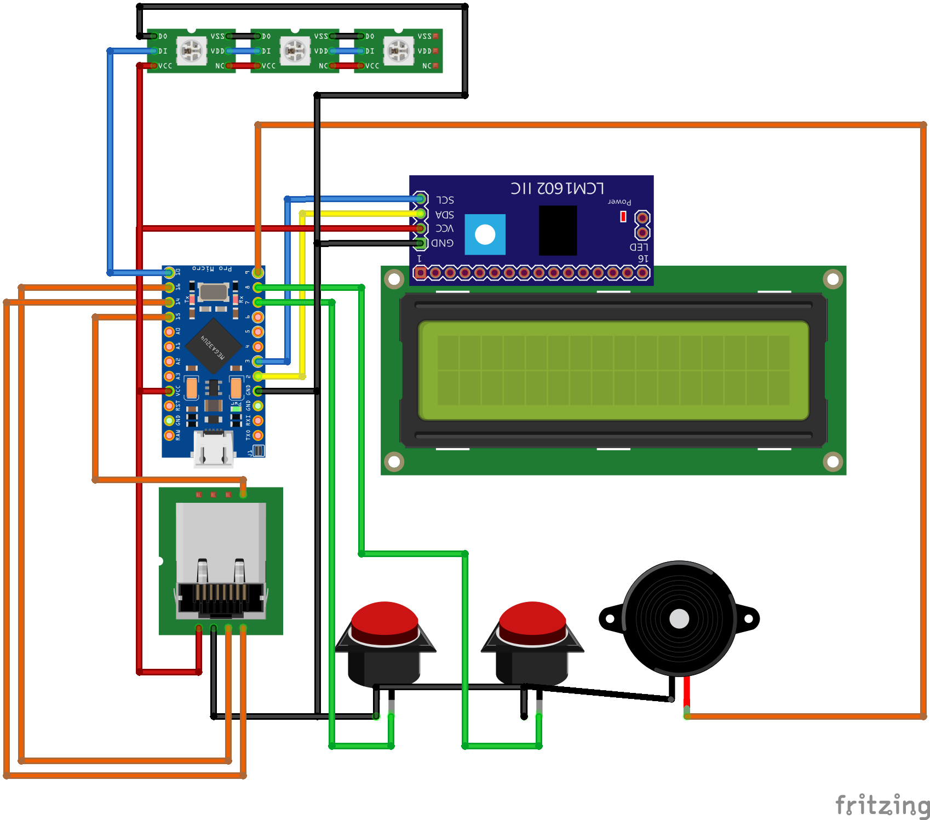
ressources/modélisation/modelisation/parts/Controller/schéma.png
