guiraudjb/Arducible_Fanny_Petanque_World_Tour/ressources/modélisation/Doc final/articulation/TAMPON RESSORT CR60 ∅20 8,5X15MM 60SHA/tamponressort.FCStd

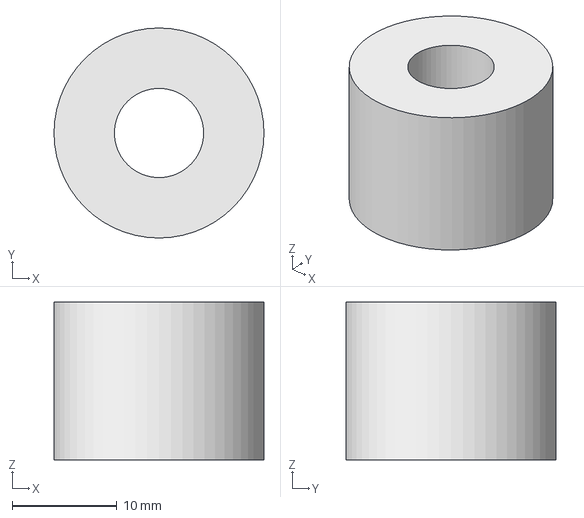
[picture p192: CAD file, 2026-07-06]
ressources/modélisation/Doc final/articulation/TAMPON RESSORT CR60 ∅20 8,5X15MM 60SHA/tamponressort.FCStd
20.0 x 20.0 x 15.0 mm
