guiraudjb/Arducible_Fanny_Petanque_World_Tour/ressources/modélisation/Doc final/articulation/vis4x30/vis4x30.FCStd

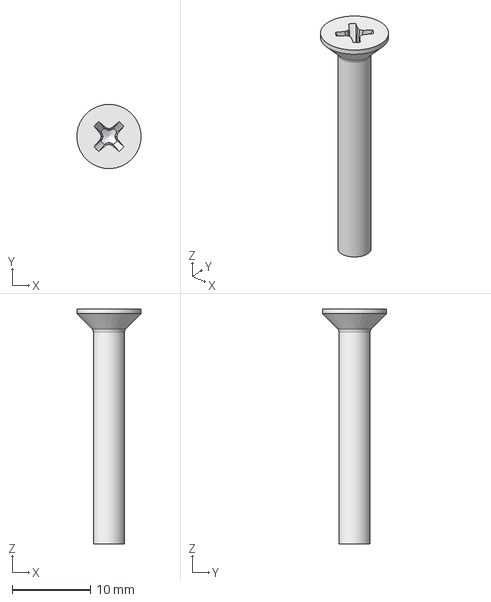
[picture p193: CAD file, 2026-07-06]
ressources/modélisation/Doc final/articulation/vis4x30/vis4x30.FCStd
8.19 x 8.20 x 30.0 mm
