guiraudjb/Arducible_Fanny_Petanque_World_Tour/ressources/modélisation/Doc final/AxeArticulation/Vis métaux CHC BTR Clé de 6 HC6 M8X70 Filetée sur 22 Classe 12.9 Acier brut.FCStd

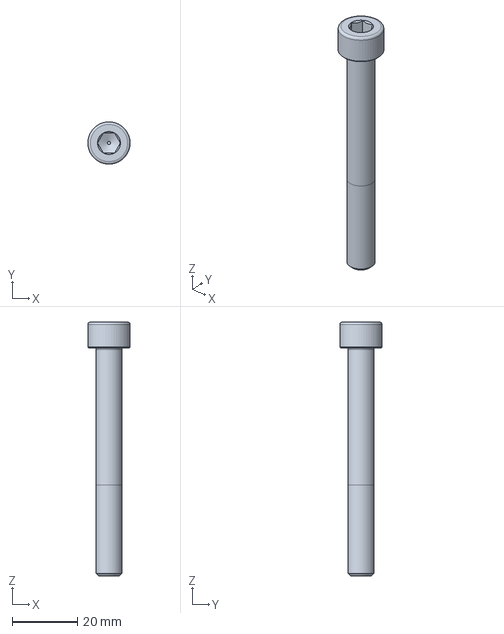
[picture p194: CAD file, 2026-07-06]
ressources/modélisation/Doc final/AxeArticulation/Vis métaux CHC BTR Clé de 6 HC6 M8X70 Filetée sur 22 Classe 12.9 Acier brut.FCStd
13.0 x 13.0 x 78.0 mm
