guiraudjb/Arducible_Fanny_Petanque_World_Tour/ressources/modélisation/Doc final/BoulePétanque/boulecreuseV2.FCStd

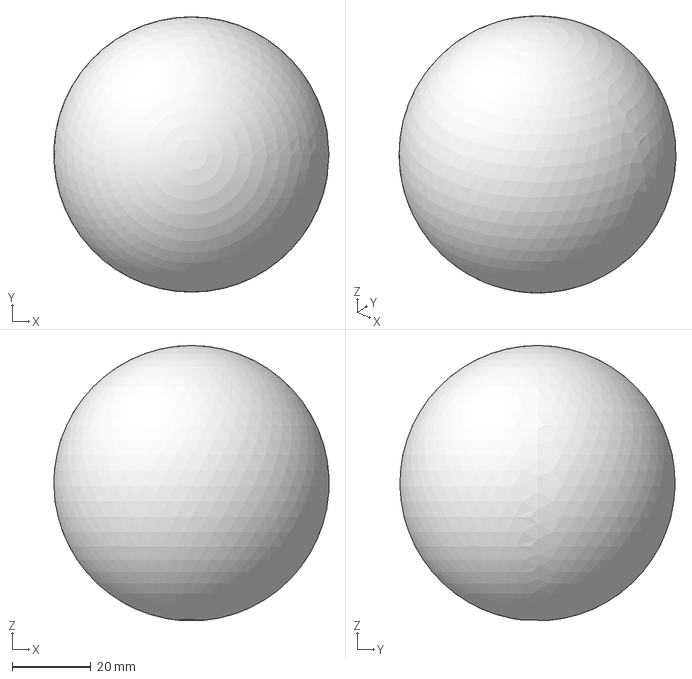
[picture p195: CAD file, 2026-07-06]
ressources/modélisation/Doc final/BoulePétanque/boulecreuseV2.FCStd
69.9 x 70.0 x 69.9 mm
