guiraudjb/Arducible_Fanny_Petanque_World_Tour/ressources/modélisation/Doc final/ChassisV7-plateau.step

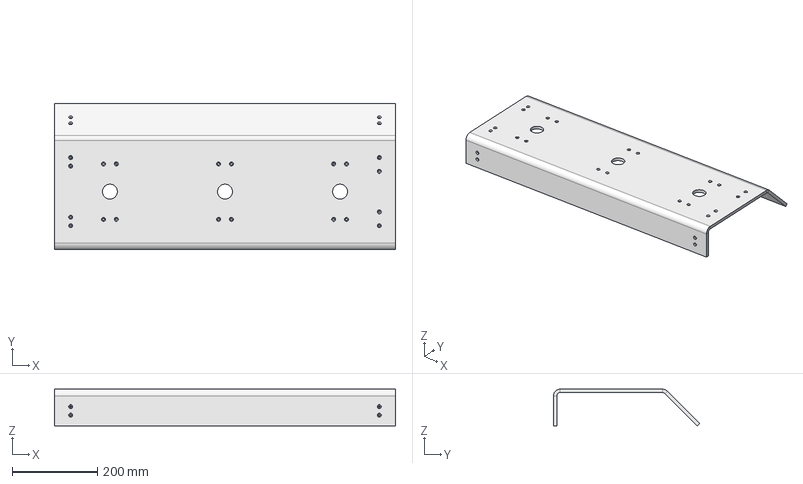
[picture p196: CAD file, 2026-07-06]
ressources/modélisation/Doc final/ChassisV7-plateau.step
800.0 x 343.0 x 86.0 mm
