guiraudjb/Arducible_Fanny_Petanque_World_Tour/ressources/modélisation/Doc final/Ecrou frein m4/EcrouM4.FCStd

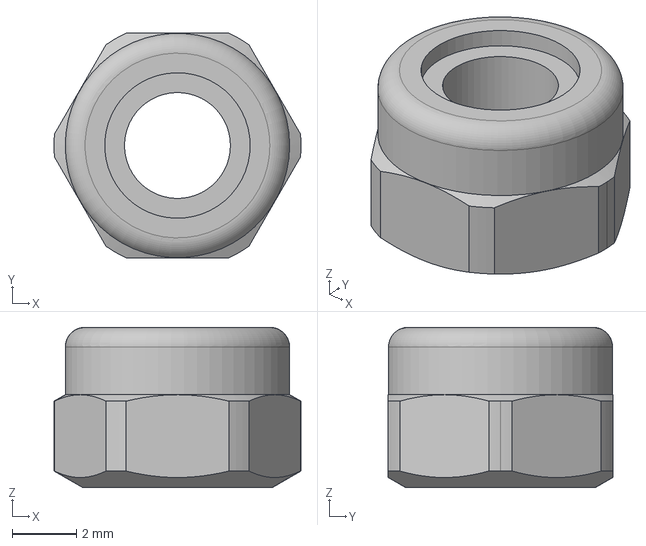
[picture p197: CAD file, 2026-07-06]
ressources/modélisation/Doc final/Ecrou frein m4/EcrouM4.FCStd
7.70 x 7.00 x 5.00 mm
