guiraudjb/Arducible_Fanny_Petanque_World_Tour/ressources/modélisation/Doc final/Ecrou frein M8/EcrouM8.FCStd

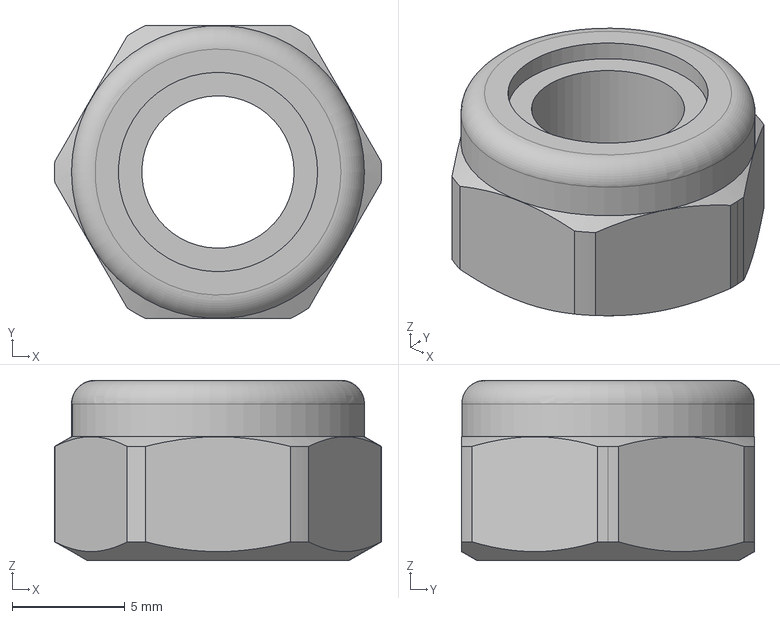
[picture p198: CAD file, 2026-07-06]
ressources/modélisation/Doc final/Ecrou frein M8/EcrouM8.FCStd
14.5 x 13.0 x 8.00 mm
