guiraudjb/Arducible_Fanny_Petanque_World_Tour/ressources/modélisation/Doc final/InterfaceAxeAimant/interfaceAxeAimant4mm.FCStd

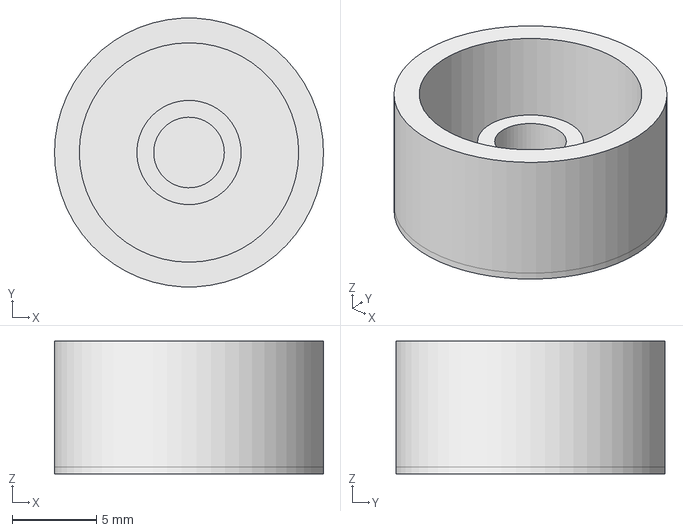
[picture p199: CAD file, 2026-07-06]
ressources/modélisation/Doc final/InterfaceAxeAimant/interfaceAxeAimant4mm.FCStd
16.0 x 16.0 x 7.90 mm
