guiraudjb/Arducible_Fanny_Petanque_World_Tour/ressources/modélisation/Doc final/Rondelle8x22x1,5/rondelle8x22x1,5.FCStd

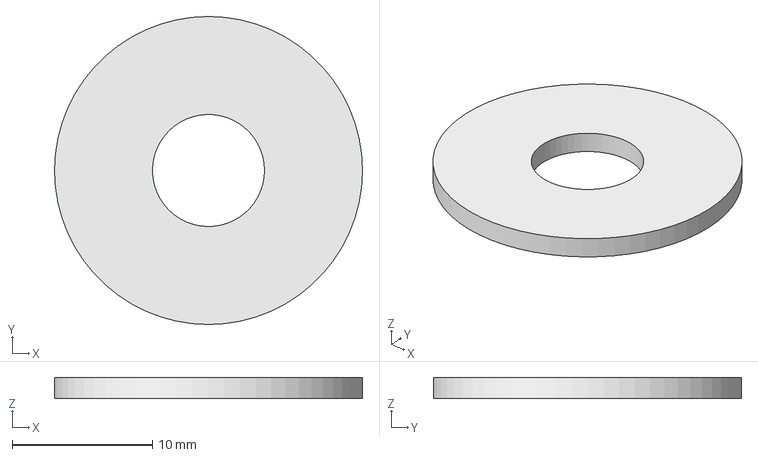
[picture p200: CAD file, 2026-07-06]
ressources/modélisation/Doc final/Rondelle8x22x1,5/rondelle8x22x1,5.FCStd
22.0 x 22.0 x 1.50 mm
