guiraudjb/Arducible_Fanny_Petanque_World_Tour/ressources/modélisation/Doc final/vis/Vismetauxtetefraise4x25/vis4x25.FCStd

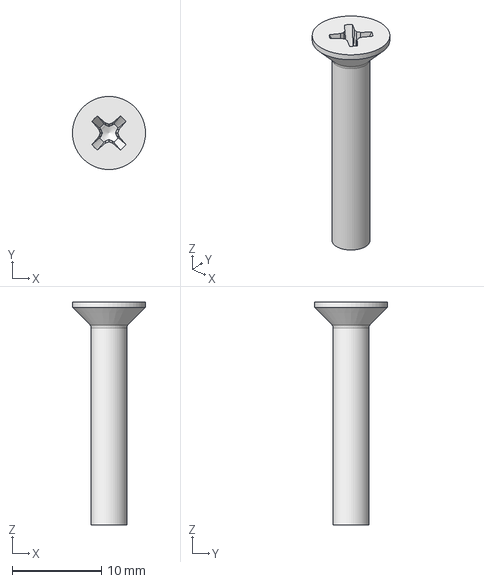
[picture p201: CAD file, 2026-07-06]
ressources/modélisation/Doc final/vis/Vismetauxtetefraise4x25/vis4x25.FCStd
8.19 x 8.20 x 25.0 mm
