guiraudjb/Arducible_Fanny_Petanque_World_Tour/ressources/modélisation/Doc final/visSupportPlaqueElectronique/Vis métaux Tête fraisée TF Pozi 2 M4X50 Acier zingué.FCStd

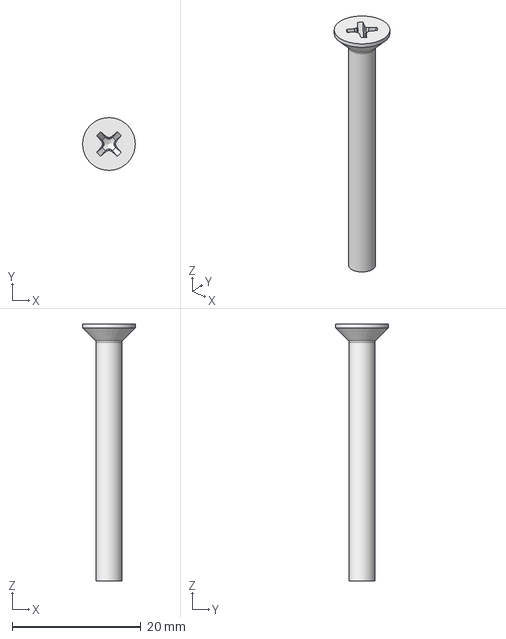
[picture p202: CAD file, 2026-07-06]
ressources/modélisation/Doc final/visSupportPlaqueElectronique/Vis métaux Tête fraisée TF Pozi 2 M4X50 Acier zingué.FCStd
8.19 x 8.20 x 40.0 mm
