guiraudjb/Arducible_Fanny_Petanque_World_Tour/ressources/modélisation/modelisation/parts/BoulePétanque/boulediam70.FCStd

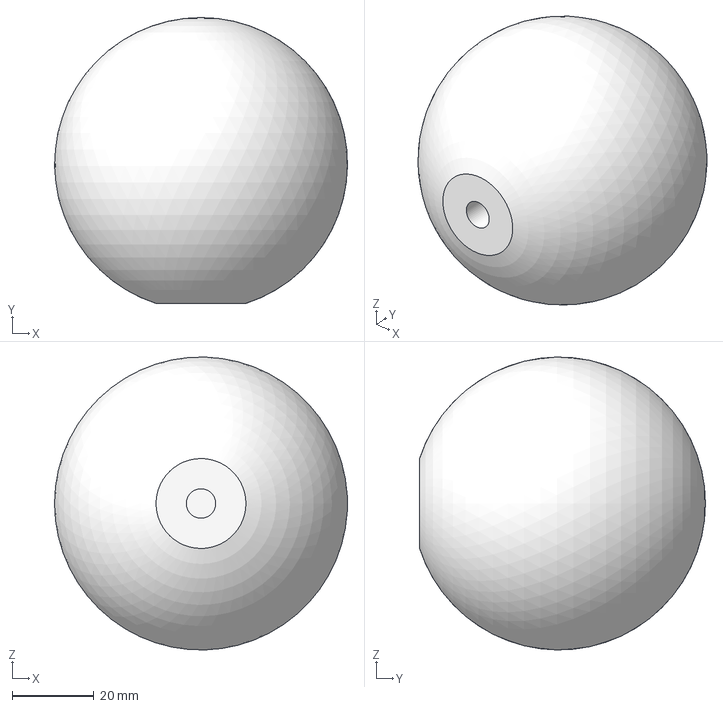
[picture p203: CAD file, 2026-07-06]
ressources/modélisation/modelisation/parts/BoulePétanque/boulediam70.FCStd
71.7 x 70.0 x 71.7 mm
