guiraudjb/Arducible_Fanny_Petanque_World_Tour/ressources/modélisation/modelisation/parts/Chassis/chassisv4/parts/DocumentFabricationChassisDecoupeLaserFraisageTaraudagePrototypeV1/plastron/plastron chassisV4-Body.step

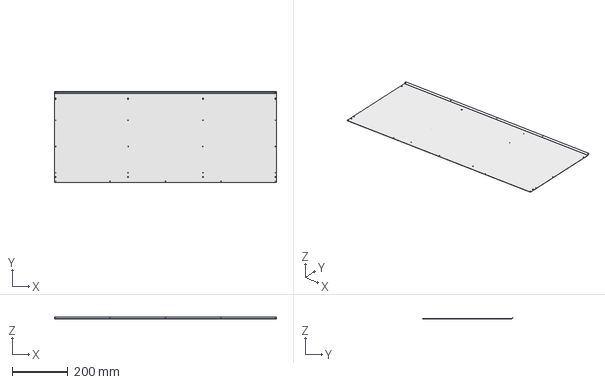
[picture p204: CAD file, 2026-07-06]
ressources/modélisation/modelisation/parts/Chassis/chassisv4/parts/DocumentFabricationChassisDecoupeLaserFraisageTaraudagePrototypeV1/plastron/plastron chassisV4-Body.step
800.0 x 326.5 x 6.24 mm
