guiraudjb/Arducible_Fanny_Petanque_World_Tour/ressources/modélisation/modelisation/parts/Chassis/chassisv4/parts/DocumentFabricationChassisDecoupeLaserFraisageTaraudagePrototypeV1/plateau/ChassisPlateauV4-Body.step

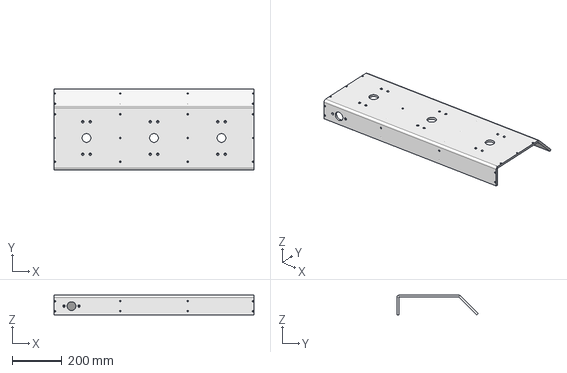
[picture p205: CAD file, 2026-07-06]
ressources/modélisation/modelisation/parts/Chassis/chassisv4/parts/DocumentFabricationChassisDecoupeLaserFraisageTaraudagePrototypeV1/plateau/ChassisPlateauV4-Body.step
800.0 x 325.9 x 79.0 mm
