guiraudjb/Arducible_Fanny_Petanque_World_Tour/ressources/modélisation/modelisation/parts/Chassis/chassisv4/parts/DocumentFabricationChassisDecoupeLaserFraisageTaraudagePrototypeV1/Support chassis/supportvChassisV5-Body001.step

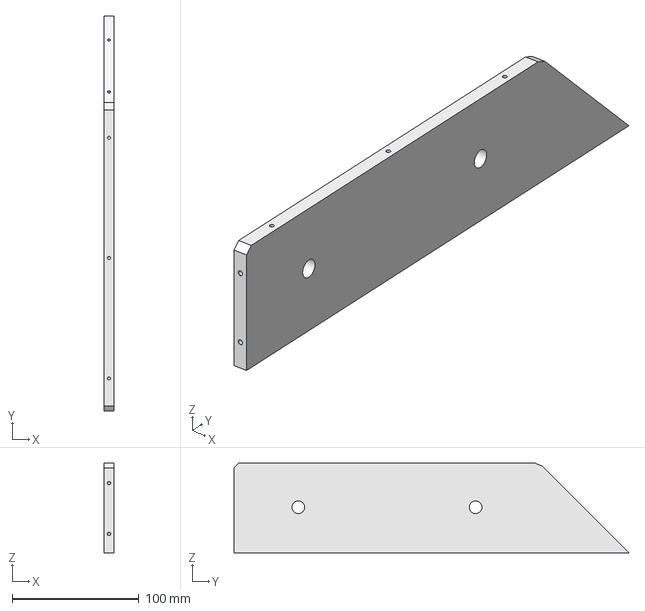
[picture p206: CAD file, 2026-07-06]
ressources/modélisation/modelisation/parts/Chassis/chassisv4/parts/DocumentFabricationChassisDecoupeLaserFraisageTaraudagePrototypeV1/Support chassis/supportvChassisV5-Body001.step
8.00 x 311.9 x 70.8 mm
