guiraudjb/Arducible_Fanny_Petanque_World_Tour/ressources/modélisation/modelisation/parts/Controller/Boitier Controller/boitier/boitierJeufreecad020.FCStd

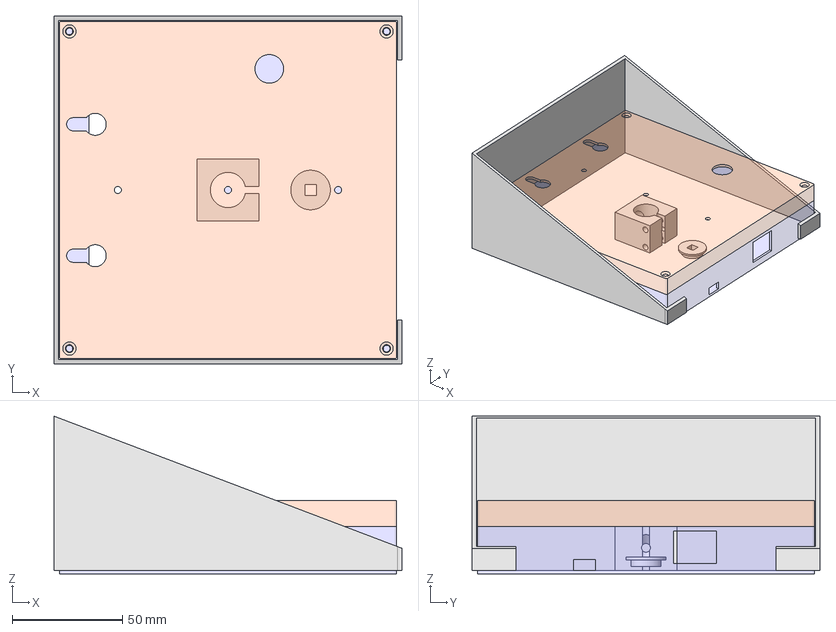
[picture p207: CAD file, 2026-07-06]
ressources/modélisation/modelisation/parts/Controller/Boitier Controller/boitier/boitierJeufreecad020.FCStd
158.0 x 158.0 x 71.6 mm
Corps
casquette
