guiraudjb/Arducible_Fanny_Petanque_World_Tour/ressources/modélisation/modelisation/parts/vis/Vis métaux Tête fraisée TF Pozi 2 M4X50 Acier zingué.FCStd

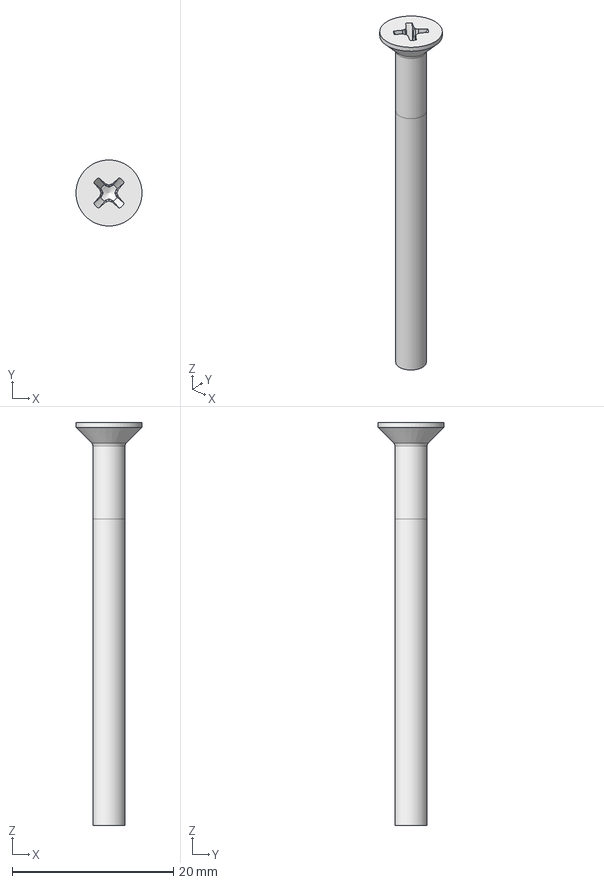
[picture p208: CAD file, 2026-07-06]
ressources/modélisation/modelisation/parts/vis/Vis métaux Tête fraisée TF Pozi 2 M4X50 Acier zingué.FCStd
8.19 x 8.20 x 50.0 mm
