guiraudjb/Arducible_Fanny_Petanque_World_Tour/hardware/cad/rondelle-8x22x1-5.FCStd

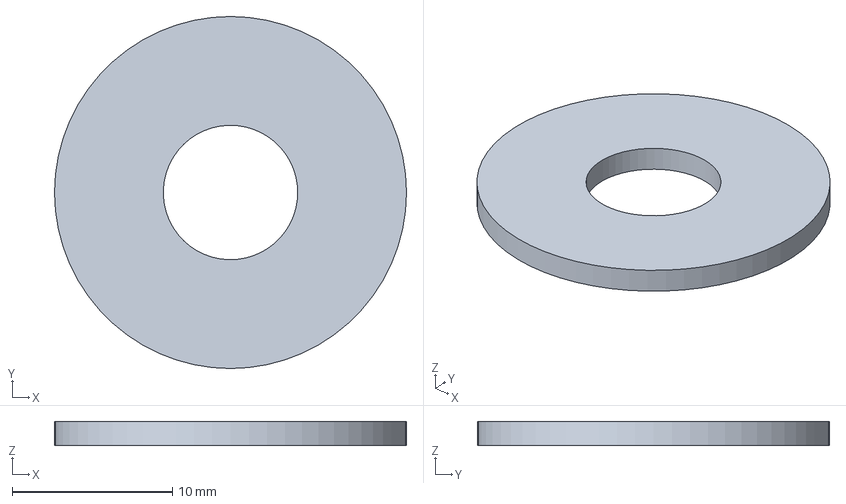
[picture p209: CAD file, 2026-07-20]
hardware/cad/rondelle-8x22x1-5.FCStd
22.0 x 22.0 x 1.50 mm
