guiraudjb/Arducible_Fanny_Petanque_World_Tour/ressources/modélisation/Doc final/articulation/EntretoiseCarteElectronique/entretoisesV5.FCStd

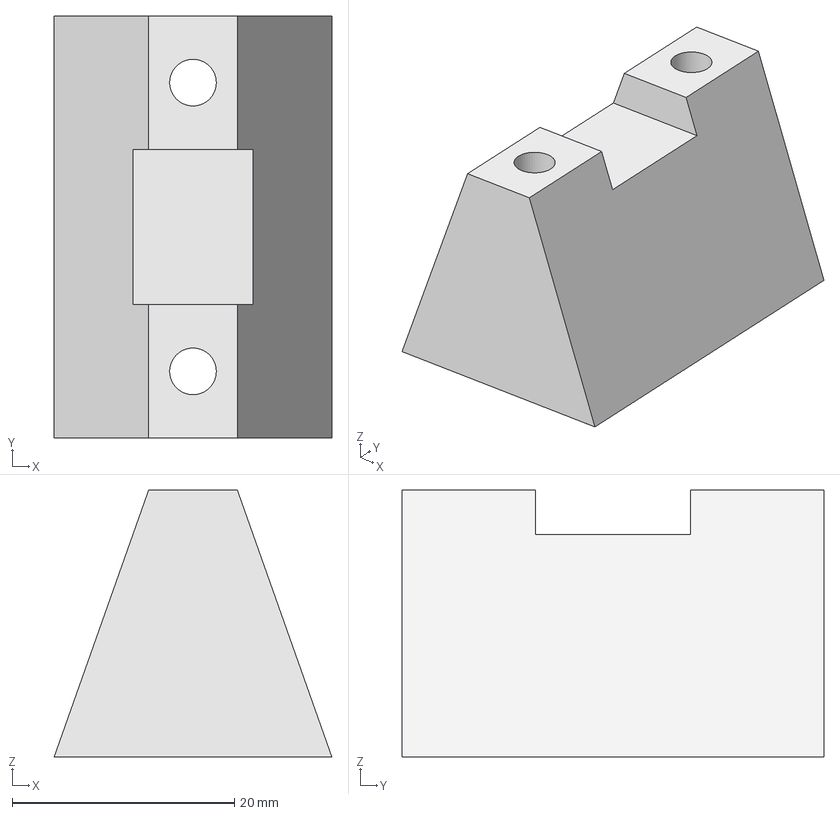
[picture p210: CAD file, 2026-07-06]
ressources/modélisation/Doc final/articulation/EntretoiseCarteElectronique/entretoisesV5.FCStd
25.0 x 38.0 x 24.0 mm
