guiraudjb/Arducible_Fanny_Petanque_World_Tour/ressources/modélisation/Doc final/BoulePétanque/boulepleineV2.FCStd

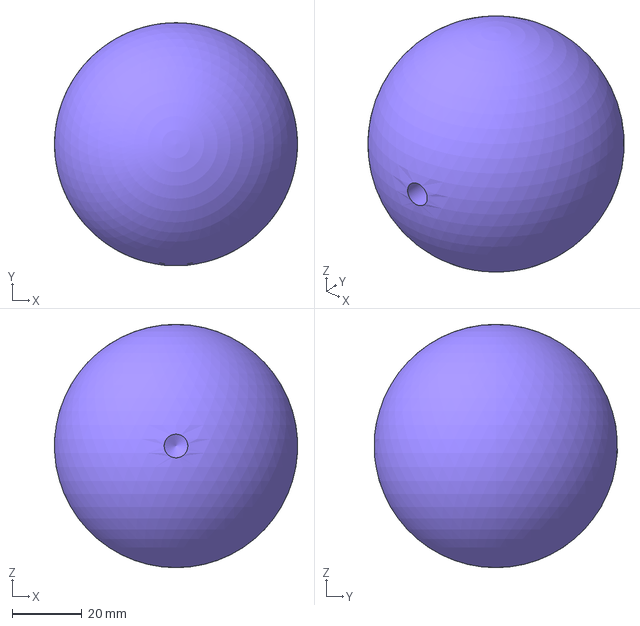
[picture p211: CAD file, 2026-07-06]
ressources/modélisation/Doc final/BoulePétanque/boulepleineV2.FCStd
69.9 x 69.8 x 70.0 mm
