guiraudjb/Arducible_Fanny_Petanque_World_Tour/ressources/modélisation/Doc final/ChassisV7/equaireplastron.FCStd

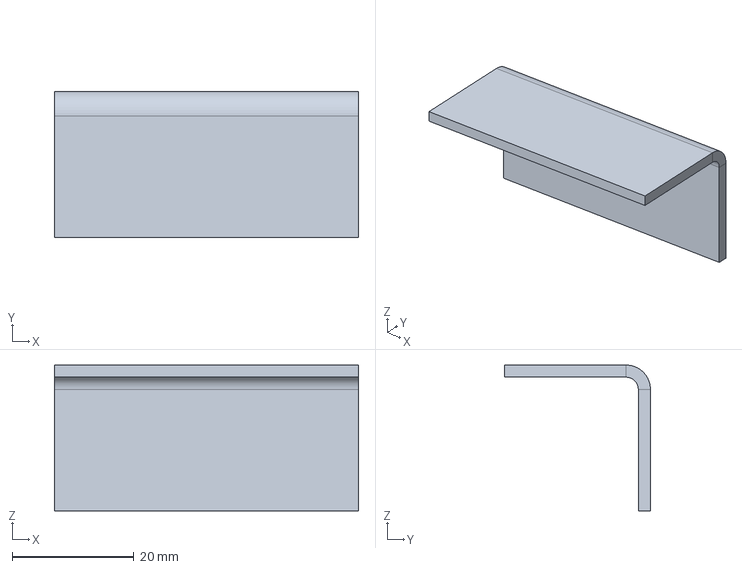
[picture p212: CAD file, 2026-07-06]
ressources/modélisation/Doc final/ChassisV7/equaireplastron.FCStd
50.0 x 24.0 x 24.0 mm
