guiraudjb/Arducible_Fanny_Petanque_World_Tour/ressources/modélisation/modelisation/parts/Chassis/chassisv4/parts/protectionpetg-Body002.stl

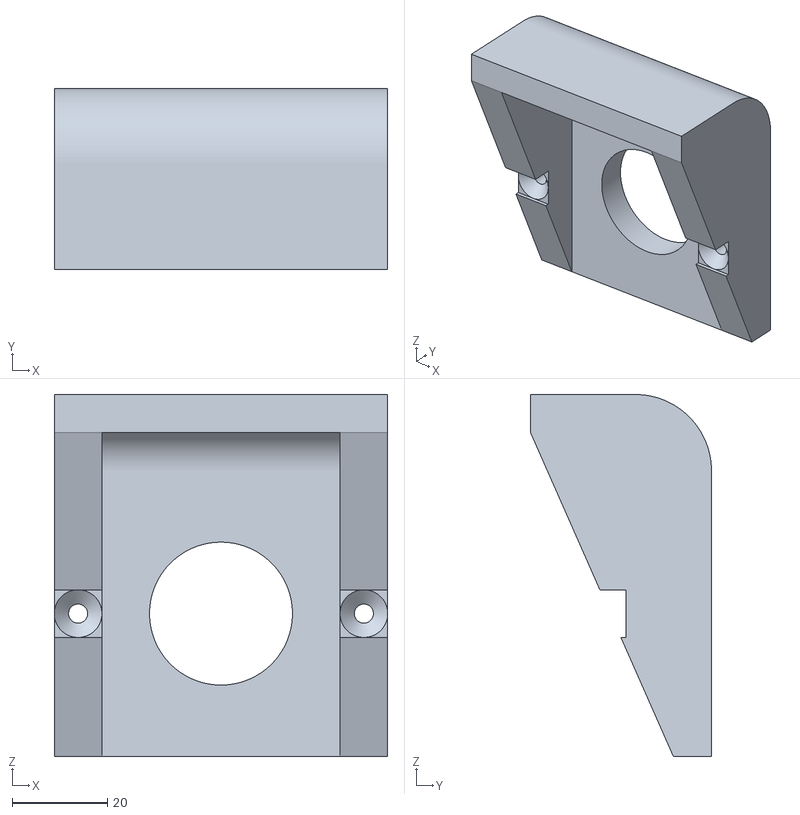
[picture p213: CAD file, 2026-07-06]
ressources/modélisation/modelisation/parts/Chassis/chassisv4/parts/protectionpetg-Body002.stl
70.0 x 38.0 x 76.0
