guiraudjb/Arducible_Fanny_Petanque_World_Tour/ressources/modélisation/modelisation/parts/Chassis/chassisv5/chassisv5_plateau-Corpsproto.step

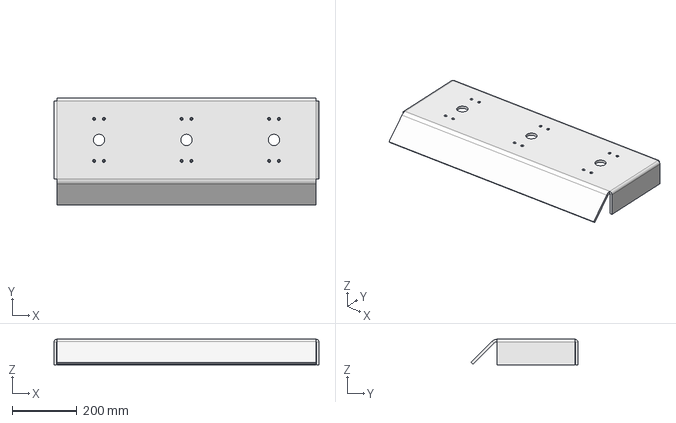
[picture p214: CAD file, 2026-07-06]
ressources/modélisation/modelisation/parts/Chassis/chassisv5/chassisv5_plateau-Corpsproto.step
818.0 x 329.6 x 79.0 mm
