guiraudjb/Arducible_Fanny_Petanque_World_Tour/ressources/modélisation/modelisation/parts/Chassis/ChassisV6/ChassisV7.FCStd

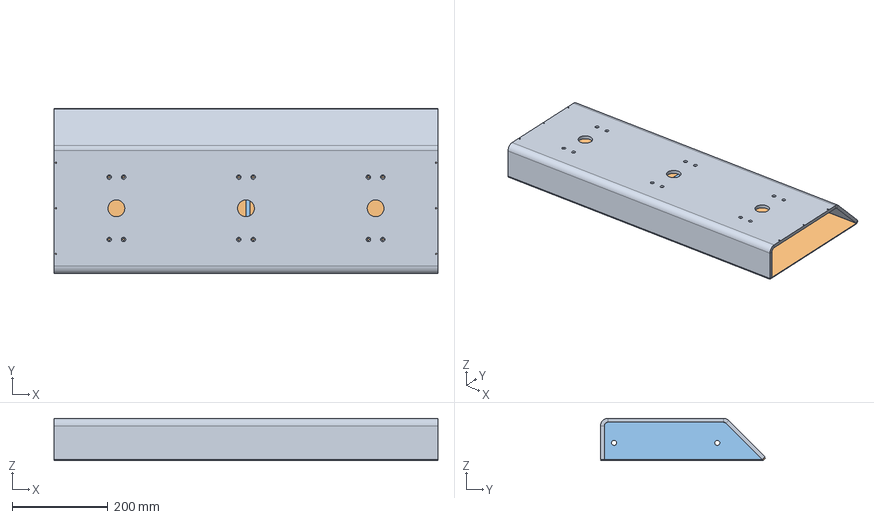
[picture p215: CAD file, 2026-07-06]
ressources/modélisation/modelisation/parts/Chassis/ChassisV6/ChassisV7.FCStd
800.0 x 344.1 x 88.4 mm
plateau
plastron
support
