guiraudjb/Arducible_Fanny_Petanque_World_Tour/ressources/modélisation/modelisation/parts/Controller/Boitier Controller/boitier/promicrousbcv1.FCStd

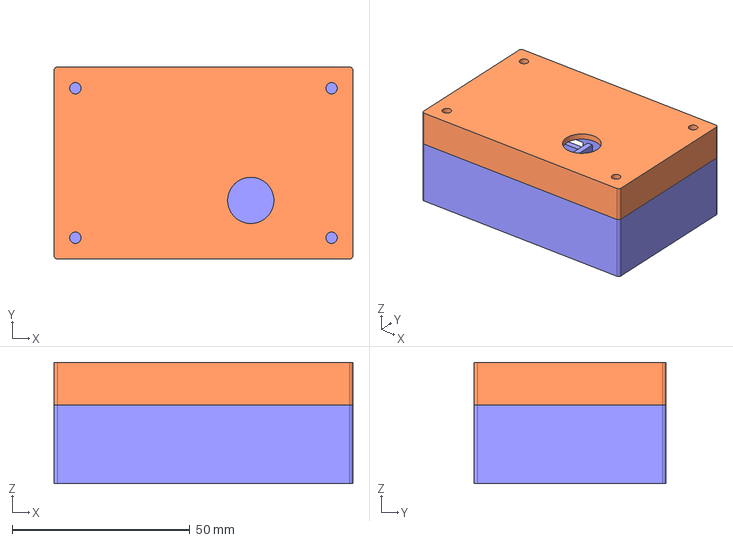
[picture p216: CAD file, 2026-07-06]
ressources/modélisation/modelisation/parts/Controller/Boitier Controller/boitier/promicrousbcv1.FCStd
84.0 x 54.0 x 34.0 mm
