guiraudjb/Arducible_Fanny_Petanque_World_Tour/hardware/enclosure/boitierJeu-supportws2812.stl

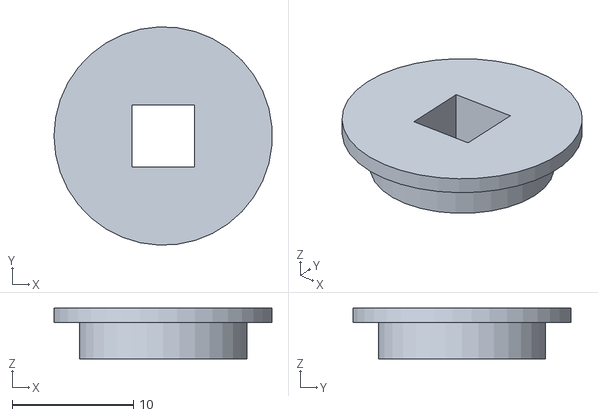
[picture p217: CAD file, 2026-07-06]
hardware/enclosure/boitierJeu-supportws2812.stl
18.0 x 18.0 x 4.20
