guiraudjb/Arducible_Fanny_Petanque_World_Tour/ressources/modélisation/Doc final/ChassisV7/supportv7.FCStd

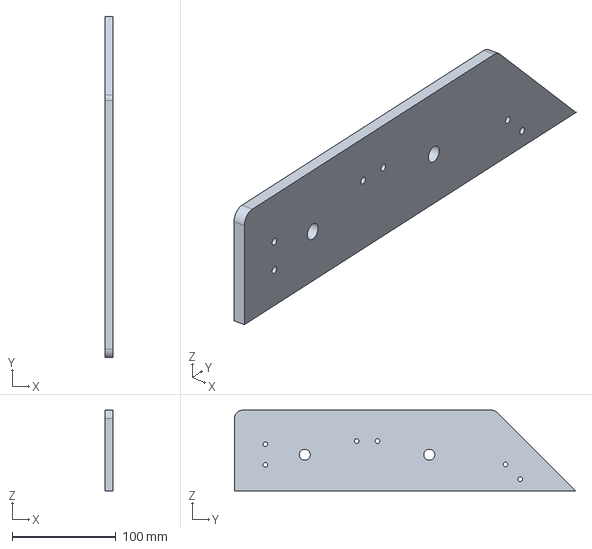
[picture p218: CAD file, 2026-07-06]
ressources/modélisation/Doc final/ChassisV7/supportv7.FCStd
8.00 x 328.7 x 77.8 mm
