guiraudjb/Arducible_Fanny_Petanque_World_Tour/ressources/modélisation/Doc final/vis/M1.6x5-Vis.FCStd

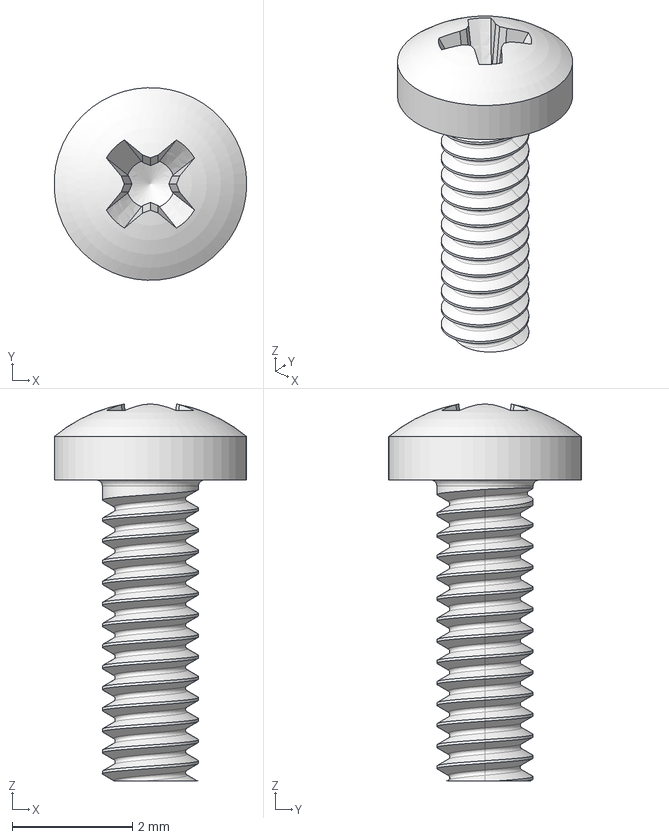
[picture p219: CAD file, 2026-07-06]
ressources/modélisation/Doc final/vis/M1.6x5-Vis.FCStd
3.20 x 3.20 x 6.26 mm
