guiraudjb/Arducible_Fanny_Petanque_World_Tour/ressources/modélisation/modelisation/parts/Chassis/chassisv5/supportchassisv5_plateau-Corps.step

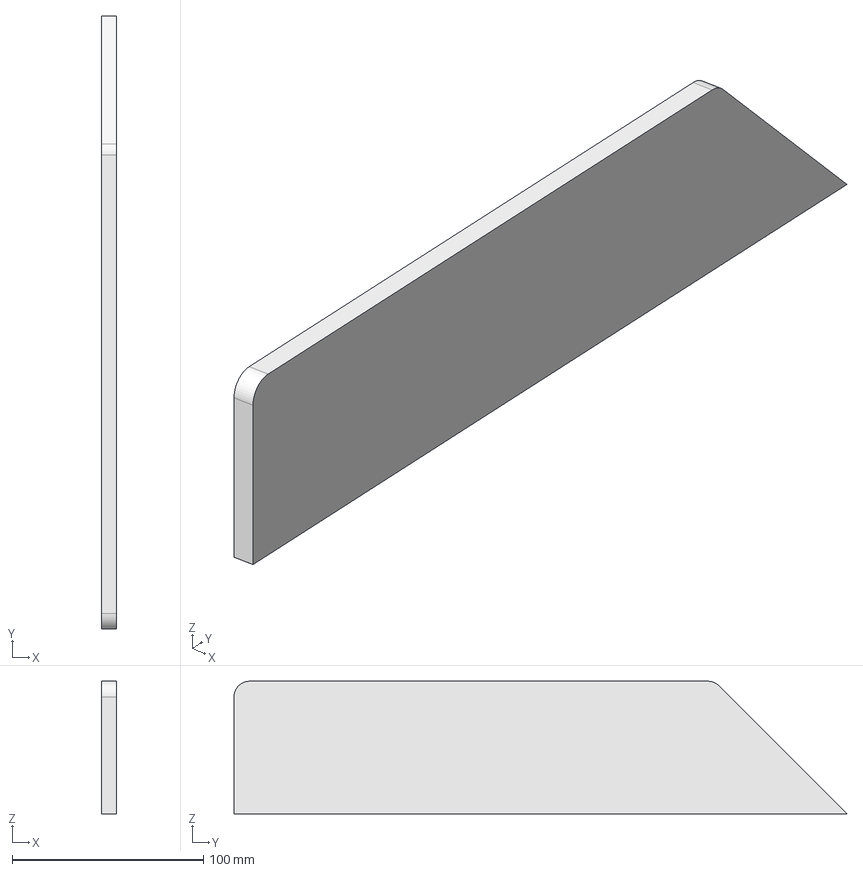
[picture p220: CAD file, 2026-07-06]
ressources/modélisation/modelisation/parts/Chassis/chassisv5/supportchassisv5_plateau-Corps.step
8.00 x 320.6 x 69.4 mm
