guiraudjb/Arducible_Fanny_Petanque_World_Tour/ressources/modélisation/modelisation/parts/Chassis/ChassisV6/ChassisV6-support.step

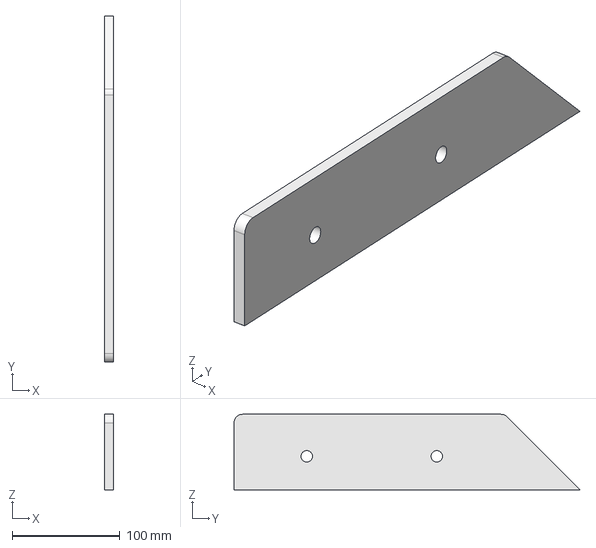
[picture p221: CAD file, 2026-07-06]
ressources/modélisation/modelisation/parts/Chassis/ChassisV6/ChassisV6-support.step
8.00 x 320.7 x 70.0 mm
