guiraudjb/Arducible_Fanny_Petanque_World_Tour/hardware/cad/rotule-ge8-articulee.FCStd

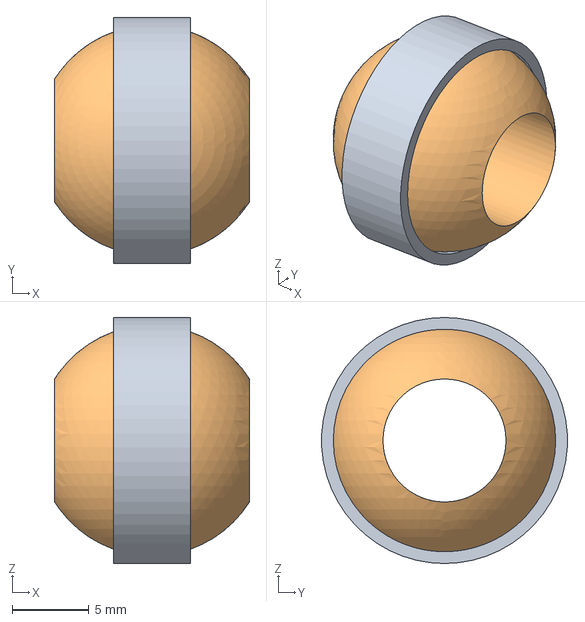
[picture p222: CAD file, 2026-07-20]
hardware/cad/rotule-ge8-articulee.FCStd
12.7 x 16.0 x 16.0 mm
Chape exterieure (fixe, vissee aux plaques)
Bille + axe (mobile, solidaire du M8)
