guiraudjb/Arducible_Fanny_Petanque_World_Tour/hardware/enclosure/boitierJeu-facade.stl

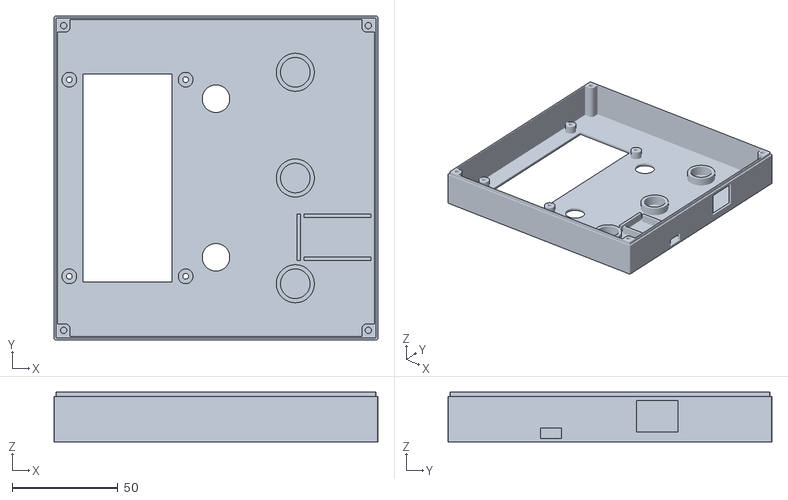
[picture p223: CAD file, 2026-07-06]
hardware/enclosure/boitierJeu-facade.stl
153.2 x 153.2 x 23.6
