guiraudjb/Arducible_Fanny_Petanque_World_Tour/ressources/modélisation/modelisation/parts/Chassis/chassisv4/parts/supportvChassisV5.FCStd

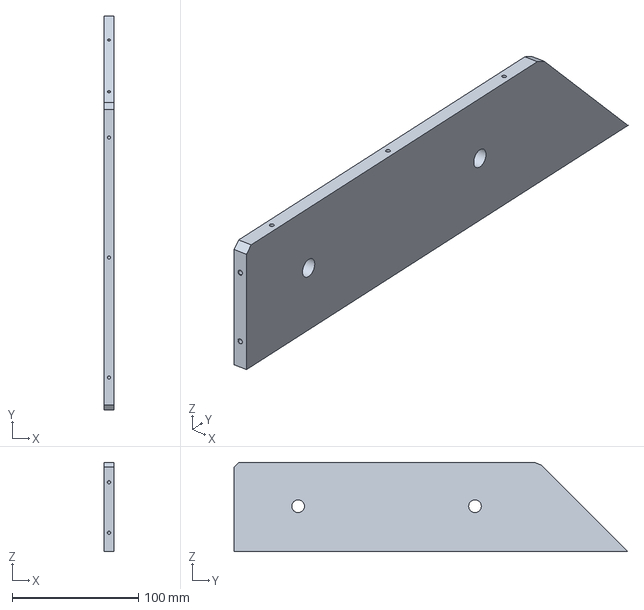
[picture p224: CAD file, 2026-07-06]
ressources/modélisation/modelisation/parts/Chassis/chassisv4/parts/supportvChassisV5.FCStd
8.00 x 311.9 x 70.8 mm
