guiraudjb/Arducible_Fanny_Petanque_World_Tour/ressources/modélisation/modelisation/parts/Chassis/chassisv5/chassisv5_plateau-Corps.step

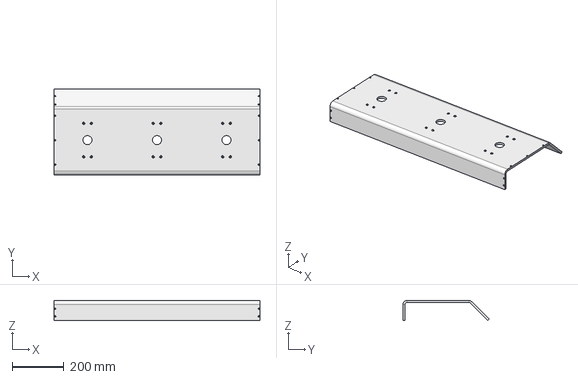
[picture p225: CAD file, 2026-07-06]
ressources/modélisation/modelisation/parts/Chassis/chassisv5/chassisv5_plateau-Corps.step
800.0 x 335.2 x 78.2 mm
