guiraudjb/Arducible_Fanny_Petanque_World_Tour/ressources/modélisation/modelisation/parts/Chassis/ChassisV6/ChassisV6-plateau.step

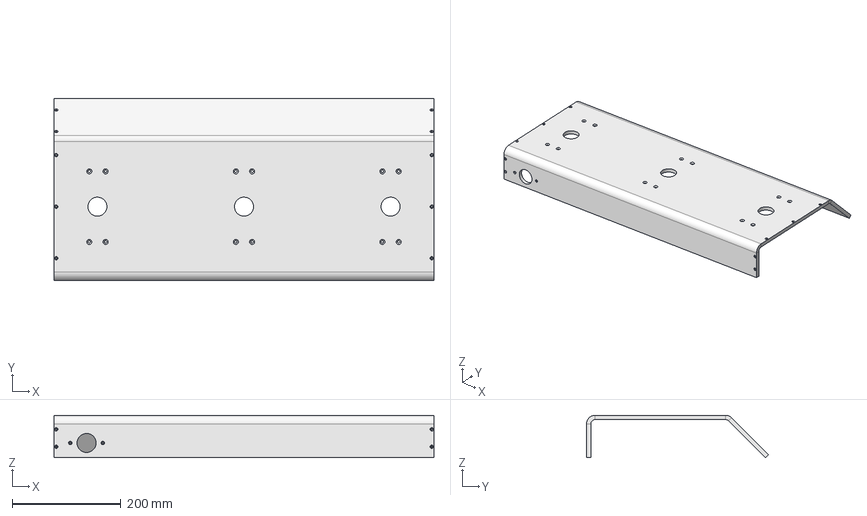
[picture p226: CAD file, 2026-07-06]
ressources/modélisation/modelisation/parts/Chassis/ChassisV6/ChassisV6-plateau.step
700.0 x 335.2 x 78.2 mm
