guiraudjb/Arducible_Fanny_Petanque_World_Tour/hardware/enclosure/boitierJeu-fermeture.stl

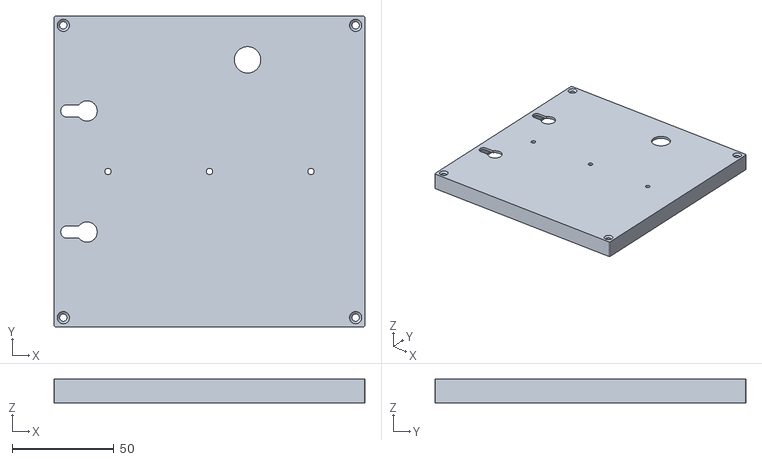
[picture p227: CAD file, 2026-07-06]
hardware/enclosure/boitierJeu-fermeture.stl
153.2 x 153.2 x 11.6
