guiraudjb/Arducible_Fanny_Petanque_World_Tour/ressources/modélisation/modelisation/parts/Chassis/ChassisV6/ChassisV6-plastron.step

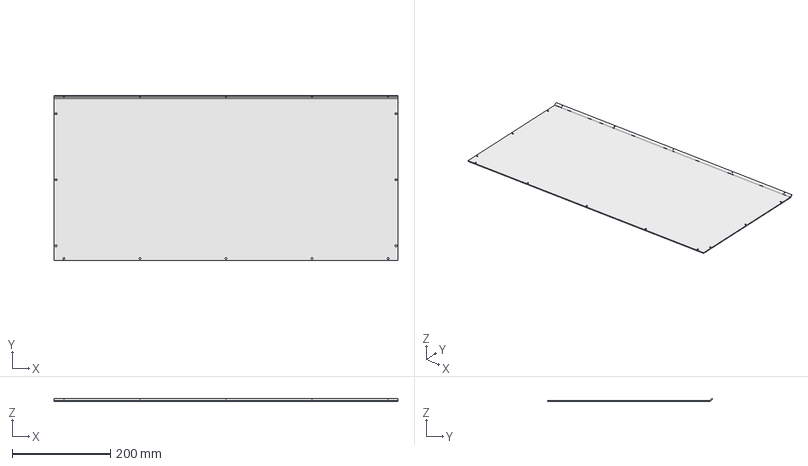
[picture p229: CAD file, 2026-07-06]
ressources/modélisation/modelisation/parts/Chassis/ChassisV6/ChassisV6-plastron.step
700.0 x 336.1 x 6.83 mm
