guiraudjb/Arducible_Fanny_Petanque_World_Tour/hardware/cad/detection-pcb-v3.FCStd

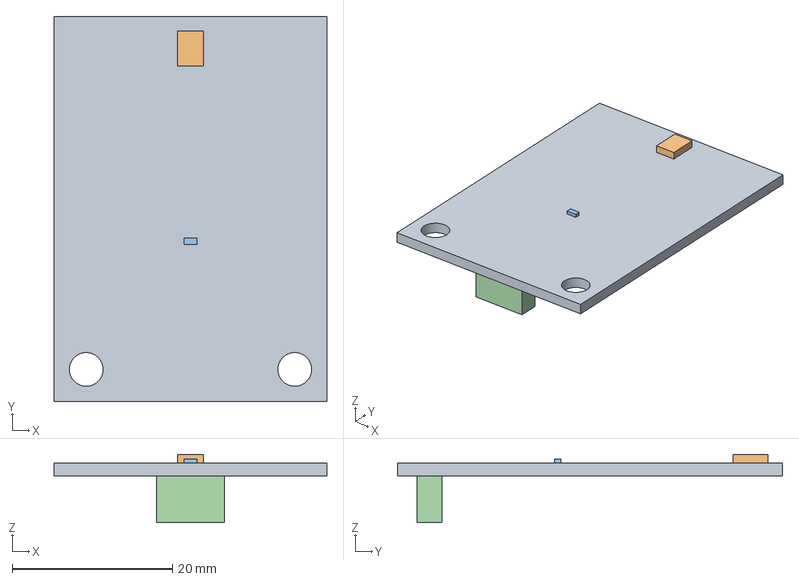
[picture p230: CAD file, 2026-07-19]
hardware/cad/detection-pcb-v3.FCStd
34.0 x 48.0 x 8.50 mm
SMD_v3_Arducible
OH37_hall_sensor
R1_10k
JST_XH_3pts
