guiraudjb/Arducible_Fanny_Petanque_World_Tour/hardware/enclosure/promicrousbcv1.FCStd

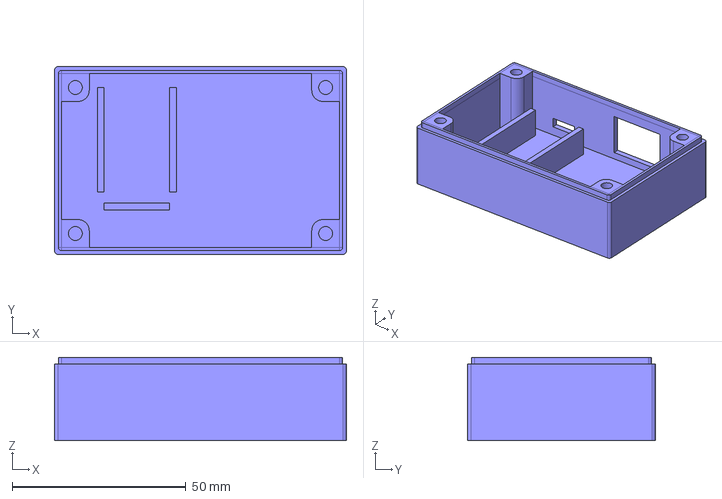
[picture p231: CAD file, 2026-07-06]
hardware/enclosure/promicrousbcv1.FCStd
84.0 x 54.0 x 24.0 mm
