guiraudjb/Arducible_Fanny_Petanque_World_Tour/ressources/modélisation/modelisation/parts/Chassis/chassisv4/parts/guidepercage.FCStd

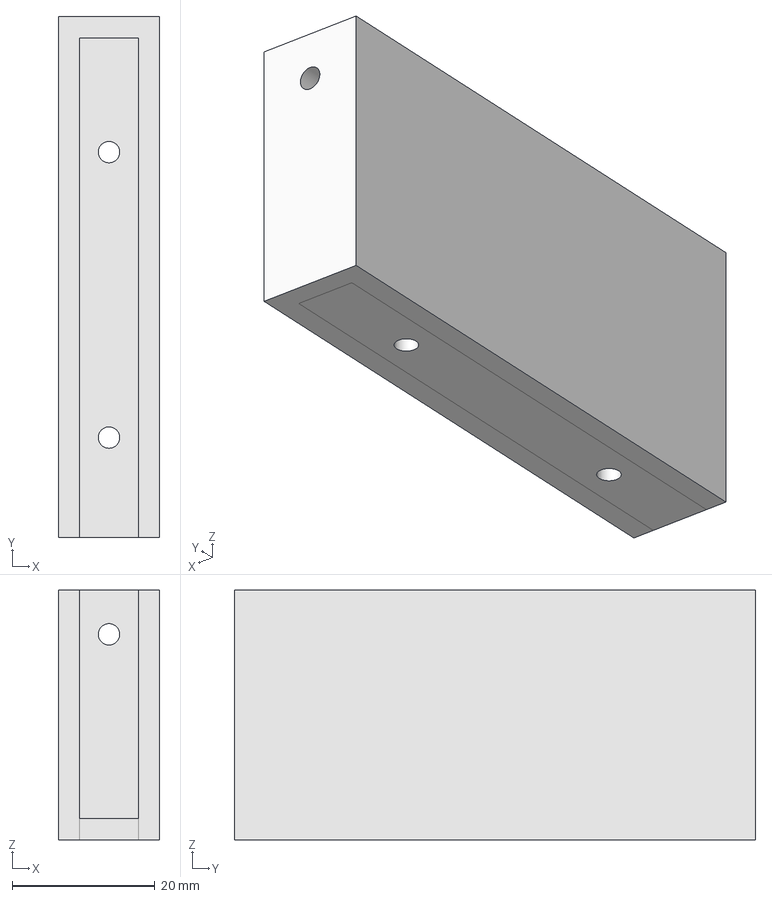
[picture p232: CAD file, 2026-07-06]
ressources/modélisation/modelisation/parts/Chassis/chassisv4/parts/guidepercage.FCStd
14.2 x 73.0 x 35.0 mm
