guiraudjb/Arducible_Fanny_Petanque_World_Tour/ressources/modélisation/Doc final/ChassisV7/equairev7.FCStd

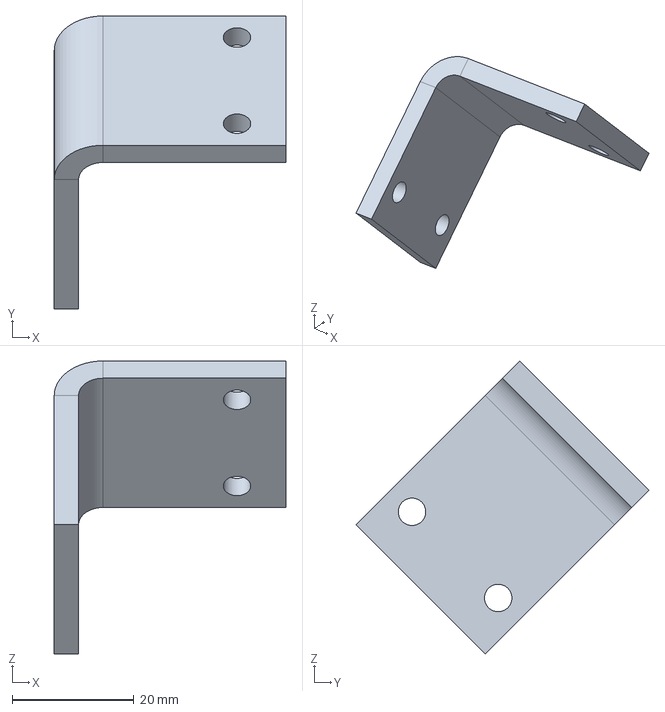
[picture p233: CAD file, 2026-07-06]
ressources/modélisation/Doc final/ChassisV7/equairev7.FCStd
38.0 x 48.1 x 48.1 mm
