guiraudjb/Arducible_Fanny_Petanque_World_Tour/ressources/modélisation/Doc final/ChassisV7/equairev7-equaire.step

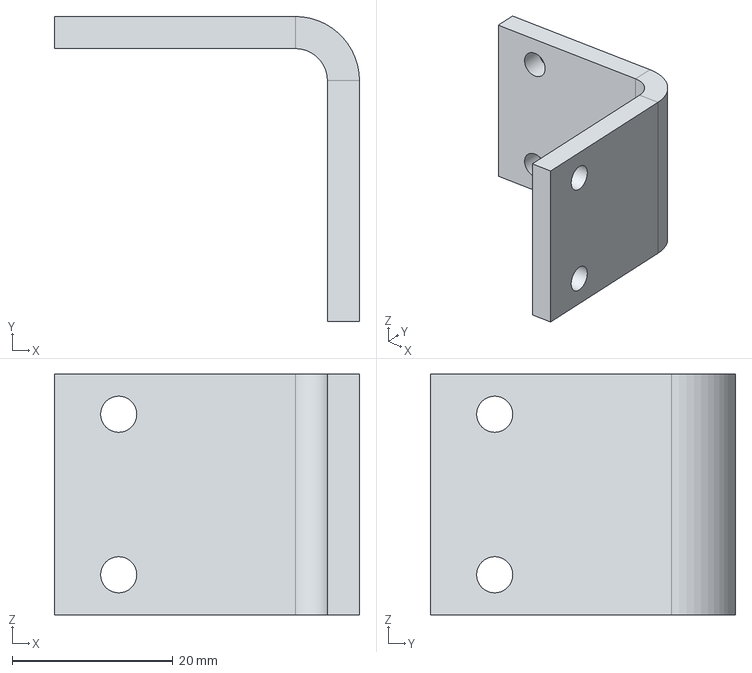
[picture p234: CAD file, 2026-07-06]
ressources/modélisation/Doc final/ChassisV7/equairev7-equaire.step
38.0 x 38.0 x 30.0 mm
