guiraudjb/Arducible_Fanny_Petanque_World_Tour/ressources/modélisation/Doc final/ChassisV7/plastronV7-plastron.step

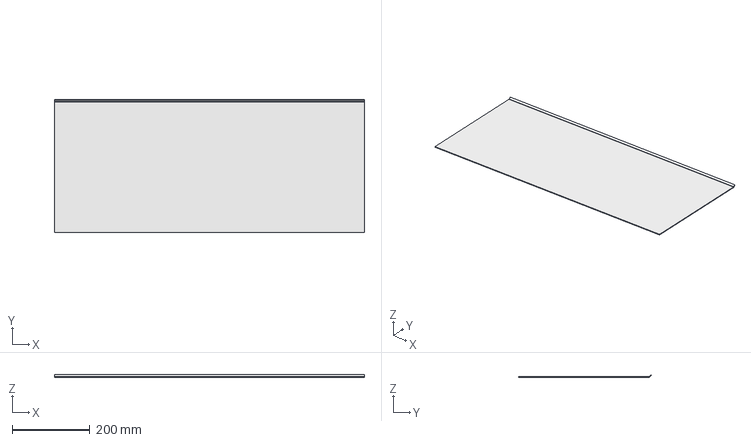
[picture p235: CAD file, 2026-07-06]
ressources/modélisation/Doc final/ChassisV7/plastronV7-plastron.step
800.0 x 344.1 x 6.83 mm
