guiraudjb/Arducible_Fanny_Petanque_World_Tour/hardware/cad/interface-noyau-rj45.FCStd

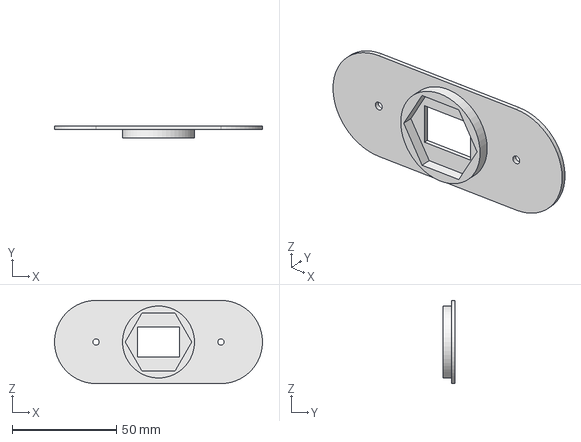
[picture p236: CAD file, 2026-07-06]
hardware/cad/interface-noyau-rj45.FCStd
100.0 x 5.60 x 40.0 mm
