guiraudjb/Arducible_Fanny_Petanque_World_Tour/hardware/cad/support-rj45.FCStd

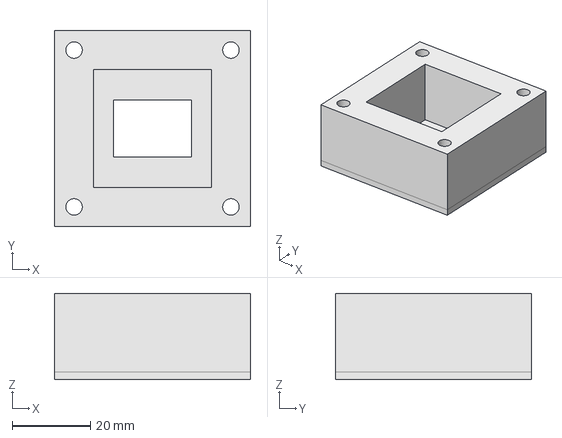
[picture p237: CAD file, 2026-07-06]
hardware/cad/support-rj45.FCStd
50.0 x 50.0 x 22.0 mm
