guiraudjb/Arducible_Fanny_Petanque_World_Tour/hardware/cad/rondelle-epaisse-din7349-m8.FCStd

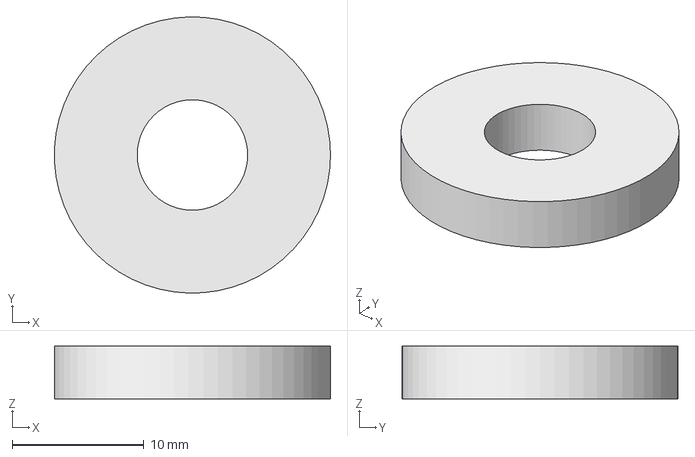
[picture p238: CAD file, 2026-07-06]
hardware/cad/rondelle-epaisse-din7349-m8.FCStd
21.0 x 21.0 x 4.00 mm
