guiraudjb/Arducible_Fanny_Petanque_World_Tour/hardware/renders/articulation/assemblage-articulation-dessous.png

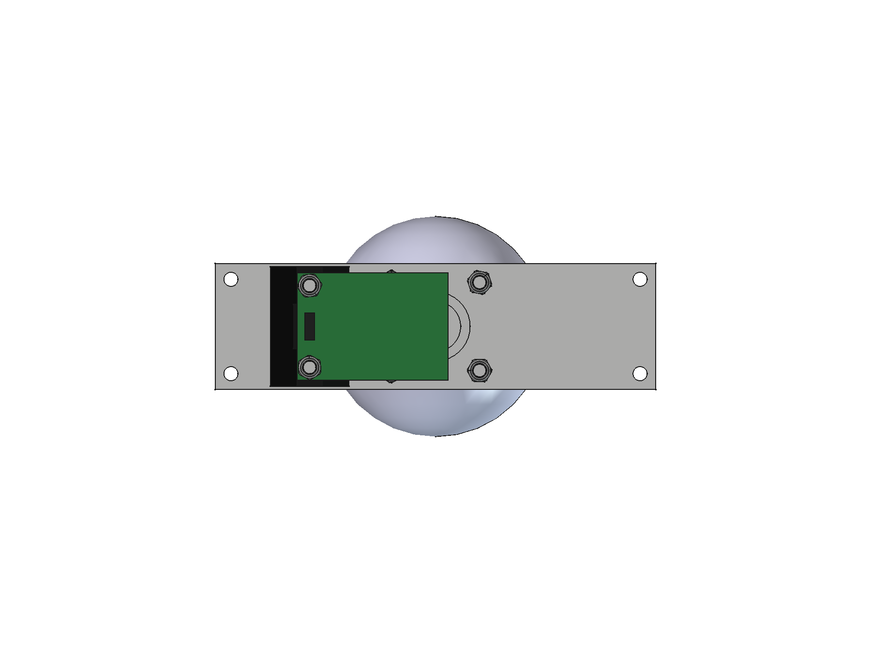
hardware/renders/articulation/assemblage-articulation-dessous.png
