guiraudjb/Arducible_Fanny_Petanque_World_Tour/hardware/renders/articulation/assemblage-articulation-droite.png

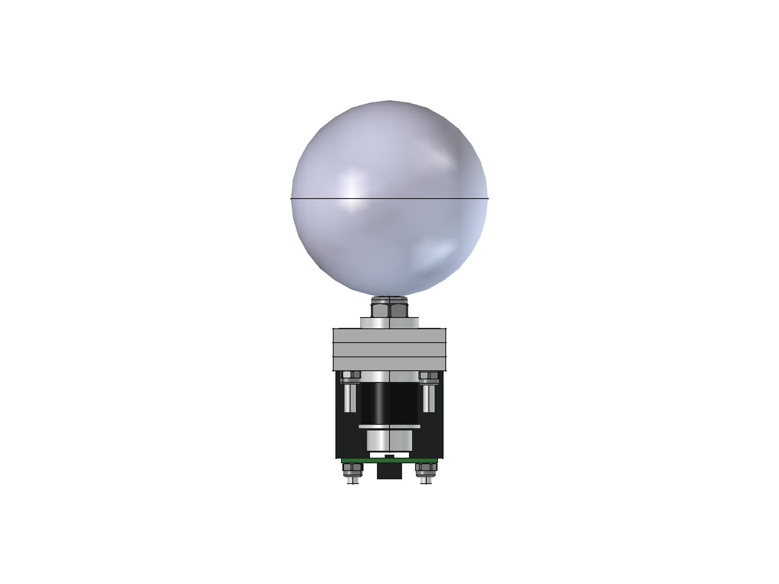
hardware/renders/articulation/assemblage-articulation-droite.png
