guiraudjb/Arducible_Fanny_Petanque_World_Tour/hardware/renders/articulation/assemblage-articulation-eclate-dessous-numerote.png

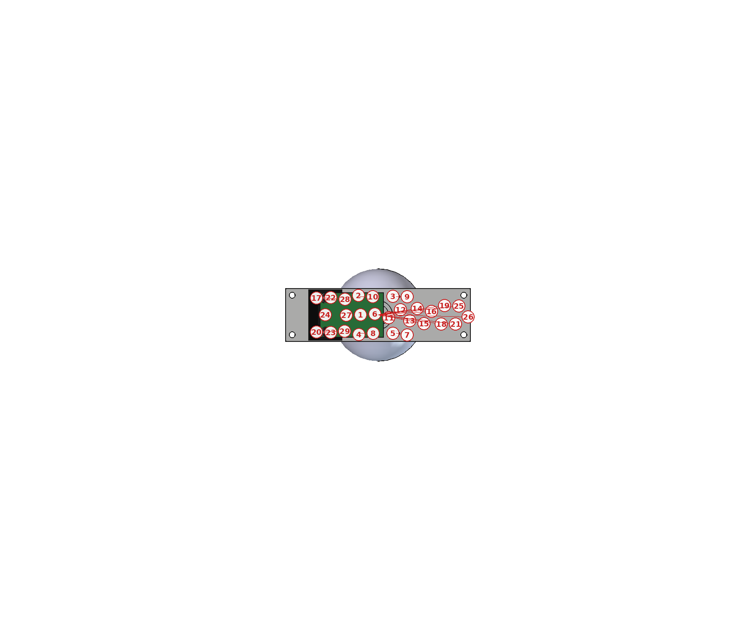
hardware/renders/articulation/assemblage-articulation-eclate-dessous-numerote.png
