guiraudjb/Arducible_Fanny_Petanque_World_Tour/hardware/renders/articulation/assemblage-articulation-face.png

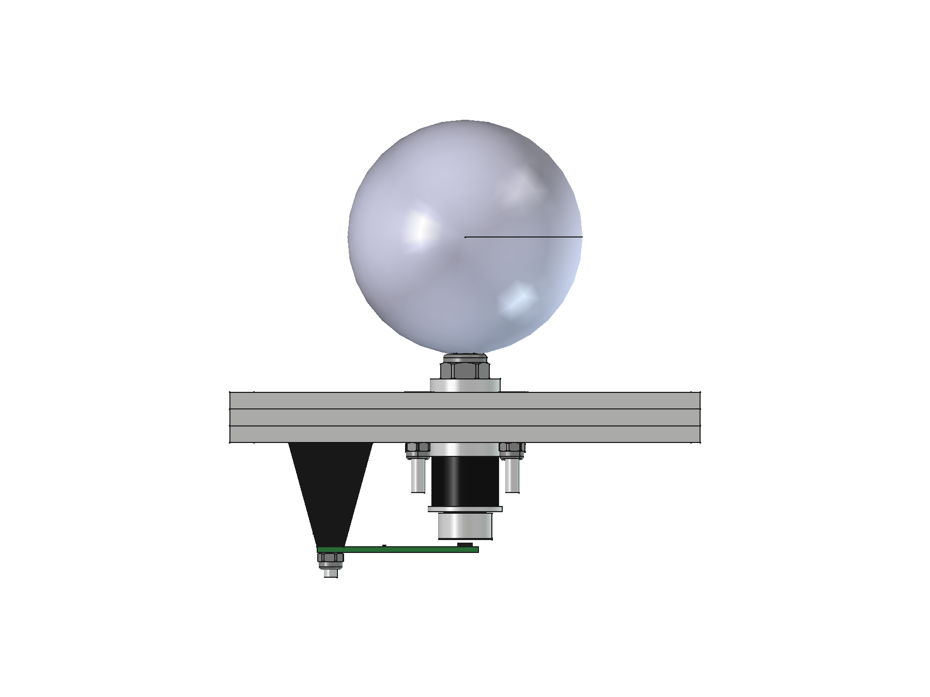
hardware/renders/articulation/assemblage-articulation-face.png
