guiraudjb/Arducible_Fanny_Petanque_World_Tour/hardware/renders/articulation/assemblage-articulation-mouvement.gif

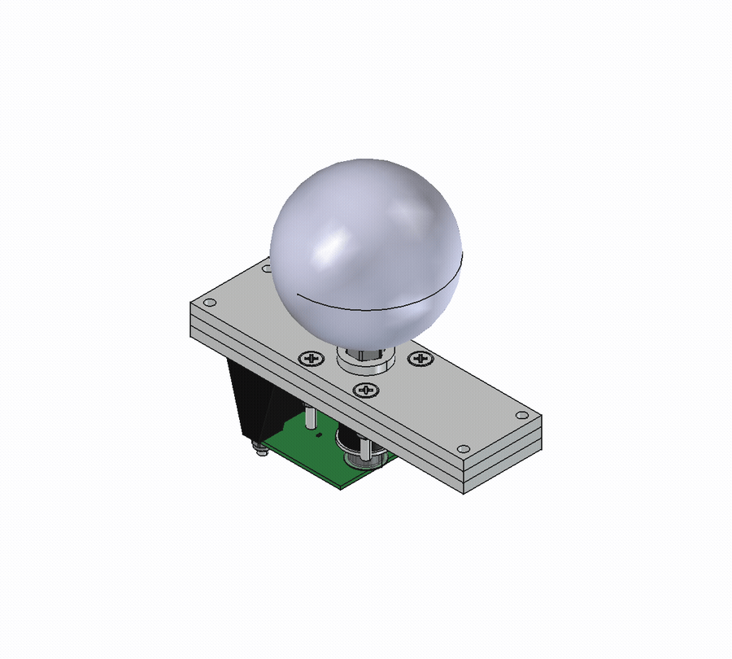
hardware/renders/articulation/assemblage-articulation-mouvement.gif
