guiraudjb/Arducible_Fanny_Petanque_World_Tour/hardware/renders/articulation/assemblage-articulation-sweep-front.gif

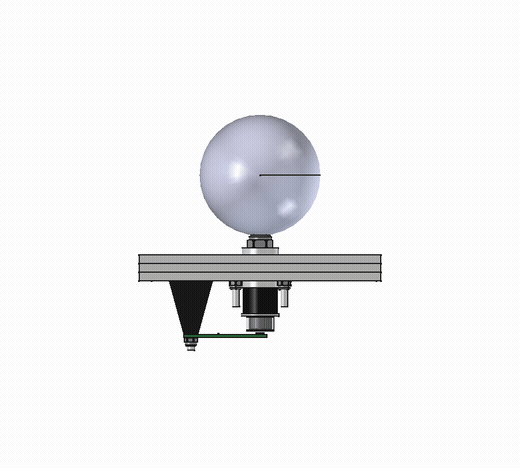
hardware/renders/articulation/assemblage-articulation-sweep-front.gif
