guiraudjb/Arducible_Fanny_Petanque_World_Tour/hardware/renders/articulation/assemblage-articulation-turntable.gif

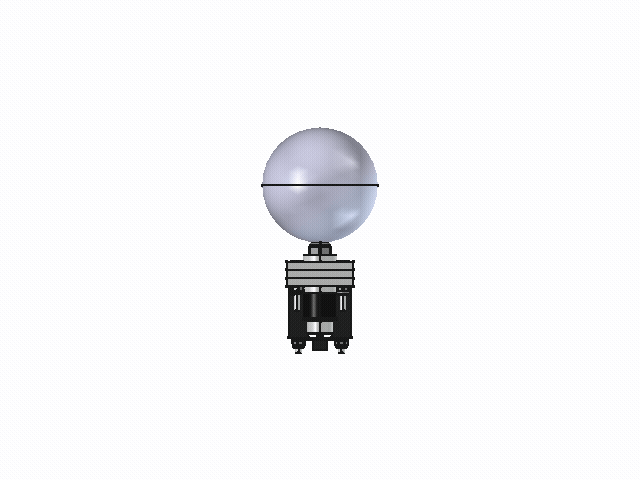
hardware/renders/articulation/assemblage-articulation-turntable.gif
