guiraudjb/Arducible_Fanny_Petanque_World_Tour/hardware/renders/chassis/chassis-assemblage-v7.png

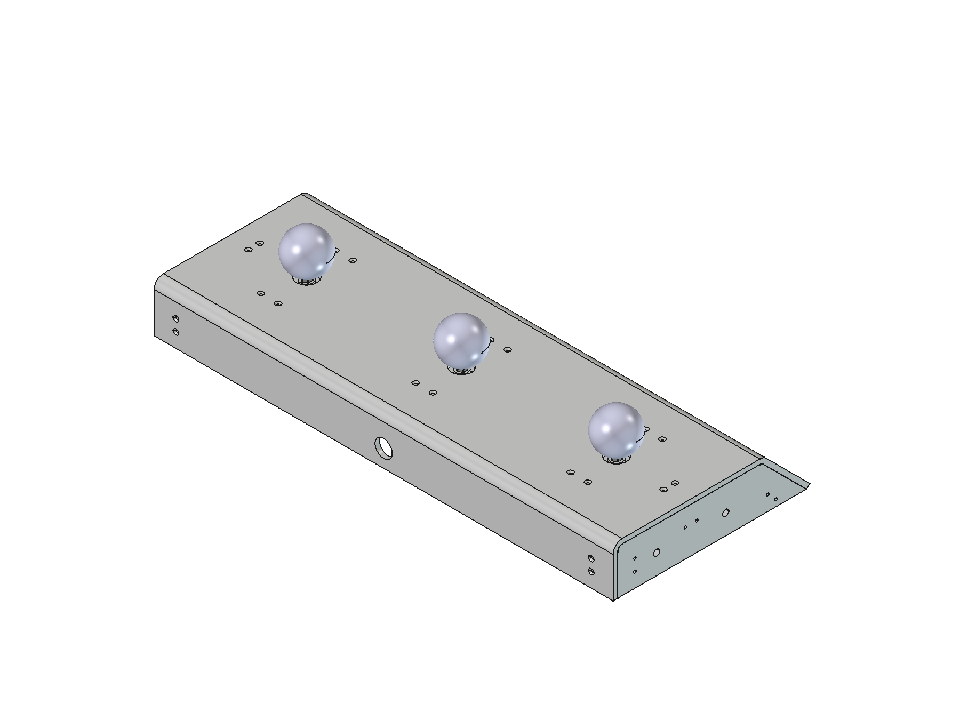
hardware/renders/chassis/chassis-assemblage-v7.png
