guiraudjb/Arducible_Fanny_Petanque_World_Tour/hardware/renders/enclosure/boitier-assemble.png

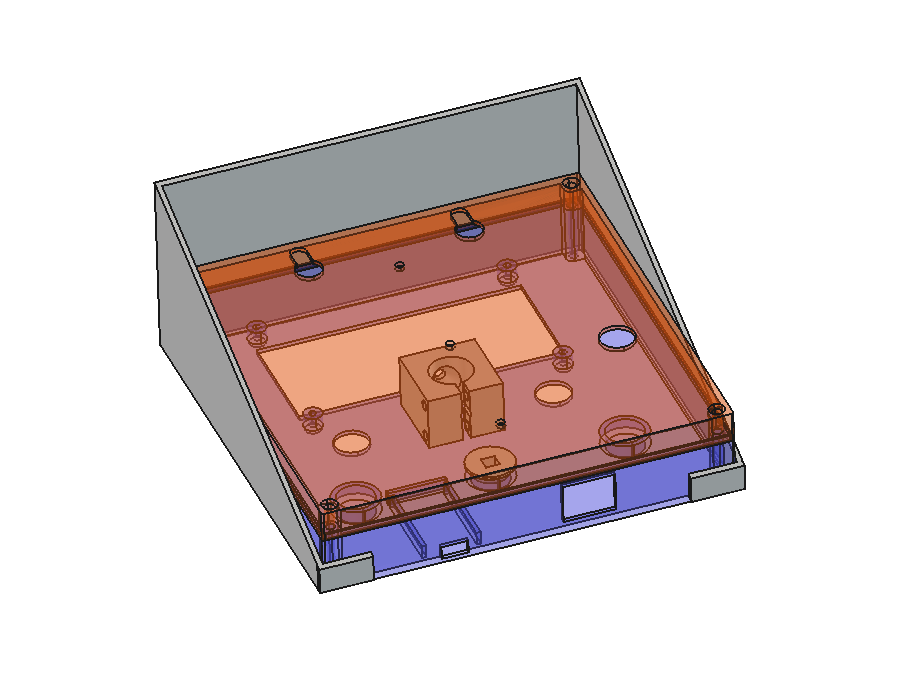
hardware/renders/enclosure/boitier-assemble.png
