guiraudjb/Arducible_Fanny_Petanque_World_Tour/hardware/schematics/arduino-leonardo-rj45-wiring.png

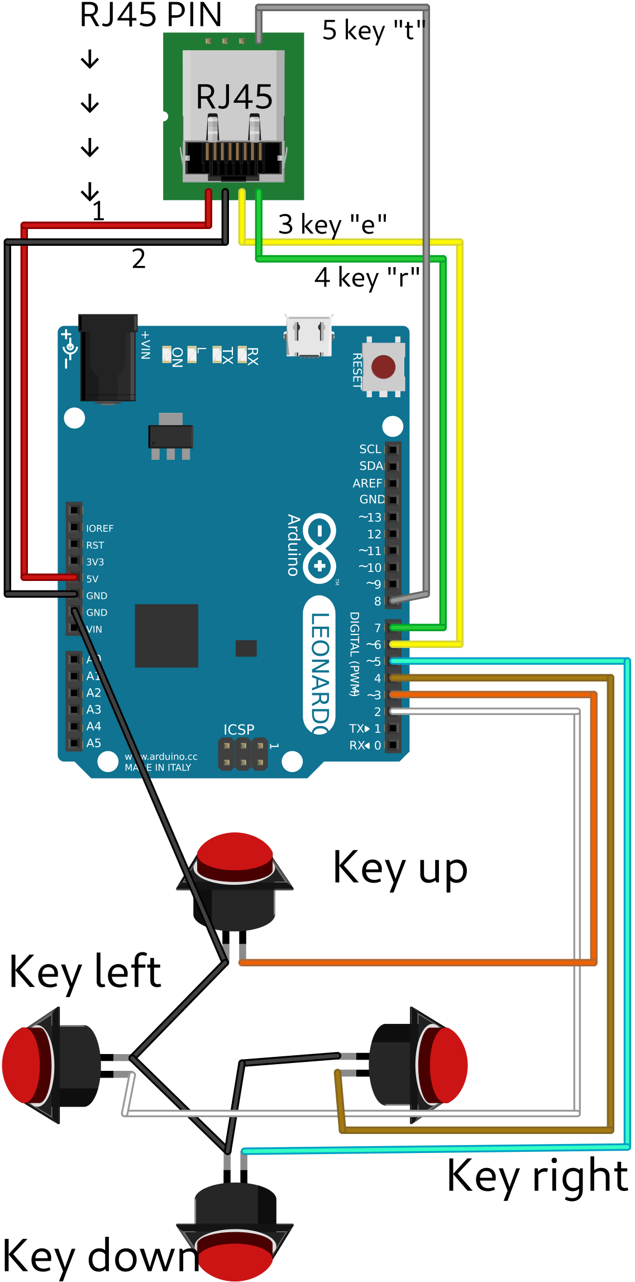
hardware/schematics/arduino-leonardo-rj45-wiring.png
