guiraudjb/Arducible_Fanny_Petanque_World_Tour/hardware/schematics/pro-micro-wiring.png

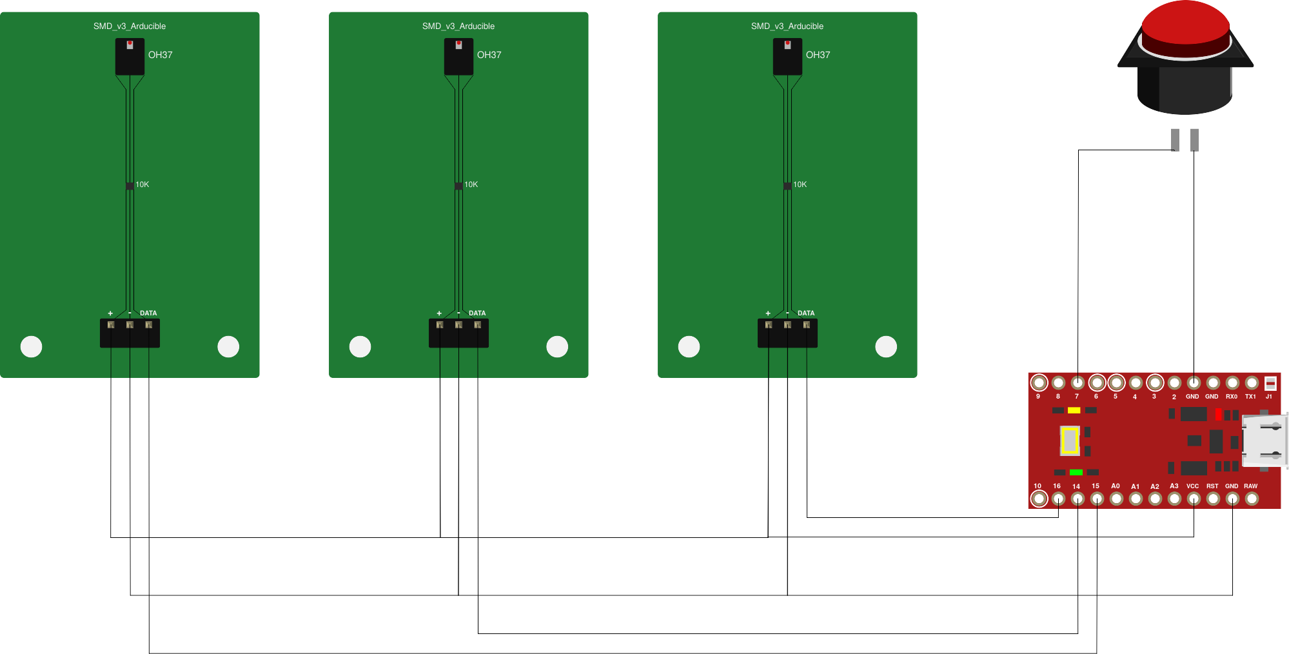
hardware/schematics/pro-micro-wiring.png
