guiraudjb/Arducible_Fanny_Petanque_World_Tour/videos/poster-assemblage-electronique.jpg

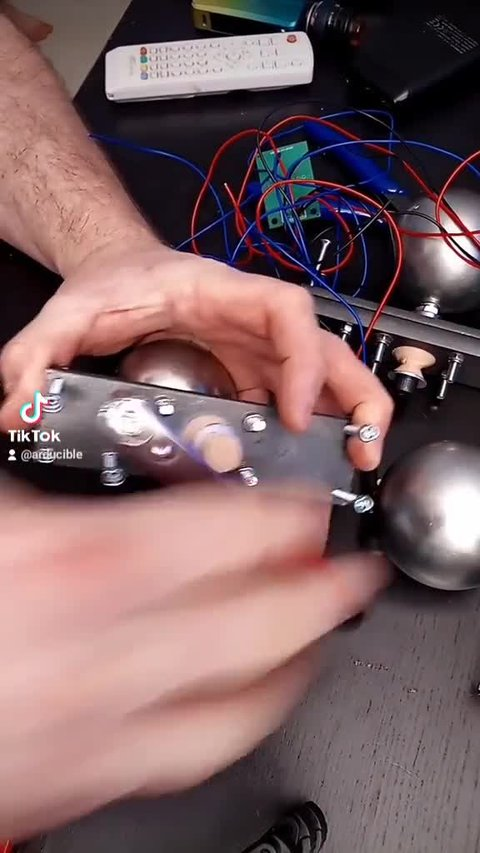
videos/poster-assemblage-electronique.jpg
