guiraudjb/Arducible_Fanny_Petanque_World_Tour/ressources/modélisation/modelisation/parts/Chassis/chassisv4/parts/DocumentFabricationChassisDecoupeLaserFraisageTaraudagePrototypeV1/plateau/plateau_fraisageM4.pdf

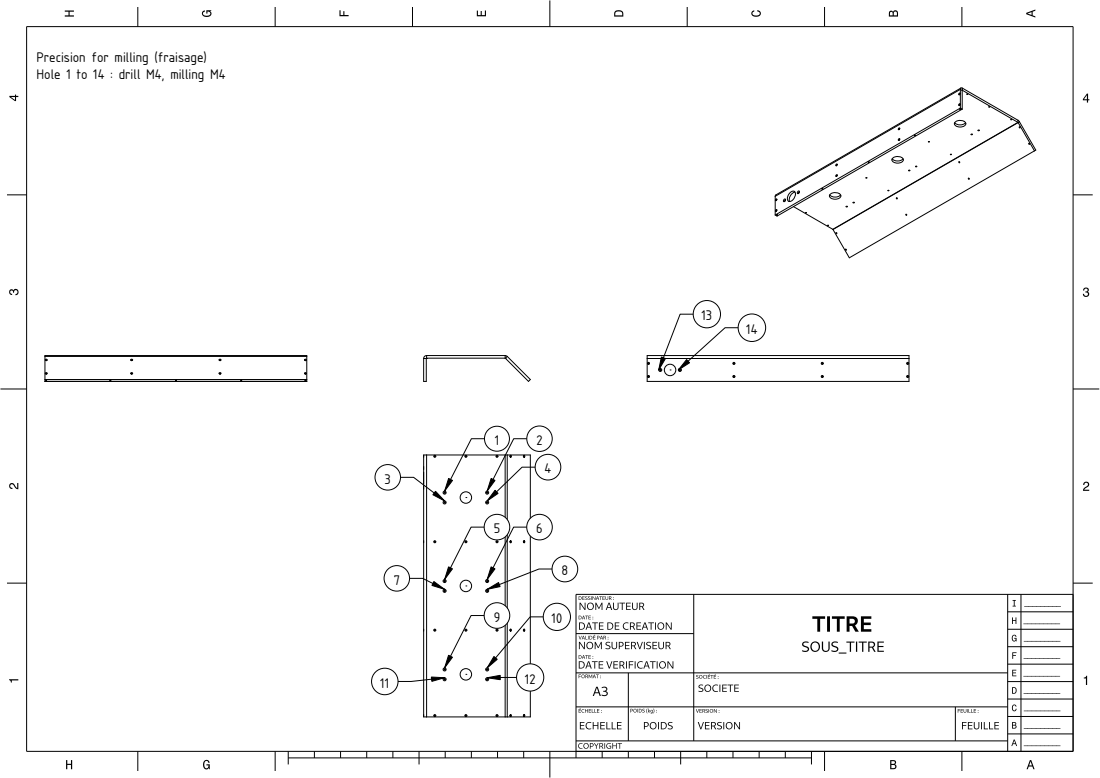
[picture p255: page 1]

Precision for milling (fraisage)
Hole 1 to 14 : drill M4, milling M4
