guiraudjb/Arducible_Fanny_Petanque_World_Tour/ressources/modélisation/modelisation/parts/Chassis/chassisv4/parts/DocumentFabricationChassisDecoupeLaserFraisageTaraudagePrototypeV1/plateau/plateau_taraudageM2.pdf

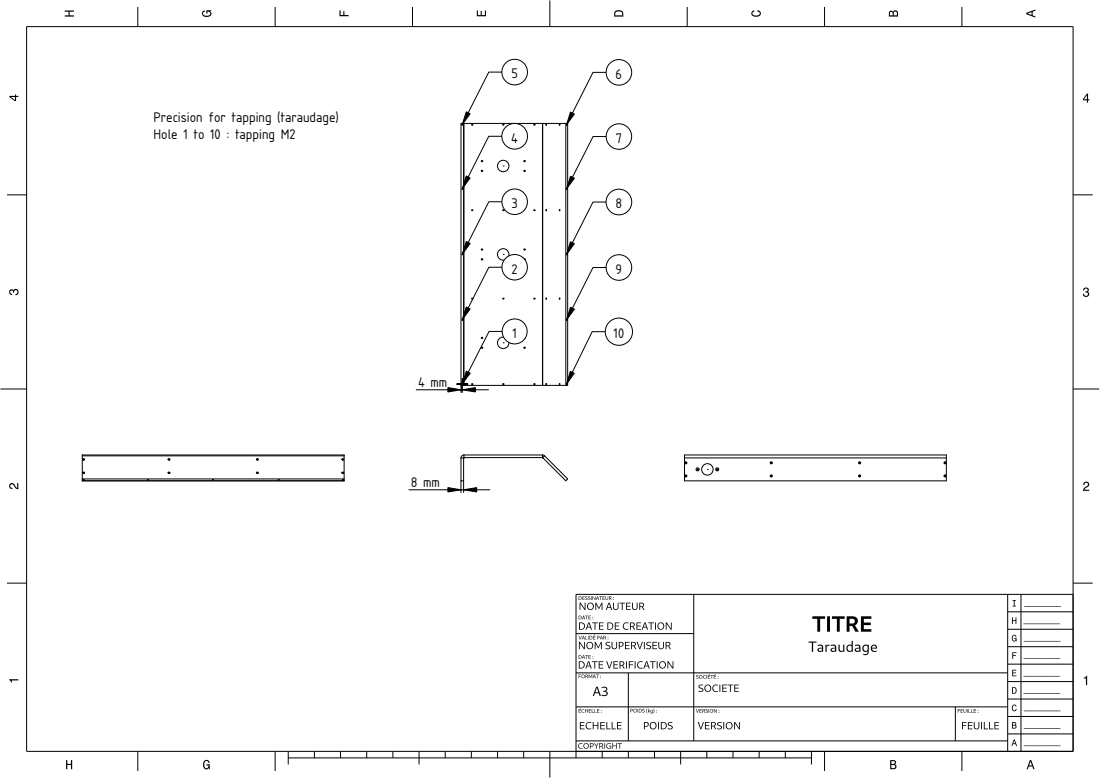
[picture p256: page 1]

Precision for tapping (taraudage)
Hole 1 to 10 : tapping M2
